Leif-Rydenfalk/halo/electronics/halo_replica/evidence/E07-CHECKS-THAT-CANNOT-FAIL.md

# E07 — the four ways a check passed today without being able to fail

*halo Replica lane, 2026-09-05. A running catalogue, because this lane produced four distinct
instances in one session and they do not look alike from the outside. Three were found by
lanes beneath me; one was mine, and I had already written the rule against it.*

Every entry is a real, dated defect in this project's own work, with the fix that caught it.

---

## 1 · A check that agrees with what it checks — the fitted-residual test

`bin/boardmetro circle` judged whether a feature was circular by the **residual of the fitted
inliers**. Its selftest fed it a **SQUARE**, which passed at **residual sd 1.15 px** under a
2.0 px threshold — because IRLS *chooses* the inliers that make the residual small.

**Fix:** judge shape on evidence the fit cannot manufacture. **Inlier fraction** separates
cleanly: square **0.055**, ring **1.000**.

**Also:** the first fix was itself wrong. It gated on angular uniformity and rejected the real
O'Flynn marker circle, which is *legitimately* clipped by the crop. **Angular completeness is
not circularity.** Selftest case 9 is now a clipped circle that must still be accepted.

## 2 · A negative control that cannot lose — L1's rim-pad permutation controls

Two in one hour, both in `m_rim_*`:
- The control permuted the **smoothed** signal, giving a jagged control where the real signal
  is smooth. The peak-finder invented ~22 peaks from it and **nothing could ever have beaten
  it.** Fix: permute raw, then smooth identically.
- The control permuted angular **columns**. For a "reaches the edge" criterion every permuted
  column is a full-height stripe, so **the control manufactured the property under test** and
  returned 46.8 against a real 26. Fix: roll each radius row independently — same pixels, same
  per-row runs, only the radial alignment destroyed.

The verdict did not change. **The reasoning behind it was worthless.** A right answer reached
through a control that cannot fail is not a measurement.

## 3 · Methods that cannot disagree — my own, E04, and I had written the rule against it

I concluded from "four independent methods" that the board was ~25 mm and not 26. Every method
applied a **scalar px/mm to an anisotropic projection**, so none could disagree about the thing
I used their agreement to establish. L5's 24.997 mm matched L1's *vertical* extent to **0.02 %**
and sat 5.08 % off horizontal. One systematic reproduced four times. **Retracted in E05.**

I had written the rule after the coil retraction four hours earlier, applied it in E04 **in
writing**, and still got it wrong: I checked whether the scale *sources* were independent and
never asked whether the *projection assumption* was shared.

## 4 · A positive control that is too easy — L1's synthetic rim, and the subtlest of the four

The blob detector **failed** its positive control outright: six synthetic pads at photo 6's
exact scale, **one found**. That withdrew M03's counts. But the replacement's positive control
was still not representative — **the synthetic was 19× cleaner than the photograph**
(differential robust sd 1.8 luma against 34.6 and 37.3). A pad at the synthetic's full 111-luma
contrast sits at **3.2 σ** in photo 6, under a 4 σ gate, and *no larger than the 4.0 σ the real
rim already throws from nothing.*

**Fix:** a noise-matched case where the same detector finds **zero** of six pads that are
certainly there.

**Why this one is the subtlest, in L1's words: passing feels like evidence.** A negative control
that cannot lose leaves you uneasy. A positive control that sails through leaves you confident.

**It also upgraded the verdict**: from *"we could not see them"* to *"at this signal-to-noise
they could not have been seen"* — which CLOSES the rim question instead of leaving it hanging.

---

## 5 · The near-miss family: a bad input dressed as a better one

Not a check, but it would have defeated all of the above. Re-rendering the FCC exhibit at
600 dpi would have resampled a 27 px rim band to 110 px, producing **more** candidates with
**higher** confidence from **no new evidence** — and nothing in that output would have looked
wrong. Caught by measuring the prior first (`E06`): no competitor FCC exhibit embeds above
2048 × 1536, ours is already 2134 × 1600. L1 then closed it independently by power-spectrum
rolloff — the board region's real detail **dies below half Nyquist**, so destroying everything
above half Nyquist costs nothing.

## 6 · And the inverse: a tool that refused when it had actually measured

L1's resolution probe demanded `as_held > /2 > /4` and, when /2 came out *equal*, reported
"cannot separate the controls". **Wrong.** If real detail already dies below half Nyquist then
destroying everything above it MUST cost nothing — **/2 failing to separate IS the answer.** A
monotonic-ordering assumption had been smuggled into the verdict logic rather than the physics.

**This is rarer and harder to notice than the reverse, because the output is the safe-looking
one and nobody audits a refusal.**

---

## The rule, in its current form

Started as: *when you claim two measurements corroborate, name what each would have had to
SEE to disagree; if you cannot name it, they are one measurement.*

Sharpened after E04: *check independence against the assumption every method has in common,
not only against the inputs they do not share — a shared assumption is harder to see than a
shared input because nobody writes it down.*

**L1's form is better and is the one this lane now uses:** *check the assumption the method
shares with **its own control**, not only the inputs they do not share.* It covers the
method-and-control case, which is the one that actually bit both of us today.

## 7 · A check whose failure mode returns the BEST possible score — noise is broadband

The worst of the set, and the one nearest to being published as a headline.

L1's resolution probe, pointed at a box on `oflynn-backside-fullres` that sat mostly **off the
board**, returned **0.992 of Nyquist** — "SHARP, essentially to the file's own limit". It was
drafted as the good news. On-board regions of the *same file* measure **0.195–0.258**.

**Sensor and JPEG noise reaches Nyquist by definition and resolves nothing.** So a resolution
probe aimed at empty background does not merely fail — **it returns the best possible score.**
This is worse than a check that cannot fail: it is a check whose failure mode is
*indistinguishable from the ideal result*. The only thing separating them was the region's
luma sd — **36** for the background box against **64–66** on board.

**Fix:** every row now names its region and carries that region's luma sd. What caught it was
drawing the sample box back onto the photograph and **looking** — the same move that caught the
half-max contact-shadow artifact, whose faked ellipse pointed a *different* direction in each
photograph, which no real board shape can do.

## 8 · A correct measurement with a wrong verdict printed over it

Distinct from all of the above: the number was right and the sentence above it was not. Two
instances in one tool:

- `k_first`, "the first ladder step that costs detail", is ≥2 even for a perfectly sharp
  image — so the tool printed **"ALREADY SOFT / UPSAMPLED" over a 0.992 measurement.**
- The verdict demanded `as_held > /2 > /4` and, when /2 came out *equal*, reported "cannot
  separate the controls" — when **/2 failing to separate WAS the answer.** A monotonic-ordering
  assumption had been smuggled into the verdict logic rather than the physics.

**L1's line, kept verbatim: nobody audits a refusal, and nobody audits a confident label
either.**

---

## The resolution table, because it is the fact these lessons produced

Genuine pixels across the board — rolloff × board span — not pixels per file:

| source | side shown | board span | rolloff | genuine px | genuine px/mm |
|---|---|---|---|---|---|
| `oflynn-frontside-fullres` (right) | BACK | 1924 px | 0.570 | 1097 | ~42 |
| `oflynn-frontside-fullres` (upper-left) | BACK | 1924 px | 0.445 | 856 | ~33 |
| `oflynn-backside-fullres` (left annulus) | **FRONT** | 2672 px | 0.258 | 689 | ~27 |
| `oflynn-backside-fullres` (top-right) | **FRONT** | 2672 px | 0.195 | 521 | ~20 |
| `oflynn-frontside-26mm-cropped` (M01 datum) | BACK | 787 px | 0.398 | 313 | ~12 |
| FCC photo 6, board | FRONT | 412 px | 0.289 | 119 | ~4.6 |
| FCC photo 6, **steel rule** (within-image control) | — | — | **0.383** | — | — |

**Three consequences, and the third is the one people will get wrong:**

1. **More pixels is not more information.** The 2916 × 3412 file is *softer per pixel* than the
   2347 × 2344 one and only wins because the board fills more of the frame.
2. **The steel rule is sharper than the board in the same frame** (0.383 vs 0.289). That single
   within-image number explains why the px/mm datum is solid and the rim count never was.
3. **"Prefer the sharper image" does not apply to component work, because there is no choice.**
   The components are on the FRONT, and the FRONT is imaged only by the *softer* source. The
   sharper photograph shows the side with the battery contacts and the coil — **the better
   picture is of the emptier face.** Component metrology is stuck at 20–27 genuine px/mm.
   At that scale an 0402 is 20–27 px long and workable; an **0201 is 12–16 px long and 6–8 px
   wide, and a 6-pixel width cannot support package-size discrimination.** The AirTag uses
   0201s. That boundary belongs in the BOM as a number, not discovered per line.

## 9 · A control that can NEVER PASS — the same defect wearing the opposite sign

L1's centre-hole negative control required **zero detected objects inside the hole**. But the
hole is **bright background seen through the board**, so an unbounded intensity detector must
always return exactly one object there. It reported **1 at every threshold**. The requirement
was not a test of anything.

**Fix:** a **physical** upper size bound — 60 mm², against a largest real part (the UWB can) of
~35 mm². **Not** by lowering the requirement.

A control that can never pass is as useless as one that can never fail, and it is more likely
to survive review because it looks strict.

## 10 · A validation blind to the very quantity it appears to certify — and the cleanest demo of all

`c_register.validate` reported a worst held-out fold of **0.1029 mm**, which reads like a
statement of accuracy. Its scale basis was `photo6_bottom = 15.8875 px/mm` — the bottom rule's
value **at the rule, near the frame edge**. M02 measures **15.6850 px/mm at the board**, by two
routes agreeing to 0.23 %. **The basis was 1.29 % high**, and every millimetre downstream moved
with it (transferred source scale 107.686 → **106.313 px/mm**).

**The held-out error cannot see this, and L1 demonstrated it rather than arguing it.** Re-running
`validate` with the corrected scale gives **0.1029 mm in both runs, identical to four decimals** —
because validate converts the fitted *and* the held-out landmarks with the same px/mm, so a wrong
scale divides both sides equally and cancels exactly.

**0.1029 mm is a statement about REGISTRATION CONSISTENCY and carries no information about SCALE
ACCURACY.** A 1.29 % scale error and a 0.1029 mm held-out error coexist happily, and the second
never warns you about the first.

This is family 3 (methods that cannot disagree) in its purest form: **two runs differing in
exactly one number, and the check does not move.** It is the strongest single demonstration this
project has produced that a passing validation is not automatically evidence about the thing you
hoped it was evidence about.

**Fixed by extension, not forking:** `--target-px-per-mm` with a named `--target-px-per-mm-basis`,
and when the default is used the tool now *prints* that it is the rule's value and names the
board-located alternative. Default behaviour unchanged. That shape — make the assumption visible
rather than silently changing it — is the one to copy.

---

## Where this leaves the component work

**95 bright features located on the project FRONT; only 32 with a short side over 10 genuine
pixels.** Median detection area **0.178 mm²** — 0201 nominal (0.6 × 0.3 mm) **to 1 %**. So most
are **located but not sized**, exactly as the 0402/0201 boundary in §8 predicted. Every row
prints its short side in genuine pixels so the distinction cannot be lost downstream.

**The known hole, with names in it:** the detector finds *metal* — pads, terminations, cans,
solder — and is **blind to dark IC bodies**. The nRF52832 is not among the 95. For a footprint
list that is arguably correct; for a placement list it is a gap, and it is the gap that matters
most for the deliverable, because the dark packages are what make the photograph read as an
AirTag at all.

## 11 · A number that measures the operator, not the board — "the answer is the box"

L1's third dark-package attempt stated a region of interest and ran Otsu inside it. **It returns
an answer, and the answer is the box.** Padding the ROI 0 / 20 / 40 / 60 px gave **3.35 / 3.98 /
4.09 / 4.50 mm for the same package** — a **34 % swing driven entirely by the choice of box**,
touching the ROI edge at every padding.

**This is M01's "394 px was the crop frame" in a new costume**, and it would have passed
unnoticed on a single run. The tell is the same one: a result that tracks a parameter of the
*search* rather than a property of the *subject*.

**The general test: sweep the arbitrary parameter and see whether the answer moves with it.**
L1 now does this everywhere — and it is what converted the UWB can from one number into an
honest split: short side **3.56–3.67 mm, stable at 2.9 %, MEASURED**; long side **15.6 %
ROI-dependent, CANNOT DETERMINE**, with 6.735 mm as a lower bound.

## 12 · An assertion in a deliberate break that could not fire

L1's merge-detection break asserted "the merged blob must be 3× bigger than the package". **It
cannot fire**: the search box caps the blob at the ROI's own area, so a fully merged blob and a
3×-too-big one are *the same number*. Caught only because it went red when the merge had
actually happened.

**Correct evidence of merging: the blob fills the WHOLE ROI — 100.0 % against the control's
82.9 %.** A deliberate break is itself a check, and it needs the same audit as the check it
tests.

---

## The cross-validation that came free, and is the strongest result in this lane

The nRF52832-CIAA positive control measured **3.218 × 2.940 mm** against a published
**2.956 × 3.226 mm** — long **−0.23 %**, short **−0.54 %**, aspect **+0.31 %**. The candidate is
selected as the **most rectangular** in the search box, *not* the closest to the published size,
because selecting on the answer would make the control agree with itself.

> **⚠ CORRECTED 2026-09-05 (BOM lane): the 0.23 % below rests on the SMALLEST of THREE
> segmentations of the same part in the same photograph.** M08's own whole-board run gives
> **108.2 px/mm by the same route — 1.8 % away, not 0.23 %**, and a third gives 110.1. The
> agreement is **real but materially weaker than this section reads**, and I amplified it twice —
> calling it "the strongest cross-validation in the lane" here and reporting it upward. The
> **verdict of 106.313 px/mm is unaffected**; only the strength of its corroboration was overstated.
> **A datasheet package cannot pin a scale better than ~2 %**, because the segmentation of the part
> is itself uncertain at that level. And the honest uncertainty is not the 0.41 % transfer spread —
> the transfer inherits FCC-6's unresolved **2.07 %** rule-to-rule disagreement, so **106.3 ± ~1 %**.

**And it validates the scale, which nobody designed it to do.** That size is reached with the
*registration-derived* 106.313 px/mm; making the nRF exactly its published size would need
106.06 px/mm — **0.23 % away**. **A steel rule in a different photograph carried through a
homography, and a package dimension from a datasheet, agree to 0.23 % with neither fitted to the
other.** Applying this lane's own rule: each could have disagreed, and the assumption they share
is only that the board is rigid.

Consequence: **L3's nRF-derived 110.3 px/mm is +3.9 % against two agreeing routes and must be
re-derived.** Its 0.4 % aspect agreement still stands — aspect is scale-free — so the
segmentation was sound and the *scale it inferred* was not.

And it resolves the UWB puzzle: L3's 20.8 mm² was **physically impossible**, not a meaningful
coincidence, since TechInsights' U1 *die* is 20.58 mm² and a SiP must exceed its die. L1's
rectangle (23.98–28.92 mm²) sits comfortably above it. **The near-equality was a box that
stopped short** — family 11 again.

## 13 · A similarity you manufactured by transcription — the colour-sampling trap

The board lane proposed sampling **median RGB from Apple's photograph inside each marker** and
painting our parts that colour, to fix "ours reads as a schematic". It asked, correctly, whether
that was a measurement or an invention.

**It is a measurement — and that is not the problem.** The problem is that it makes the
comparison **circular**. Paint our board with pixels taken from Apple's photograph, set the two
side by side, and they *must* agree on colour, because we copied it. Leif's test is whether ours
looks like theirs; **a similarity manufactured by transcription measures nothing.**

This would have been the most *visually persuasive* instance of the whole family, which is
exactly what makes it the most dangerous — every other entry here is caught by a number, this one
is caught only by asking where the agreement came from.

**Ruling:** the primary comparison stays **uncoloured** — that is the render Leif's test applies
to. A coloured version may exist as a **separate** file, labelled on its face that appearance was
sampled from Apple's photograph and that the panel cannot be used to judge colour fidelity, and
no similarity metric may touch it.

**The non-circular fix is to colour by part TYPE** — ENIG gold for a pad, silver for a can, olive
or white for an MLCC — from a palette derived from the material rather than from the target
image. That **can disagree** with the photograph, which is what makes it worth drawing.

**And the honest cause is not colour at all:** ours reads as a schematic mostly because we do not
*know what most of these parts are*. A palette cannot fix that, and must not be allowed to paper
over the identification gap.

---

## The state of the deliverable when this was written

`board/out/compare-front.png` — ours | Apple's | overlay at one shared 48 px/mm, **registration
by construction rather than by alignment**, so nothing was fitted to make the panels agree.

**The one number that matters:** median luma under our 97 markers **185.0**, against **60.0** at
4000 random annulus positions; **42.3 % of markers above the random 90th percentile against 10 %
by construction — 4.23× enrichment.** The random draw is the negative control and it is printed
on the picture. The positions are not decoration.

**What is still wrong, worst first, in the board lane's own assessment:** Apple's centre hole has
a step/notch at 3–5 o'clock that our fitted superellipse rounds straight over, so our line runs
through Apple's board material there — a real geometric miss. The dark regions are **empty**, and
knowingly so. Ours reads as a schematic. The grey rim material is absent (no geometry exists for
it — CANNOT DETERMINE). The outer outline overshoots at 2–4 o'clock, fit residual sd 0.277 mm
with 55.8 % of rays inside ±0.15 mm (a plain circle gives 0.563 mm / 43.6 %). And **X1 is firing
at 3.20 % and the montage exits FAIL** — diagnosed as the instrument, not the board: dark wooden
blocks in the photograph's background merge into the thresholded silhouette. **Not loosened. A
failing check that names its own cause is worth more than a passing one.**

## 14 · A break severed from its subject by a process boundary

Distinct from family 12 (an assertion inside a break that cannot fire). Here **the break was
real, the check was real, and the break never reached the check.**

- `X3` displaced the geometry, but **panel 1 is rendered by a subprocess that knows nothing
  about the break**, so `X4` sat unmoved at 0.413 mm under a 12° rotation. The break was a
  decoration on that number. Fixed; X4 now moves 0.413 → 0.470.
- `R5`'s `--break-drop` **truncated the input rows**, so the accounting balanced and the check
  had nothing to notice. Fixed to lose markers at draw time instead.

**A break that runs in one process and a check that runs in another are not connected by
intention.** Anywhere a deliberate break crosses a subprocess, a file write, or a regenerate
step, verify the number on the far side actually moves.

## 15 · A threshold that silently inverts when its reference goes negative

The "does this model earn its extra parameters" gate read **gain > 2 × floor**, where the floor
was the same improvement measured on a synthetic shape known to have no such feature.

When the floor came out **negative**, `2 × floor` is *more negative*, so **the test passed on any
positive gain whatsoever.** A ratio test against a signed reference inverts silently, and nothing
in its output says so.

**Fix:** demand an absolute margin as well — 5 % — not only a ratio.

**And getting to that floor took two rejected controls.** The first returned **−3836 %** and was
correctly binned as nonsense rather than reported. The rebuilt one returned **−221 %**, which
turned out to be **the detector, not the control**: a line fitted to a short noisy arc comes out
nearly tangential, `d/cos(θ−normal)` diverges at 90°, and such a "facet" throws its own radius to
infinity inside its own arc. Facets more than 60° from their own normal are now refused *with
that reason*. Final floor **−0.31 %** against a real gain of **40.53 %**.

---

## The corroboration that worked — control R7

Set against the recurring failures, one clean success, and it came from asking two methods with
**different blind spots** the same question.

Markers falling outside the drawn outline is a self-consistency check that can fail. The board
lane found **16 of 100 rows** beyond 0.95 of the *fitted outline radius*. L1 had independently
flagged **14** as `on_rim_material_suspect`, by a *radial* criterion against the local edge
radius. **Intersection 14. L1-only 0.** L1's set is strictly contained in the geometric one, and
neither model was fitted to the other.

The two extras are the interesting part. B011 at 0.9648 is marginal. **D004 at 1.0413 is a
BLUE-body row outside the fitted outline — and L1's radial test ran on the 95 *bright* rows only,
so it could never have flagged it.** A genuine 15th candidate, visible only because the two
methods fail in different places. Reported, not chased, and not drawn as a confirmed part.

## The finding that may reopen a closed verdict

**Apple's centre hole is a routed pocket — arcs and straight walls — not a smooth curve.** Seven
facets admitted; line inlier fraction **0.86–1.00** against the superellipse's **0.00 on the same
arcs**; residual **0.3342 → 0.1987 mm**.

**CORRECTED 2026-09-05: there are TWO estimates, not three — see below. The argument stands but is weaker than I first wrote it.** L1 closed
the hole as PARTIALLY DETERMINED because two photographs gave n=2.70 and n pinned at 2.00, and a
refit gave 2.449 (**but the latter two share a photograph — see the correction below**) — reasoning that assumes the shape *is* a superellipse and the spread is
measurement error. Under a pocket, **n is not a property of the hole at all**: it is whatever
exponent best splits the difference across whichever facets each photograph sampled well, so two
photographs would disagree **by construction**.

**The test, and it can fail:** fit the pocket model to FCC photo 6's hole boundary — different
photograph, different scale, different segmentation — and compare **facet angles, not n, and not
residuals**. Agreement moves the hole from PARTIALLY DETERMINED to MEASURED. Disagreement leaves
L1's verdict standing for a better reason than it currently has.

## 16 · A statistic that saturates — a test with no power, and the design error was mine

I directed the board lane to test the pocket hypothesis by fitting the pocket model to a second
photograph and comparing **facet angles, not n and not residuals**. Good instinct, bad statistic,
**and I specified it.**

The lane measured what chance scores on my statistic: with 7 facets at a 12° tolerance, **36 % of
the circle counts as a match**, and granting a free rotation on top means **chance already scores
2.61 of a possible 3**. The pre-registered run returned **3 of 3 at p = 0.61** — a perfect-looking
agreement that is indistinguishable from noise.

**A test that cannot distinguish agreement from coincidence is not a test.** I never asked what
the null distribution looked like before naming the statistic. The lane's negative control is the
only reason "3 of 3 agreement" is not in the file as a result — and I would have accepted it,
because I asked for facet agreement and would have been handed facet agreement.

**The fix is a shape worth keeping:** a **count** saturates; an **error** does not. Derive the
tolerance per facet from `atan(1 genuine px / that facet's span)` rather than one number for all,
restrict the comparison to facets the second photograph can actually resolve, and use the angular
error as the statistic.

## 17 · A verdict chosen after seeing which analysis wins

The lane wrote a facet-stability filter **after** the first null, and it moved p from **8.64 % to
2.81 %**. The filter was defensible on its own terms — excluding operator-dependent features is
this project's standing rule, and only 3 of 7 facet normals survive half the threshold sweep.

**Being defensible was not enough, because the choice was made downstream of the answer.** The
tool now always runs **both** sets, reports both, and **takes the verdict on the weaker one**.

In the lane's words: *a verdict chosen after seeing which analysis wins is not a verdict.* The
temptation was real — 2.81 % is publishable-looking and 8.64 % is not.

---

## CORRECTION TO THIS DOCUMENT — the exponents were never three

**My own miscount, repeated and built upon.** `n = 2.00` (pinned) and `n = 2.449` come from the
**same photograph and the same boundary points**, differing only by optimiser and bounds. There
are **TWO** estimates — photo 6's 2.70 and O'Flynn's ~2.0–2.45 — not three.

**This partly undercuts the pocket argument I made above.** I said three disagreeing exponents
were probably explained by fitting the wrong primitive. **Two estimates from two photographs
disagreeing is far less remarkable and needs much less explaining** — an ordinary measurement
spread covers it. The pocket may still be the right model on its own evidence (line inlier
0.86–1.00 against the superellipse's 0.00 on the same arcs), but **the exponent spread is now weak
support for it, not strong.**

**ROUTED, not edited:** `metrology/M02 §4` should restate PARTIALLY DETERMINED on **two**
estimates rather than three. The **verdict is unaffected** — only the basis it cites is
overcounted. That is L1's file; L1 is idle and this is a documentation refinement, not a
propagating error.

## Instrument facts that outlive the test

- **Photo 6's hole diameter moves 6.60 % across thresholds 150–210**; photo 7's moves 2.97 %.
  Anyone quoting a hole size off an FCC photograph should see 6.60 % first — **this supports
  PARTIALLY DETERMINED on its own, with no facet analysis at all.**
- **Only 3 of 7 facet normals recur across more than half the threshold sweep.** Most of that
  geometry is the operator's threshold choice, not the board. (Family 11 again.)
- The same extractor **centred on solid board finds 0 px of hole on both photographs** — the
  positive-control-in-reverse that says the extractor finds a real thing when it finds one.
- The faster cross-correlation statistic is applied **identically to the real set and to every
  random set**. A strict statistic for the real data and a loose one for the null is the rigged
  comparison caught three times elsewhere in this project.

## 18 · A fix applied in one place and not the other — the latent defect

The near-tangential guard (a straight edge cannot be the boundary more than 60° from its own
normal, because `d/cos` diverges at 90°) was added to the **hole facets** and **never propagated
to the outer chords**. It surfaced only when a *second* profile was fitted: chords at 4.02 and
5.55 mm offset, **73° and 63° from their own arcs**, residual 3.21 mm.

**It changed nothing on the published profile.** That is the point — it was a **latent** defect,
not an active one, and latent defects are the ones that survive, because nothing goes red. The
board lane found two of its own in one session.

**When a guard is added, grep for every other place the same operator is applied.**

## 19 · A control that cannot be placed cleanly on the geometry — reported, not tuned

`E1` (find nothing where there is nothing) first ran over 0.40–0.80 R, which **straddles the
centre hole**. It fired 72 of 72 — and it was **right to**, because it was being shown genuine
background and asked to find nothing. **The control was wrong, not the finder.**

Moved fully into the annulus it *still* fires (50/35/26 of 72 at persistence 1.5/2.5/3.5 mm), with
found radii clustered at 0.68/0.64/0.62 R — **against the hole's bright shelf, not scattered**.
The annulus is 5.79 mm wide and the persistence window needs 1.5–3.5 mm of it, so **the control
cannot be placed clear of both the shelf and the rim.**

**Reported as un-runnable on this geometry rather than tuned until it passed.** `E4` — real
annulus texture with a known step appended — carries the verdict instead: 0 missed of 24, median
error 0.0015 mm, **but p90 0.19 mm and max 3.76 mm, so roughly one ray in ten prefers an annulus
feature to the true edge.** That rate is published, and it is what makes the whole-circle refusal
below legible rather than a matter of taste.

---

## The refusal that matters most: more data, declined

A whole-circle re-extraction produced **1428 rays with an edge against L1's 1194**, including
**246 rays L1 had no value for**. It was **not adopted.**

- **N4 fired: displacing the fitted chords by 0.30 mm made the fit BETTER**, and `p_fit`
  **refused to write the file.** A fit that improves when you deliberately corrupt it is not
  tracking the geometry, and a tool that notices this about its own output and declines to
  publish is doing something almost nothing does.
- The gaps are gaps **precisely where the edge is genuinely ambiguous**, and E4 puts the
  gross-failure rate there near **one ray in ten**. Filling a gap with a value that is wrong one
  time in ten is worse than leaving it empty.

**More data was available and was declined, with the number that justified declining it
published.** Almost everyone takes the extra rays.

And the corroboration that came free: on the **1182 shared rays the two extractors agree to a
median 0.0158 mm** — sixteen microns, from two finders never tuned to each other.

## The two worst arcs answered differently, which is why re-measuring was worth it

- **82.75–101.0°** — the 0.901 mm excursion. Mine +0.556 mm from the fit, L1 +0.674 mm, and a
  second independent extractor moves it only 0.119 mm. **The bulge is REAL** — unmodelled
  geometry, not a detector artefact. Whether it is substrate or the grey rim material lapping
  over it **cannot be separated with the sources this lane has**. The model has no feature there
  and none was invented.
- **101.0–123.0°** — the 0.979 mm excursion, containing a 13.75° data gap. Mine −0.127 mm, L1
  −0.691 mm, and 74 rays L1 had no value for sit **near the fit**. **The dent is largely a
  detector artefact** — so refusing to model a flat across that gap was right, and is now
  measured rather than argued.

**One worst arc was a real feature the model lacks; the other was the instrument. Only measuring
told us which.**

## And a measurement bias larger than the thing being measured

`E2` caught the gradient-peak edge estimator at **4.21 px of bias on a synthetic step — 40 µm,
larger than the feature being measured.** A boxcar smoother turns a step into a ramp whose
gradient is a *plateau*, and the peak lands anywhere in it. Position is the **50 % crossing**
now: **0.05 px**.

## 20 · A threshold is not a property of a material — it is a property of a material AND A FIELD OF VIEW

The sharpest portability lesson this project has produced.

L1's copper criterion (chroma ratio 0.25) measured the NFC winding at **0.727 mm** in the tight
26 mm crop, at ~12 genuine px/mm, in a frame that held little but the coil. The **same criterion**
applied to the full frame returns **2.732 mm — 3.8× too wide** — because it now sees *every gold
feature on the board*.

**Nothing in its output would have looked wrong.** The threshold did not travel, and a threshold
carries no record of the frame it was tuned in.

**Consequence, stated so it cannot be misused:** the resulting 18.6 % / 20.9 % difference against
M01 is **NOT** a scale comparison and must not be quoted as one. The verb was measuring a different
object. The scale comparison that *is* worth doing — O'Flynn's tilde against the FCC rulers, on
**one object, in a photograph both share** — is still untested, and is valuable precisely because
those two measurements share every pixel and **can therefore only disagree about scale**.

## 21 · A control that merely sits under the threshold has separated nothing

The no-coil control annulus scored **0.230** against a **0.25** admission threshold and **PASSED**.

It should not have. **A control passes by being far from the signal, not by squeaking under a
bar.** Real separation was **1.37×** against a **2.00×** floor — a fail. That near-miss *was* the
entire signal, and the first version of the check threw it away by asking the wrong question
("is the control under the threshold?" rather than "how far apart are they?").

**Demand a separation ratio, never a pass.**

## 22 · The null and the statistic must be designed against each other

A row-roll null **cannot fire** against a statistic built on **row means** — rolling a row
horizontally leaves its mean exactly unchanged. And a **peak-height** statistic survives row
*permutation* untouched, so the statistic itself had to be rebuilt on **band contiguity** before
any null could bite.

**Inheriting a good null from a neighbouring tool is not enough.** A null is only a null with
respect to a particular statistic; the pair has to be designed together, and porting one without
the other produces a control that runs, reports, and cannot fail.

## 23 · A number that snaps to a known standard is the strongest invitation to stop checking

The back-face lane measured a bulk capacitor at **3.192 × 1.581 mm** — **EIA 3216 / Case A to
0.25 % and 1.2 %**. It is very likely correct.

**It was refused**, because the same seed returns **4.699 × 4.414 mm** two window sizes later
(family 11 — the answer is a function of the window). Held in `candidates_not_published` with the
reason attached, and with the note that the three clustered candidates **share a method, a scale
and a seed, so they could not have disagreed** about any of those.

**In the lane's own words: landing on a plausible standard case code makes the temptation worse,
not better.** A value that matches a published standard *feels* like independent confirmation. It
is not — the standard was never consulted by the measurement, so the match is a coincidence until
the measurement is shown to be window-invariant.

---

## And the systematic that had gone unstated all day

**The FCC photographs and O'Flynn's are of TWO DIFFERENT BOARDS** — `920-08283-01` data code 3119
(2019 engineering build) versus `820-01736-A` data code 2920 17 (2020 production). Every scale in
this lane is transferred from one to the other.

**A uniform dimensional difference between them is absorbed into the fitted scale and leaves the
held-out residual completely unchanged**, because the check divides both sides by the same number —
family 10 exactly, arriving from a direction nobody was watching. It applies to the Replica's
106.313 px/mm and therefore to **every absolute millimetre this lane has published.**

`REFERENCE-TEARDOWN.md` §7 already listed "whether the FCC-sample board differs electrically from
production" as open. **Nobody had noticed it was also a DIMENSIONAL assumption.** CANNOT DETERMINE
here; a caliper on one board of each part number settles it.

## 24 · A STABLE WRONG ANSWER — and why parameter-invariance is not sufficient

**This refines a test several lanes here have leaned on as though it settled things.**

Family 11 ("the answer is the box") produced a 34 % swing on ROI padding alone, and the fix
adopted across this lane was: **sweep every arbitrary parameter and show the answer does not move
with it.** That is a good test and it is *not* a sufficient one.

The dark-package lane found a rectangle scoring 18.8 at 2.45 × 2.18 mm — an **inner** feature of
the nRF package, not its outline — **stable to −26 % across downsample 2/3/4, band 1/2/3 and
npeak 30/40/60. Every parameter swept, and the answer did not move.** It is also wrong.

**A wrong answer that corresponds to a real feature of the image is stable precisely because it is
genuinely there.** Invariance rules out one failure mode — the operator's arbitrary choice driving
the result — and establishes nothing else. It does not tell you that the feature you locked onto is
the feature you were looking for.

**So sweep-stability is necessary, not sufficient.** It must be paired with something that ties the
answer to the *intended subject*: a published dimension, an independent modality, or a positive
control whose truth came from outside the measurement.

## 25 · A check that SATURATES rather than fails — the zero-variance null

The rectangle engine's null standard deviation was sampled over spans that lay **off the board**,
where the directional derivative is **identically zero**. Past 50 % zeros the **MAD is zero**, so
`z` goes to infinity and **every rectangle scores the same.**

It produced z-scores of **1e11**.

**This is not a check that fails — it is a check that saturates, and a saturated check reports
maximum confidence in everything.** It would have made every subsequent number meaningless while
looking overwhelmingly significant. Nothing downstream would have flagged it; a 1e11 z-score looks
like a triumph.

**Fix:** sample the null only where the mask is fully covered. **Found by pointing a diagnostic at
a known answer** — not by reading the code.

**Guard the denominator.** Any statistic normalised by a spread must refuse when that spread
collapses, and say so, rather than dividing by something near zero.

---

## And a premise of mine, refuted by measurement

I briefed the dark-package lane that the packages are "unmistakable to the eye **because of their
straight boundaries and right-angled corners**", and told it to detect exactly that.

**Measured, that is false on this board.** Perpendicular luma profiles across the nRF's outline,
61 samples averaged per side: **one strong step, two weak (−15 and −14 luma), and one side with no
step at all.** Interior luma runs **90 / 41 / 66 / 36** around the same package — a strong
illumination gradient across it — so a consistent-polarity closure test is refuted by the data. An
exhaustive search with peak-picking removed confirms **no rectangle at the published
3.226 × 2.956 mm has four supported sides.**

**What the eye is actually doing is completing a shape from partial evidence plus the laser
marking. I described the output of that process as if it were the input.**

The correct design follows from the measurement: fit each side **independently**, report **per-side
support**, and call a dimension MEASURED only when **both sides of that axis** are supported —
otherwise the row is position-only. That is the same located-not-sized distinction already carried
by 63 of the 100 rows in the front-face handoff.

## 26 · A parameter you did not know was a parameter — and "chosen by the code" is not a control

**The sharpest defect surfaced today, and it feels *more* objective than the thing it replaced.**

The dark-package lane's detection-limit run used **the single quietest on-board window**, selected
automatically. It landed on the **metal shield can** — smooth at 4.2 mm, so it wins a
gradient-energy contest while being **nothing like the soldermask a package actually sits on**.

**Nothing in the numbers said so. Only drawing the evidence onto the photograph and looking did.**

And it was load-bearing: sweeping the site moved the closing number from "~120" to **100–140 luma**.

**In the lane's words: an automatic choice is not the same as a controlled one.** "Chosen by the
code, not by me" removes the operator's hand and **leaves the criterion's own blind spot exactly
where it was** — while feeling more objective, which is what makes it dangerous. Sweep the site
selection like any other parameter.

## 27 · A regression test written against an easy case is not a regression test

Selftest case 7 exists to protect a bound against side-wander. **With that bound removed, it still
passed** — because on a clean four-edged synthetic the sides have no reason to wander in the first
place.

Rebuilt on a `onesided` synthetic reproducing the real situation (one strong boundary, three nearly
absent), removing the bound produced **3.423 × 0.000 mm**. Only then was it a test.

**Family 4 arriving inside a selftest rather than inside a measurement.** A regression case must
reproduce the conditions the bound exists for, not merely exercise the code path.

---

## The refusal, repeated independently by two lanes on the same day

The per-side fit of the nRF gives **3.076 × 2.878 mm** against a published **3.226 × 2.956** —
−4.6 % and −2.6 %, with the centre wandering only 0.242 mm. **It was not admitted**, because only
**one of four boundaries** clears the measured bar.

**In the lane's words: its agreement with the datasheet is not a reason to believe it, and
admitting it for that reason is a control agreeing with itself.**

That is the same trap as the capacitor snapping to **EIA 3216 Case A to 0.25 %** that the back-face
lane refused (§23) — and **the two lanes refused it independently, hours apart, without
coordination.**

## The dark packages are closed with a NUMBER, not an absence

**What the photograph needs:** a boundary step of **100–140 luma** for 3 of 4 sides to be
exceptional among the board's own straight structures; **120–160** for all four. Measured at five
automatically-chosen sites, all five reaching it.

**What the packages present:** **1–26 luma** on most sides; the nRF reaches **75** on its single
best one. Per-side |z| 37.2 / 15.4 / 9.2 / 13.5 against a bar of 33.4. **One supported boundary in
twenty examined**, across five bodies.

**And the method is not at fault:** the positive control is made *of* the photograph — a
3.226 × 2.956 mm rectangle of known boundary step pasted into the quietest on-board windows — and
at 120 luma it is recovered as **3.217 × 2.935 mm (0.3 % / 0.7 %)**.

So the verdict moves from *"we could not see them"* to **"at the boundary contrast they actually
present, they could not have been seen by any boundary method on this source."**

## The reframe that changes what would close it

**Every method this project has tried — intensity, texture, colour, boundary — reads a FLAT-LIT
photograph.** Flat lighting destroys precisely the property that makes a package trivially
separable: **its height.**

**A 0.5 mm tall body under oblique or raking illumination throws a shadow edge that no method has
to infer.** The gap is therefore not resolution (M10: 1.9× more genuine resolution does not do it)
and not contrast in the flat-lit sense — **it is that every source we hold was lit in the one way
that hides the discriminating feature.**

It needs no new teardown, only a differently-lit one. **This belongs at the top of every
what-would-close-it list in this lane.**

## 28 · A quantity measured a second way is not automatically the better one

**The nastiest entry here, because every instinct this project has built says "measure it another
way" is the safe move. It usually is. It was not here.**

The rim lane measured a boundary step at a rough seed and got **64–99 luma**, and could see the
figure was diluted by its own imperfect outline. So it measured the same thing a way that does not
depend on the outline at all — **brightest core against the board ring beyond** — and got
**174–191**, above the 140–170 limit. It read that as *bar cleared, count on*, and said so out loud.

**Wrong.** Core-minus-ring is a **peak-to-median** statistic and a **loose upper bound** on a
boundary **step** — and the step is what the detector integrates. The direct per-side measurement
settled it at **|z| 8–27** against a 23.7 bar.

**The outline-independent estimate was more robust AND further from what the method actually
consumes.** The tell was that the second measurement was of a **different quantity**, not a second
look at the same one.

**The number that decides a verdict has to be the number the method uses, not a proxy that
correlates with it.**

*(And the lane's own pre-registered P4 predicted its bias would be pessimism. It was pessimism,
then optimism, and only the direct measurement was neither — which is the kind of scoring that only
a committed prediction makes possible.)*

## 29 · A mask that manufactures an absence out of a coverage failure

The rim probe returned **|z| = 0.0 on eleven of twenty sides**, one step from being reported as *no
boundary*. It was not. **A rim feature straddles the board edge**, and fitting against the *eroded*
board mask cut its outer boundary, so the scan returned nothing — **and printed a zero**.

**A number that looks like strong evidence of absence, and is the absence of a measurement.**

Fixed by dilating the mask 1.5 mm outward into the gasket where a rim pad's outer boundary
legitimately sits; 0 of 20 unmeasured now. **And the structural fix: `probe` NAMES unmeasured sides
instead of scoring them.**

**An unmeasured thing must never be representable in the same field as a measured zero.**

## 30 · A control that catches the wrong failure — the limits of the disjoint-arc tell

L1's disjoint-arc control exists to catch a detector following per-photograph illumination: front
candidates clustering at 147–199° while back candidates cluster at 210–308° is a tell, because two
views of one board cannot legitimately put their features in non-overlapping arcs.

A later run's five detections spanned **45–322° across five of eight octants** and **passed that
control comfortably** — while being **SMD capacitor pads and entirely the wrong objects**.

**The control catches a detector following illumination. It does not catch a detector looking at the
wrong things.** Passing it is necessary and nowhere near sufficient — and anyone inheriting a control
should be told what it does *not* cover, not only what it does.

---

## The rim joints: closed a second time, and for a DIFFERENT reason

M05 closed the rim count on **signal-to-noise**. That closure no longer holds, and the new one is
about the instrument:

- On this source the joints are **unmistakable** — core luma **222–242** against a surrounding board
  ring of **34–56**, at roughly **5× the genuine resolution** M05 closed on. **They are not lost in
  noise.**
- They fail the boundary detector because **a straight-sided rectangle is the wrong model for a round
  solder blob** — a straight-line integral matches only a short tangent arc of a circle. **2 of 20
  boundaries clear.**

**That is a statement about the instrument, not the source, which means the question is genuinely
live again rather than closed twice.** The matched instrument is a **round**-feature detector, and
`bin/boardmetro circle` already has one with an inlier-fraction shape test.

## The refusal that produced a blind test

The lane that reached this point **could see the answer at native resolution** — and noticed its own
tally matched the dossier's stated figure. **It refused to run the circle detector**, on the grounds
that running a counter straight after seeing an expected number is how a count gets fitted to an
expectation. *"The number I expected is the number I saw."*

**Declining to run an available tool because the TIMING would contaminate it** is a form of control
this catalogue had no entry for. The observation is preserved, marked never-to-be-drawn, **as the
thing a later blind measurement gets compared against** — and a separate lane now runs the count
without being told the number, because **there is only one first look.**

## 31 · An allow-list controls WHICH FILES are read, not WHAT IS INSIDE THEM

**Found by verifying a containment rather than by reasoning about it — and the leak was in this
very document, in the one file the protocol marks *required*.**

To count the rim joints without knowing the expected answer, the lane that had already seen it
wrote a protocol naming ten permitted files, on an argument worth keeping: **a deny-list has to be
complete to work; an allow-list does not.** It grepped the repo first and found the withheld figure
in **more than twenty files**, including a selftest that builds a synthetic rim carrying a specific
number of pads, and log files quoting a document title.

It then flagged the honest residual risk: **blindness enforced by a lane's compliance is
undetectable if broken, because a contaminated count and a clean one look identical.** So the
allow-list was applied to the **filesystem** instead — a git worktree with every other file deleted,
leaving eleven files and the images.

**Then the result was grepped, and §4 of this document twice stated a count of synthetic pads used
in a rim-detection positive control.** Those numbers described a *synthetic* rim and had nothing to
do with the withheld figure — **but a number of pads, in a rim-detection context, read by a lane
counting rim features, is a leak regardless of what it refers to.**

**The allow-list protects against files you did not think of. It does nothing about a leak inside a
file you deliberately included** — and the required file is exactly the one nobody re-reads for
contamination, because its inclusion was the deliberate part.

Redacted to `N` in the blind working tree only; the copy on `main` is untouched and correct.

**The transferable rule: after applying a containment, GREP THE RESULT. Verifying the artefact is
not the same as reasoning about the rule that produced it** — which is the same distinction this
whole catalogue keeps arriving at from different directions.

---

## And the escalation that produced it: compliance → structure

| level | what enforces the blindness | detectable if broken? |
|---|---|---|
| instruction | the lane not reading forbidden files | **no** |
| tool refusal | `d_rim step`/`probe` exit 2 without an explicit flag, seeds quarantined out of the docstring | partly |
| **filesystem** | the files are **absent** from the working copy | **structurally** |

The first level is where this started. **The lane that wrote the protocol argued its own protocol
down** — naming the gap rather than defending the work — and proposed the third level itself.
Taking that suggestion cost one worktree and caught a real leak within minutes.

## 32 · The containment ladder has a ceiling — redaction inside a permitted file is a deny-list again

**My own containment, refined by the lane it was protecting.**

I redacted a synthetic-pad count out of the required file (§31) and believed the blind tree clean.
The executing lane then reported, unprompted, that the same document still carried **"invented ~22
peaks"** and **"returned 46.8 against a real 26"** — control figures from a withdrawn rim-pad
analysis. Numbers, in a rim-counting context, reaching a lane counting rim features.

I had grepped for the figure and for count-like patterns. **I had not grepped for bare numbers in a
rim-counting context, because that set is not enumerable.**

**The structure of the failure:**

| layer | mechanism | can it be circumvented by an oversight? |
|---|---|---|
| files removed from the working tree | **absence** | **no — structural** |
| redaction *within* a permitted file | **a deny-list over content** | **yes, and it must be complete to work** |

**So the ladder tops out.** L7 chose an allow-list because a deny-list has to be complete; applying
that allow-list to the filesystem made the file layer structural — and then the *content* layer fell
straight back to a deny-list, one level down, for exactly the reason the allow-list was chosen. The
only complete fix was to omit the document entirely, and it was marked *required* for good reason.

**The honest statement of what the blindness is worth: structural at the file level, best-effort
within the files supplied.** That is weaker than I claimed when I set it up, and saying so is the
point.

**What made it survivable was not the containment — it was the lane's disclosure.** It recorded the
numbers in its pre-registration §0 *before measuring*, and pre-committed to say so explicitly if its
count lands on either. **A contamination that is named and pre-committed is checkable; one that is
merely absent-in-principle is not.**

**And the correct answer to "is this the number?" from inside a blind test is silence** — a *denial*
eliminates candidates and is information just as surely as a confirmation. Refused deliberately, and
said to be deliberate, so it could not read as an oversight.

---

## The instrument that is blind by construction

Worth recording beside all the failures: the blind lane chose a **circular boundary integral** —
integrating the outward radial derivative around a ring — because **a straight edge gives
`D = |g|·cos(φ − φ_n)`, which integrates to ZERO around a full circle.**

**That is structural blindness to the exact failure that killed the rectangle attempt** (§30: a
straight-line integral matches only a short tangent arc of a circle), rather than a threshold tuned
to avoid it. **An instrument that cannot see the wrong class by construction is worth more than one
that is told not to.**

With it: three morphology classes never merged, and an **X class** — clears the locator, fails the
shape gate — **reported as a number rather than silently discarded**, because a detector that
quietly drops what it cannot classify reports a clean count and hides its own error rate. That is
exactly where the five SMD capacitor pads went wrong.

And a bias pre-registered **with its direction and mechanism**: optimism, biased to count too high,
because being told the joints are unmistakable and that the prior failure was instrumental primes a
lane to believe a matched instrument and admit bright non-joint metal. **That framing came from my
own brief — the bias was induced, and naming its source is part of controlling for it.**

---

# CLOSING SYNTHESIS — one sentence for all thirty-two

*Added after the catalogue was closed. This is **not** a thirty-third entry; it is a statement
about the other thirty-two, and it came from the comparison lane rather than from me.*

> **Each one was checking something ADJACENT to the property it was supposed to test.**

That is sharper than the formulation this document had been using — *check the assumption the
method shares with its own control* — because it **names what goes wrong** rather than what to do
about it, and it covers cases the earlier version does not.

Five instances from a single day, all found by a deliberate break and none by inspection:

| the check | what it actually tested | what it was supposed to test |
|---|---|---|
| a null permuting profile **increments** | that increments are large — which a two-peak profile guarantees | that the peaks are not chance |
| a contrast-to-noise estimator | the **signal**, since a 3.5 mm part fills two thirds of the window | the noise floor beside it |
| an area-symmetry gate | that two areas **agree** | that two features are **one symmetric pair** |
| a "GND is between the tabs in **x**" rule | position in **one coordinate** | being **with** the tabs |
| an anti-gaming guard | a path resolved against the **search root** | that rev_a's board had not been copied in |

**Three kinds of adjacent**, and the last is the one people least expect:
**adjacent STATISTIC** (increment permutation, off-peak noise, area alone) · **adjacent COORDINATE**
(between-in-x) · **adjacent PATH** (the guard resolving against the search root). The path case is
not a modelling error at all — it is **a plumbing error wearing a control's clothes**, which is why
no amount of thinking about the physics would have found it.

*(A sixth, from the same day and the same shape: reading `cmd | tail`'s exit status instead of the
command's. `${PIPESTATUS[0]}` gives the real one. **The exit code you read was adjacent to the exit
code you wanted** — and it cost two false readings before it was caught by re-running clean.)*

**Adjacency is what makes these survive review.** A check testing something *unrelated* is obvious.
A check testing something *next to* the target passes, correlates, and reads as evidence — and the
tighter the correlation, the longer it lives.

The practical form: **name the property, then ask what else would satisfy your check.** If anything
else would, the check is adjacent and not on target. Two lanes independently refused a number for
exactly this reason on the same day — a capacitor matching EIA 3216 to 0.25 %, and a package fit
agreeing with its datasheet to 4.6 % — because in both cases **the agreement was with something
adjacent to the measurement rather than produced by it.**

### Two amendments to the synthesis, both against rules I specified

**A counter must not be improvable by typing — AND IT MUST NOT BE SILENTLY ZEROABLE.** I asked for
the basis grade to be guarded against relabelling, and it was. Then a sheet edit ran one statement
too far and deleted the loop that hands every basis to the checker. **The count went to "0 of 52
MEASURED" and nothing went red**, because the feature is opt-in — so *a sheet that never declared*
and *a sheet that lost its declarations* are indistinguishable to the check. I specified the opt-in
and the promotion guard and did not think about deletion. Fixed by a grader that fails on exactly
that case, **moved into the default pass**: a grader that only runs under `--self-test` is a grader
that is not running.

**A break must find its target by the property it breaks, never by a hardcoded literal.** Two of
this session's five "break that did not reach its check" instances came from the same cause — a
break naming a string verbatim that something else was free to change. Shortening a component's
value turned a break into a no-op. **A literal in a break is a dependency the break does not
declare.**

### And the rule that no check can enforce

> *"I had not looked at my own drawing."*

Every number green, ERC passing, 6 of 6 checks passing — and the rendered sheet had 29 value fields
running to 92 characters over their neighbours, 16 paragraph notes drawn past the bottom edge over
each other, and a title truncated mid-sentence.

**And looking properly mattered twice, in opposite directions, in one image.** At page scale the
note block *looked* like it had overlapping lines — and the measurement said it fitted with 34 mm
to spare. At real zoom the notes were clean, but a rail label was printing on top of the first note
line, which page scale had hidden. **A render that is produced and glanced at is not a render that
was looked at.**

One design law fell out of the repair, and it is worth more than the repair: **two pieces of code
placing text into one band cannot be made not to collide by arithmetic in one of them.** Proved by
trying — the first fix cleared the notes and put them over the power-flag symbols. A second
collision in place of the first.

---

## 33 · A check whose SUBJECT is the artefact its INPUT was derived from

*L5b BOARD BUILD, 2026-09-05. Mine, it was this lane's headline number, and I quoted it to two
sessions and into the changelog before catching it.*

`p_compare.py`'s **X5 "component landing"** measured, for each of 97 drawn component markers, the
photograph's luma at that position, against the same statistic at 4000 random annulus positions.
It returned **4.23× enrichment**, and it moved correctly under every perturbation: it collapses to
1.44× when the geometry is rotated 12° on purpose. It has a real negative control, it has a real
break, and both work.

**And the marker positions were extracted from that same photograph.**
`metrology/components-front.json` `source: oflynn-backside-fullres.jpeg`; X5 samples
`oflynn-backside-fullres.jpeg`. The markers ARE the bright blobs of that image. Bright-metal
markers landing on bright pixels is **close to a tautology**.

**This is not entry 1's shape.** There the *estimator* agreed with what it checked — IRLS chooses
its own inliers. Here the estimator is fine, the null is fine, the break is fine: **the
circularity is in the DATA PROVENANCE**, one file upstream of anything the check can see. No
amount of inspecting the check reveals it. The question that does is *"where did the INPUT come
from, and is it the same artefact as the SUBJECT?"*

**What X5 does genuinely test**, and it is kept under a correct name — **registration round-trip**:
the k-scaling, the crop about the stated origin, the resample to the montage scale, the coordinate
mapping. That is worth having. It is not what it was called.

**The fix — X5B, and it can fail.** Push the same markers through `c_register`'s homography into
**FCC photo 6**, an image they were never extracted from, taken by different people with a
different camera:

| | |
|---|---|
| marker median luma | **106** |
| 4000 random annulus positions | **42** |
| null — 97-sized draws from the random pool reaching our median | **zero of 20000, p < 1/20000** |
| fraction above the random 90th percentile | 15.5 % vs 10 % by construction — 1.55×, **p = 0.051** |

The count statistic is only marginal and that is **reported, not dropped**: photo 6 gives a 2.8 px
sampling radius, so blur mixes a pad with its neighbourhood. The median statistic is the powerful
one and it is decisive.

**The rule.** A check inherits the provenance of its input. Before believing a check that compares
a derived quantity against a source, ask **which artefact the derived quantity came from** — and if
it is the same one, the check is measuring the pipeline, not the world. Say so in its name.

## 34 · A null that was mine, not the board's

*Same lane, same hour, and it is entry 33's inverse.*

X5B's first version returned a flat **0.00× enrichment, 10 of 97 markers even inside the frame** —
a clean, quotable negative that would have read as *"the markers are an artefact of one
photograph."*

It was wrong. `c_register`'s homography maps into the O'Flynn image **divided by its `pre_average`
of 6.58**, not into full resolution. Omitting that factor put every marker on the paper background,
where the luma is saturated and identical to the random control.

**Verified in one line:** `H(fcc6 board centre) × 6.58 = (1522.559, 1738.801)` — the stated frame
origin to three decimals. The measurement that settles a frame question is *round-tripping a point
you already know the answer for*, and it costs nothing.

**The rule.** `VERIFICATION-DEBT.md` records the mirror defect for **capabilities** — a thing
declared absent because the probe looked in the wrong place. This is the same shape for a
**measurement**: a null needs auditing for its own construction exactly as hard as a pass does, and
it will not get that audit from anyone who is pleased with it. A negative result flatters whoever
wanted the negative.
