Leif-Rydenfalk/halo/electronics/halo_replica/comparison/THREE-WAY.md

# Apple | halo_rev_a | halo_replica — every axis, and which is better on it

*L9 — THE COMPARISON, halo Replica, 2026-09-05. **Generated by `tools/k_threeway.py render` from `comparison/threeway.json`. Nothing on this page is hand-typed into it.***

**Anchor check at render time: 80 PASS · 0 FAIL · 0 CANNOT DETERMINE → PASS.** Every cell below names a file and a value in it; `k_threeway check` resolves all of them and goes red when the table and its sources disagree.

---

## What this is

Apple | halo_rev_a | halo_replica, one row per axis. Five lanes measured Apple's board and nobody had set our own two boards against each other. This file is that comparison, and it is the artifact DECISIONS.md D23 asked for: it converts twenty-two assertions into measured differences, or says CANNOT DETERMINE and names what would settle it.

## The asymmetry that governs every row

> THE THREE OBJECTS ARE NOT THE SAME KIND OF THING, and no row means anything until that is stated. Apple's AirTag is a shipped product. halo_rev_a is a routed, DRC-checked, priced KiCad design with 62 footprints, 49 vias and 255 track segments. halo_replica is a MEASURED DRAWING: one face, no copper, no nets, no netlist, no DRC, no price, and no possibility of any of those, because nothing in it was ever a schematic. A Replica row that wins on fidelity has not thereby won anything a person can build.

## The three axes a row can be judged on

- **F** — FIDELITY TO APPLE — does this object reproduce what Apple actually built. The Replica's stated purpose (Leif: 'a perfect copy of the internal airtag stuff').
- **B** — BUILDABILITY — can it be ordered, assembled and checked. Measured against published capability pages and against this repo's own DRC/DFM/cost outputs.
- **G** — FITNESS FOR GOAL.md — a cheap open Find My puck, an embeddable circuit block in any outline, and peer-to-peer ranging between Leif's own sensors.

**Better is not automatic.** D23, verbatim: 'some of Core's divergences will survive comparison — the deleted amplifier looks likely.' It did. So did four more. Every row names the axis it is judged on, and where the axes disagree the row says so instead of picking the flattering one. CLOSER TO APPLE IS NOT A SYNONYM FOR BETTER and is never used as one here.

---

## The scoreboard

| # | axis | rev_a vs Apple | replica vs Apple | judged on | better | in one line |
|--:|---|---|---|:-:|---|---|
| 1 | Board outer diameter | SAME | SAME | F | **CANNOT DETERMINE** | Apple's diameter is a bound 1.39 mm wide and BOTH our boards sit inside it — 26.0000 and 25.1593. |
| 2 | Board outline SHAPE (not size) | DIVERGED | SAME | F | **halo_replica** | The Replica's outline is FITTED TO APPLE'S OWN EDGE with a published residual and a published per-degree map of where it disagrees. |
| 3 | Board thickness | DIVERGED | SAME | F | **halo_replica** | 0.30 against 0.60 is a 2x miss for rev_a on the best figure anyone has for Apple. |
| 4 | Layer count | SAME | SAME | F | **TIE** | All three are 4 and all three are counted rather than assumed. |
| 5 | Centre hole / board shape | DIVERGED | SAME | F | **halo_replica** | Apple's board is annular and rev_a's is not. |
| 6 | BLE and UWB antenna implementation | DIVERGED | SAME | F | **halo_replica** | Apple has no antenna in board copper and neither does the Replica. |
| 7 | NFC coil | DIVERGED | SAME | F | **halo_replica** | Apple's central coil is wound wire and the Replica refuses to draw it as copper. |
| 8 | Component packages | EQUIVALENT | CANNOT DETERMINE | F | **CANNOT DETERMINE** | THE REPLICA CANNOT CLAIM PACKAGE FIDELITY WHILE THE LARGEST BODY ON THE BOARD IS ABSENT BY NAME. |
| 9 | The flash and its power rail | DIVERGED | CANNOT DETERMINE | G | **halo_rev_a** | THIS IS A DIVERGENCE THAT SURVIVES COMPARISON, and it is the same shape as the one D23 predicted. |
| 10 | The audio path | DIVERGED | CANNOT DETERMINE | G | **halo_rev_a** | THE ROW D23 NAMED IN ADVANCE, and it survives. |
| 11 | The speaker / sounder | DIVERGED | CANNOT DETERMINE | B | **halo_rev_a** | Apple's motor is not buyable at any price and a housed buzzer does not fit the height. |
| 12 | Battery and its contacts | SAME | UNSTARTED | F | **halo_rev_a** | rev_a reproduces Apple's scheme exactly — three contacts, two positive rails, one sensed rather than loaded — and the prior comparison grades it SAME on this row. |
| 13 | Connectors and off-board joints | SAME | CANNOT DETERMINE | F | **halo_rev_a** | Apple's principle is 'not a connector on the product' and rev_a matches it exactly and measurably. |
| 14 | UWB transceiver | MISSING | MISSING | F | **TIE AT ZERO** | Neither board has an ultra-wideband radio and no amount of replication will produce one. |
| 15 | The SoC | DIVERGED | CANNOT DETERMINE | F | **halo_rev_a** | rev_a names a specific part and diverges from Apple's on a stated, priced reason. |
| 16 | Bulk energy storage | DIVERGED | UNSTARTED | F | **halo_rev_a** | rev_a is at one twelfth of Apple's bulk, which is a large and honestly-recorded miss. |
| 17 | Debug access and test points | DIVERGED | UNSTARTED | G | **halo_rev_a** | Apple's debug surface is a documented glitch target and Apple documents none of it. |
| 18 | Surface finish | CANNOT DETERMINE | SAME | F | **halo_replica** | The Replica's finish is a stated choice inside a measured bound, with the measurement's own control published. |
| 19 | Soldermask colour | CANNOT DETERMINE | CANNOT DETERMINE | F | **CANNOT DETERMINE** | Apple's mask colour is not known and the Replica's black is explicitly a choice rather than a match. |
| 20 | Board identity marking | EQUIVALENT | DIVERGED | G | **halo_replica** | Putting 'U1 IS UNPOPULATED' on the copper rather than only in a file is the one place the Replica applies this project's own standard to a physical artifact: a fact a person can find without reading t... |
| 21 | Cost at 10 / 100 / 1000 / 10000 | CANNOT DETERMINE | CANNOT DETERMINE | B | **halo_rev_a** | AND IT IS NOT CLOSE. |
| 22 | Manufacturability of the bare board | DIVERGED | SAME | B | **halo_rev_a** | One of these two boards can be ordered today and the other cannot be ordered at all. |
| 23 | Design integrity — can the artifact be checked at all | n/a | n/a | B | **halo_rev_a** | THIS ROW IS THE ASYMMETRY THE WHOLE FILE RESTS ON. |
| 24 | Coverage — how much of Apple's board each object accounts for | SAME | UNSTARTED | F | **halo_rev_a** | COVERAGE IS PART OF FIDELITY AND THE REPLICA HAS HALF A BOARD. |
| 25 | Design-rule violations, and whose they are | n/a | n/a | F | **CANNOT DETERMINE** | Apple has no DRC to compare against, so no fidelity verdict is available on this axis at all. |

**Primary-axis tally across 25 axes:** halo_rev_a **12** · halo_replica **7** · CANNOT DETERMINE **4** · TIE **1** · TIE AT ZERO **1**

Secondary judgements — the rows where a second axis reverses the first — are in the row bodies below and are the substance of this document, not a footnote to it.

---

## The accumulation — the divergence counter

*THE-DRIFT.md's own prescribed fix, verbatim: 'A divergence budget, made visible. That count belongs on the convergence scoreboard as a tracked row with a stated ceiling, so the thirteenth divergence is visibly the thirteenth rather than just the next one. A ratchet with no counter is how you get here.' This is the counter. It is computed from the rows above by tools/k_threeway.py, not typed.*

| | SAME | EQUIVALENT | DIVERGED | MISSING | CANNOT DETERMINE | UNSTARTED | n/a | departures | NO ANSWER |
|---|--:|--:|--:|--:|--:|--:|--:|--:|--:|
| **halo_rev_a** | 5 | 2 | 12 | 1 | 3 | 0 | 2 | **13** | **3** |
| **halo_replica** | 9 | 0 | 1 | 1 | 8 | 4 | 2 | **2** | **12** |

**THE TWO RIGHT-HAND COLUMNS MUST BE READ TOGETHER AND NEITHER MAY BE QUOTED ALONE.** The Replica's 2 departures against rev_a's 13 looks like a rout and is not one: the Replica also has NO ANSWER on 12 of 24 axes against rev_a's 3. An axis you never answered cannot be a departure. Quoting the departure count on its own would be this project's own headline-from-a-favourable-half failure, in the document written to catch it.

- **SAME** — the same thing, or inside the bound Apple's own value is known to within. No departure.
- **EQUIVALENT** — a different realisation doing the same job to the same specification.
- **DIVERGED** — a deliberate difference from what Apple built. Includes functions DELETED.
- **MISSING** — the function is absent and nothing replaces it.
- **CANNOT DETERMINE** — MEASURED AND NOT SETTLED. An attempt was made, it is on record, and what would settle it is named.
- **UNSTARTED** — NOT ATTEMPTED. Distinct from CANNOT DETERMINE and the distinction is the point of the count below: an unstarted axis is a job, a CANNOT DETERMINE is a limit.

**The ceiling.** THERE IS NO CEILING, because nobody has set one. THE-DRIFT.md asks for 'a stated ceiling' and no document in this repo states a number. That is an open product decision and it is routed to the orchestrator, not decided here.

### What the count says

- halo_rev_a departs from Apple on 13 of the 24 axes (12 DIVERGED + 1 MISSING). D23's own sentence says halo 'had diverged from the AirTag in seven places'. The full three-way count is nearly double that. THE RATCHET WAS WORSE THAN THE DOCUMENT THAT NAMED IT — which is exactly what a ratchet with no counter does.
- halo_replica matches Apple on 9 axes and HAS NO ANSWER ON 12 (8 CANNOT DETERMINE + 4 UNSTARTED). Half the table.
- AND THE NINE MATCHES ARE ALL IN ONE REGION. Outline, shape, thickness, layer count, centre hole, finish, and the three refusals where the right answer was to draw nothing. THE REPLICA MATCHES APPLE ON THE BARE BOARD AND HAS NO ANSWER ON ALMOST ANYTHING MOUNTED TO IT. That is a true and useful object; it is not a replica of the AirTag's internals, which is what was asked for.
- The four UNSTARTED axes are one job, not four: Apple's BACK face has never been drawn. Battery contacts, the five bulk capacitors, the ~38 test points and half the coverage all sit on it, and oflynn-frontside-fullres.jpeg (2347x2344) already carries every one of them. It is the highest-value unblocked work in this lane by a wide margin.

### The GOAL.md re-read

*'Periodically read GOAL.md and ask one question in writing: does what we are building still answer this? Record the answer even when it is yes, because a check that only produces output when something is wrong is a check nobody trusts.' Run here, 2026-09-05, against the accumulation rather than against any single row.*

**GOAL 1 a perfect copy of the AirTag internals** — NEITHER OBJECT ANSWERS THIS, and they fail it in opposite directions. rev_a is a functional equivalent with 13 named departures. The Replica is a faithful substrate with the electronics absent — it matches the board and not the internals, and 'internals' is the word Leif used. ANSWER: NO, for both, for different reasons.

**GOAL 2 an embeddable block not only a puck** — rev_a answers it: a KiCad hierarchical block with the antenna in its own copper, which is exactly why row 6's fidelity loss is a GOAL win. The Replica cannot answer it and cannot be made to — it has no schematic, no netlist and no nets, so there is no block to embed. ANSWER: YES for rev_a, STRUCTURALLY NO for the Replica.

**GOAL 3 local relative position between Leifs own devices** — rev_a answers it with Bluetooth Channel Sounding on the nRF54L10 — the one capability in the whole comparison that Apple does not provide at any price. The Replica does not address it. ANSWER: YES for rev_a, NOT ADDRESSED by the Replica.

**CONSTRAINT cost is a first class spec** — rev_a is priced at 10/100/1000/10000 against a dated catalogue and FAILS honestly at two of them on stock. The Replica has no cost, no sourced part, and a board that is not orderable at either house. ANSWER: YES for rev_a, NO for the Replica.

### The conclusion

THE-DRIFT.md says halo 'built the wrong thing while every step was right'. Measured against GOAL.md rather than against the AirTag, THAT IS TOO HARSH ON rev_a AND TOO KIND TO THE PROCESS. rev_a answers three of GOAL.md's four stated aims and is the only one of the two objects that answers any of them. What actually went wrong is narrower and worse: Leif asked for BOTH — 'so create many different versions including one which is a perfect recreation' — and the project built the equivalent and did not build the recreation until he said so twice. The defect was never that rev_a diverged. It was that the recreation was not also built, and that nothing counted the divergences while it wasn't.

### And the risk in this very document

The failure THE-DRIFT.md describes is a sequence of locally-correct judgements arriving somewhere nobody chose. THIS FILE COULD REPEAT IT by letting 'closer to Apple' accumulate into 'better'. It does not: on the primary axis of each row halo_rev_a wins 12 and halo_replica wins 7. The Replica's wins are real and they are concentrated in one region of the board, and this document says so in the same breath as it counts them.

---

## Distance from a deliverable — the other axis of drift

*The divergence counter in threeway.json counts distance FROM APPLE. It does not count DISTANCE FROM A DELIVERABLE, and that is the gap that let this project run for a day with 130 measurement files, 40 measuring tools and twelve evidence documents, and NOTHING ANYONE CAN OPEN IN KiCAD OR SEND TO A FABRICATOR. We had an instrument for one axis of drift and none for the other, so the Replica could move steadily away from being a buildable thing while every number about fidelity improved. THIS IS THE MISSING AXIS. It is red until KiCad can open something.*

**8 of 8 artifacts exist and open. 0 of those are STALE. 6 rows are green.**

| | artifact | state | opens | current | source ok | **its own verdict** | evidence |
|---|---|:-:|:-:|:-:|:-:|:-:|---|
| D1 | Schematic source | ✅ | yes | — | — | — | `electronics/halo_replica/out/schematic/halo_replica.kicad_sch` |
| D2 | Netlist | ✅ | yes | yes | — | — | `electronics/halo_replica/out/schematic/halo_replica.net` |
| D3 | Footprint library | ✅ | yes | — | — | — | `electronics/halo_replica/halo_replica.pretty/REPL_0201_0603Metric.kicad_mod`, `electronics/halo_replica/halo_replica.pretty/REPL_0402_1005Metric.kicad_mod`, `electronics/halo_replica/halo_replica.pretty/REPL_ABSENCE_EYEBALLED.kicad_mod`, `electronics/halo_replica/halo_replica.pretty/REPL_BACK_CONTACT_POS.kicad_mod`, `electronics/halo_replica/halo_replica.pretty/REPL_BPAD_D0.21.kicad_mod`, `electronics/halo_replica/halo_replica.pretty/REPL_BPAD_D0.34.kicad_mod` |
| D4 | Board file | ✅ | yes | yes | yes | — | `electronics/halo_replica/pcb/out/halo_replica.kicad_pcb` |
| D5 | ERC result | ✅ | yes | yes | — | 0E | `electronics/halo_replica/out/schematic/halo_replica.erc.json` |
| D6 | DRC result | ✅ | yes | yes | yes | **33E 0U** | `electronics/halo_replica/pcb/out/halo_replica.drc.json` |
| D7 | Gerbers | 🔴 | yes | yes | **NO** | — | the package is not a complete copper set: PRESENT BUT CONTAINS NO IMAGE: In1.Cu (halo_replica-In1_Cu.g1), In2.Cu (halo_replica-In2_Cu.g2). Found 3 of 5 required layers. A zip that opens and carries no copper would waste the order. |
| D8 | Drill file | 🔴 | yes | yes | **NO** | — | cut from a source that FAILED its own checks: D6 reports 33 error(s). It exists, it may even be current, and IT IS NOT BUILDABLE. |

**Freshness.** AN ARTIFACT THAT OPENS IS NOT AN ARTIFACT THAT IS CURRENT. halo_rev_a's gerbers open perfectly and describe a board that no longer exists: they carry an embedded KiCad creation date of 2026-09-05T06:06:39 while the board file they came from has an mtime of 07:54:19 - 6,460 seconds later, an hour and three quarters in which the board gained the NFC coil keep-out, lost plane copper under the coil, and was rerouted from 83 unconnected items to 28. A pure existence test reads that GREEN. EXISTENCE IS ADJACENT TO CURRENCY, which is the same failure shape as every other control this lane broke today.

**The rule.** Every non-root artifact must be NEWER THAN EVERY ONE OF ITS SOURCES. A set of files is only as fresh as its OLDEST member; a source is as new as its NEWEST member. Both directions are the conservative one. FRESH -> the row can be green. STALE -> RED. SOURCE ABSENT -> CANNOT DETERMINE, never green and never red: an artifact with no source to compare against is UNMEASURED, not stale, and this project does not let an unmeasured thing occupy the same field as a measured one.

**Timestamps.** An EMBEDDED timestamp - one the generating tool wrote into its own output - is preferred wherever it exists. mtime is the fallback and it is WEAK: a git checkout rewrites every mtime to checkout time, which can make a stale artifact look fresh or a fresh one look stale. Every row records which kind it used, and a comparison that mixes an embedded stamp against an mtime says so.

**Its own verdict — the column that removes a trap rather than documenting it.** A REPORT'S ROW STATE AND A REPORT'S CONTENTS ARE DIFFERENT FACTS, and with only three columns the first reads as the second. D6 showed valid=yes, which by this file's own rules means ITS SOURCE (the ERC) was clean - and reads to anyone scanning a table for green as 'the DRC passed'. It did not: the Replica's DRC reports 42 errors against 3 warnings, with actual clearances down to 0.0000 mm. The column that says so is now beside it. Documenting the trap was the weaker option; removing it is this one.

> **A report row being GREEN means:** the report EXISTS, OPENS, is NEWER than the thing it grades, and came from a source that had itself passed. It says NOTHING about what the report FOUND. A DRC listing 42 errors is a perfectly good ARTIFACT and a perfectly bad BOARD - different objects, and this table now shows both.

> **And a failing report does not turn its own row red**, because the artifact is not the defect. Turning D6 red on its contents would conflate 'we have no DRC' with 'the DRC found things', and this project already has a standing rule against conflating could-not-build with could-not-verify. Contents become a GATE where something DEPENDS on them - which is exactly what the third leg does for D7 and D8.

### The fifth state — whose fault a clearance violation is

42 of the Replica's 45 DRC violations are clearance errors on rows placed at MEASURED positions and sizes. An overlap there means one of three things and only one is a defect: Apple's metal genuinely is that close, OR our measurement could not separate two adjacent features, OR we drew something wrong. A gate that cannot tell them apart gets switched off for crying wolf - the same way an mtime-only freshness rule gets switched off the first time it calls a clean clone stale.

**IF A VIOLATION CAN MOVE OUT OF DRAWN-WRONG BY EDITING A STRING, THE GATE BECOMES SOMETHING A LANE IMPROVES BY TYPING. So every excusing class carries a RESOLVABLE POINTER that this check resolves AND CHECKS SUPPORTS THE CLAIM. A pointer that resolves but does not support the claim is refused exactly like one that does not resolve.**

**The default is the honest one.** DRAWN-WRONG needs no pointer and is what an UNCLASSIFIED violation falls back to. Silence means our fault, never Apple's. A lane that wants a violation excused must produce evidence; a lane that produces nothing gets the blame. The incentive runs the correct way round.

| class | pointer required | blocks fabrication | means |
|---|:-:|:-:|---|
| **DRAWN-WRONG** | no | **yes** | we placed something wrong. Our defect, and the default. |
| **MEASUREMENT-LIMITED** | yes | **yes** | the two features are closer together than our measurement could separate, so the overlap is an artifact of resolution rather than a placement error. NOT OUR DEFECT AND STILL NOT FABRICABLE - you cannot cut a board where two pads overlap, whatever the reason. It blocks, and it names a different fix: a measurement that CAN separate them, not a nudged pad. |
| **GENUINELY-TOUCHING** | yes | no | the two features are the same net or the same physical feature, so there is no clearance to violate. The rule fired on a distinction that does not exist on Apple's board. |
| **BOUND-LIMITED** | yes | **yes** | copper-to-OUTLINE, where our outline's diameter is a BOUND (24.95-26.34 mm) and not a number. No placement change fixes these honestly: the violation is against an edge whose position is not known. Specified by the board lane, not invented here. |

**Resolution floor: 0.0606 mm.** TWO genuine pixels at the coarser of this face's two genuine resolutions: 2 / 33 px/mm = 0.0606 mm. One pixel of edge-location uncertainty on each of the two facing edges. *Not the registration hold-out:* The handoff's held-out registration error is 0.1256 mm, and using THAT as the floor would excuse roughly twice as many violations. It is the wrong number here: a global registration error is COMMON-MODE between two features measured in the SAME frame and very largely cancels out of the gap between them. Reaching for the larger number would have been the permissive direction dressed as rigour. *Not one pixel:* one pixel would credit a single edge with perfect location while the other carries all the error. Two edges, one pixel each. *What would sharpen it:* a measured edge-location repeatability on this face - two independent extractors on the same edges, the way the outline lanes measured 0.0158 mm median across 1182 shared rays on the other face. Nobody has done that here, so this floor is derived rather than measured, and it says so.

**Current split of 33 clearance errors in `electronics/halo_replica/pcb/out/halo_replica.drc.json`:** DRAWN-WRONG **33** · MEASUREMENT-LIMITED **0** · GENUINELY-TOUCHING **0** · BOUND-LIMITED **0** — 33 block fabrication. no classification file found - every error falls back to DRAWN-WRONG. That is not CANNOT DETERMINE: an unexcused violation IS our defect until evidence says otherwise.

**The rule.** A ROW IS GREEN ONLY WHEN A FILE EXISTS THAT THE RELEVANT TOOL CAN ACTUALLY OPEN. A path that exists is not an artifact. Every row therefore carries a FORMAT PROBE - a string the real format must contain - and an empty file, a stub, or a file of the wrong kind at the right name all stay RED. The selftest watches each of those three cases fail on purpose, because a check that only ever goes red proves nothing about its own ability to go green.

**Anti-gaming.** The board and schematic rows additionally REFUSE a file whose sha256 matches halo_rev_a's equivalent. The cheapest way to turn this check green without doing the work is to copy the board Leif rejected into the Replica's tree, and that would be the exact failure this check exists to catch, dressed as a pass.

Why each is required, in the row's own words:

- **D1 Schematic source** — There is no circuit until there is a schematic. Every net, every part and every connection the Replica claims to copy from Apple lives here or lives nowhere.
- **D2 Netlist** — The netlist is the schematic in the form the board tool consumes. Without it a board file is a drawing of copper rather than a realisation of a circuit, and nothing can check that the copper matches the schematic.
- **D3 Footprint library** — Apple's parts are WLCSP-50, WLCSP-10, 0201 and a wound coil. None of those has a stock footprint that fits this board, and the Replica's whole claim is that its geometry is measured rather than assumed. The measured geometry has to become land patterns or it is not in the design.
- **D4 Board file** — THIS IS THE ONE LEIF ASKED FOR. His words were 'the exact pcb design and all the components'. Until this row is green there is no PCB design, only an apparatus for measuring one.
- **D5 ERC result** — A schematic nobody ran the rule checker over is a claim, not a verified circuit. This project's own standard is that a check which never ran is verification debt.
- **D6 DRC result** — Same argument one level down, and it is the row THREE-WAY.md row 23 turns on: halo_rev_a is a design that CAN be wrong and is measured to be wrong in four height rows. The Replica cannot be wrong in that sense at all, because there is nothing to check.
- **D7 Gerbers** — A board file is what WE can open. Gerbers are what a FABRICATOR can open. Nothing gets made without them. *halo_rev_a HAS NOT GOT THESE EITHER. This row is red for both boards, and saying so is the point - a check that only accuses the Replica would be measuring the wrong thing.*
- **D8 Drill file** — The board is annular with a routed centre pocket and three plated tooling holes. Every one of those is a drill or route operation and none of them exists until this file does. *halo_rev_a HAS NOT GOT THIS EITHER. Red for both.*

---

## Reconciliation with the prior comparison

*The brief's instruction: read out/comparison/ and docs/COMPARISON.md and say whether these numbers agree, and where they do not. They mostly agree. Three rows do not, and one of the three matters.*

**Denominators.** docs/COMPARISON.md grades 34 rows (22 component + 12 PCB) and counts 18 DIVERGED + 2 MISSING = 20 departures. This file grades 24 axes and counts 12 DIVERGED + 1 MISSING = 13. THESE ARE NOT THE SAME MEASUREMENT AND 20 vs 13 IS NOT A CHANGE. The prior page grades parts; this page grades axes, and one axis can hold several parts (row 9 holds Apple's flash, its LDO and its load switch, which are three rows there and one here).

### Where they agree

- 6 of 18 Apple BOM lines carry a usable manufacturer part number; 9 of 18 carry none at all. Not re-derived here and not disputed - it is a BOM fact, not a board fact, and it remains the real ceiling on 'recreating it exactly', higher than the U1 wall.
- Board thickness DIVERGED for rev_a, with D17's reason. Agreed, and this file adds that the Replica's faithful 0.30 mm is what makes it unorderable.
- Connectors SAME, battery contacts SAME, populated sides SAME. Agreed on all three.
- The U1 wall. Agreed, and unchanged: neither board has a UWB radio and the part is not sold.

### Where they do not

**PCB row 3, layer count**

- *prior:* CANNOT DETERMINE - 'halo's 4 is measured; Apple's 4 is a guess nobody has confirmed'
- *now:* SAME. Apple's 4 is COUNTED from a published physical delayering, and the superposition reading that would have made those four files carry no count was falsified at a named spot.
- *why it changed:* the evidence arrived after that page was generated. The prior verdict was correct for its state of knowledge. THIS CLOSES ONE OF THE PRIOR PAGE'S THREE CANNOT DETERMINE PCB ROWS.

**PCB row 1, outer diameter**

- *prior:* SAME - '26.0000 mm on the major axis, inside Apple's stated ~26 mm'
- *now:* SAME, but on a different basis. Apple's '~26 mm' has since been retracted (E04 -> E05: four methods that could not disagree, because all four applied a scalar px/mm to an anisotropic projection). Apple's OD is now a BOUND 24.95-26.34 mm with a signed downward expectation. rev_a's 26.0000 is still inside it. THE VERDICT SURVIVES; THE REASON UNDER IT DOES NOT.

**components row 15, the 2.4 GHz antenna**

- *prior:* 'AE1 - a rim inverted-F... ce-rf models +0.521 dBi, 3.7 dB above Apple's published figure'
- *now:* CONTRADICTED BY rev_a's OWN FILE on both halves. Topology: board.py builds 'the meandered quarter-wave monopole' and the owner describes a nine-tooth meander. Performance: board.py's WHAT THIS BOARD DOES NOT CLAIM section says the element is a parametric placeholder, that lane T3's round-board cases resonate at 4.0 and 5.8 GHz instead of 2.44 on a different outline, and that 'Its S11 is CANNOT DETERMINE until ce-rf measures THIS copper. It is not asserted to work.'
- *why it matters:* IT IS THE ONE ROW WHERE THE PRIOR PAGE CLAIMS rev_a BEATS APPLE ON A PHYSICAL NUMBER, and rev_a's own source file withdraws it. Apple's -3.2 dBi is a measurement of a shipped antenna; +0.521 dBi is a model of a placeholder. Comparing them was never valid.
- *not fixed here:* halo_rev_a and spec/comparison.json belong to other live sessions. Read, not written. Routed to the orchestrator.

### What this file adds that the prior one could not

- A THIRD COLUMN. The prior page is Apple vs halo. Nothing had ever set our two boards against each other, which is the only way to ask whether a divergence was worth making.
- A NAMED JUDGING AXIS PER ROW. The prior page's verdicts (SAME/EQUIVALENT/DIVERGED) describe a relationship; they never say which object is better, so 'DIVERGED' reads as a demerit even on the five rows where the divergence is the right call.
- A DIVERGENCE COUNTER. THE-DRIFT.md asked for one and nothing had built it.
- THE UNSTARTED / CANNOT DETERMINE SPLIT. The prior page has no way to say 'nobody has tried yet', so the Replica's four unstarted axes would have been filed as limits rather than as the one job they actually are.

---

## Outline and shape

### 1 · Board outer diameter

| | value | state | how it is known |
|---|---|---|---|
| **Apple AirTag A2187** | BOUND 24.95 – 26.34 mm. NOT a number. | BOUNDED, signed downward | halo_replica metrology M02 via board/board.json — the two image axes do not share a scale (26.3 wide x 25.0 tall). If the bound moves it moves DOWN. |
| **halo_rev_a** | 26.0000 mm major x 25.6138 mm minor | MEASURED off Edge_Cuts geometry | out/verify/dfm-jlc-4layer.json board_facts.size_mm, measured by `fab dfm` and cross-checked on the exported Gerber (720 points). Minor axis is short because three 26-degree keying notches cut to R12.60. |
| **halo_replica** | 25.1593 mm AS DRAWN — itself a shape result, not a fourth opinion on the diameter | PARAMETER, inside Apple's bound | board/board.json parameters.outer_diameter_mm.value, from p_fit.py robust circle fit, 1194 rays at 106.313 px/mm. It inherits the same registration scale as every other number in that frame. |

*Against Apple:* **halo_rev_a SAME** — 26.0000 inside Apple's 24.95-26.34 bound. **halo_replica SAME** — 25.1593 inside the same bound.

**Better on F: CANNOT DETERMINE.** Apple's diameter is a bound 1.39 mm wide and BOTH our boards sit inside it — 26.0000 and 25.1593. You cannot rank fidelity against a bound that contains both candidates. The Replica's number is nearer the bound's centre, and that is a fact about arithmetic, not about Apple.

*Would settle it:* a caliper on a bare MLB, or a scale-referenced edge-on photograph. Optical measurement from the existing frames cannot do it — M02 already established the two axes do not share a scale.

### 2 · Board outline SHAPE (not size)

| | value | state | how it is known |
|---|---|---|---|
| **Apple AirTag A2187** | Circle clipped by straight chords. 1194 measured rays; a plain circle fits at sd 0.5629 mm / 43.6% inliers, circle+4 chords at sd 0.2771 mm / 55.8%. | MEASURED | board/outline/outline-fit-oflynn.json, fitted primitives never merged with the raw silhouette. |
| **halo_rev_a** | Circle with THREE 26-degree keying notches cut to R12.60. Apple has no keying notches. | MEASURED off Edge_Cuts | spec/comparison.json pcb row 1 why-text; the notches are rev_a's own mechanical keying feature. |
| **halo_replica** | The fitted circle + 4 straight chords, drawn. Residual sd 0.2771 mm, 51% of the perimeter within 0.15 mm of Apple's own edge, 12% beyond 0.40 mm, 9% carrying no ray. | MEASURED, disagreement drawn onto the overlay in colour | board/CLOSING.md section 2, X4 RMS 0.413 mm over 654 rays; board/out/compare-front.png. |

*Against Apple:* **halo_rev_a DIVERGED** — three 26-degree keying notches Apple's board does not have. **halo_replica SAME** — fitted to Apple's own edge, residual sd 0.2771 mm.

**Better on F: halo_replica.** The Replica's outline is FITTED TO APPLE'S OWN EDGE with a published residual and a published per-degree map of where it disagrees. rev_a's three keying notches are a feature Apple's board does not have, and no measurement of Apple's outline was ever an input to them. This is a genuine Replica win and it is the clearest one in the file.

> **On B: halo_rev_a.** the notches key the board to the carrier so it can only go in one way. The Replica's chords carry no such function and no tolerance — CLOSING.md says plainly the silhouette 'cannot be dimensioned or toleranced'.

### 5 · Centre hole / board shape

| | value | state | how it is known |
|---|---|---|---|
| **Apple AirTag A2187** | ANNULAR. A routed pocket — superellipse plus 7 measured straight facets, i.e. a rounded polygon, not a circle. NO DIAMETER IS PUBLISHED by this lane. | PARTIALLY DETERMINED | board/board.json parameters.centre_hole. Three superellipse fits disagree on the exponent and disagree in different directions (n=2.70, n pinned at 2.00, n=2.449). |
| **halo_rev_a** | NO CENTRE HOLE. A solid disc. | MEASURED off Edge_Cuts | spec/comparison.json pcb row 4. D11a/D17: the hole holds a magnet and a voice coil rev_a deleted, so there is nothing to put in it and the SoC sits in the middle instead. |
| **halo_replica** | Superellipse + 7 facets drawn. Residual 0.3342 -> 0.1987 mm (40.5%) against a fabrication floor of -0.31% measured on a synthetic pure superellipse. No diameter published. | DRAWN, earned against a floor | board/board.json parameters.centre_hole.facets_earned. |

*Against Apple:* **halo_rev_a DIVERGED** — solid disc against an annular board. **halo_replica SAME** — annular, superellipse + 7 facets.

**Better on F: halo_replica.** Apple's board is annular and rev_a's is not. spec/comparison.json calls this 'the divergence every other mechanical difference hangs off' and it is right. The Replica reproduces it and additionally establishes that the hole is a ROUTED POCKET rather than a circle, which no prior document in this repo had stated.

> **On G: halo_rev_a.** GOAL.md wants an embeddable circuit block. A hole that exists to hold a magnet and a coil nobody is fitting is dead area in the middle of the block, and the SoC has to go somewhere. On the goal Leif actually stated, rev_a's solid disc is the better object.

> **On F-limit: n/a.** the Replica's win is bounded: the facet SIDE WALLS are not measured. Each facet ends where the boundary crosses 0.30 mm from the superellipse, which is not where the wall is. A perpendicular-edge detector would close it.

---

## Stackup and materials

### 3 · Board thickness

| | value | state | how it is known |
|---|---|---|---|
| **Apple AirTag A2187** | 0.30 mm | REPORTED, NOT MEASURED — a teardown engineer's statement in passing, no error bar ever published | Colin O'Flynn, verbatim: 'it's 0.3mm PCB so I'm pretty sure I broke some solder joints getting it out.' Catley corroborates THIN, not 0.30. |
| **halo_rev_a** | 0.60 mm — TWICE Apple's, deliberately | MEASURED off the board's own stackup | out/verify/dfm-jlc-4layer.json board_facts.thickness_mm. D17: deleting Apple's magnet and voice coil returned 1.742 mm to the stack and lane M spent part of it on a board that does not break when handled — the exact failure O'Flynn reports in the sentence that gives us Apple's number. |
| **halo_replica** | 0.30 mm AS DRAWN | SETTLED as-drawn; NOT ORDERABLE | board/board.json parameters.thickness_mm. Below PCBWay's 0.40 mm four-layer floor and below JLCPCB's 0.40 mm overall minimum at ANY layer count. That is a fact about us, not about Apple, and the two numbers are never fused. |

*Against Apple:* **halo_rev_a DIVERGED** — 0.60 against 0.30 - twice. **halo_replica SAME** — 0.30 as-drawn, matching the reported figure.

**Better on F: halo_replica.** 0.30 against 0.60 is a 2x miss for rev_a on the best figure anyone has for Apple. But the Replica's win is only as good as its target, and the target is a tweet: REPORTED, NOT MEASURED, uncertainty unbounded in both directions.

*Would settle it:* a caliper on a bare MLB or a cross-section micrograph. No published photograph shows the board edge-on; the best-scaled flat frame renders 0.30 mm as 4.8 px.

> **On B: halo_rev_a.** 0.60 mm is PCBWay's normal four-layer thickness and an orderable JLCPCB option. The Replica AS DRAWN cannot be ordered from either house at any layer count above two, and not from JLCPCB at all — anchored in stackup.json fabrication_delta.

> **On G: halo_rev_a.** GOAL.md asks for a block 'easy for everyone to integrate into their own pcbs'. A 0.30 mm board whose own reference source broke solder joints lifting it is not that.

### 4 · Layer count

| | value | state | how it is known |
|---|---|---|---|
| **Apple AirTag A2187** | 4 | COUNTED from a published physical delayering | stacksmashing/airtag-hardware pcb/layer1..layer4, credited to David Hulton. Cited, not redistributed. The superposition reading was falsified at a named spot: layer1's fine-pitch land grid is ABSENT from layer2 at the same board location. |
| **halo_rev_a** | 4 | MEASURED off the .kicad_pcb stackup | out/verify/dfm-jlc-4layer.json board_facts.copper_layers, read by ce-fab's parser during `fab dfm`. |
| **halo_replica** | 4 | MATCHES APPLE — no longer a Replica assumption | board/board.json parameters.layer_count. The orchestrator had authorised drawing 4 as a stated choice inside a {4,6} bound; the delayering arrived in the same session and made that unnecessary. |

*Against Apple:* **halo_rev_a SAME** — 4 = 4. **halo_replica SAME** — 4 = 4.

**Better on F: TIE.** All three are 4 and all three are counted rather than assumed. Nobody wins a row everybody passes.

> **On meta: n/a.** THIS ROW DISAGREES WITH THE PRIOR COMPARISON AND THE DISAGREEMENT IS AN UPGRADE. docs/COMPARISON.md pcb row 3 grades this CANNOT DETERMINE — 'halo's 4 is measured; Apple's 4 is a guess nobody has confirmed'. That was correct when written. The delayering evidence arrived afterwards, so the row can now be graded and it grades as a match. One of the three CANNOT DETERMINE rows in the prior PCB comparison is closed by this lane's work.

### 18 · Surface finish

| | value | state | how it is known |
|---|---|---|---|
| **Apple AirTag A2187** | GOLD-BEARING — ENIG or another immersion/electroless-gold finish. Plated hole rims at hue 40.5 and 43.8 degrees against BARE COPPER WIRE IN THE SAME FRAME at 21.8 degrees: 19-22 degrees of separation. Not HASL, tin or silver, all of which are grey. | MEASURED, with an in-frame control | stackup.json apple.surface_finish. The control is not optional: colour under an unknown illuminant cannot be trusted absolutely, but a hue DIFFERENCE between two metals in one frame survives a white-balance error because the error moves both together. |
| **halo_rev_a** | CANNOT DETERMINE from this lane's reading — no finish row appears in out/verify/dfm-jlc-4layer.json board_facts. | CANNOT DETERMINE — not read, and not asserted | the DFM output carries copper_layers, thickness, size, footprints, vias, tracks and mask width, and no finish field. |
| **halo_replica** | ENIG — chosen because the measurement says gold-bearing and because a 50-ball WLCSP needs coplanarity. ENIG is the member of the gold family both prototype houses offer. | CHOICE inside a measured bound | stackup.json replica_as_drawn.finish. |

*Against Apple:* **halo_rev_a CANNOT DETERMINE** — no finish field in the DFM output this lane read. **halo_replica SAME** — ENIG, a choice inside a measured gold-bearing bound.

**Better on F: halo_replica.** The Replica's finish is a stated choice inside a measured bound, with the measurement's own control published. rev_a's finish could not be read from its DFM output by this lane, so it is not being scored — an unread value is not a losing value.

*Would settle it:* reading the finish out of rev_a's fabrication order or its .kicad_pro. This lane did not do it because the file is another live session's and this row is not worth a write anywhere near it.

> **On F-limit: n/a.** WHICH gold finish stays CANNOT DETERMINE for Apple. ENIG, ENEPIG, immersion gold and hard gold are indistinguishable by hue in a JPEG. XRF or a cross-section would separate them.

### 19 · Soldermask colour

| | value | state | how it is known |
|---|---|---|---|
| **Apple AirTag A2187** | CANNOT DETERMINE. Bounded to DARK AND NEUTRAL — not green, blue, red or white. Flat mask patches read V=65 to 128 against a white in-frame CONTROL at V=224, R/G/B within about 10 counts. | CANNOT DETERMINE, bounded | stackup.json apple.soldermask_colour. The apparent violet cast (hue ~270 at saturation 0.14) is inside what a white-balance error produces on a near-neutral dark surface, so it is NOT evidence of a purple mask. |
| **halo_rev_a** | CANNOT DETERMINE from this lane's reading — no mask colour in the DFM output. | CANNOT DETERMINE — not read | out/verify/dfm-jlc-4layer.json board_facts has no colour field. |
| **halo_replica** | BLACK — recorded as a CHOICE within the measured bound, not as Apple's colour. | CHOICE inside a bound | stackup.json replica_as_drawn.soldermask and soldermask_note. |

*Against Apple:* **halo_rev_a CANNOT DETERMINE** — no colour field in the DFM output this lane read. **halo_replica CANNOT DETERMINE** — Apple's own mask colour is CANNOT DETERMINE, so nothing can match it.

**Better on F: CANNOT DETERMINE.** Apple's mask colour is not known and the Replica's black is explicitly a choice rather than a match. A choice inside a bound cannot be graded against the bound.

*Would settle it:* the board photographed beside a colour checker, or in hand.

---

## Radio

### 6 · BLE and UWB antenna implementation

| | value | state | how it is known |
|---|---|---|---|
| **Apple AirTag A2187** | NOT ON THE BOARD. A BLE inverted-F and a UWB patch, LASER-DIRECT-STRUCTURED onto a moulded plastic carrier and soldered to pads at the board rim. BLE max gain -3.2 dBi; UWB -1.6 dBi at 6.5 GHz. Six solder joints that TEAR when the board is lifted. | MEASURED — the on-board hypothesis was tested at ~90-110 px/mm and REFUTED. No meander, no inverted-F, no patch in the outer copper of either face. | evidence/E01-ARE-THE-ANTENNAS-ON-THE-BOARD.md; stackup.json apple.antennas_and_the_stackup. |
| **halo_rev_a** | AE1 — a nine-tooth meandered quarter-wave monopole in the board's OWN COPPER on the top layer alone, spanning R11.192–R12.200 with a 24.49100 mm conductor. Zero carrier, zero solder joints. Nearest foreign copper 0.3627 mm, MEASURED in plan view across all layers, against a 0.30 mm floor. | MEASURED (clearance) / REPORTED by the rev_a owner (tooth count and radii, relayed 2026-09-05) | out/verify/routed-check.json row antenna_arm_not_shadowed = 0.3627 mm, verdict PASS. The 0.30 mm floor is not arbitrary: lane T3 solved the coil at 2.4321 GHz in band at 0.30 mm and at 1.7666 GHz under the arm — a 668 MHz shift not recoverable by tuning. |
| **halo_replica** | NO ANTENNAS DRAWN, and that is the correct drawing. Also NO RIM PADS — their count is CANNOT DETERMINE and CLOSED. | REFUSED, with the reason | board/board.json not_drawn.antennas and not_drawn.rim_pads. The withdrawn 15- and 13-pad candidate angle sets FAILED a positive control. |

*Against Apple:* **halo_rev_a DIVERGED** — a nine-tooth meander in board copper Apple has nowhere. **halo_replica SAME** — no antennas in copper, which is what Apple's board has.

**Better on F: halo_replica.** Apple has no antenna in board copper and neither does the Replica. rev_a puts a nine-tooth meander on F.Cu that Apple's board does not have anywhere. On fidelity this is not close.

> **On B: halo_rev_a.** AN LDS CARRIER NEEDS A MOULD TOOL AND A LASER-PLATING LINE. Etched copper is free at every PCB house on earth and cannot tear off. The Replica has no antenna at all and therefore cannot transmit; it is not in this race.

> **On G: halo_rev_a.** GOAL.md asks for a block anyone can drop into their own board in any outline. A block whose radio only works with a custom moulded carrier is not distributable. D16 already names the residual limit: the keep-out has to travel as WORDS an integrator reads and applies. THIS IS THE STRONGEST rev_a SURVIVOR IN THE FILE — stronger than the deleted amplifier D23 predicted.

> **On RF PERFORMANCE: CANNOT DETERMINE FOR BOTH, AND THE PRIOR COMPARISON OVERSTATES rev_a.** spec/comparison.json components row 15 credits AE1 with 'ce-rf models +0.521 dBi, 3.7 dB above Apple's published figure'. rev_a's OWN board.py, under a heading WHAT THIS BOARD DOES NOT CLAIM, says the opposite: the element is 'a PARAMETRIC PLACEHOLDER at a length computed from a quarter wavelength', lane T3's two round-board cases 'resonate at 4.0 and 5.8 GHz instead of 2.44' on a diameter-30 outline that is not this board, and 'Its S11 is CANNOT DETERMINE until ce-rf measures THIS copper. It is not asserted to work.' THE GAIN FIGURE MUST NOT BE QUOTED AS A rev_a ADVANTAGE. Apple's -3.2 dBi is a published measurement of a shipped antenna; rev_a's number is a model of a placeholder. This lane takes rev_a's own file over the generated comparison page, and the Replica has no antenna to compare at all.

> **On naming: n/a.** rev_a's board.py calls AE1 three things in three places - 'the meandered quarter-wave monopole' (l.820), 'the inverted-F drawn here' (l.86) and 'an inverted-L monopole' (l.324) - and spec/comparison.json calls it 'a rim inverted-F'. The owner's relayed description is a NINE-TOOTH MEANDER spanning R11.192-R12.200 with a 24.49100 mm conductor. A meandered monopole and an inverted-F are different topologies with different counterpoise requirements. NOT CORRECTED HERE - halo_rev_a is another live session's file and this lane only reads it. ROUTED to the orchestrator. What would settle it: the owner naming AE1 once, in one place, and the generated page regenerating from it.

### 7 · NFC coil

| | value | state | how it is known |
|---|---|---|---|
| **Apple AirTag A2187** | WOUND MAGNET WIRE at the board centre, ID 9.380 mm / OD 10.834 mm — i.e. radii 4.690 to 5.417 mm. Not a trace, not board copper, and it needs no tooling. | MEASURED (geometry) — but WHETHER IT IS THE NFC ANTENNA OR THE VOICE COIL IS OPEN (E02) | board/board.json not_on_this_board.nfc_coil; evidence/E02-THE-COIL-CORRECTION.md. |
| **halo_rev_a** | AE2 — a 2-turn coil ETCHED on the outer annulus of B.Cu at R10.043–R10.825, 0.2449 uH measured by ce-rf, tuned by C24/C25. Radially roughly TWICE as far out as Apple's central coil. | MEASURED (inductance) / REPORTED by the rev_a owner (radii, relayed 2026-09-05) | spec/comparison.json components row 16. The annulus between the cell can and the contact lands is 0.70 mm wide, which holds two turns and not five, so the coil is eight times smaller than Nordic's reference and the tuning capacitors eight times larger. |
| **halo_replica** | NOT DRAWN. Wire is not copper on a board. | REFUSED, correctly | board/board.json not_drawn.nfc_coil. |

*Against Apple:* **halo_rev_a DIVERGED** — etched 2-turn coil at R10.043-10.825 against Apple's wound wire at R4.690-5.417. **halo_replica SAME** — refused to draw wire as copper.

**Better on F: halo_replica.** Apple's central coil is wound wire and the Replica refuses to draw it as copper. rev_a's etched coil sits at R10.043–10.825 against Apple's R4.690–5.417 — a 2.1x radial difference nobody in this repo had stated until this row. THE FIRST NEW MEASURED DIFFERENCE THIS LANE PRODUCED.

> **On F-caveat: n/a.** E02 leaves OPEN whether the central wound coil is the NFC antenna at all. If it is the VOICE COIL, Apple's NFC antenna is the LDS coil on the carrier around the magnet well, and the 2.1x radial comparison above is comparing rev_a's NFC coil against Apple's SPEAKER. The number stands; its interpretation does not. Settling E02 settles this.

> **On function: halo_rev_a.** rev_a can be tapped by a phone. The Replica has no NFC antenna and no phone will ever read it.

### 14 · UWB transceiver

| | value | state | how it is known |
|---|---|---|---|
| **Apple AirTag A2187** | U2 — the Apple U1 (die TMKA75, TSMC 16 nm) in a USI SiP module, ~20.58 mm2 die, under a shield can. Apple's own FCC internal photo 6 labels the position 'UWB Module'. | TEARDOWN — never sold to anyone, at any price | spec/comparison.json components row 2. |
| **halo_rev_a** | NOT FITTED. J2 reserves eight SMD lands just inboard of the board edge as a stuffing option — a stub, not a DW3110 land pattern, because no sourced DW3110 pin table exists in this repo. | DECIDED (D1, D12), with the sourcing measured: DW3110 shows 30 in stock, DW3220 shows 9, DW1000/DW3210/DW3120/DWM3000 all show zero | spec/comparison.json components row 2. |
| **halo_replica** | UNPOPULATED, AND THE FOOTPRINT IS NOT DRAWN — for a DIFFERENT reason from the unpopulation. Its size is CANNOT DETERMINE: an independent remeasure of the can swings 6.735 -> 7.891 mm on the operator's padding alone. That U1 is unpopulated is printed ON THE BOARD in the legend. | CANNOT DETERMINE (size); DECIDED (unpopulated) | board/board.json not_drawn.U1_footprint and unpopulated.U1. |

*Against Apple:* **halo_rev_a MISSING** — no UWB radio; the part is not sold to anyone. **halo_replica MISSING** — U1 unpopulated and its footprint not drawn - size swings 6.735->7.891 mm on padding.

**Better on F: TIE AT ZERO.** Neither board has an ultra-wideband radio and no amount of replication will produce one. Apple's part is not sold; every buyable alternative is out of stock in the volumes GOAL.md names. THE WALL IS THE SAME FOR BOTH BOARDS AND IT DOES NOT MOVE.

*Would settle it:* nothing available from this machine. It is a supply fact, not a measurement gap.

> **On G: halo_rev_a.** rev_a replaces the function rather than the part: Bluetooth Channel Sounding on the nRF54L10 ranges tag-to-tag, which is the capability Leif actually asked for and which Apple's Precision Finding does not provide at any price. Section 3 of GOAL.md is answered by rev_a and untouched by the Replica.

---

## Components

### 8 · Component packages

| | value | state | how it is known |
|---|---|---|---|
| **Apple AirTag A2187** | WLCSP-50 SoC (3.0 x 3.2 mm, 90 nm), WLCSP-10 flash, metal-lid LGA accelerometer 2.0 x 2.0 x 0.95 mm, 0201 and 0402 passives, five large 100 uF bricks on the rim, K11-marked Schottky pairs. | PRIMARY for their existence; NO VALUES PUBLISHED for the passives | spec/comparison.json components rows 1, 4, 5, 13, 14 — Catley, iFixit, TechInsights, O'Flynn photographs. |
| **halo_rev_a** | 62 footprints, all real datasheet land patterns. 0201 dominant; the only 0402s are the four bulk capacitors on the bottom face, where the height allowance reaches 0.578 mm. Height check: 42 PASS, 4 FAIL, 16 CANNOT DETERMINE — verdict FAIL. | MEASURED | out/verify/dfm-jlc-4layer.json board_facts.footprints; electronics/halo_rev_a/out/height_check.json. |
| **halo_replica** | 34 rows drawn to MEASURED SIZE, 63 as POSITION ONLY. Every neutral-black IC package is ABSENT BY NAME — including the largest body on the board. | CANNOT DETERMINE for the dark packages, after three detector attempts, one of which returned an answer that was purely a function of the operator's chosen box (34% swing on padding alone) | board/board.json components.knowingly_incomplete; board/CLOSING.md section 4. |

*Against Apple:* **halo_rev_a EQUIVALENT** — same package classes for the same stated reason - height, not money. **halo_replica CANNOT DETERMINE** — the largest body on the board is absent by name; M08 CANNOT DETERMINE.

**Better on F: CANNOT DETERMINE.** THE REPLICA CANNOT CLAIM PACKAGE FIDELITY WHILE THE LARGEST BODY ON THE BOARD IS ABSENT BY NAME. rev_a's 62 footprints are real land patterns but chosen from its own parts, not read off Apple's. Neither side has the evidence to win and saying otherwise would be inventing a verdict.

*Would settle it:* the boundary-based detector CLOSING.md section 5 gap 2 specifies — line detection plus rectangle assembly with the same sweep-stability admission rule, on the 1.9x-resolution link-only source, with MIRROR-AWARE registration since that source is flipped and carries no scale.

> **On B: halo_rev_a.** a footprint you can place a part on beats a rectangle drawn from a photograph, and rev_a's height check FAILS on 4 rows with the rows named — a failure you can read is worth more than a drawing that cannot fail.

### 9 · The flash and its power rail

| | value | state | how it is known |
|---|---|---|---|
| **Apple AirTag A2187** | U3 — 32 Mbit (4 MB) SPI NOR, 1.8 V, WLCSP-10. GD25LE32D (iFixit) or GD25LQ32C/GD25LQ32DLIGR (O'Flynn) — TWO TEARDOWNS NAME DIFFERENT PART NUMBERS. Fed by U9, an UNIDENTIFIED SOT-23 regulator, and gated by U8, an onsemi FPF2487 load switch. | SILICON CITED, not SEEN. U9 stays UNVERIFIED. | spec/comparison.json components rows 4, 9, 10. |
| **halo_rev_a** | ALL THREE DELETED — flash, its LDO, and the load switch that gated it. Firmware lives in the nRF54L10's own 1.022 MB internal flash, MEASURED at 13,164 bytes used = 1.27 percent. | MEASURED (the 1.27 percent) / DECIDED (D18) | spec/comparison.json components row 4 halo text. Apple needed 4 MB off-die because the U1's own 'Rose' firmware stages there too; with no U1 an external NOR is a part, a bus and a power gate carrying nothing. |
| **halo_replica** | PRESENT IN bom/bom.json AS A RECONSTRUCTED LINE, ABSENT FROM THE BOARD. It is one of the neutral-black packages the detector could not separate. | CANNOT DETERMINE on the board | bom/bom.json is a reconstruction of APPLE's bill of materials for identification. It is not a purchasable BOM and it places nothing. |

*Against Apple:* **halo_rev_a DIVERGED** — flash, its LDO and its load switch all deleted (D18). **halo_replica CANNOT DETERMINE** — the package was never separated from the soldermask.

**Better on G: halo_rev_a.** THIS IS A DIVERGENCE THAT SURVIVES COMPARISON, and it is the same shape as the one D23 predicted. 1.27 percent of the SoC's own flash is used. Apple's 4 MB existed to stage a coprocessor's firmware for a coprocessor that cannot be bought. Deleting three parts, a bus and a rail to carry nothing is correct, and copying them would be copying a consequence of a part we do not have.

> **On F: TIE AT ZERO.** rev_a diverged deliberately; the Replica never located the package. Neither board has a flash, for two entirely different reasons, and only one of them wrote down why.

> **On evidence: n/a.** bom/bom.json states the rule that makes this row readable: 'the four that halo deleted (flash, amplifier, op-amp, load switch) are all CITED, which is not a coincidence and is not evidence.' The four parts halo could most easily delete are the four nobody has photographed well enough to see.

### 15 · The SoC

| | value | state | how it is known |
|---|---|---|---|
| **Apple AirTag A2187** | U1 — Nordic nRF52832-CIAA (nRF52832CIAAE), WLCSP-50, 90 nm, 3.0 x 3.2 mm. Marking N52832 CIAAE0 2102JK, READ OFF the photograph. | PRIMARY, SILICON SEEN, marking read | spec/comparison.json components row 1. |
| **halo_rev_a** | nRF54L10. Brings Bluetooth Channel Sounding — tag-to-tag ranging at 6-10 cm without a second radio — and costs 61 cents LESS than the nRF52832 it replaces. | DECIDED (D12), price measured against the LCSC catalogue | spec/comparison.json components row 1. |
| **halo_replica** | NOT DRAWN. The SoC is one of the neutral-black packages M08 could not separate — the single most important part on the board, and the Replica has no footprint for it. | CANNOT DETERMINE | board/CLOSING.md section 4 and section 5 gap 2. |

*Against Apple:* **halo_rev_a DIVERGED** — nRF54L10 for nRF52832, on a stated and priced reason (D12). **halo_replica CANNOT DETERMINE** — the processor has no footprint on this board.

**Better on F: halo_rev_a.** rev_a names a specific part and diverges from Apple's on a stated, priced reason. The Replica has no SoC on the board at all. A replica that cannot place the processor has not replicated the board — and it says so, which is why this row can be written honestly instead of being quietly absent.

*Would settle it:* the boundary-based dark-package detector in CLOSING.md section 5 gap 2. The packages are UNMISTAKABLE TO THE EYE by their straight boundaries; the gap is a METHOD gap, not a source gap, and a 1.9x-resolution source has already been tested and does not close it by luma or texture.

> **On G: halo_rev_a.** the divergence is what delivers GOAL.md section 3. Channel Sounding is peer ranging; nRF52832 has none.

---

## The audio path

### 10 · The audio path

| | value | state | how it is known |
|---|---|---|---|
| **Apple AirTag A2187** | U5 MAX98357A class-D digital amplifier (iFixit writes MAX98357B) plus U7 TI TLV9001IDPWR op-amp, driving the voice coil across TP1/TP38. | SILICON CITED — no marking is legible on either part in any photograph in images/airtag, and the two teardowns name different suffixes for the amplifier | spec/comparison.json components rows 6 and 8. |
| **halo_rev_a** | BOTH DELETED. Two SoC GPIO driven anti-phase into the bender through R9 (100 R series damping). 1.43 mA peak at 21 nF and 3.6 kHz, inside nRF54L high-drive. | COMPUTED from the load, with the load stated | spec/comparison.json components row 6 why: a bridge-tied class-D swings about 6 Vpp from a 3 V cell and two anti-phase GPIO swing the SAME 6 Vpp; what the amplifier bought was CURRENT, and a piezo bender is capacitive. |
| **halo_replica** | NEITHER PART DRAWN. Both are neutral-black packages in the CANNOT DETERMINE set. | CANNOT DETERMINE | board/board.json components.knowingly_incomplete. |

*Against Apple:* **halo_rev_a DIVERGED** — amplifier and op-amp deleted (D11a). **halo_replica CANNOT DETERMINE** — both are neutral-black packages in the CANNOT DETERMINE set.

**Better on G: halo_rev_a.** THE ROW D23 NAMED IN ADVANCE, and it survives. The amplifier bought current into an inductive voice coil; the load is now a 21 nF capacitor and the current is 1.43 mA peak, which two GPIO supply directly. An op-amp conditioning an analog node in a path that has no analog node is a part with no job.

> **On F: TIE AT ZERO.** neither board carries either part. rev_a deleted them with a numbered decision and an arithmetic argument; the Replica could not see them. Only one of those is a design.

### 11 · The speaker / sounder

| | value | state | how it is known |
|---|---|---|---|
| **Apple AirTag A2187** | A copper VOICE COIL glued to the plastic dome moving against a FIXED CENTRAL MAGNET — the whole housing is the diaphragm. NOT A PART ANYONE SELLS. | PRIMARY for the mechanism; and whether the wound coil visible at the board centre IS this voice coil rather than the NFC antenna is OPEN | spec/comparison.json components row 18; evidence/E02-THE-COIL-CORRECTION.md. |
| **halo_rev_a** | LS1 — a BARE 20.0 x 0.21 mm piezo bender BONDED TO THE INSIDE OF THE SHELL, driven anti-phase from two GPIO. Apple's IDEA kept — the housing is the radiating surface — with a catalogue part. | SOURCED | spec/comparison.json components row 18: a housed buzzer is 3.5 mm tall against the ~1.5 mm available. |
| **halo_replica** | NO CLAIM. The sounder is not a board part and this lane has not settled which coil is which. | CANNOT DETERMINE | evidence/E02 leaves NFC-vs-voice-coil OPEN. |

*Against Apple:* **halo_rev_a DIVERGED** — piezo bender for a voice-coil motor nobody sells. **halo_replica CANNOT DETERMINE** — E02 leaves open whether the measured coil is the motor at all.

**Better on B: halo_rev_a.** Apple's motor is not buyable at any price and a housed buzzer does not fit the height. A 0.21 mm bender does. rev_a keeps the mechanism that matters — the shell is the diaphragm — and drops the part that cannot be obtained.

> **On F: CANNOT DETERMINE.** the Replica cannot claim to have replicated Apple's motor while E02 leaves open whether the coil it measured is the motor at all.

---

## Power

### 12 · Battery and its contacts

| | value | state | how it is known |
|---|---|---|---|
| **Apple AirTag A2187** | CR2032 on THREE sprung contacts: one negative on the well floor, two positive tabs on the wall. BOTH positives must see 3 V to boot; the left one powers the electronics, the right one is sensed at about 50 nA. | PRIMARY | spec/comparison.json components row 19. |
| **halo_rev_a** | BT1 — CR2032 on THREE sprung C5191 fingers on rev_a's own three-pad land pattern (no bought holder exists under 2 mm). Pad 1 VDD at 12 o'clock, pads 2 and 3 at 4 and 8 o'clock. The third is VBAT_SNS_HI through a 4.7 M / 4.7 M divider — 319 nA at 3 V against Apple's ~50 nA. | MEASURED (the divider current is computed from stated resistors) | spec/comparison.json components row 19 halo text, graded SAME. |
| **halo_replica** | NOT DRAWN. The battery-contact face is Apple's BACK, and THE REPLICA HAS DRAWN ONLY THE COMPONENT SIDE. The 'large silver clip beside the centre hole' on the drawn face is a magenta absence marker, not a contact. | CANNOT DETERMINE — the face was never drawn | board/CLOSING.md title line: 'The side carrying the SoC and the shield can.' board/out contains board-front.png and compare-front.png and no back. |

*Against Apple:* **halo_rev_a SAME** — three contacts, two rails, one sensed - Apple's scheme. **halo_replica UNSTARTED** — the contacts are on Apple's BACK face and that face was never drawn.

**Better on F: halo_rev_a.** rev_a reproduces Apple's scheme exactly — three contacts, two positive rails, one sensed rather than loaded — and the prior comparison grades it SAME on this row. The Replica cannot be graded here at all because it never drew the face the contacts are on.

*Would settle it:* drawing Apple's BACK face. Every input exists — oflynn-frontside-fullres.jpeg is 2347x2344 and all five bulk capacitors, the contacts and the TP field are on it. THIS IS THE LARGEST SINGLE GAP IN THE REPLICA AND IT IS NOT A MEASUREMENT PROBLEM.

> **On power: Apple.** Apple senses at ~50 nA; rev_a's 4.7M/4.7M divider draws 319 nA — 6.4x more, continuously, from a cell whose whole budget this project argues about in microamps. Neither of our boards beats Apple on this number and the Replica does not have one.

### 16 · Bulk energy storage

| | value | state | how it is known |
|---|---|---|---|
| **Apple AirTag A2187** | C1-C5 — five 100 uF bricks = 500 uF, on the rim of the BACK face. Marking J107S read off the photograph; all five located and counted. NO PART NUMBER PUBLISHED. | PRIMARY for count and marking, none for the part | spec/comparison.json components row 13. |
| **halo_rev_a** | C9-C12 — four 10 uF 0402 = 40 uF. ONE TWELFTH of Apple's bulk. On the BOTTOM face over the cell where 0.578 mm is allowed; they clear by 0.028 mm. | MEASURED (the clearance) | spec/comparison.json components row 13: a 100 uF part is a brick and the top face inside 21.2 mm allows a 0.400 mm body, so Apple's rim capacitors do not physically fit under rev_a's diaphragm gap. |
| **halo_replica** | NOT DRAWN — all five are on Apple's BACK face, which the Replica has not drawn. | CANNOT DETERMINE — face not drawn | board/CLOSING.md, the component side only. |

*Against Apple:* **halo_rev_a DIVERGED** — 40 uF against 500 uF - one twelfth. **halo_replica UNSTARTED** — all five are on Apple's BACK face, never drawn.

**Better on F: halo_rev_a.** rev_a is at one twelfth of Apple's bulk, which is a large and honestly-recorded miss. The Replica has no number at all. A 12x miss you can read beats an absence you cannot.

*Would settle it:* drawing Apple's BACK face — the same gap as row 12, and the same inputs already exist.

> **On function: CANNOT DETERMINE.** whether 40 uF is enough is not a fidelity question, it is a hold-up question, and nobody has measured it. WOULD SETTLE IT: a brown-out test across battery removal on real hardware, which is a bench measurement neither board has had.

---

## Interfaces

### 13 · Connectors and off-board joints

| | value | state | how it is known |
|---|---|---|---|
| **Apple AirTag A2187** | NONE, ANYWHERE. Every off-board connection is a spring contact or a soldered tab: 3 battery contacts, 6 antenna solder joints ('4x at upper center and 2x bottom left-of-center'), 2 voice-coil joints. | PRIMARY — O'Flynn's tear-off joint count | spec/comparison.json pcb row 6. |
| **halo_rev_a** | NONE either. Three sprung battery fingers, two piezo wire lands, and ZERO antenna joints because the antennas are etched in the board — six fewer joints than Apple. | MEASURED off the schematic's connector-less contract | spec/comparison.json pcb row 6, graded SAME. |
| **halo_replica** | NO CONNECTORS DRAWN — and it CANNOT STATE THE JOINT COUNT, because the rim pad count is CANNOT DETERMINE and CLOSED. At photo 6's signal-to-noise those pads could not have been seen. | CANNOT DETERMINE, closed | board/board.json not_drawn.rim_pads; the closure came from a noise-matched positive control in which the same detector finds ZERO of six pads that are certainly there. |

*Against Apple:* **halo_rev_a SAME** — no connectors, and six fewer solder joints than Apple. **halo_replica CANNOT DETERMINE** — rim pad count CANNOT DETERMINE and closed - no joint count to be right about.

**Better on F: halo_rev_a.** Apple's principle is 'not a connector on the product' and rev_a matches it exactly and measurably. The Replica also has no connectors, but it cannot say how many joints Apple has or where — the count is closed as unmeasurable — so it has nothing to be right about.

*Would settle it:* a source that images the rim at higher SNR than FCC photo 6. E06 established that re-rendering the existing exhibit at higher dpi produces more candidates from no new evidence and must not be done.

> **On reliability: halo_rev_a.** six fewer solder joints, and the six it removed are the ones Catley reports tearing: 'Removing the PCB is likely to cause damage due to the thin PCB and being soldered to the plastic tray.' A divergence from Apple that is straightforwardly better.

### 17 · Debug access and test points

| | value | state | how it is known |
|---|---|---|---|
| **Apple AirTag A2187** | About 38 numbered pads on the BACK face, reachable after popping the cover. SWD fully exposed on TP30/TP35/TP36 with SWO on TP31; the SPI flash fully exposed on TP19-TP24; APPROTECT enabled but DEFEATED by a voltage glitch on TP28. UNDOCUMENTED BY APPLE - the numbering is Colin O'Flynn's. *** MEASURED BY THIS LANE 2026-09-05: 43 circular gold pads located on that face, MEDIAN DIAMETER 0.5985 mm, interquartile range 0.034 mm = 5.7% of the median. *** | PRIMARY for the pinout; the pad GEOMETRY is now MEASURED | spec/comparison.json components row 20 and pcb row 8 for the pinout. The pad diameter is metrology/backface-pads.json - k_backface pads at 69.557 px/mm, gold colour AND circular shape, 55 gold components rejected on shape. Negative control: 0 pads found off the board. Positive control: Colin O'Flynn's 2021 annotation, an EXTERNAL reference made with no knowledge of this detector - his label positions sit a median 0.462 mm from a detection against 1.973 mm for 4000 random points on the same annulus, a 4.27x separation against a 2.00x floor. |
| **halo_rev_a** | J1 — a Tag-Connect TC2030 SWD footprint with a PUBLISHED PINOUT, plus 11 named test points with a stated reason each, including SEPARATE FORCE AND SENSE pads on VDD and GND, and two ASYMMETRIC fiducials so a round board has a datum at all. | MEASURED off the schematic's TESTPOINTS table | spec/comparison.json pcb row 8. The force/sense pairs matter because sleep current here is single-digit microamps and a two-wire measurement puts the probe's contact resistance in series with the thing being measured. |
| **halo_replica** | The TP FIELD IS NOT DRAWN - it is on Apple's BACK face. But that face is no longer unmeasured: it has a validated scale (69.557 px/mm, held out at 0.1256 mm) and 43 of its pads are located at a measured 0.598 mm diameter. The gap is now DRAWING work, not metrology work. | NOT DRAWN - but the face is measured and the inputs exist | board/CLOSING.md; metrology/backface-pads.json; evidence/E08. |

*Against Apple:* **halo_rev_a DIVERGED** — 11 named TPs + TC2030 with a published pinout against ~38 undocumented pads. **halo_replica UNSTARTED** — the TP field is on Apple's BACK face, not drawn - but the face now has a validated scale and 43 located pads, so this is unfinished drawing rather than unfinished measurement.

**Better on G: halo_rev_a.** Apple's debug surface is a documented glitch target and Apple documents none of it. rev_a publishes a pinout, which is the stated differentiator against certified tags from eufy and Motorola that ship debug pads undocumented. For an OPEN product, documented beats hidden.

> **On F: CANNOT DETERMINE.** the Replica has not drawn the face, so it cannot be scored. The pad count is knowable — oflynn-frontside-tpnames.jpg carries all 38 already annotated — which makes this an unstarted job rather than a measurement limit.

> **On F: n/a.** APPLE'S TEST-PAD DIAMETER IS NOW A NUMBER: 0.598 mm median over 43 pads, spread 5.7%. Nothing in this repo had it. halo_rev_a's 11 named test points have no published pad diameter in any file this lane read, so the two still cannot be compared on pad geometry - but the Apple side of that row is no longer empty, and it was empty this morning.

### 20 · Board identity marking

| | value | state | how it is known |
|---|---|---|---|
| **Apple AirTag A2187** | Silkscreen 820-01736-A on the component side plus data code '2920 17' (week 29, 2020, batch 17); 920-08283-01 with data code 3119 on the FCC sample. White legend on a dark mask. TWO DIFFERENT BOARDS, never merged. | OBSERVED | stackup.json apple.board_part_numbers. |
| **halo_rev_a** | M1 — a DataMatrix serial mark on the probed face. Graded EQUIVALENT: both carry a board identity and a per-unit trace, Apple's human-readable, rev_a's machine-readable. | MEASURED off the footprint list | spec/comparison.json pcb row 9. |
| **halo_replica** | A legend stating U1 IS UNPOPULATED, printed on the board rather than only in a document. | DRAWN | board/board.json unpopulated.U1. |

*Against Apple:* **halo_rev_a EQUIVALENT** — DataMatrix against human-readable silkscreen - same purpose. **halo_replica DIVERGED** — prints U1 IS UNPOPULATED; prints neither 820-01736-A nor a data code.

**Better on G: halo_replica.** Putting 'U1 IS UNPOPULATED' on the copper rather than only in a file is the one place the Replica applies this project's own standard to a physical artifact: a fact a person can find without reading the repository. rev_a's DataMatrix is the better production mark; the Replica's legend is the better honesty mark, and they are not competing.

---

## Cost and manufacture

### 21 · Cost at 10 / 100 / 1000 / 10000

| | value | state | how it is known |
|---|---|---|---|
| **Apple AirTag A2187** | $29 retail. BOM NEVER PUBLISHED. NINE of the eighteen bill-of-materials lines have no manufacturer part number in the public record at all. | PRIMARY for retail; the BOM cost is CANNOT DETERMINE and always was | out/comparison/comparison-summary.json unidentified = 9, pct_orderable = 33.3. |
| **halo_rev_a** | $6.146 / $4.144 / $3.579 / $3.490 parts per board at 10 / 100 / 1000 / 10000, plus $66 of extended-part feeder fees (22 unique extended parts x $3). PASS at 10 and 100; FAIL at 1000 (1 failed line) and FAIL at 10000 (6 failed lines) — on STOCK, not on price. | MEASURED against a 684,956-row LCSC catalogue snapshot dated 2026-09-03 | out/verify/bom-cost-live-2026-09-05.json. |
| **halo_replica** | NO COST EXISTS AND NONE CAN. bom/bom.json is a reconstruction of APPLE's bill of materials for IDENTIFICATION — it prices nothing, sources nothing and places nothing. The board as drawn is not orderable at 0.30 mm four-layer from either house. | CANNOT DETERMINE, structurally | bom/bom.json document line; stackup.json fabrication_delta.the_delta_in_one_line. |

*Against Apple:* **halo_rev_a CANNOT DETERMINE** — Apple's BOM cost is unknowable - 9 of 18 lines have no part number. **halo_replica CANNOT DETERMINE** — same wall, and no cost of its own either.

**Better on B: halo_rev_a.** AND IT IS NOT CLOSE. rev_a is priced at four quantities against a dated catalogue and FAILS HONESTLY at two of them, naming the failing lines. The Replica has no price, no sourced part and no orderable board. GOAL.md's first stated constraint is 'Cost is a first-class spec: BOM at 10 / 100 / 1 000 / 10 000, vs $29 retail'. rev_a answers it; the Replica does not and was never built to.

> **On F: n/a.** Apple's BOM cost is unknowable from here — nine of eighteen lines have no part number — so no fidelity comparison on cost is possible for EITHER board. The $29 is a retail price, not a bill of materials, and must never be differenced against $6.146.

### 22 · Manufacturability of the bare board

| | value | state | how it is known |
|---|---|---|---|
| **Apple AirTag A2187** | Built at volume by suppliers no prototype capability page describes. A 0.30 mm four-layer board with a 50-ball WLCSP and a routed centre pocket. | OUT OF SCOPE for capability comparison, deliberately — a prototype house's floor bounds what WE can order, never what Apple built | stackup.json fabrication_delta._and_what_it_does_not_mean. |
| **halo_rev_a** | ORDERABLE. 0.60 mm four-layer is PCBWay's normal thickness and a stock JLCPCB option. DRC: 0 errors, 3 warnings (all track_dangling). 28 unconnected items after routing, down from 83 before — 55 closed, verdict PASS on all 9 routed-check rows. | MEASURED | out/verify/routed-check.json drc_after; electronics/halo_rev_a/out/halo_rev_a-routed.drc.json. |
| **halo_replica** | NOT ORDERABLE AT ANY HOUSE READ. 0.30 mm is below PCBWay's 0.40 mm four-layer floor and below JLCPCB's 0.40 mm overall minimum at ANY layer count. Building one requires an HDI house whose capability page was not read, or a stated departure to 0.40 mm (+33.3%), PROPOSED and NOT ADOPTED. | MEASURED against published capability pages. No account, no quote, nobody contacted, no money spent. | stackup.json fabrication_delta. |

*Against Apple:* **halo_rev_a DIVERGED** — 0.60 mm is orderable; Apple's build is out of scope for a capability page. **halo_replica SAME** — 0.30 mm as-drawn, and unbuildable BECAUSE it is faithful.

**Better on B: halo_rev_a.** One of these two boards can be ordered today and the other cannot be ordered at all. That is the whole row.

> **On F: halo_replica.** and this is the row that shows why fidelity and buildability genuinely conflict rather than merely differing: the Replica is unbuildable BECAUSE it is faithful. 0.30 mm is exactly the number that puts it under both floors.

---

## What the artifacts are

### 23 · Design integrity — can the artifact be checked at all

| | value | state | how it is known |
|---|---|---|---|
| **Apple AirTag A2187** | n/a. A shipped product needs no DRC from us. | n/a | — |
| **halo_rev_a** | CHECKABLE, AND CHECKED, AND IT FAILS IN PLACES. DRC 0 errors / 3 warnings. 81 unconnected items in the unrouted board (out/drc.json) and 28 in the routed one (halo_rev_a-routed.drc.json) — TWO DIFFERENT BOARDS, and this lane quotes both with their files rather than picking one. Height check verdict FAIL: 42 PASS, 4 FAIL, 16 CANNOT DETERMINE. Keep-out check verdict CANNOT DETERMINE, 0 hits. | MEASURED | electronics/halo_rev_a/out/*.json. |
| **halo_replica** | NOT CHECKABLE, AND NEVER WILL BE. No netlist, no nets, no copper, no DRC, and no path to any of them, because nothing in it was ever a schematic. It has its own controls — the fit residuals, the enrichment test, the break flags — and they are good ones, but they check a DRAWING against a PHOTOGRAPH, not a design against a rule set. | STRUCTURAL, not a gap to be closed | board/CLOSING.md section 3: 'copper, traces, vias — not measured'. |

*Against Apple:* **halo_rev_a n/a** — not a fidelity axis - it is about what our artifacts are. **halo_replica n/a** — not a fidelity axis.

**Better on B: halo_rev_a.** THIS ROW IS THE ASYMMETRY THE WHOLE FILE RESTS ON. The two artifacts are not the same kind of thing. rev_a is a design that can be wrong and is measured to be wrong in four height rows; the Replica is a drawing that cannot be wrong in that sense at all. Every fidelity win above should be read against this row.

> **On method: halo_replica.** the Replica's controls are stronger than rev_a's on the axis it does measure. Nine of its own defects were found by controls rather than by inspection, every break flag has been watched going red, and it publishes a per-degree map of where it disagrees with its own reference. rev_a has nothing equivalent for the question 'how close is this to the AirTag'.

### 24 · Coverage — how much of Apple's board each object accounts for

| | value | state | how it is known |
|---|---|---|---|
| **Apple AirTag A2187** | TWO populated faces. Front: every IC, both crystals, the UWB module, the shield can. Back: battery contacts, voice-coil pads, magnet well, the coil, five 100 uF caps, ~38 test points. | PRIMARY | spec/comparison.json pcb row 5. |
| **halo_rev_a** | TWO populated faces, 62 footprints, 49 vias, 255 track segments, 33 nets. Every function of Apple's board is either present, deliberately deleted with a numbered decision, or recorded as MISSING — 22 component rows and 12 PCB rows, none blank. | MEASURED | out/verify/dfm-jlc-4layer.json board_facts; spec/comparison.json. |
| **halo_replica** | ONE FACE. 34 components at measured size, 63 at position only, every dark IC absent by name, no copper, no back face. The prior comparison's 12 PCB axes: the Replica addresses 6 and cannot address 6. | MEASURED where drawn; the back face is UNSTARTED, not unmeasurable | board/CLOSING.md sections 2 and 4. |

*Against Apple:* **halo_rev_a SAME** — two populated faces, 34 graded rows, nothing blank. **halo_replica UNSTARTED** — one face of two.

**Better on F: halo_rev_a.** COVERAGE IS PART OF FIDELITY AND THE REPLICA HAS HALF A BOARD. rev_a accounts for every function of Apple's board across 34 graded rows with nothing blank; the Replica accounts for one face with its most important parts absent by name. A faithful drawing of half the object is not a more faithful object.

*Would settle it:* the back face, from oflynn-frontside-fullres.jpeg (2347x2344) which already carries the contacts, the coil, the five bulk capacitors and all 38 annotated test points. THIS IS THE SINGLE HIGHEST-VALUE JOB IN THE REPLICA AND IT IS NOT BLOCKED ON ANYTHING.

### 25 · Design-rule violations, and whose they are

| | value | state | how it is known |
|---|---|---|---|
| **Apple AirTag A2187** | NO DRC EXISTS AND NONE CAN. Apple's board ships; nobody outside Apple has its rule set, its stackup tolerances or its fabricator's capability. The only thing this lane can say is that the board was manufactured, so by construction it passed whatever rules Apple applied. | n/a - not a measurable axis on Apple's side | The bound that makes this row necessary is Apple's OD, which is 24.95-26.34 mm and not a number (board/board.json). Every copper-to-edge rule the Replica fires is a rule against an edge whose position is not known. |
| **halo_rev_a** | 0 errors, 3 warnings (all track_dangling), 28 unconnected items on the routed board. A CLEAN RULE SET AND AN INCOMPLETE ROUTE - the opposite failure to the Replica's. | MEASURED | electronics/halo_rev_a/out/halo_rev_a-routed.drc.json, dated 2026-09-05T08:15:46. Note its gerbers predate it by 7,742 s and were cut from a board with those 28 unconnected nets - see the deliverable section. |
| **halo_replica** | 0 unconnected and a live, moving error count - the route is COMPLETE and the rules are not satisfied. THE EXACT INVERSE OF rev_a. The count is read live by k_threeway rather than frozen here, because it has moved 42 -> 58 -> 33 in under two hours while the board lane iterates, and an anchored number that churns is an anchor that cries wolf. | MEASURED, live | pcb/out/halo_replica.drc.json, read at render time; the split by class is in the deliverable section of this page. The CLASSES are stable and anchored here even though the counts are not. |

*Against Apple:* **halo_rev_a n/a** — not a fidelity axis - Apple has no DRC to be faithful to. **halo_replica n/a** — same.

**Better on F: CANNOT DETERMINE.** Apple has no DRC to compare against, so no fidelity verdict is available on this axis at all. What the row DOES carry is the split - how much of the Replica's unbuildability belongs to Apple's unknown edge, to the photographs' resolution, and to us - and that split is a fidelity reading even though the gate that produces it is a buildability gate. THE TWO QUESTIONS ARE KEPT IN SEPARATE INSTRUMENTS ON PURPOSE: the deliverable gate answers 'can it be cut' and blocks on every class but one; this row answers 'whose fault is it' and blocks nothing.

*Would settle it:* nothing available. Apple's rule set is not public and its board is already made.

> **On buildability: halo_rev_a.** a board with 0 rule errors and 28 unrouted nets is nearer to fabricable than one with a complete route and 33 rule errors: finishing a route is ordinary work, while 19 of the Replica's 33 are copper-to-OUTLINE against an edge whose position is a bound. rev_a's remaining work is known; the Replica's is partly unknowable.

> **On THE SIGNED EXPECTATION: n/a.** AND THIS IS THE PART THAT MUST NOT BE MISREAD. M02 sec.8 records that IF THE OD BOUND MOVES, IT MOVES DOWN. So the Replica's 19 copper-to-edge violations get WORSE, not better, as the outer diameter resolves toward the 24.95 mm floor. Classifying them BOUND-LIMITED records WHOSE PROBLEM THEY ARE. It must never be read as expecting them to go away - they cannot be waited out, and the expectation runs against us.

---

## How to reproduce

```bash
cd ce-designs/halo/electronics/halo_replica
python3 tools/k_threeway.py check -v      # every anchor, with its file and value
python3 tools/k_threeway.py selftest      # 9 deliberate breaks, each watched going red
python3 tools/k_threeway.py render        # regenerate this page
```

`check` exits 0 PASS / 1 FAIL / 2 CANNOT DETERMINE. It verifies that this page agrees with the files it cites; it cannot verify that those files are right, and says so in its own docstring.
