Leif-Rydenfalk/halo/electronics/halo_replica/trash/leifsays.md

# LEIF SAYS — the halo Replica lane
# VERBATIM ONLY. This file outranks the lane brief, PROTOCOLS, and every summary.
# Anything not in quotes here is dated attribution, nothing else.

## 2026-09-05 — the instruction that created this lane
> "our current version doesnt look visually similar at all. not even close. put a claude
> terminal instance window on orchestrating workflows to make an actual perfect replica of
> every components and painstakinlgy reverse engineering it exactly with the exact pcb
> design and all the components. there shouild be different versions of it and this is one
> of them."

## Earlier, recorded in DECISIONS.md D23
> "so create many different versions including one which is a perfect recreation."

> "first step is recreating it exactly."

## 2026-09-05 — on tools (relayed to this lane by the halo lane, session halo-cb)
> "Tell halo replica orchestration to always manage its own tools and create any tools
> that might be missing."

Relay path: Leif -> halo-cb -> this lane, 2026-09-05, received before any tool work was
committed. Recorded verbatim as relayed; the wording is Leif's, the framing sentence
around it is not and is therefore not quoted.

## 2026-09-05 — supervision (relayed to this lane by the halo lane, session halo-cb)
> "tell it to tell the agents its supervising"

Context of the relay: it applies to the tools instruction immediately above. Every lane
this session supervises manages its own tools and builds what is missing, and every brief
written from here on carries that rule. Relay path: Leif -> halo-cb -> this lane.

---
Further words of Leif's go here verbatim, dated, BEFORE they are acted on.
