Leif-Rydenfalk/halo/electronics/halo_replica/board/stackup/FINDING-pack-status-is-asserted.md

# FINDING — every release-pack status is hand-authored, and item 5 is READY without its artifact

*halo Replica lane L4, 2026-09-05. A finding about the **release pack**, raised
from this lane because it owns fabrication and cannot write into `out/release/`
or `tools/`. Instrument: `../../tools/s_packstatus.py`.*

## 1. No status in the pack is computed

`spec/release-pack.json` gives each of the eleven artifacts a `status`, a
`reason`, an `evidence` line and — for ten of the eleven — **the `command` that
would prove it**.

`tools/gen_release_pack.py` **never runs any of them.** Its only `subprocess`
call is `git rev-parse --short HEAD`; every other use of `status` is counting
them, sorting by them, and rendering a badge. So all eleven are **hand-authored
literals**, against the workshop's own standing rule — *"`trust.json` is
COMPUTED here, never hand-authored"* — and against MISSION.md's requirement
that every item be *generated by a tool on this machine and graded PASS, never
asserted*.

## 2. Being hand-authored is not the same as being wrong — measured

I ran the recorded commands for every item that has a cheap one:

| item | asserted | its own command | verdict |
|---|---|---|---|
| 1 Gerbers, drill, netlist | PARTIAL | `check_fabset` → exit 1 | consistent |
| 3 BOM | **READY** | `check_bom_identity` → **exit 0**, 138 assertions, 0 fail | **agrees** |
| 4 Pick-and-place | **READY** | `check_cpl_rotations` → **exit 0**, 40/40 | **agrees** |
| 9 Test plan | PARTIAL | `gen_test_plan --selftest` → exit 0 | conservative |
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
