Leif-Rydenfalk/halo/electronics/halo_replica/metrology/compside/R00-DATUM-TRANSFER.md

> **⚠ HOLD-OUT SUPERSEDED (L2, 2026-09-05, later the same day) — see
> [R08](R08-THE-HOLDOUT-WAS-OPTIMISTIC.md).** The "0.103 mm, worst of four folds" headline
> below is an **INTERPOLATION** error: with four 90° folds, three quarters of the board
> still surround every held-out sector, so the fit never extrapolates. Holding out a
> **half** gives **0.1298 mm RMS / 0.2266 mm p95** on this FRONT pair. Quote **0.130 mm**
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
