Leif-Rydenfalk/halo/electronics/halo_replica/board/out/.compare-ours.png

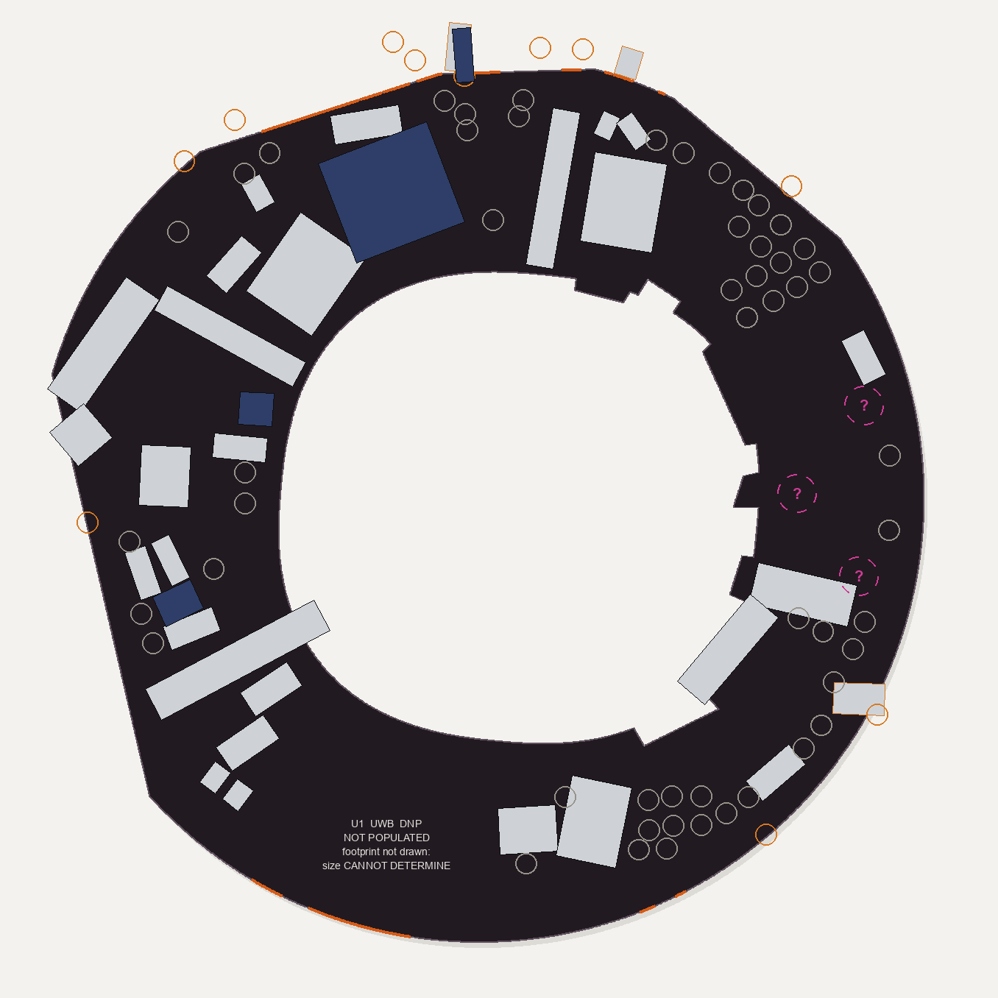
electronics/halo_replica/board/out/.compare-ours.png
