Leif-Rydenfalk/halo/electronics/halo_replica/board/out/board-front.png

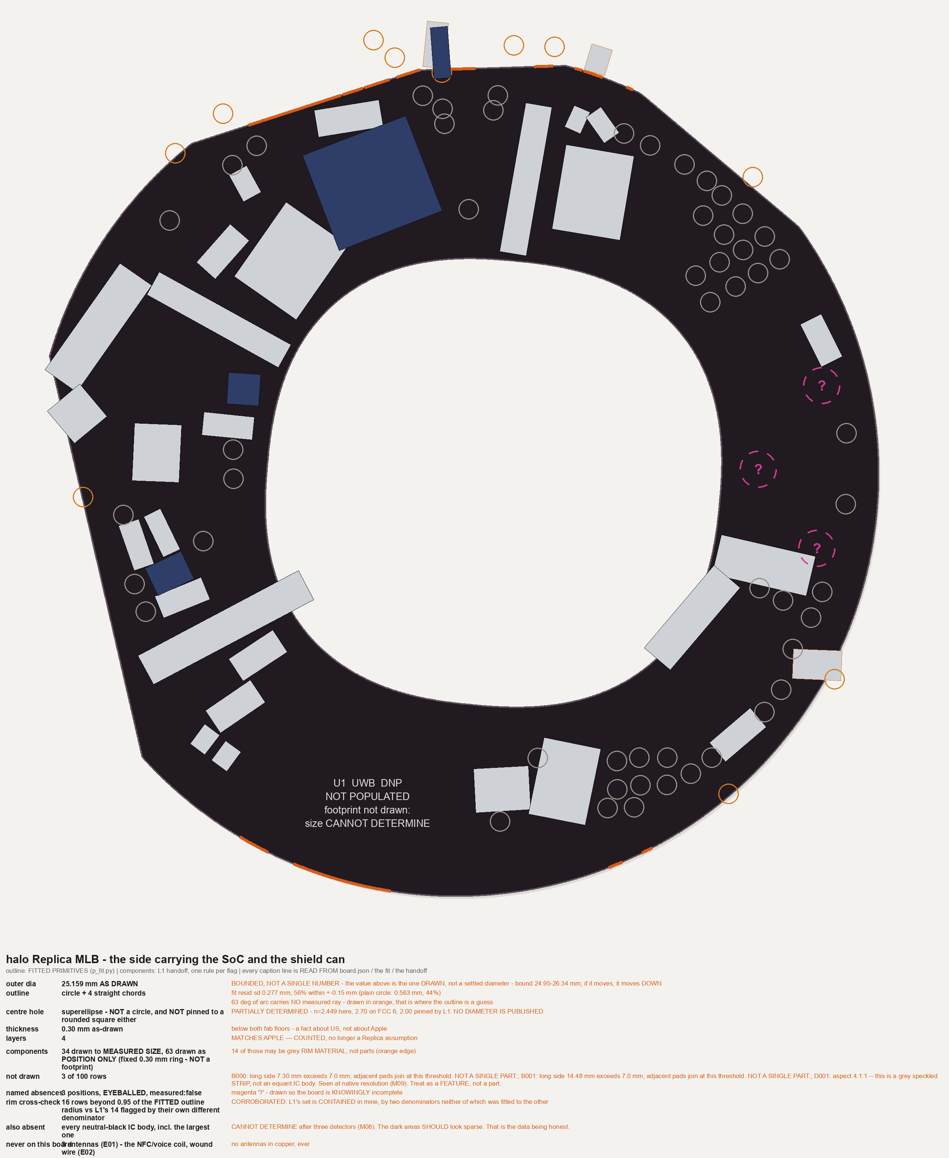
electronics/halo_replica/board/out/board-front.png
