Leif-Rydenfalk/halo/electronics/halo_replica/board/out/compare-front.png

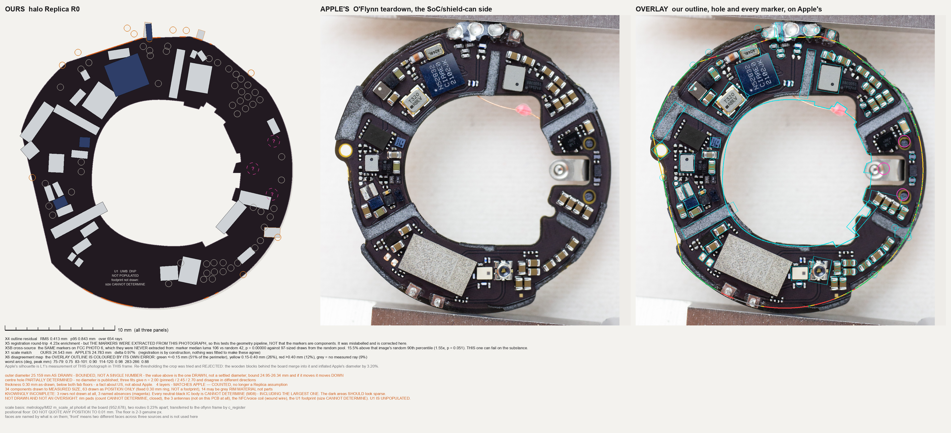
electronics/halo_replica/board/out/compare-front.png
