Leif-Rydenfalk/halo/electronics/halo_replica/evidence/E-L1-everything-on-the-photograph.png

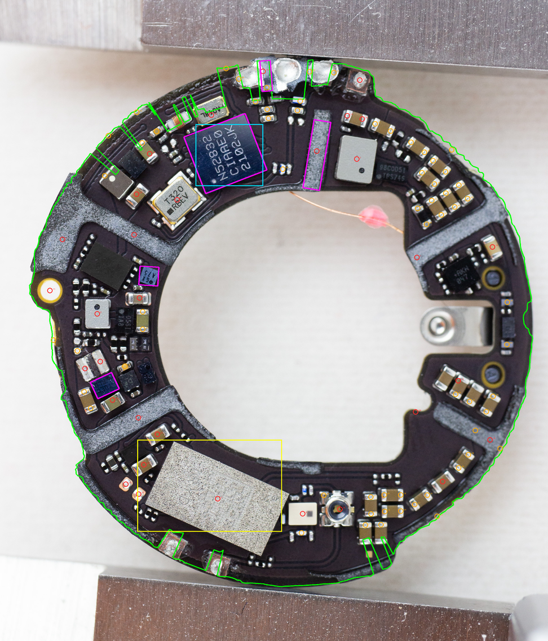
electronics/halo_replica/evidence/E-L1-everything-on-the-photograph.png
