Leif-Rydenfalk/halo/electronics/halo_replica/fab/out/render-bottom.png

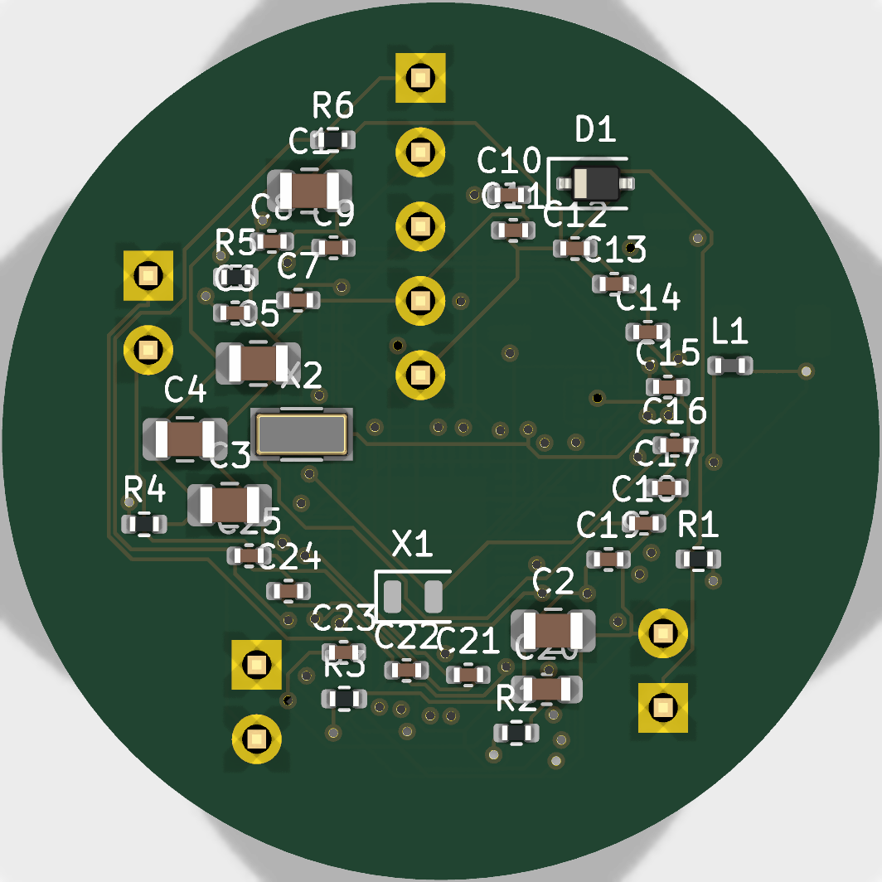
electronics/halo_replica/fab/out/render-bottom.png
