Leif-Rydenfalk/halo/electronics/halo_replica/fab/out/render-top.png

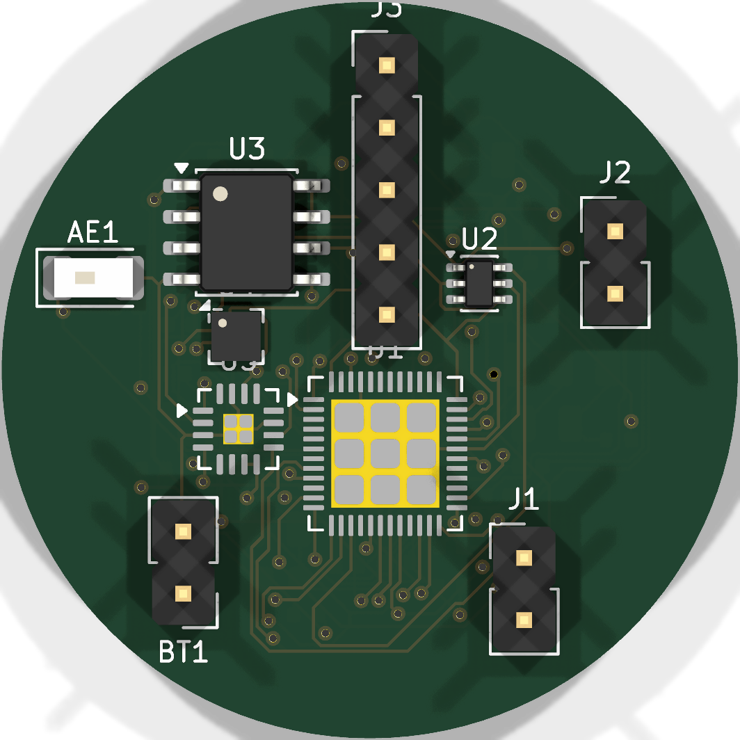
electronics/halo_replica/fab/out/render-top.png
