Leif-Rydenfalk/halo/electronics/halo_replica/metrology/compside/img/R16-edge-profiles-gated.png

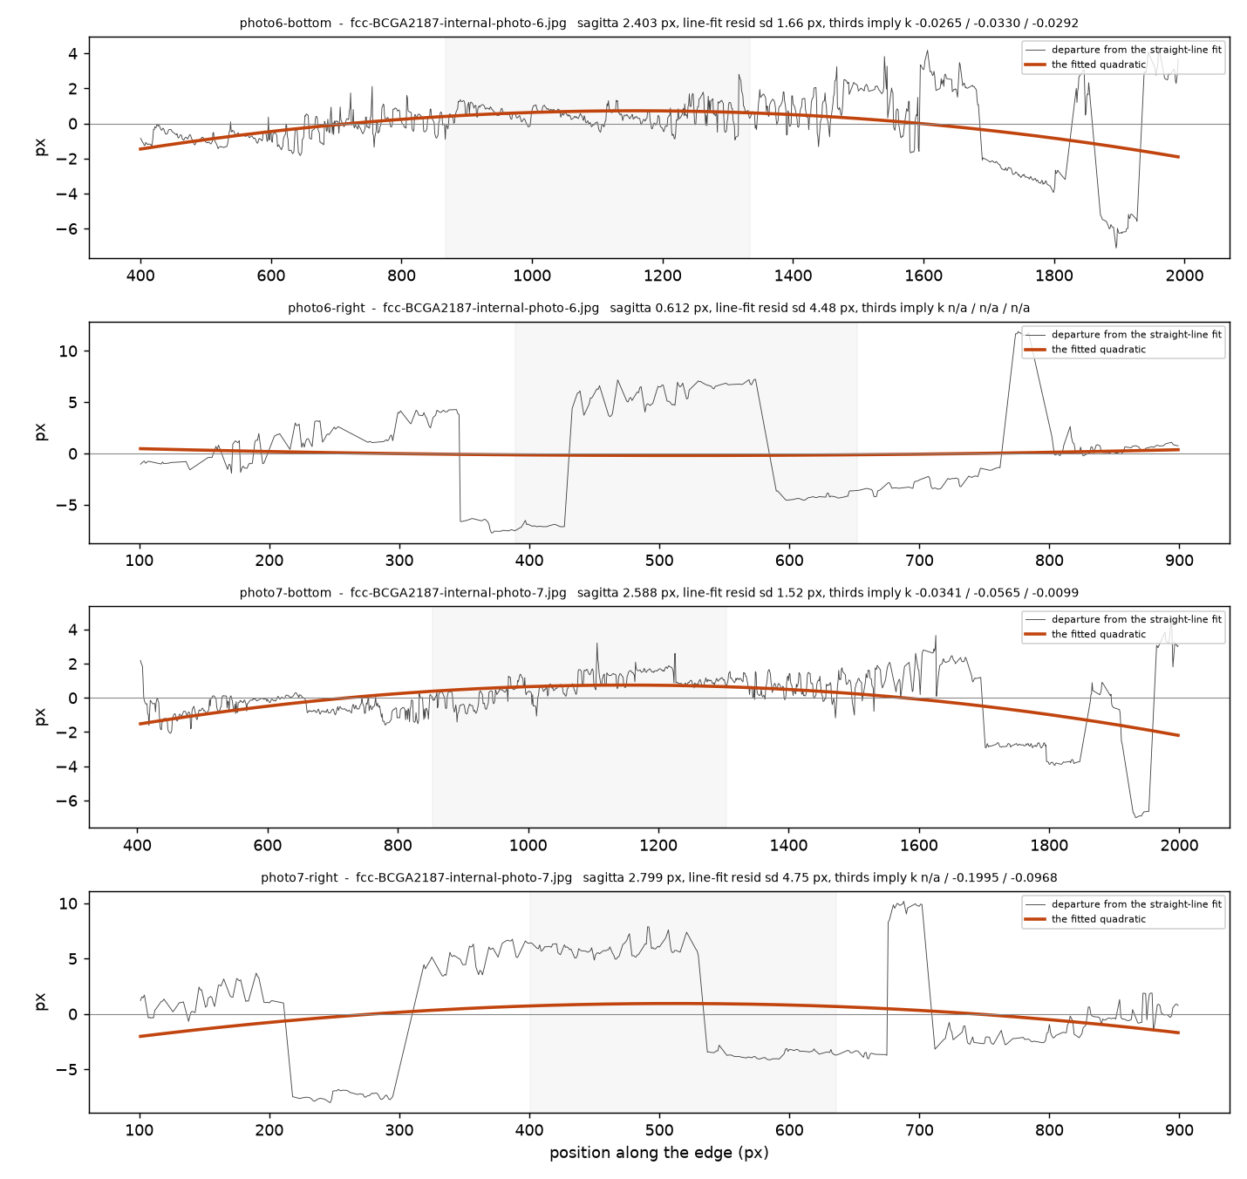
electronics/halo_replica/metrology/compside/img/R16-edge-profiles-gated.png
