Leif-Rydenfalk/halo/electronics/halo_replica/metrology/compside/img/R16-edge-profiles.png

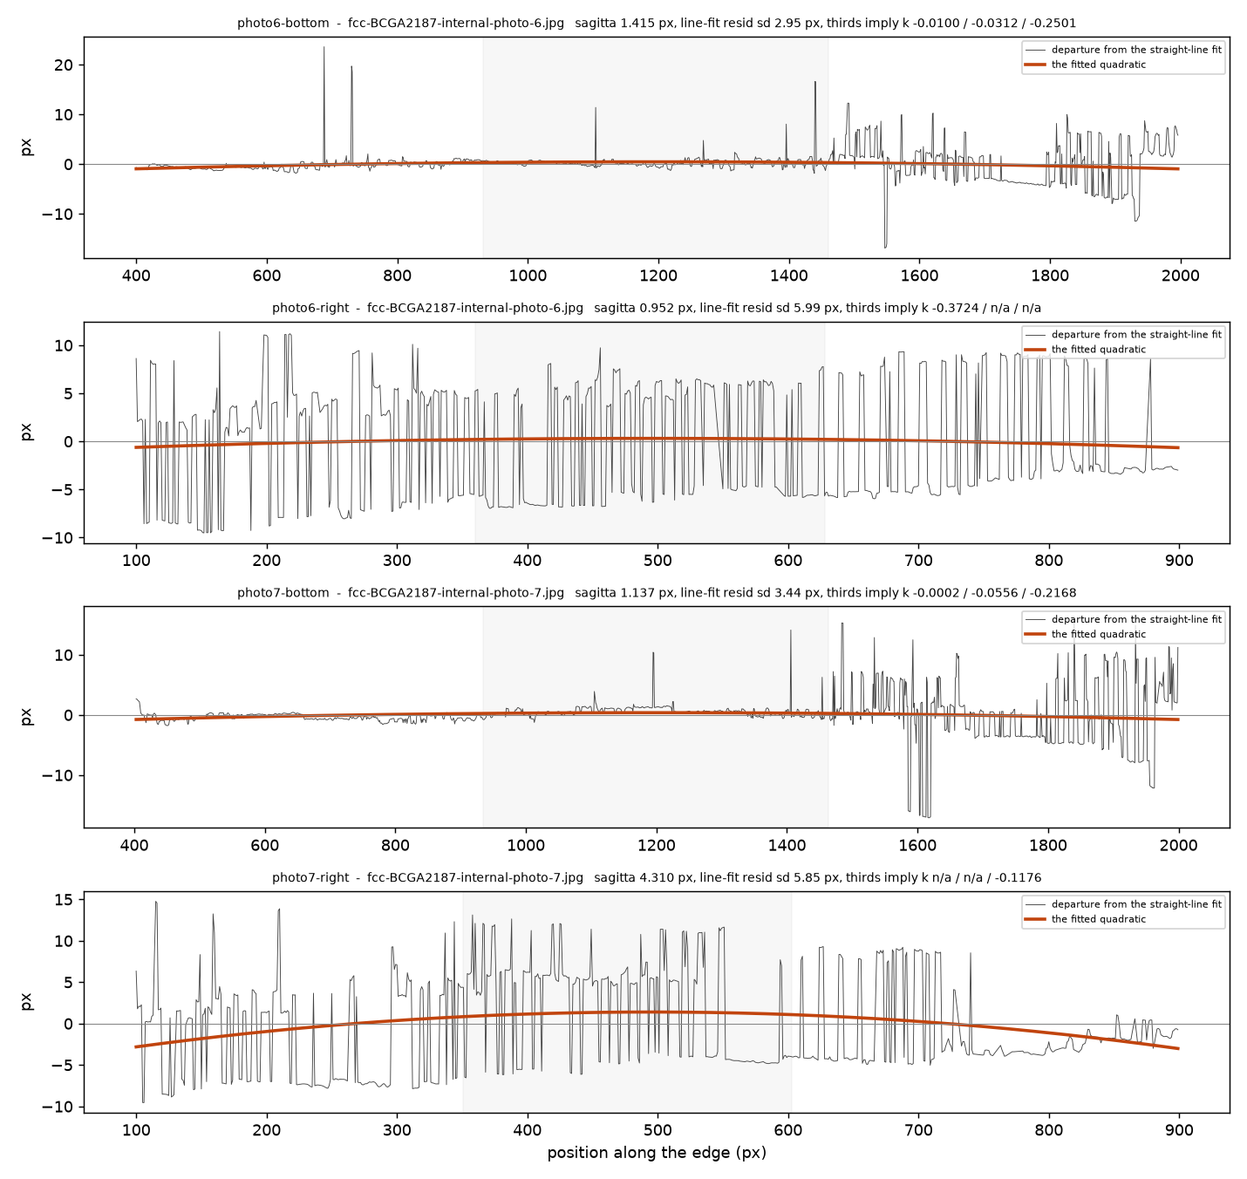
electronics/halo_replica/metrology/compside/img/R16-edge-profiles.png
