Leif-Rydenfalk/halo/electronics/halo_replica/metrology/rimcount/out/detections-tiles.png

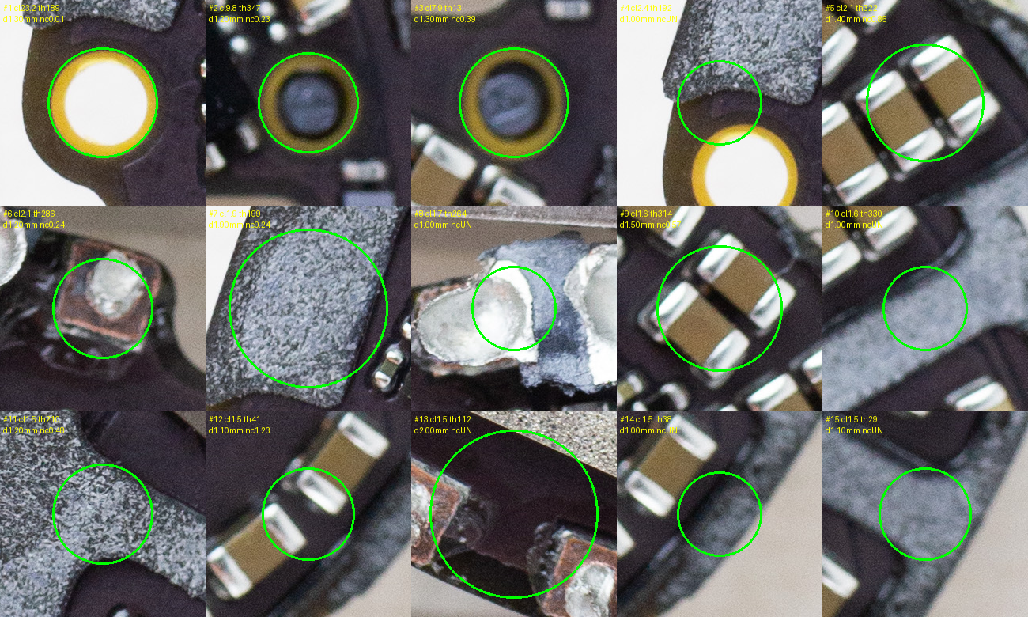
electronics/halo_replica/metrology/rimcount/out/detections-tiles.png
