Leif-Rydenfalk/halo/electronics/halo_replica/metrology/rimcount/out/sites-tiles.png

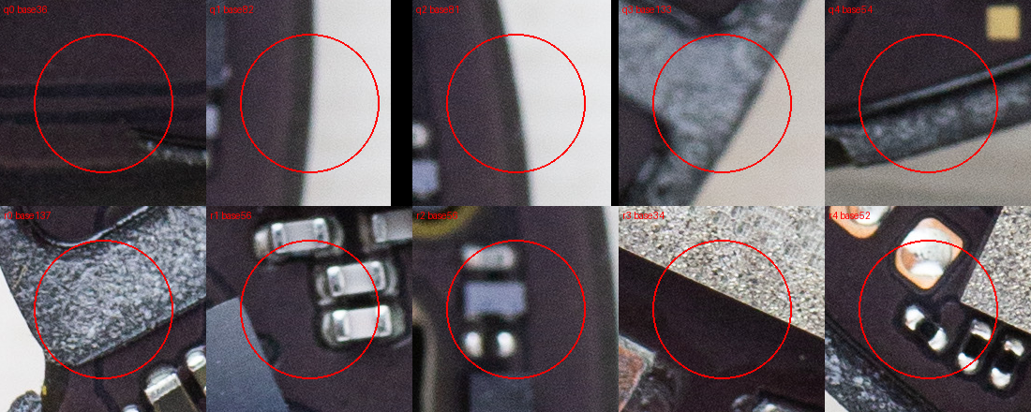
electronics/halo_replica/metrology/rimcount/out/sites-tiles.png
