Leif-Rydenfalk/halo/electronics/halo_replica/pcb/out/compare-real.png

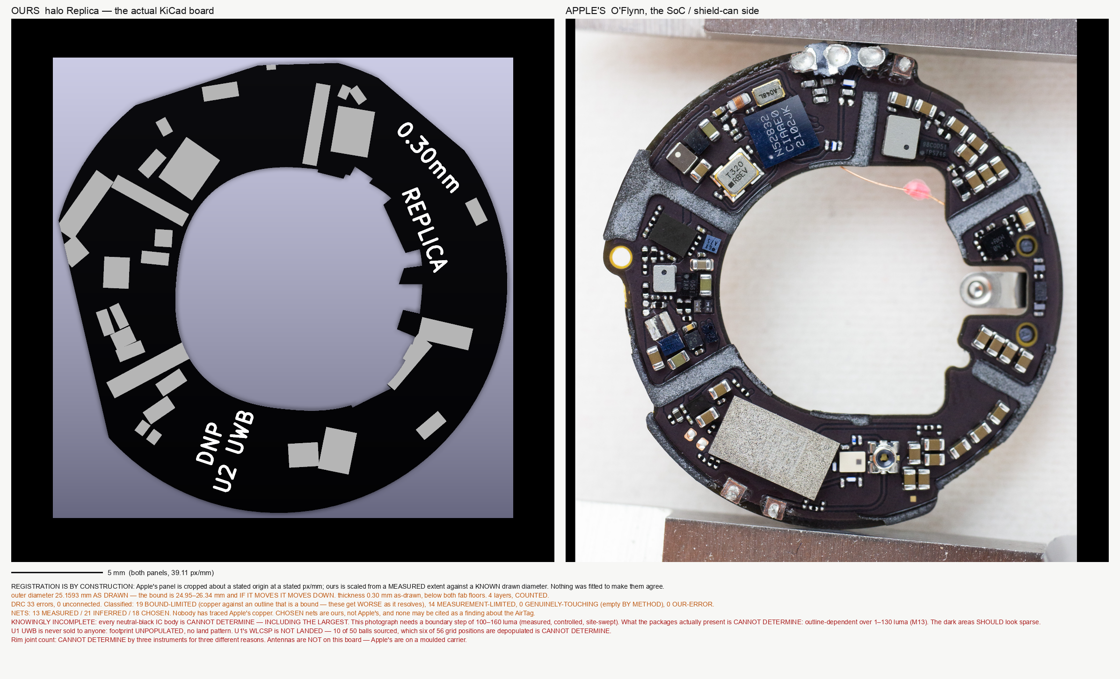
electronics/halo_replica/pcb/out/compare-real.png
