Leif-Rydenfalk/halo/electronics/halo_replica/pcb/out/halo_replica-bottom-BROKEN.png

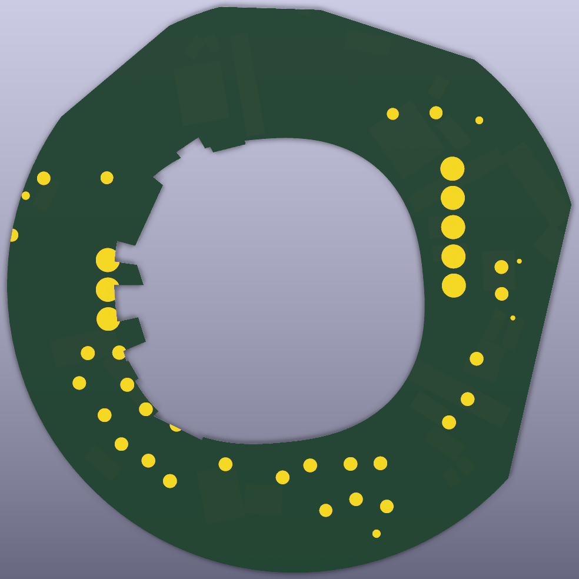
electronics/halo_replica/pcb/out/halo_replica-bottom-BROKEN.png
