Leif-Rydenfalk/halo/electronics/halo_replica/pcb/out/halo_replica-top-BROKEN.png

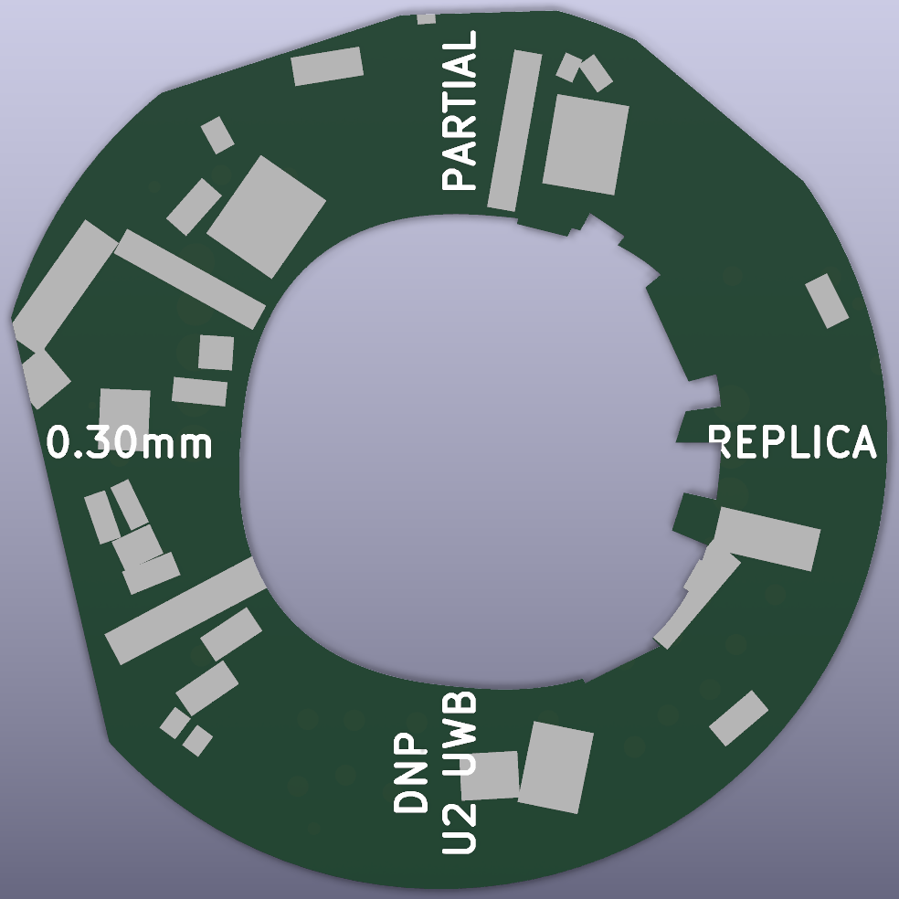
electronics/halo_replica/pcb/out/halo_replica-top-BROKEN.png
