Leif-Rydenfalk/halo/electronics/halo_replica/pcb/out/halo_replica-top.png

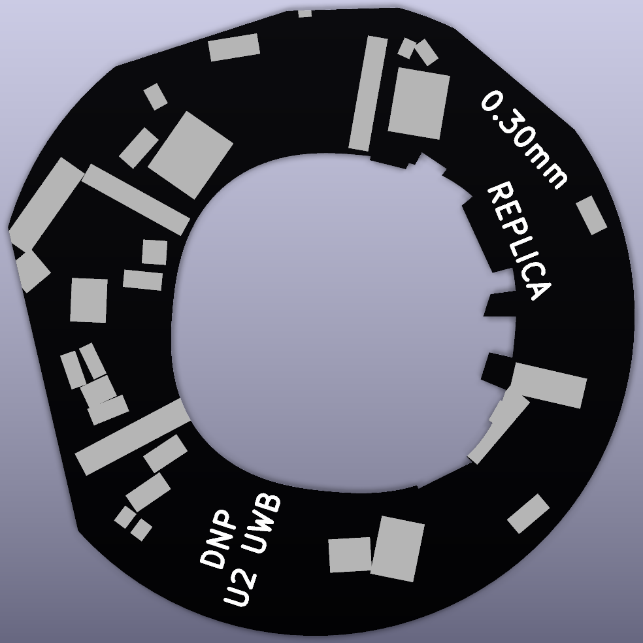
electronics/halo_replica/pcb/out/halo_replica-top.png
