Leif-Rydenfalk/halo/images/airtag/fcc-BCGA2187-internal-photo-3.jpg

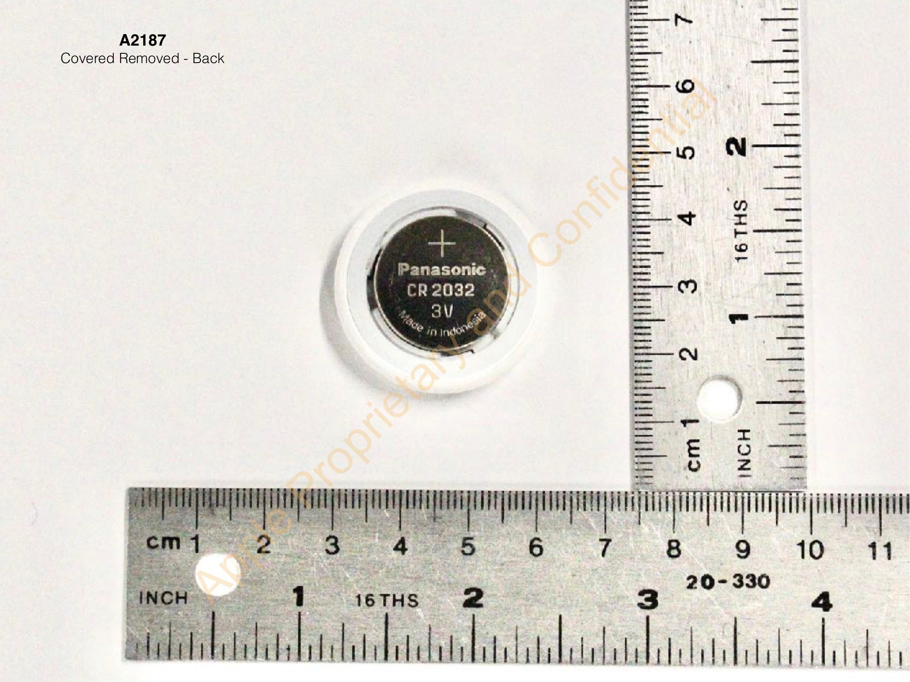
images/airtag/fcc-BCGA2187-internal-photo-3.jpg
