Leif-Rydenfalk/halo/images/airtag/fcc-BCGA2187-internal-photo-7.jpg

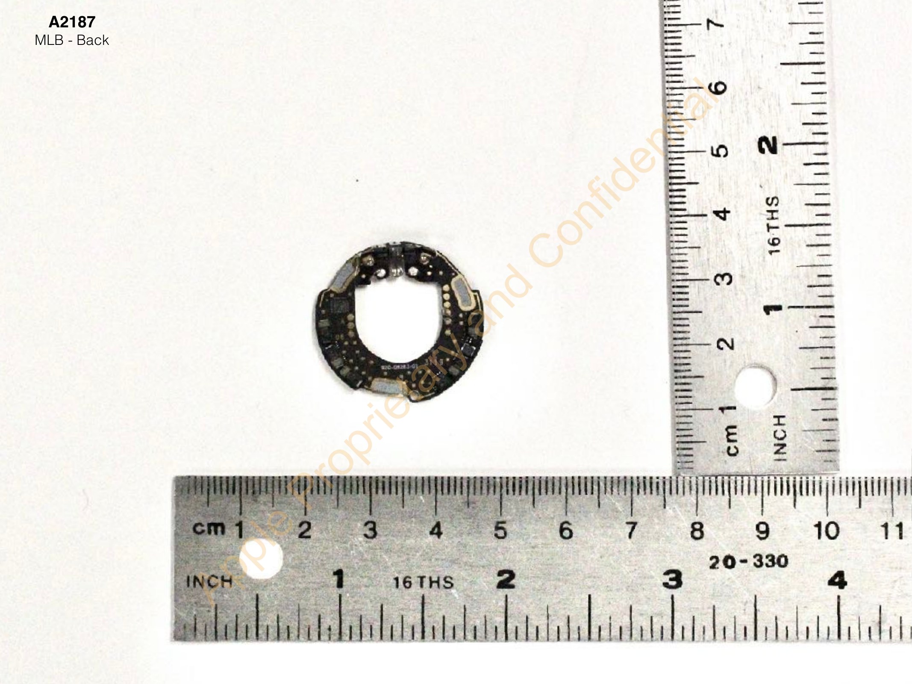
images/airtag/fcc-BCGA2187-internal-photo-7.jpg
