Leif-Rydenfalk/halo/images/airtag/fcc-BCGA2187-internal-photo-8.jpg

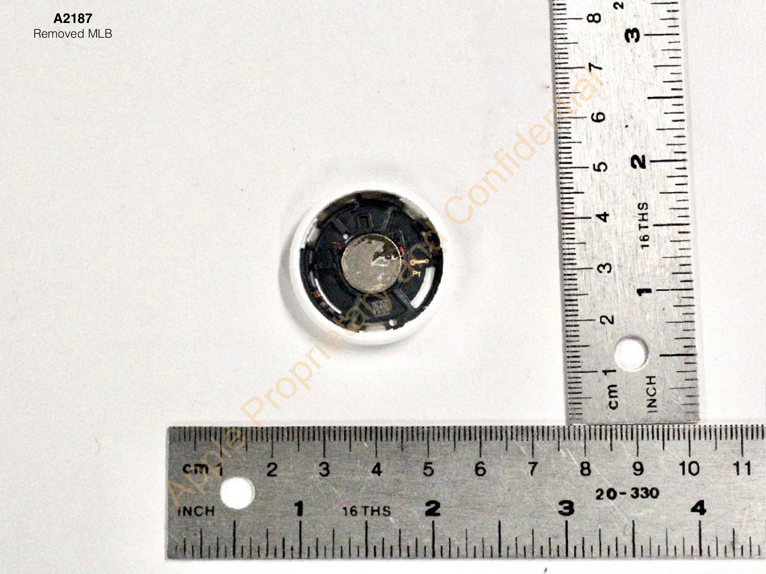
images/airtag/fcc-BCGA2187-internal-photo-8.jpg
