Leif-Rydenfalk/halo/images/commercial/FCC_2AD85-C21M_Chipolo-ONE-Spot_p-2.png

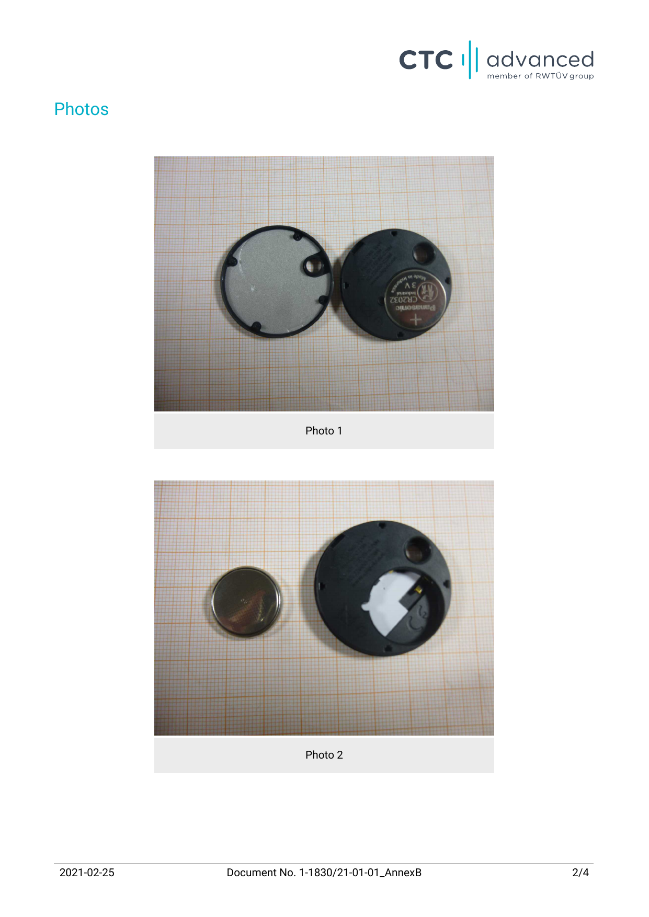
images/commercial/FCC_2AD85-C21M_Chipolo-ONE-Spot_p-2.png
