Leif-Rydenfalk/halo/images/commercial/FCC_2AG5O-PB-531-BG_Pebblebee-Clip_p-2.png

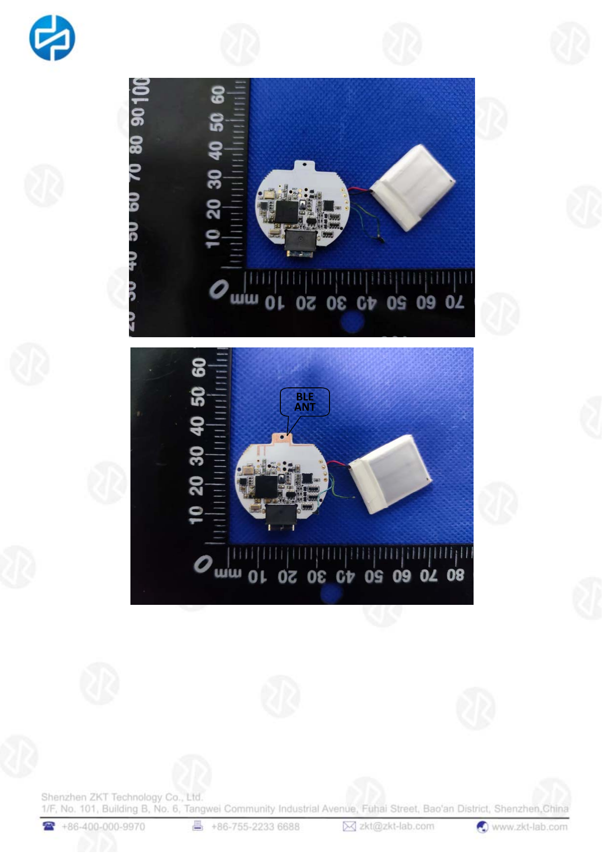
images/commercial/FCC_2AG5O-PB-531-BG_Pebblebee-Clip_p-2.png
