Leif-Rydenfalk/halo/images/commercial/FCC_2AOKB-T87B0_eufy-SmartTrack-Link_p-1.png

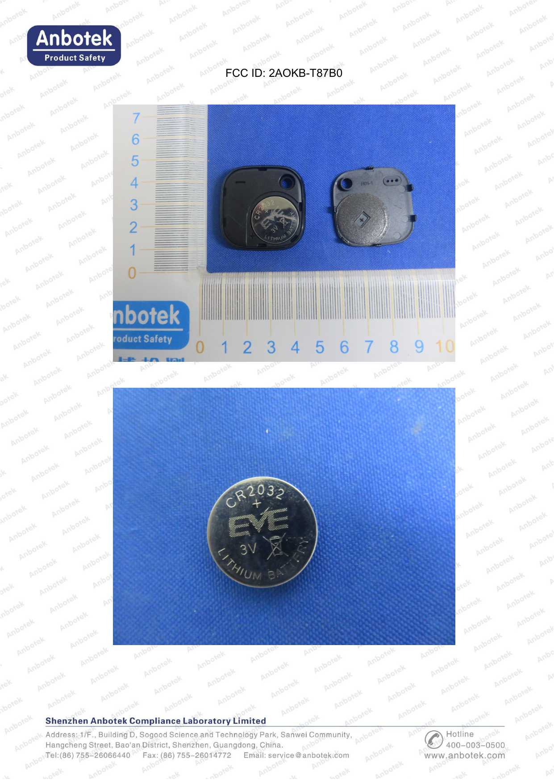
images/commercial/FCC_2AOKB-T87B0_eufy-SmartTrack-Link_p-1.png
