Leif-Rydenfalk/halo/images/commercial/FCC_2AOKB-T87B0_eufy-SmartTrack-Link_p-4.png

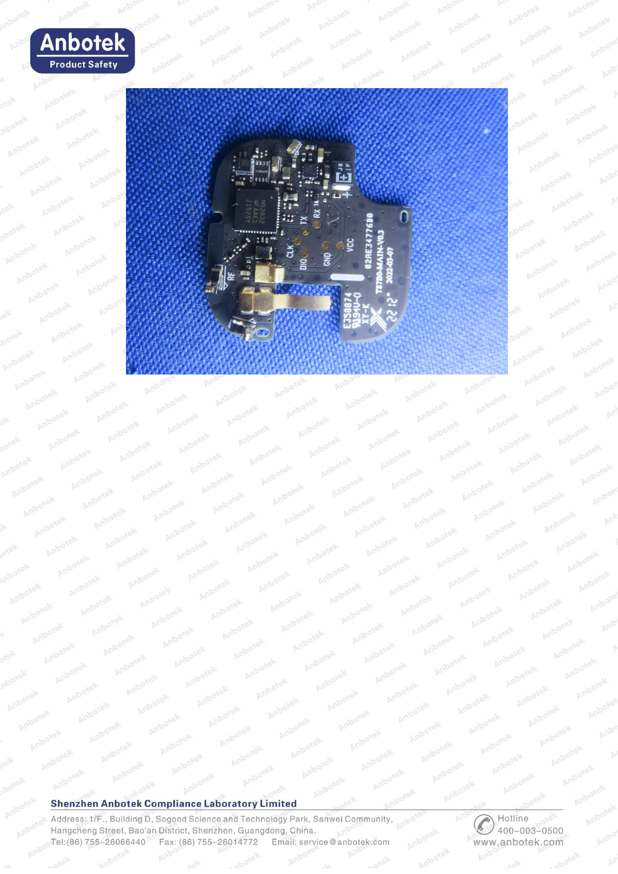
images/commercial/FCC_2AOKB-T87B0_eufy-SmartTrack-Link_p-4.png
