Leif-Rydenfalk/halo/images/commercial/FCC_2AQI5-CM816_UGREEN-Smart-Finder_p-3.png

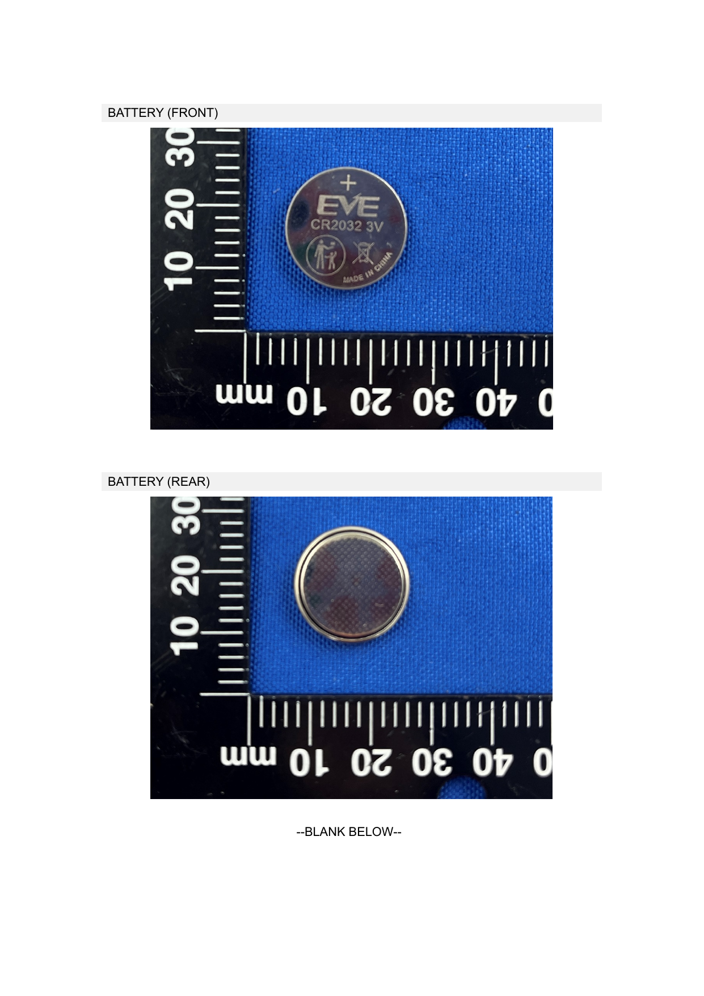
images/commercial/FCC_2AQI5-CM816_UGREEN-Smart-Finder_p-3.png
