Leif-Rydenfalk/halo/images/commercial/FCC_IHDT6AB3_moto-tag_p-01.png

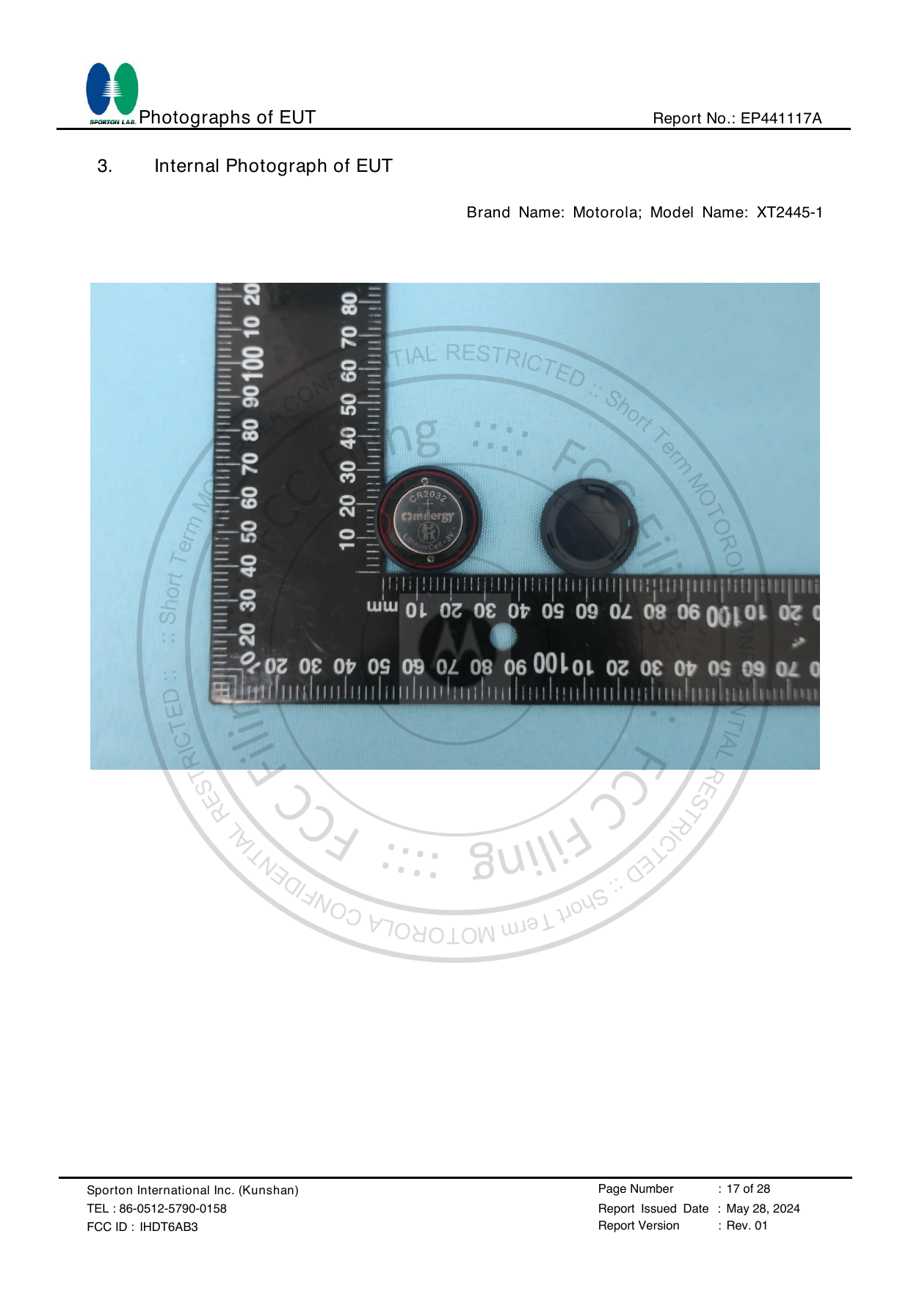
images/commercial/FCC_IHDT6AB3_moto-tag_p-01.png
