Leif-Rydenfalk/halo/images/commercial/FCC_IHDT6AB3_moto-tag_p-05.png

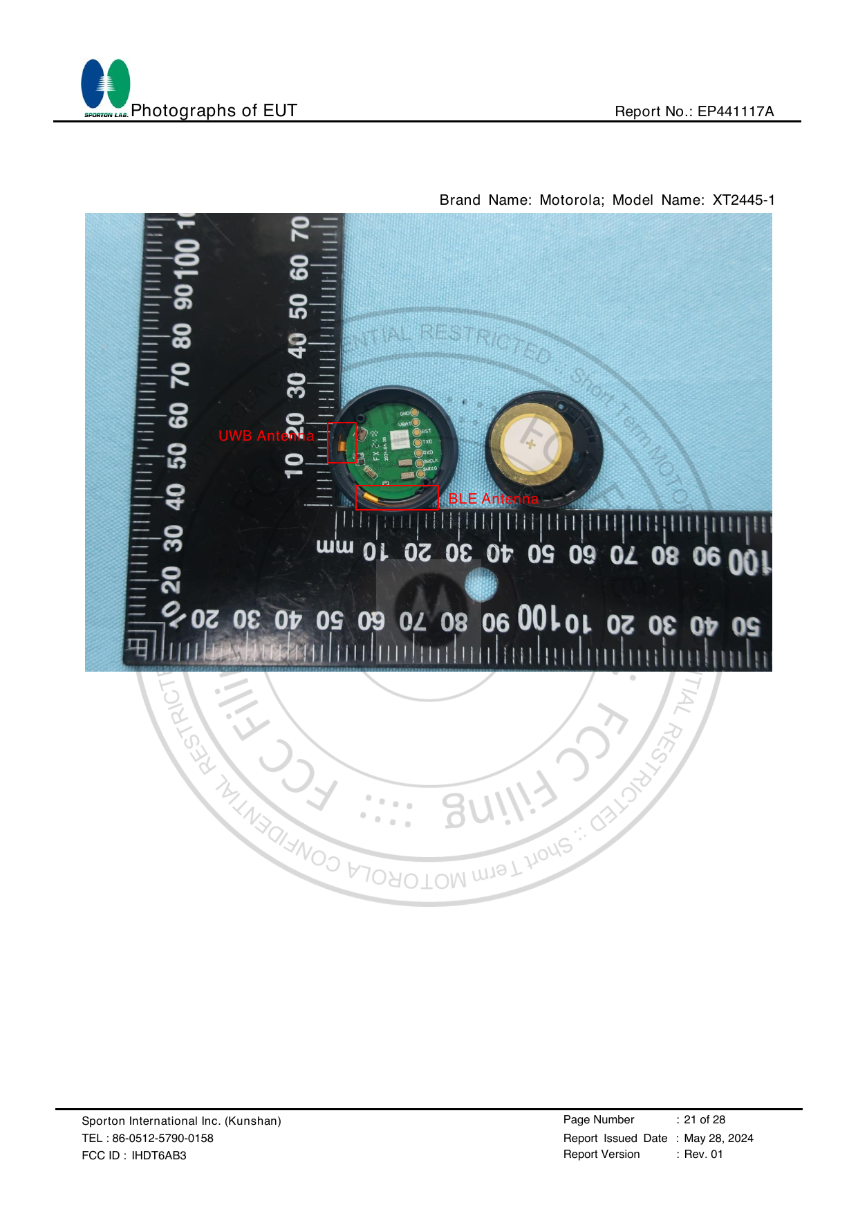
images/commercial/FCC_IHDT6AB3_moto-tag_p-05.png
