Leif-Rydenfalk/halo/images/commercial/FCC_IHDT6AB3_moto-tag_p-08.png

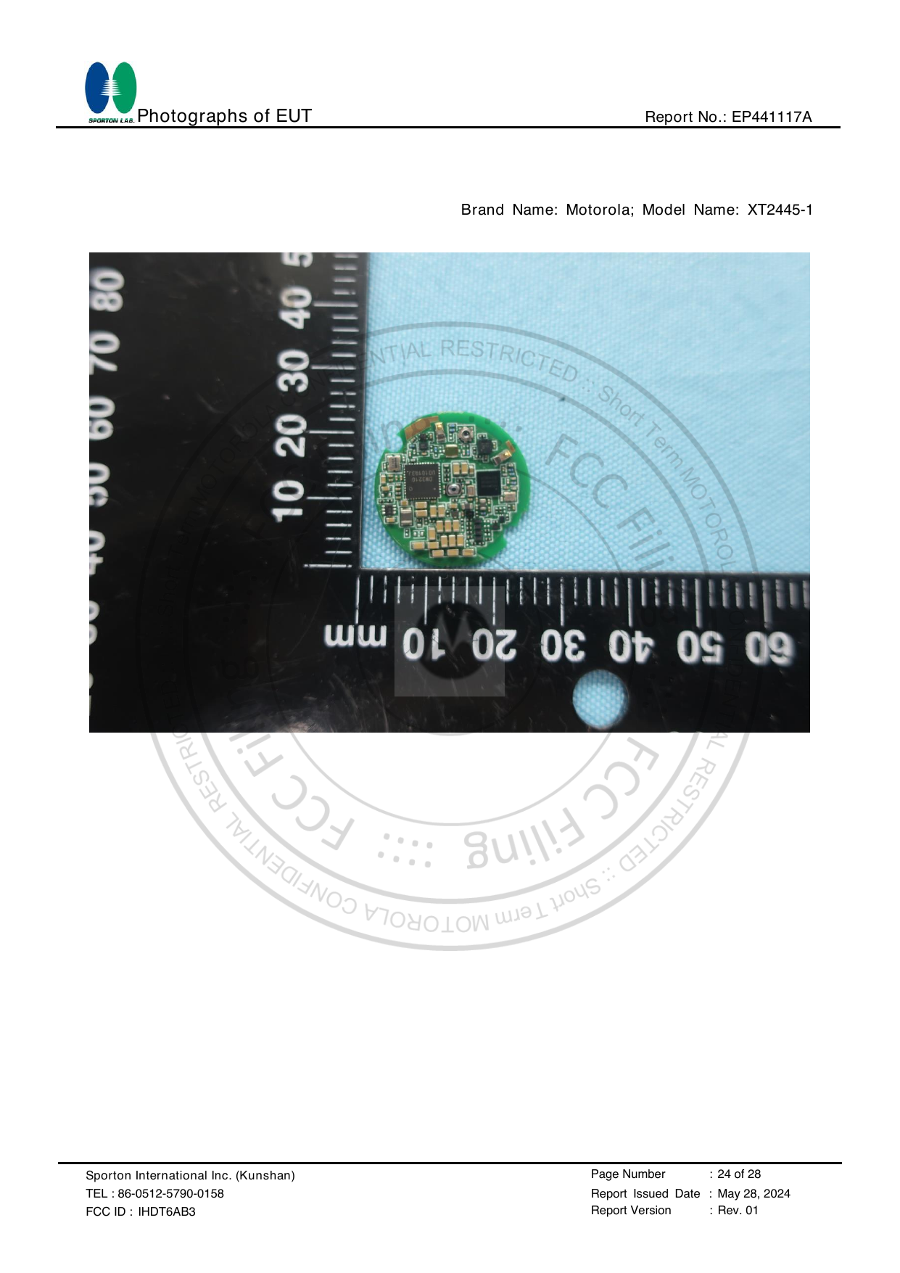
images/commercial/FCC_IHDT6AB3_moto-tag_p-08.png
