Leif-Rydenfalk/halo/images/designs/C-airtag-buttoncells-scale.jpg

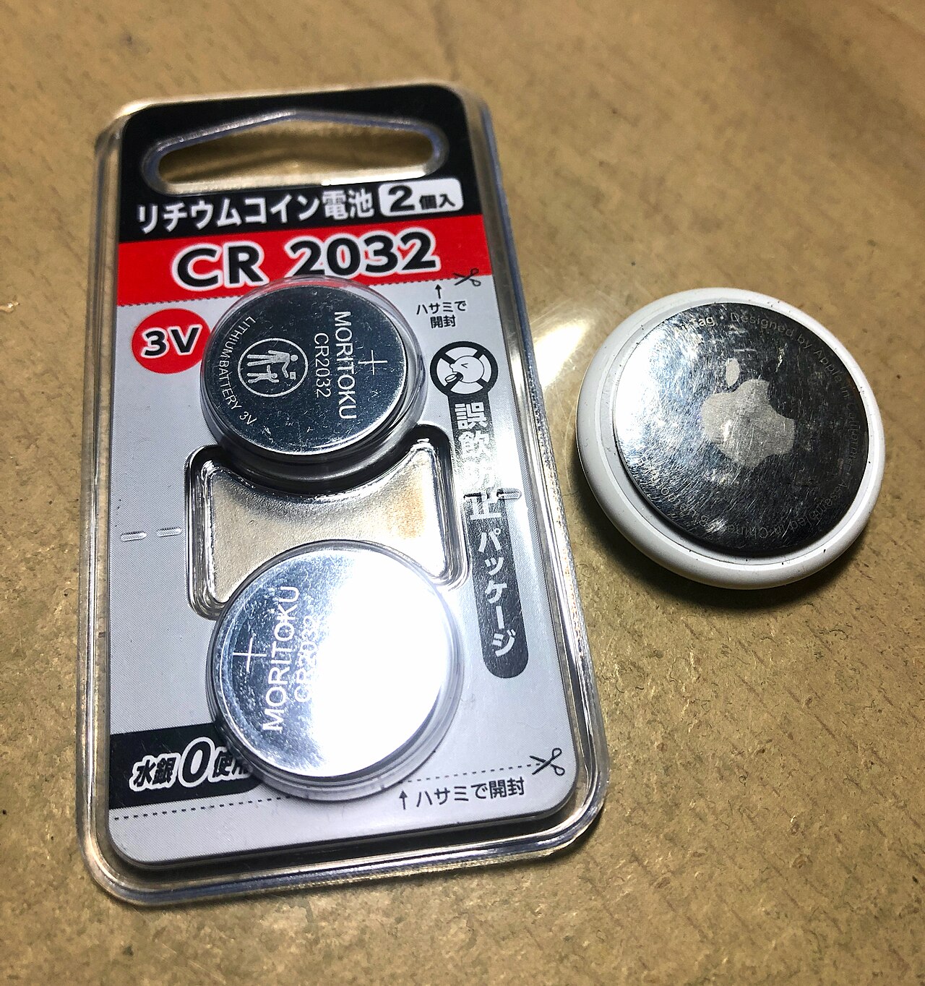
images/designs/C-airtag-buttoncells-scale.jpg
