Leif-Rydenfalk/halo/images/designs/C-airtag-inside-3.jpg

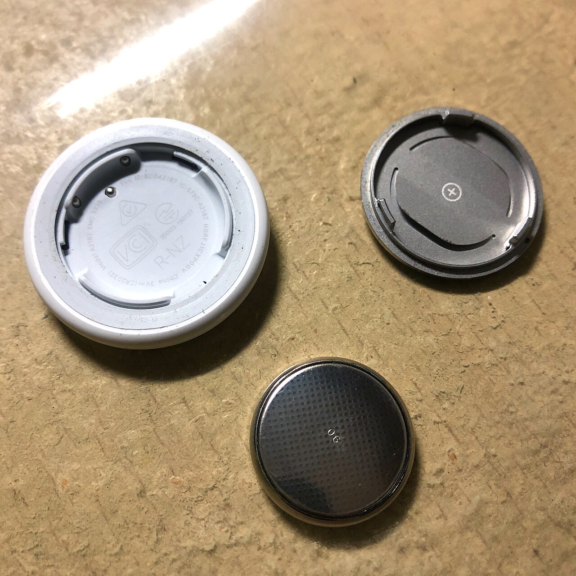
images/designs/C-airtag-inside-3.jpg
