Leif-Rydenfalk/halo/images/mechanical/Airtag_-_4.jpg

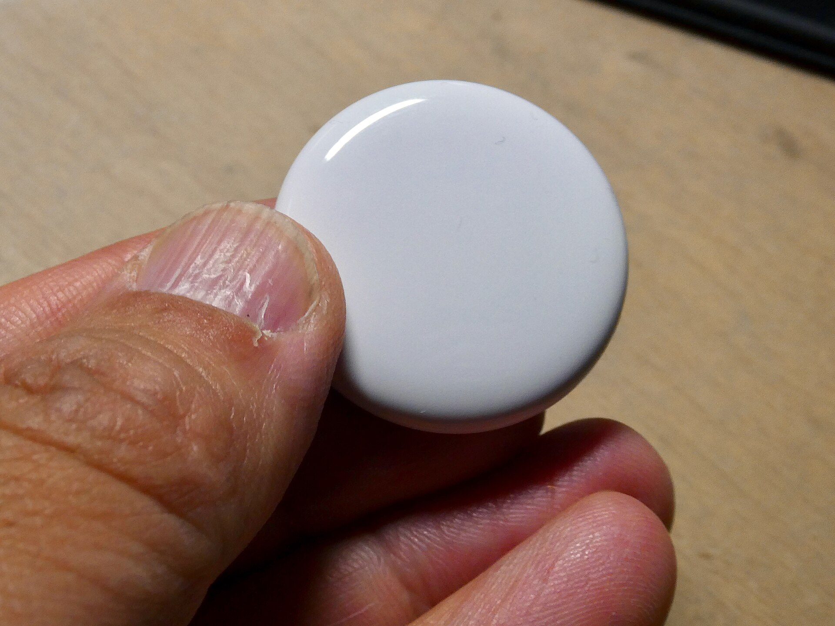
images/mechanical/Airtag_-_4.jpg
