Leif-Rydenfalk/halo/images/mechanical/Airtag_-_7.jpg

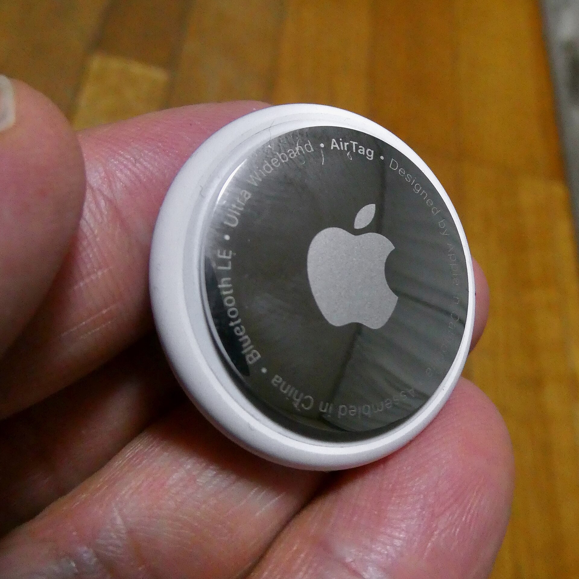
images/mechanical/Airtag_-_7.jpg
