Leif-Rydenfalk/halo/images/mechanical/Airtag_-_8.jpg

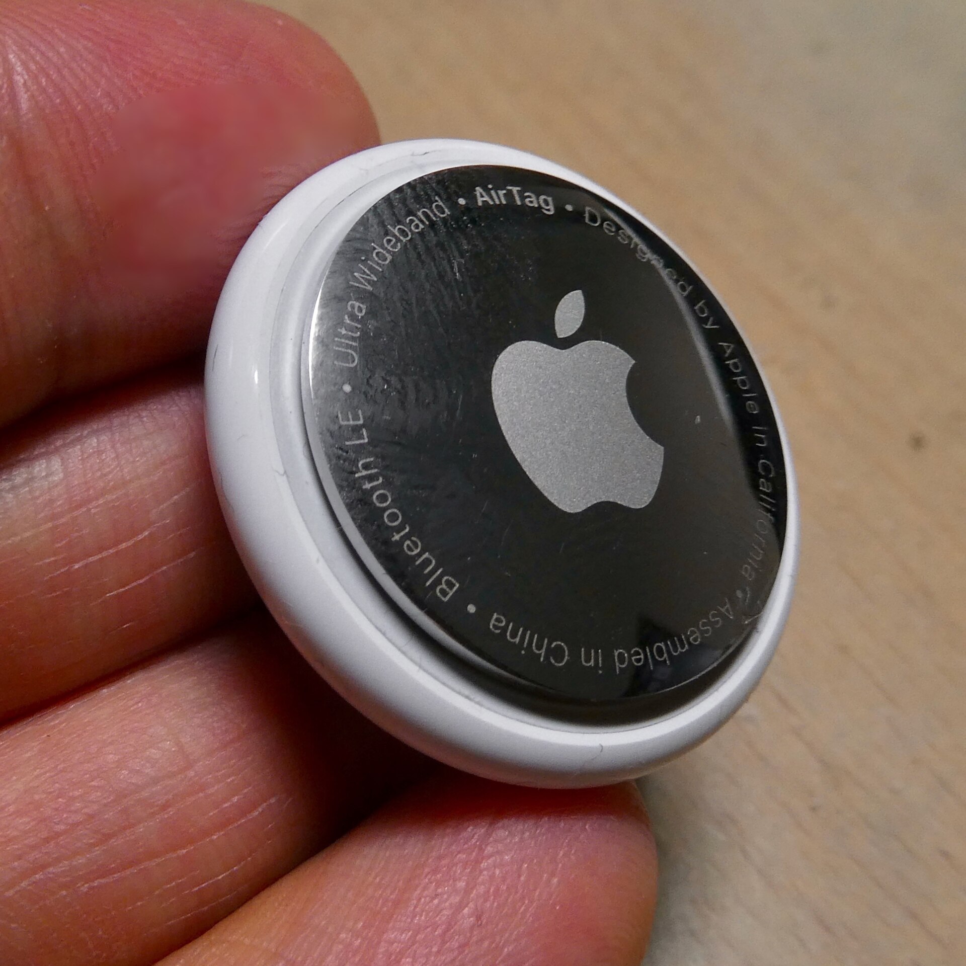
images/mechanical/Airtag_-_8.jpg
