Leif-Rydenfalk/halo/images/mechanical/Airtag_-_9.jpg

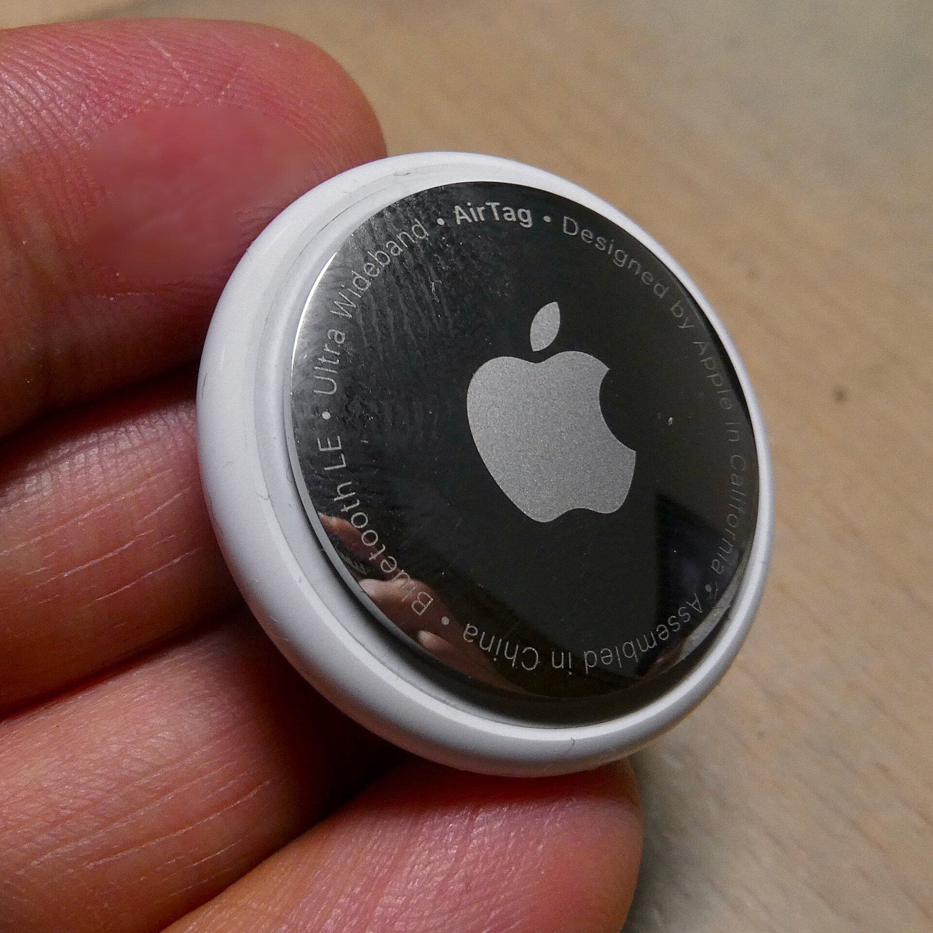
images/mechanical/Airtag_-_9.jpg
