Leif-Rydenfalk/halo/out/comparison/fig-boards-labelled.png

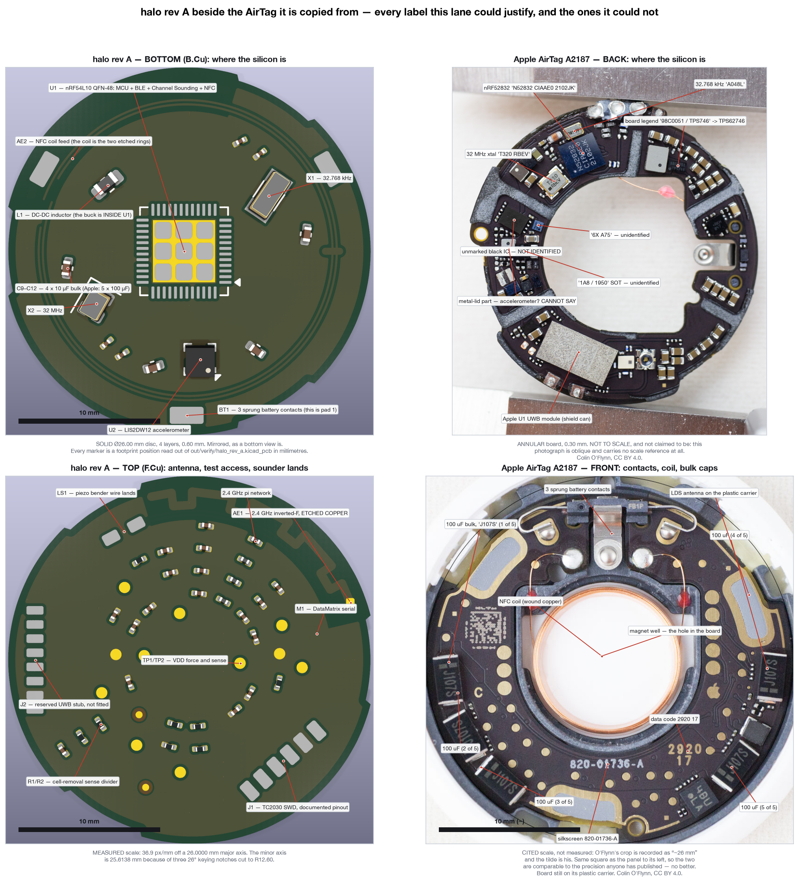
out/comparison/fig-boards-labelled.png
