Leif-Rydenfalk/halo/out/gallery/fig-board-side-by-side.png

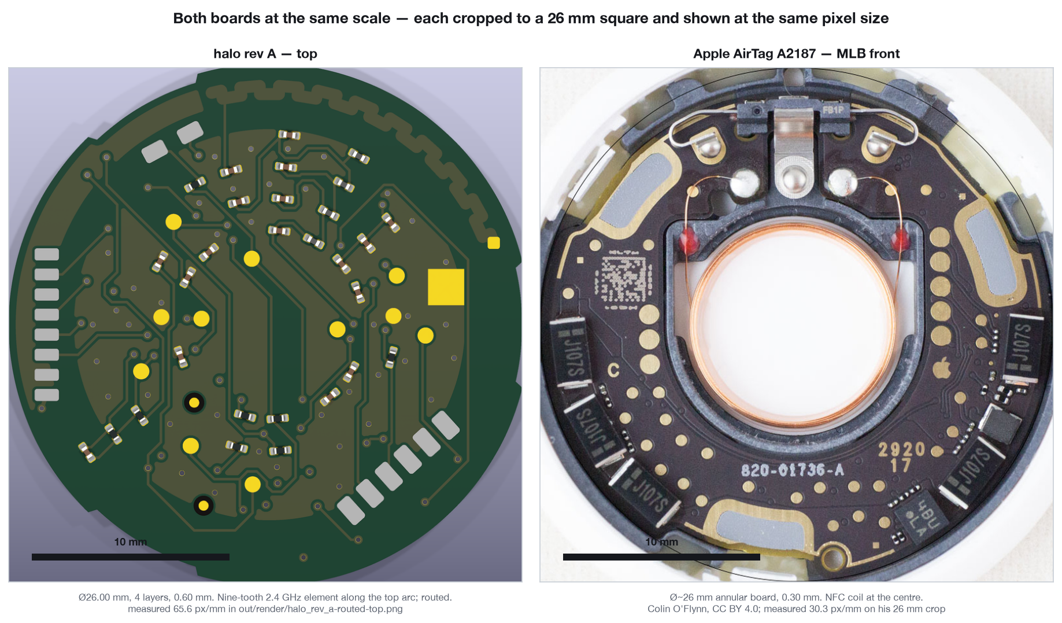
out/gallery/fig-board-side-by-side.png
