Leif-Rydenfalk/halo/out/gallery/img/ce-rf-out-halo-rev-a-2g4-meander4-bare-pad-quarter-s11.png

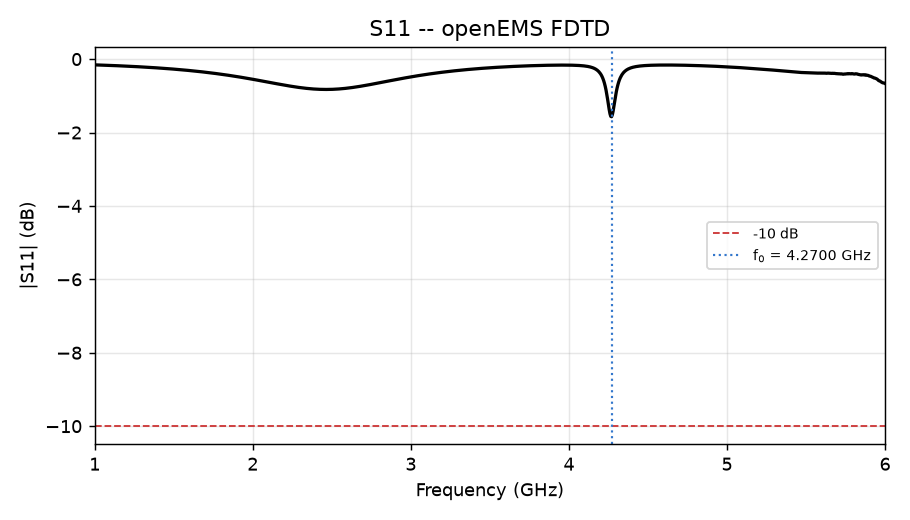
out/gallery/img/ce-rf-out-halo-rev-a-2g4-meander4-bare-pad-quarter-s11.png
