Leif-Rydenfalk/halo/out/gallery/img/ce-rf-out-halo-rev-a-2g4-meander9-passive-pattern.png

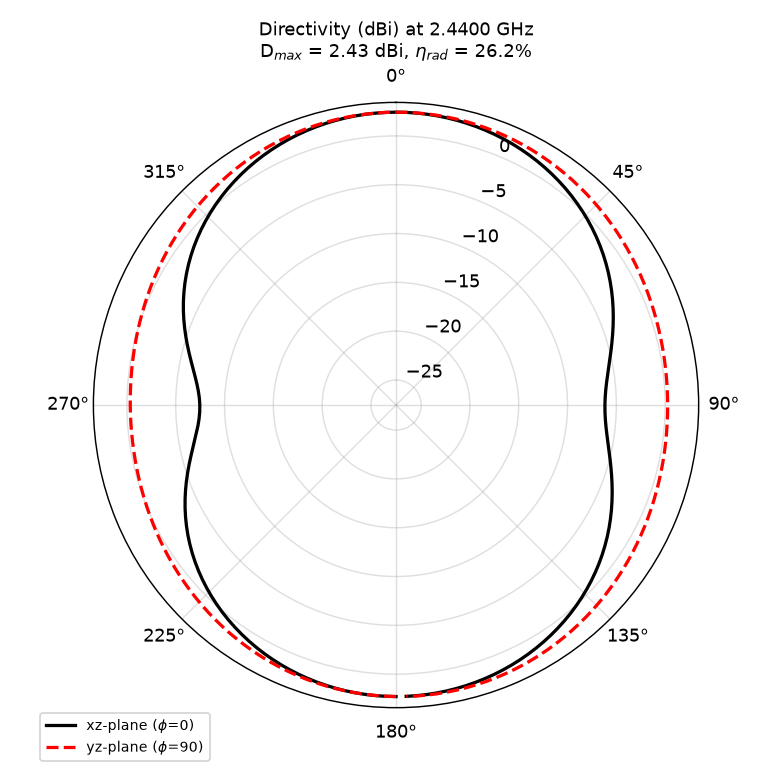
out/gallery/img/ce-rf-out-halo-rev-a-2g4-meander9-passive-pattern.png
