Leif-Rydenfalk/halo/out/gallery/img/ce-rf-out-halo-rev-a-2g4-room-r4000-layout.png

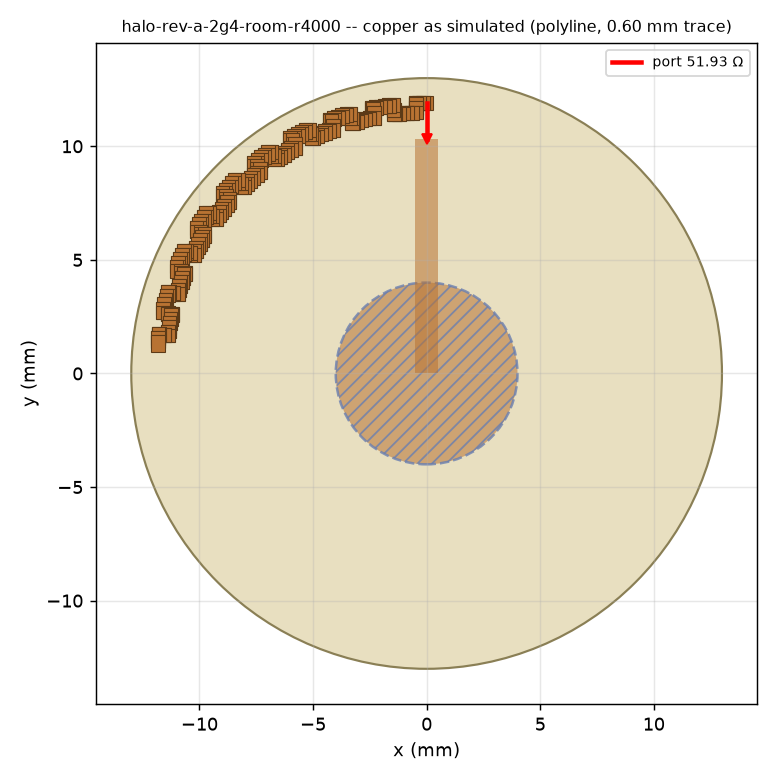
out/gallery/img/ce-rf-out-halo-rev-a-2g4-room-r4000-layout.png
