Leif-Rydenfalk/halo/out/gallery/img/ce-rf-out-halo-rev-a-2g4-rt1-bare-pattern.png

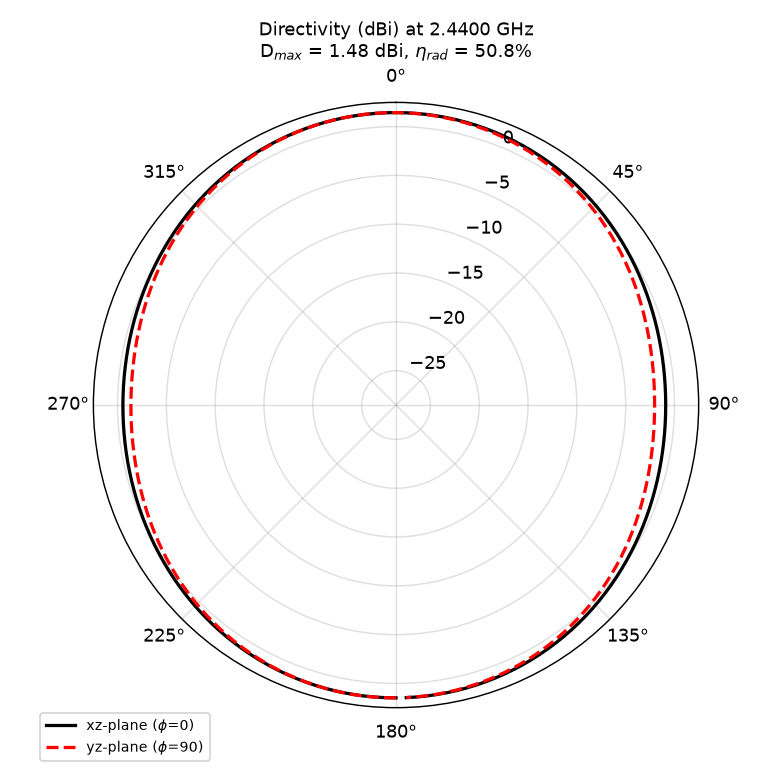
out/gallery/img/ce-rf-out-halo-rev-a-2g4-rt1-bare-pattern.png
