Leif-Rydenfalk/halo/out/gallery/img/ce-rf-out-halo-rev-a-2g4-rt1-passive-s11.png

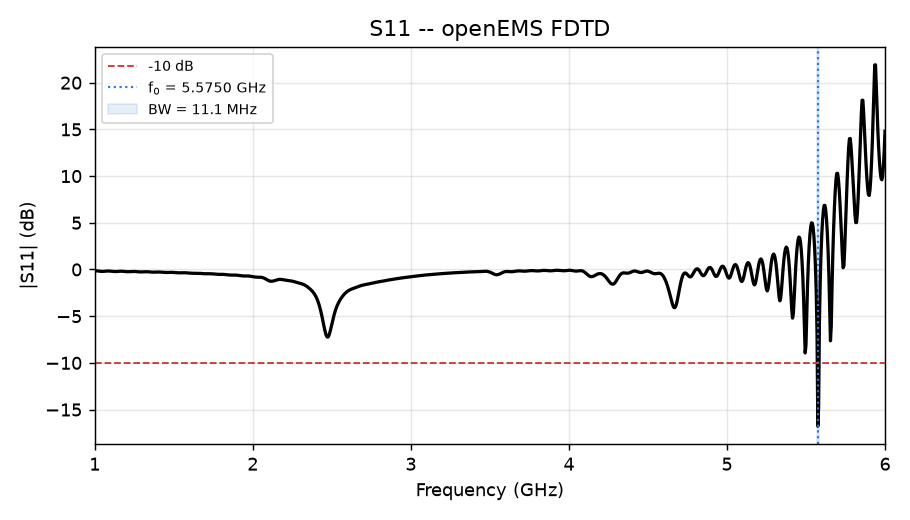
out/gallery/img/ce-rf-out-halo-rev-a-2g4-rt1-passive-s11.png
