Leif-Rydenfalk/halo/out/gallery/img/ce-rf-out-halo-rev-a-2g4-s11.png

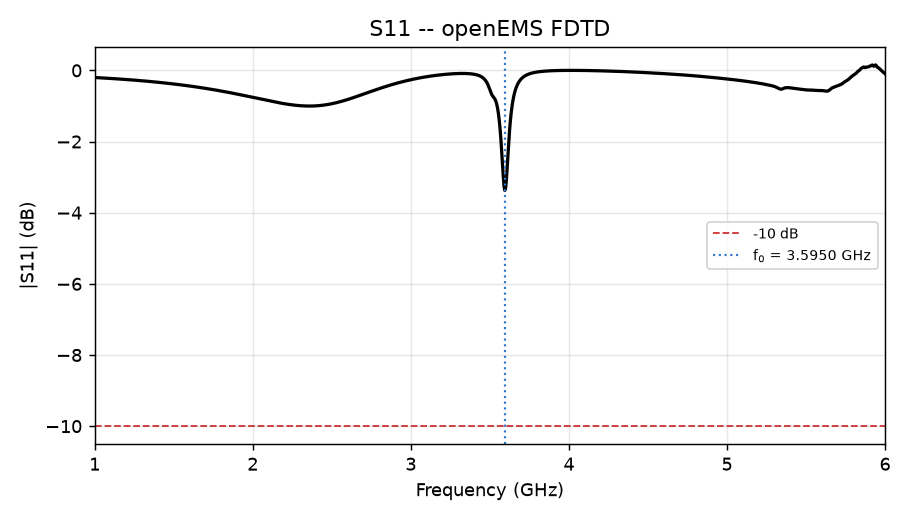
out/gallery/img/ce-rf-out-halo-rev-a-2g4-s11.png
