Leif-Rydenfalk/halo/out/gallery/img/ce-rf-out-halo-rev-a-2g4-zin.png

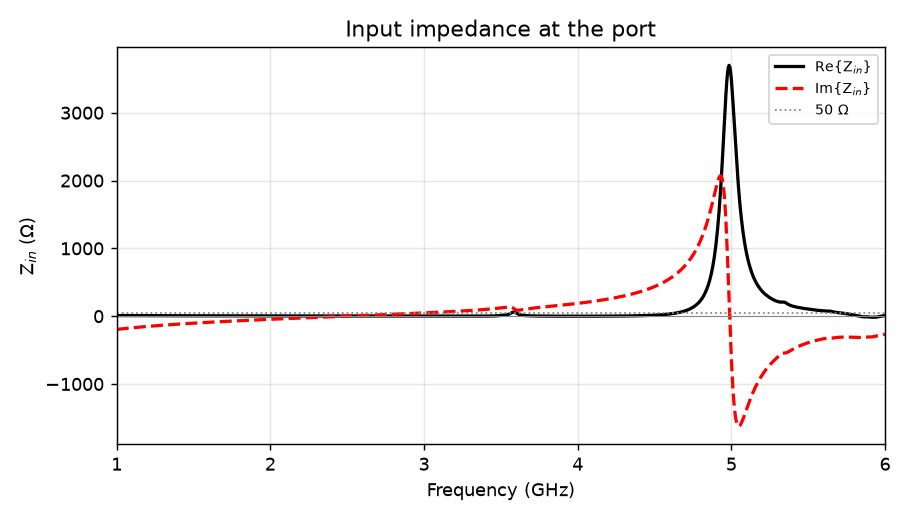
out/gallery/img/ce-rf-out-halo-rev-a-2g4-zin.png
