Leif-Rydenfalk/halo/out/gallery/img/ce-rf-out-halo-round-rim-ifa-layout.png

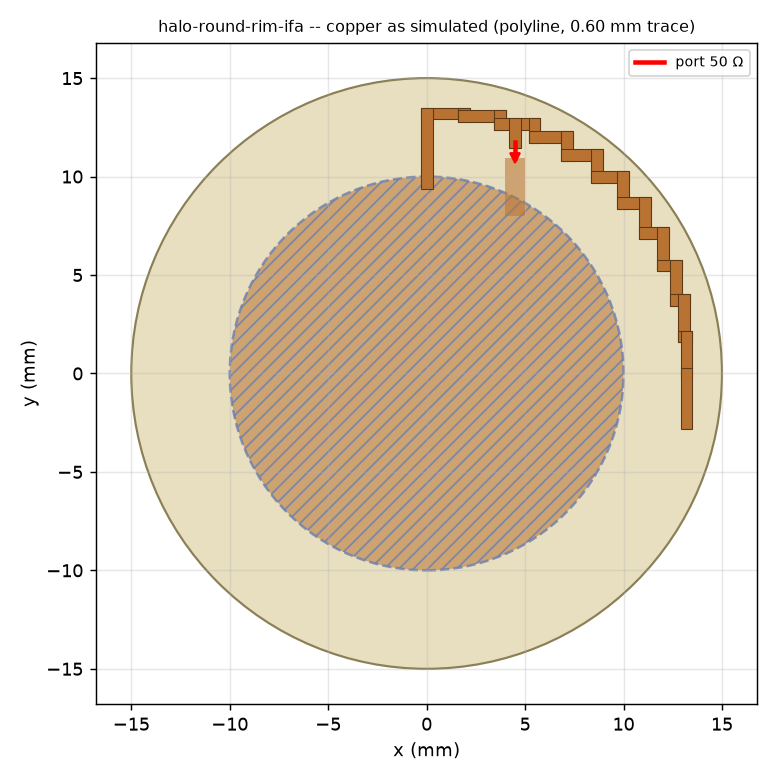
out/gallery/img/ce-rf-out-halo-round-rim-ifa-layout.png
