Leif-Rydenfalk/halo/out/gallery/img/ce-rf-out-halo-round-rim-ifa-zin.png

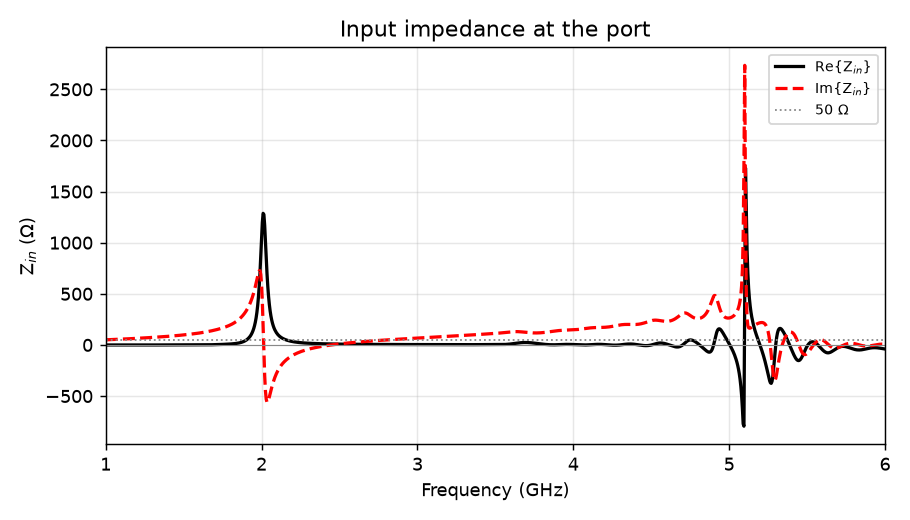
out/gallery/img/ce-rf-out-halo-round-rim-ifa-zin.png
