Leif-Rydenfalk/halo/out/gallery/img/ce-spice-out-cr2032_pulse_load-end-of-life.png

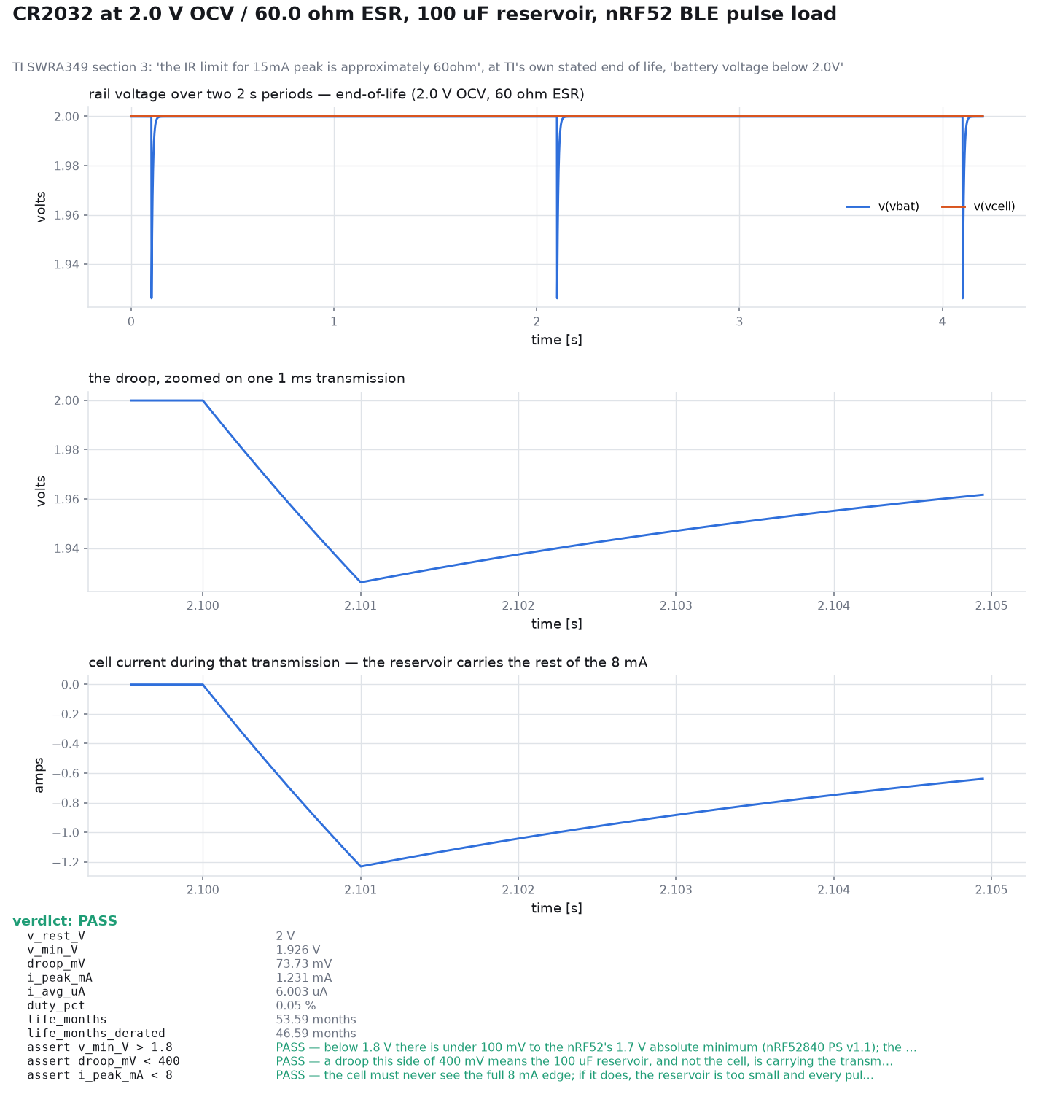
out/gallery/img/ce-spice-out-cr2032_pulse_load-end-of-life.png
