Leif-Rydenfalk/halo/out/gallery/img/ce-spice-out-cr2032_pulse_load-fresh.png

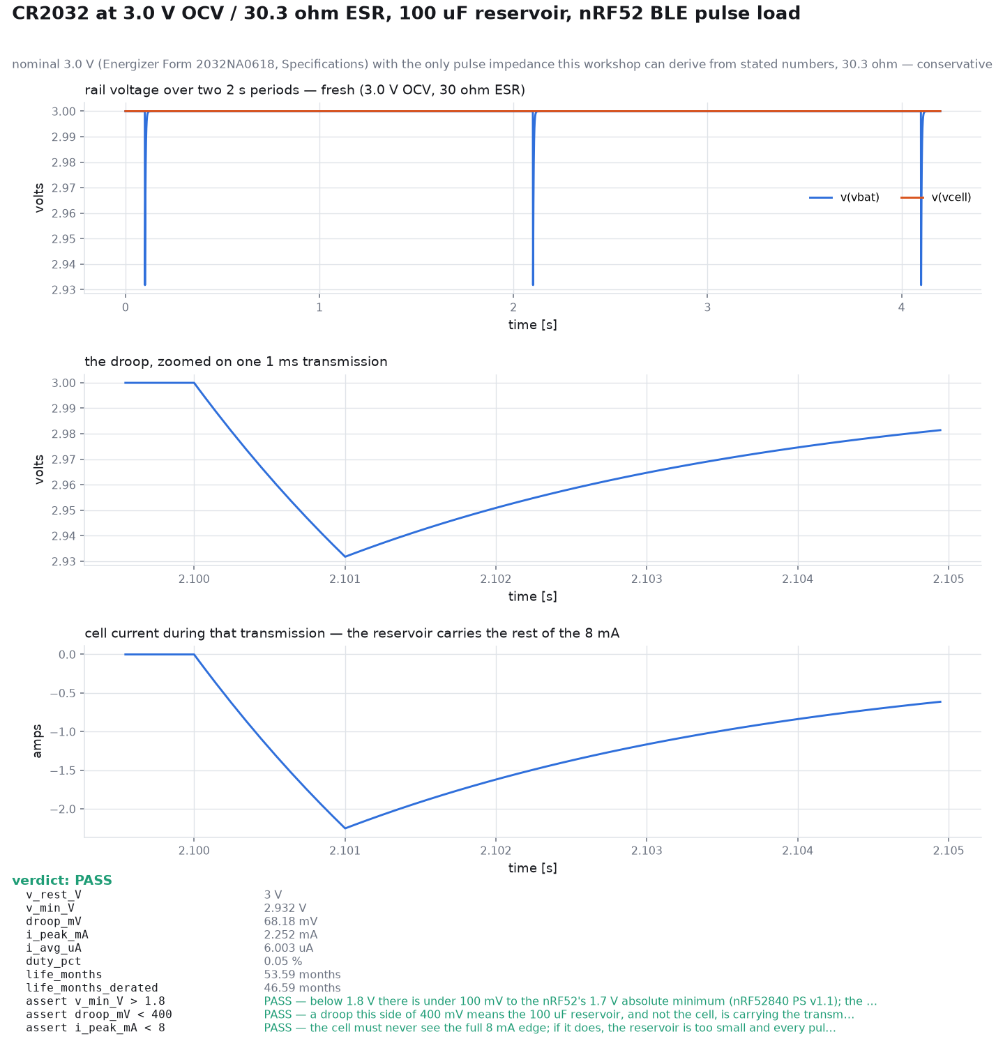
out/gallery/img/ce-spice-out-cr2032_pulse_load-fresh.png
