Leif-Rydenfalk/halo/out/gallery/img/ce-spice-out-cr2032_pulse_load-worst-case-no-reservoir.png

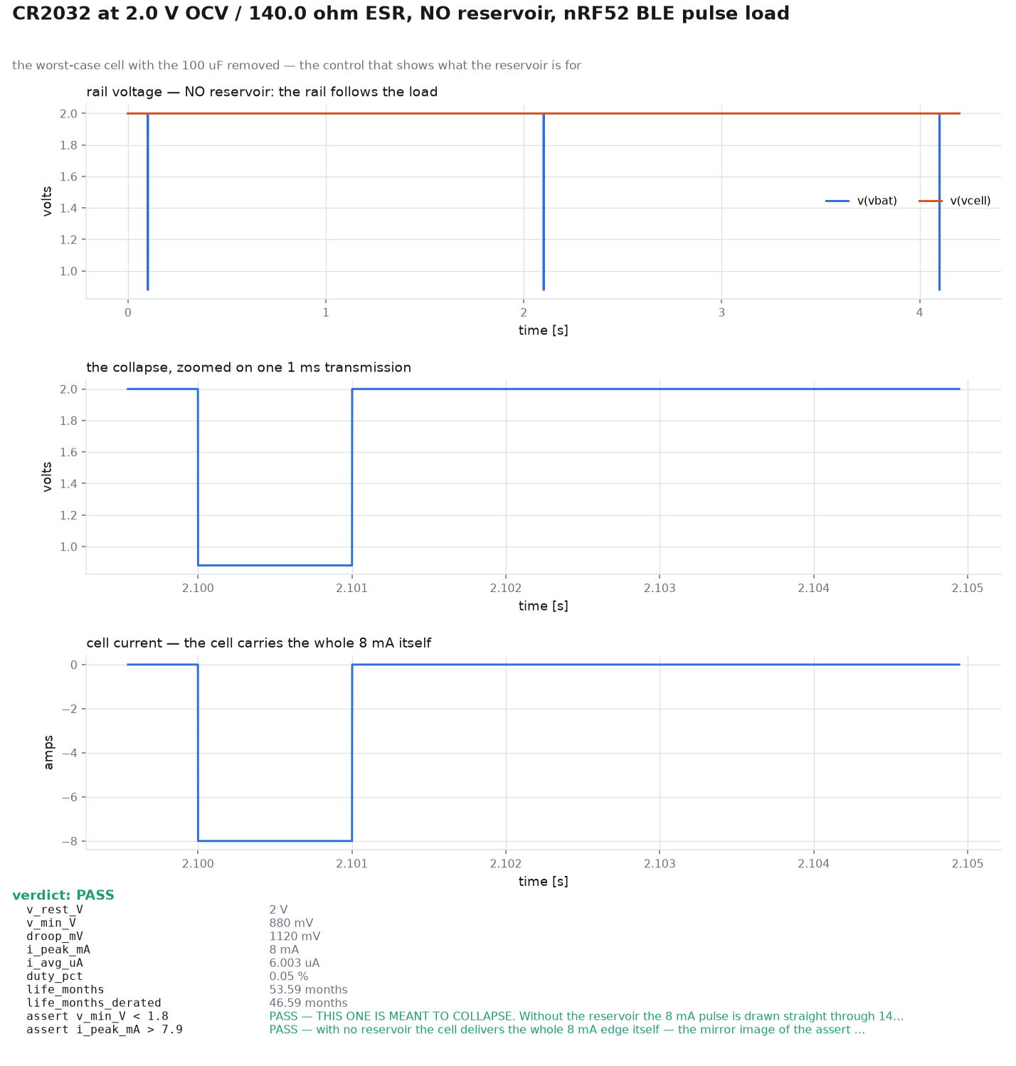
out/gallery/img/ce-spice-out-cr2032_pulse_load-worst-case-no-reservoir.png
