Leif-Rydenfalk/halo/out/gallery/img/ce-spice-out-decoupling_ldo-datasheet-check.png

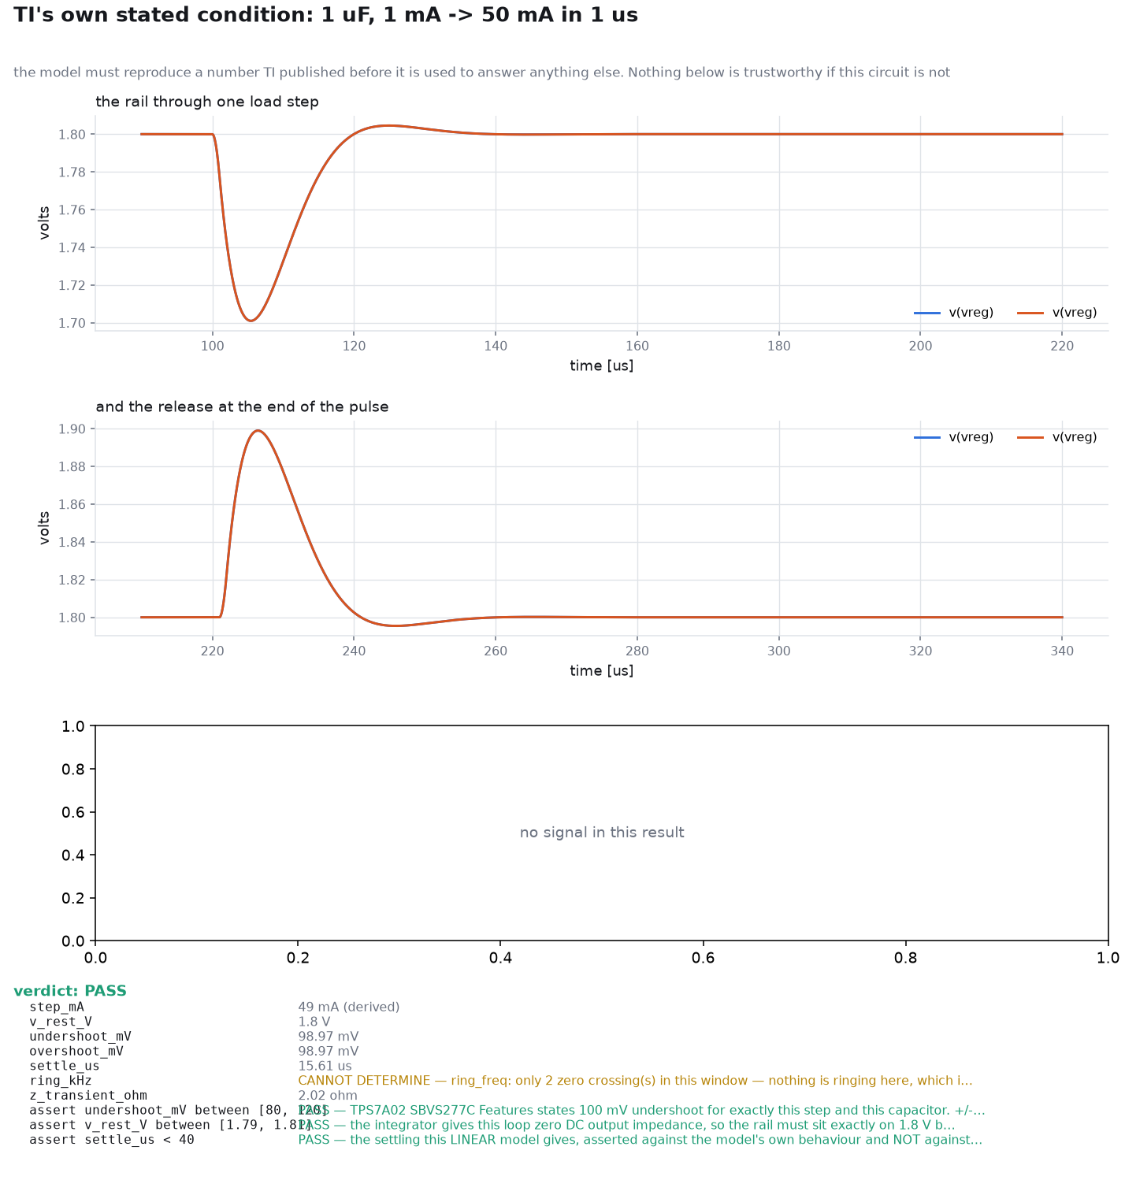
out/gallery/img/ce-spice-out-decoupling_ldo-datasheet-check.png
