Leif-Rydenfalk/halo/out/gallery/img/ce-spice-out-decoupling_ldo-halo-rail-50ma.png

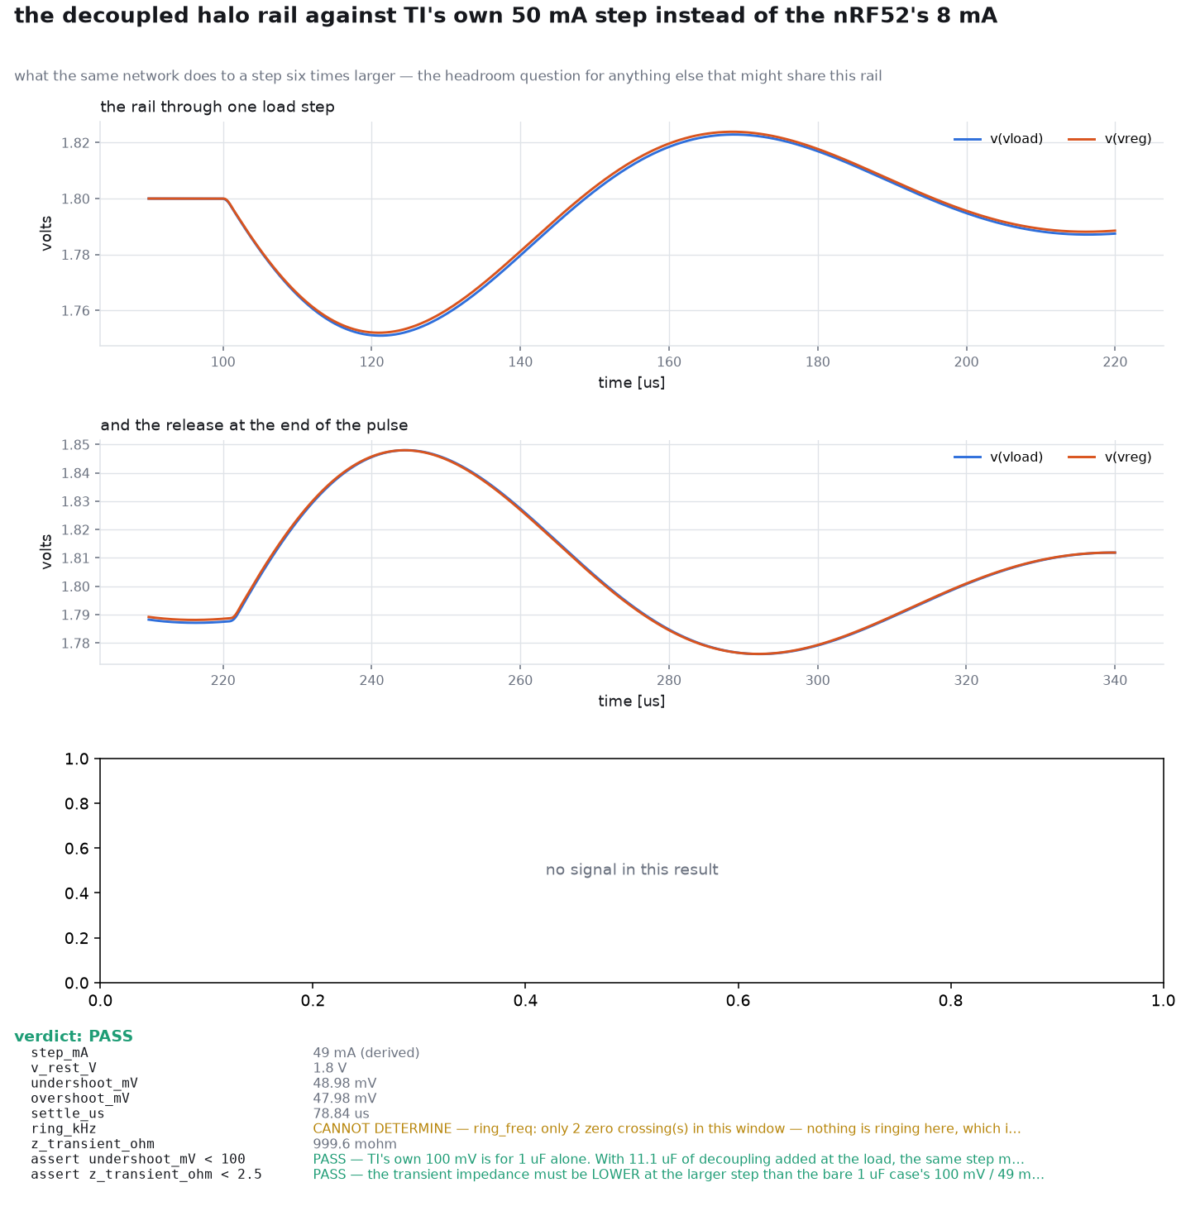
out/gallery/img/ce-spice-out-decoupling_ldo-halo-rail-50ma.png
