Leif-Rydenfalk/halo/out/gallery/img/ce-spice-out-decoupling_ldo-halo-rail.png

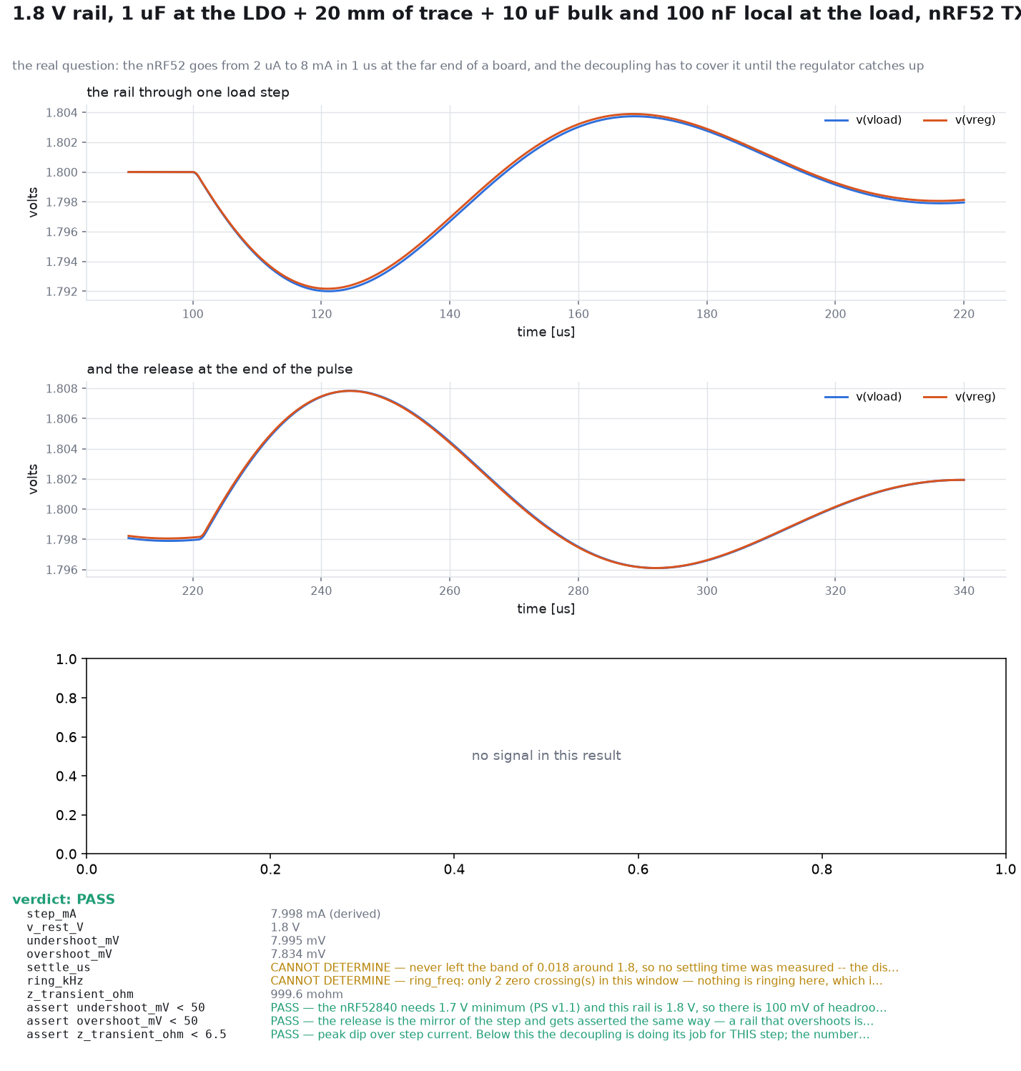
out/gallery/img/ce-spice-out-decoupling_ldo-halo-rail.png
