Leif-Rydenfalk/halo/out/gallery/img/ce-spice-out-decoupling_ldo-no-local-decoupling.png

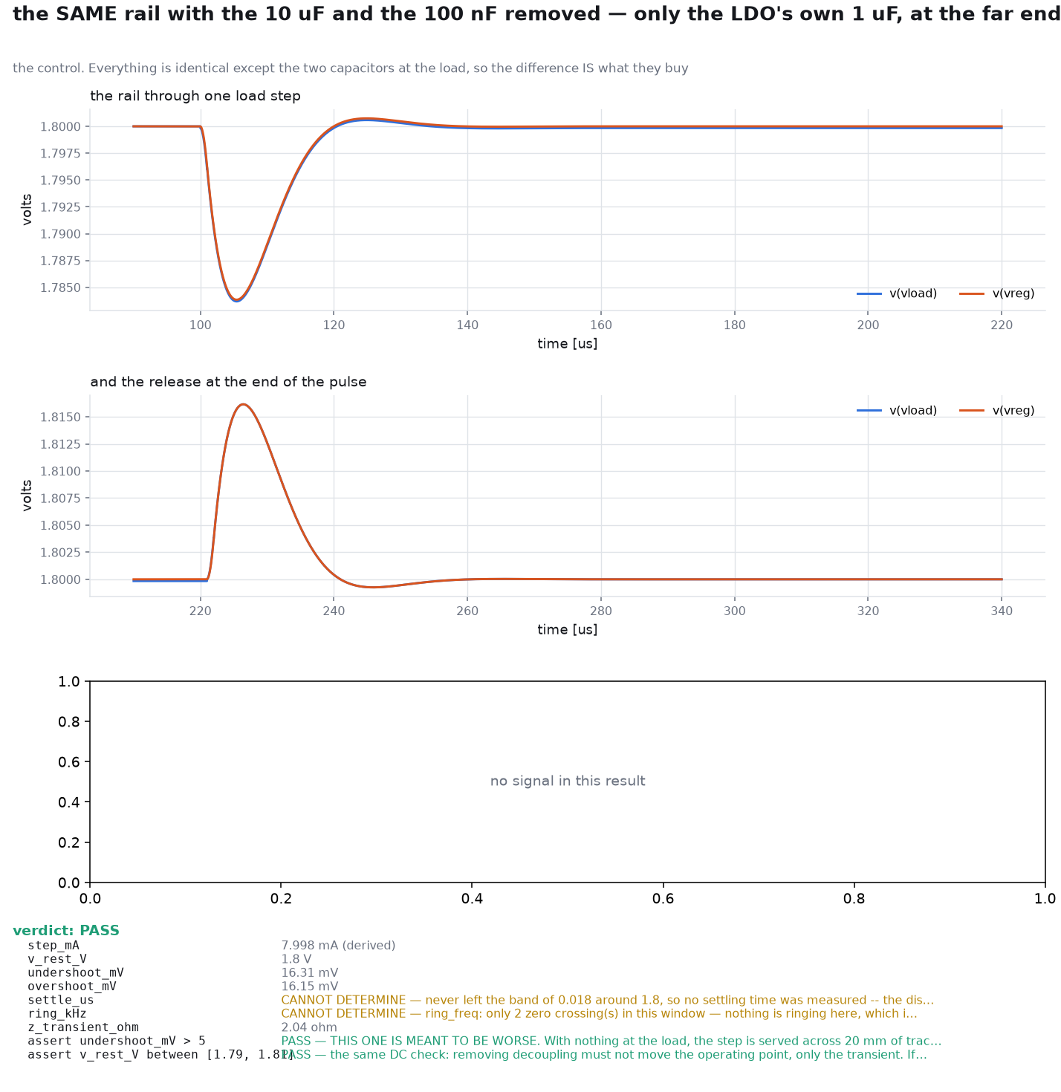
out/gallery/img/ce-spice-out-decoupling_ldo-no-local-decoupling.png
