Leif-Rydenfalk/halo/out/gallery/img/ce-spice-out-decoupling_ldo-underdamped-ringing.png

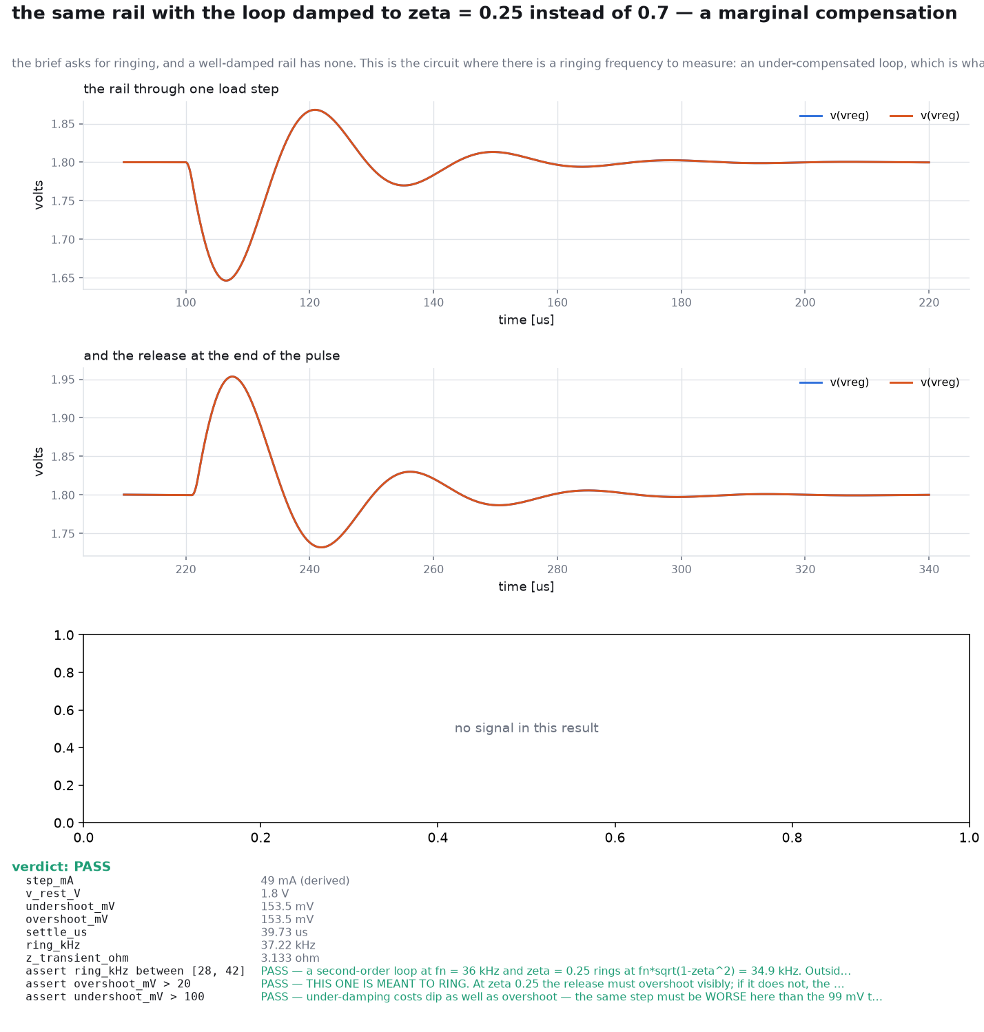
out/gallery/img/ce-spice-out-decoupling_ldo-underdamped-ringing.png
