Leif-Rydenfalk/halo/out/gallery/img/ce-spice-out-nfc_tank-damped-to-35.png

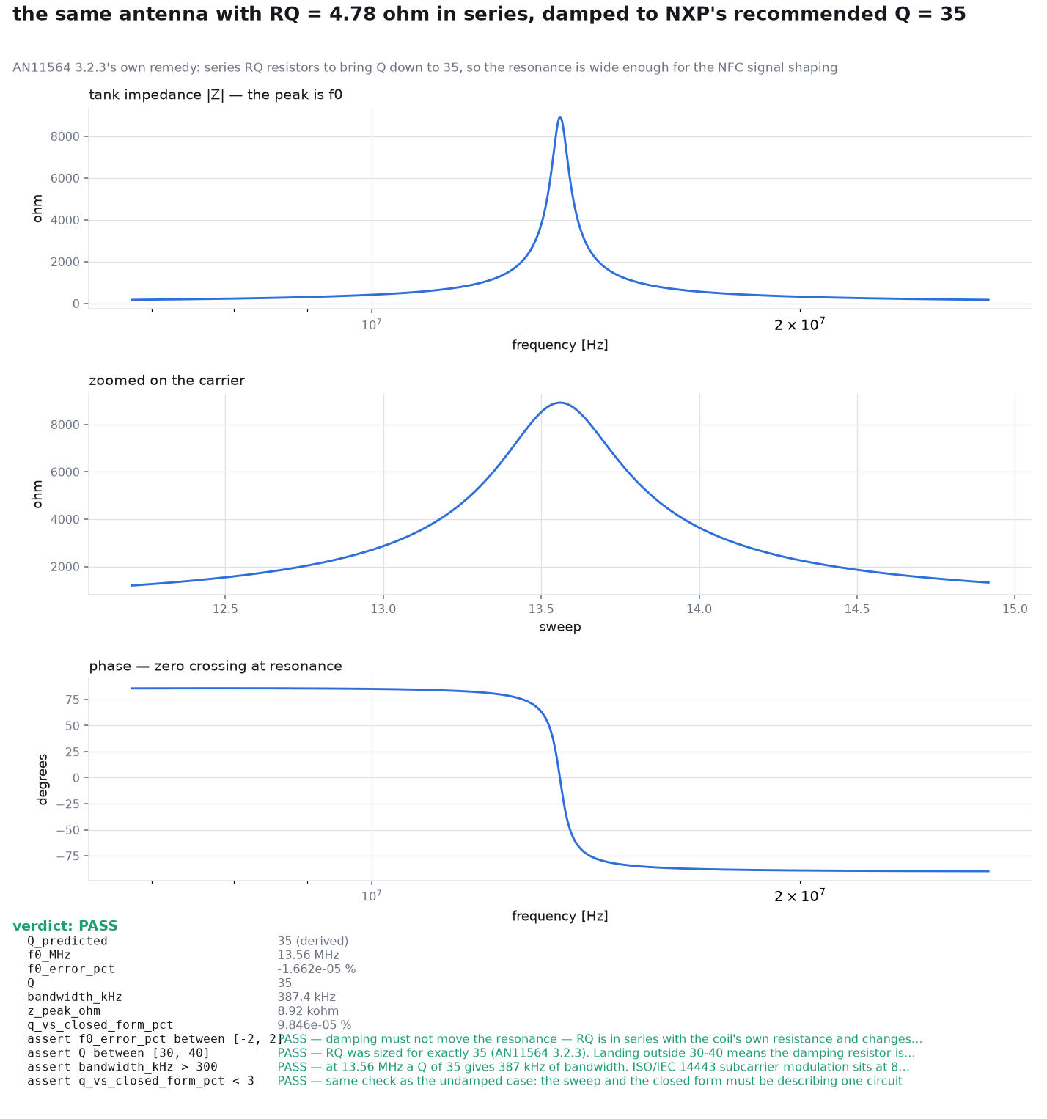
out/gallery/img/ce-spice-out-nfc_tank-damped-to-35.png
