Leif-Rydenfalk/halo/out/gallery/img/ce-spice-out-nfc_tank-detuned-10pct.png

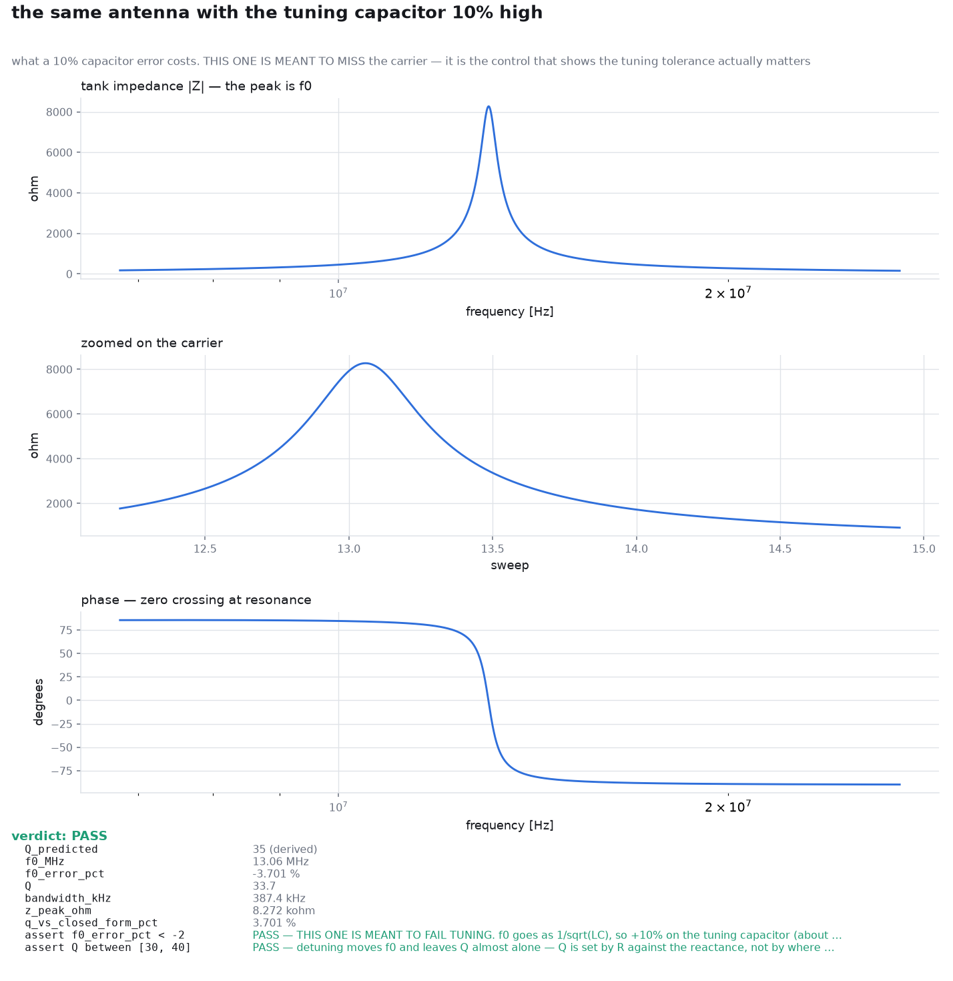
out/gallery/img/ce-spice-out-nfc_tank-detuned-10pct.png
