Leif-Rydenfalk/halo/out/gallery/img/ce-spice-out-speaker_hbridge-coil-32r-2m0h.png

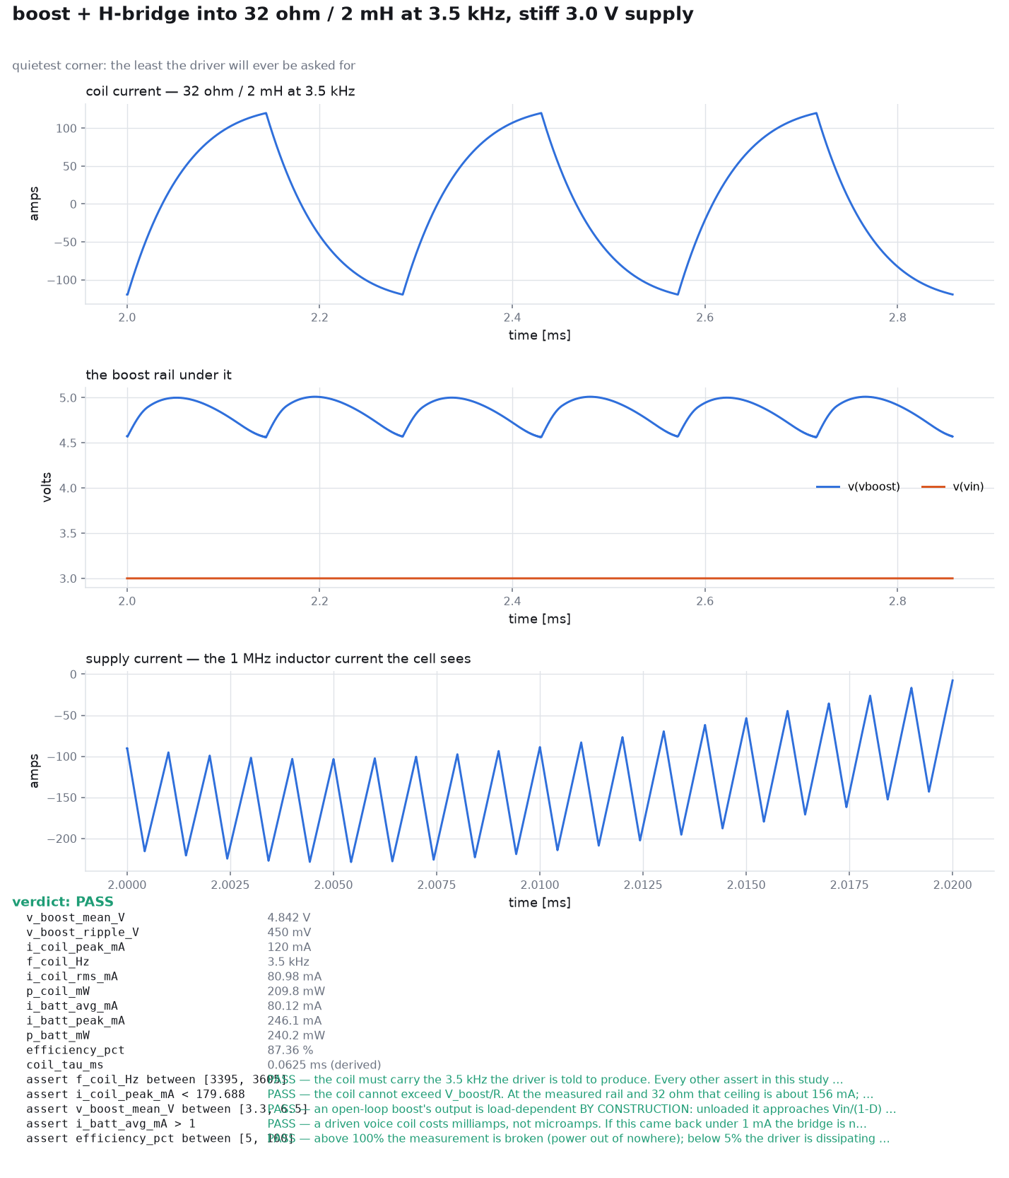
out/gallery/img/ce-spice-out-speaker_hbridge-coil-32r-2m0h.png
