Leif-Rydenfalk/halo/out/gallery/img/ce-spice-out-speaker_hbridge-cr2032-loaded.png

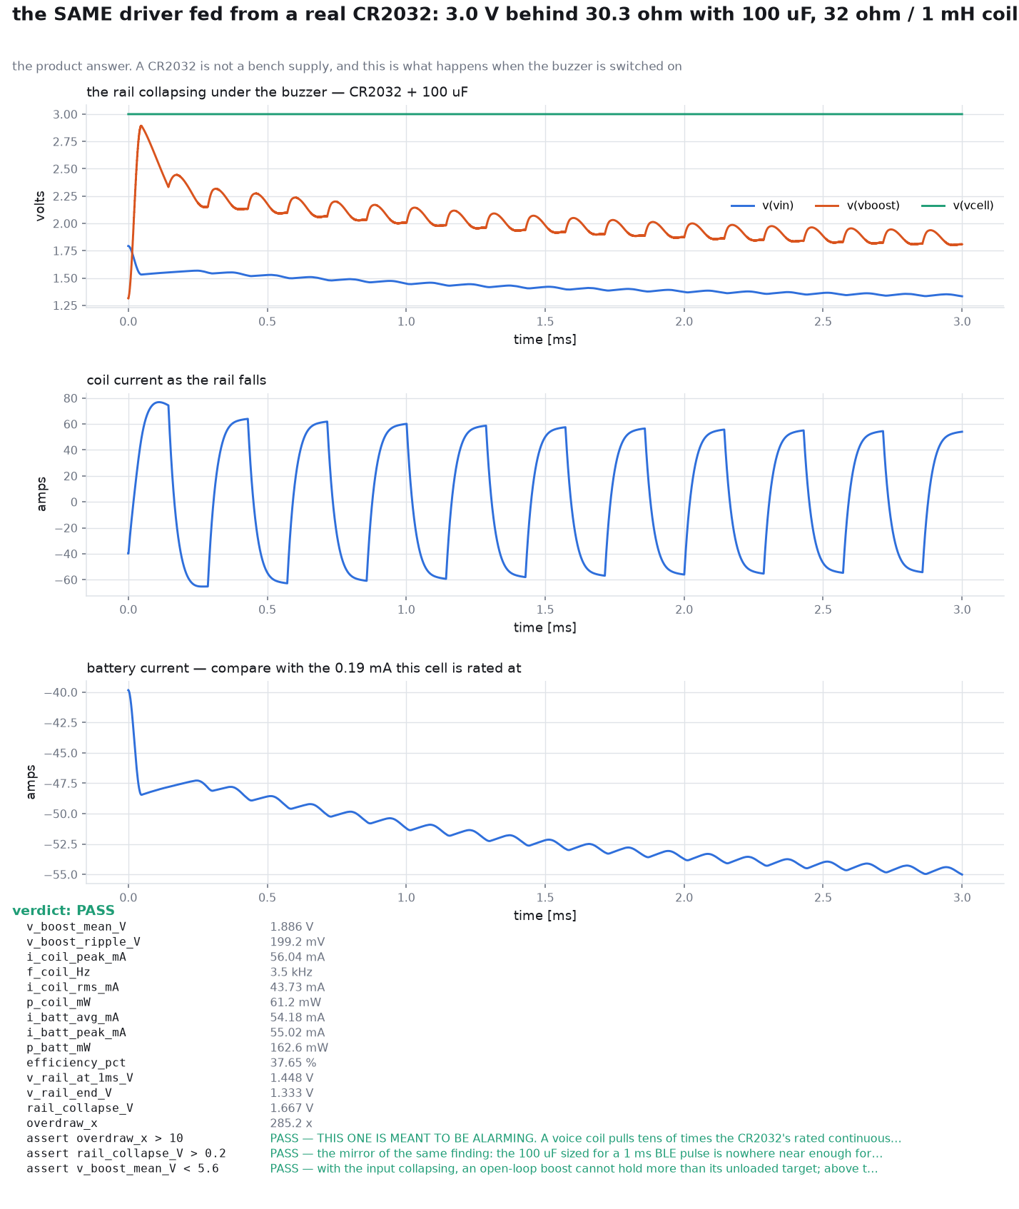
out/gallery/img/ce-spice-out-speaker_hbridge-cr2032-loaded.png
