Leif-Rydenfalk/halo/out/gallery/img/images-airtag-fcc-BCGA2187-internal-photo-1.jpg

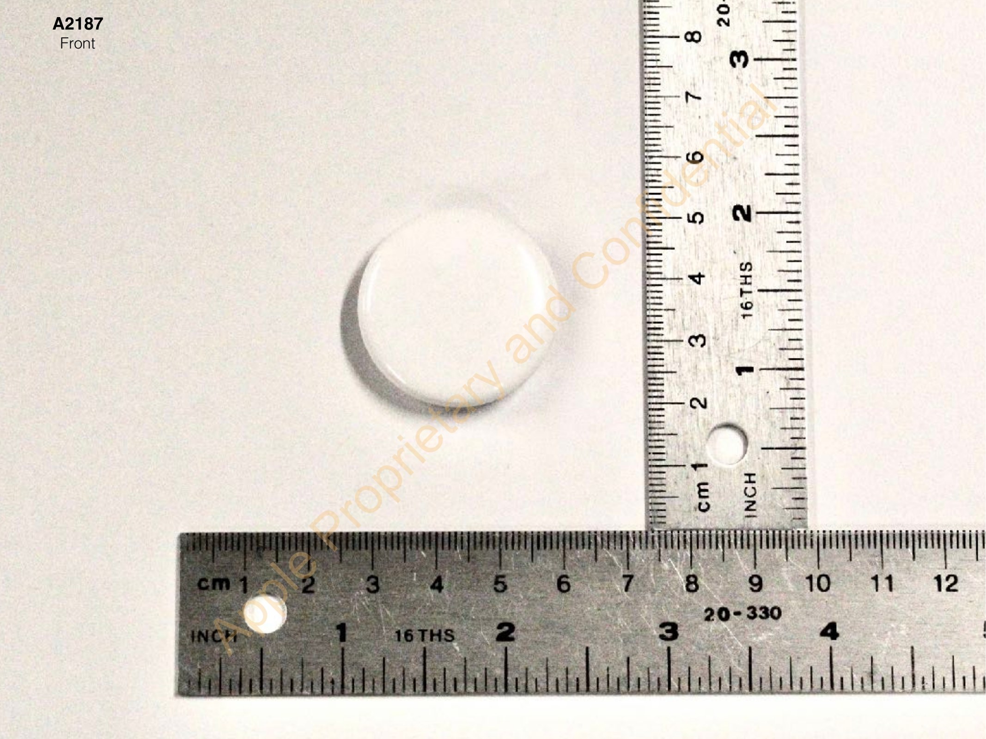
out/gallery/img/images-airtag-fcc-BCGA2187-internal-photo-1.jpg
