Leif-Rydenfalk/halo/out/gallery/img/images-airtag-fcc-BCGA2187-internal-photo-4.jpg

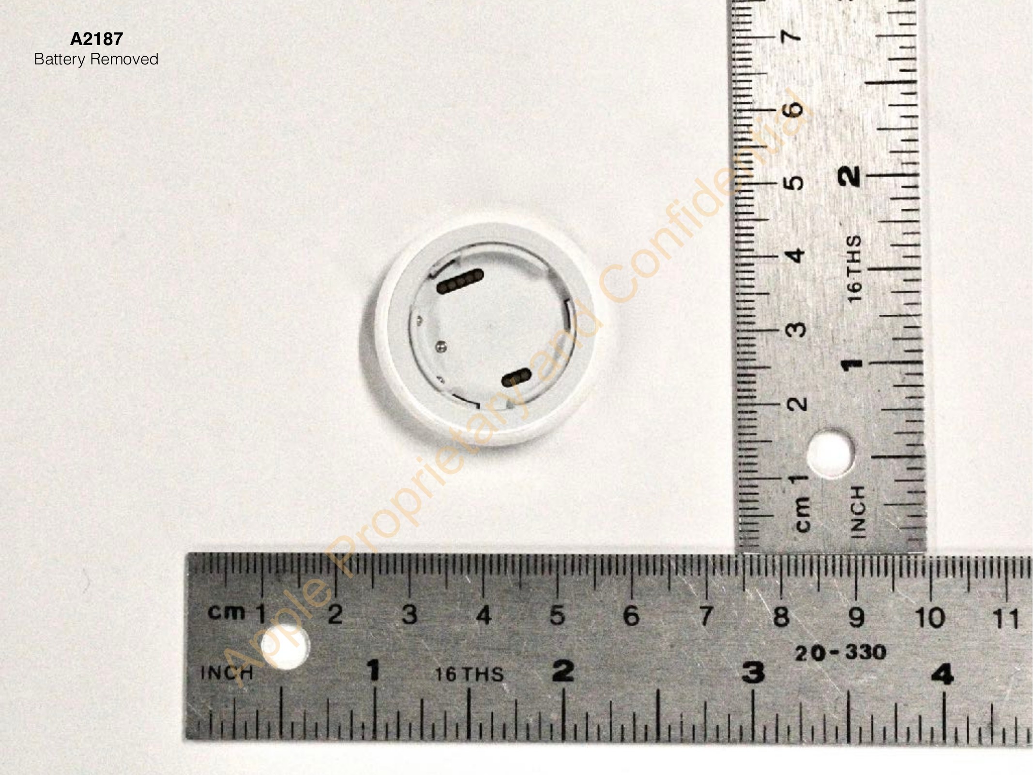
out/gallery/img/images-airtag-fcc-BCGA2187-internal-photo-4.jpg
