Leif-Rydenfalk/halo/out/gallery/img/out-gallery-fig-antenna-trajectory.png

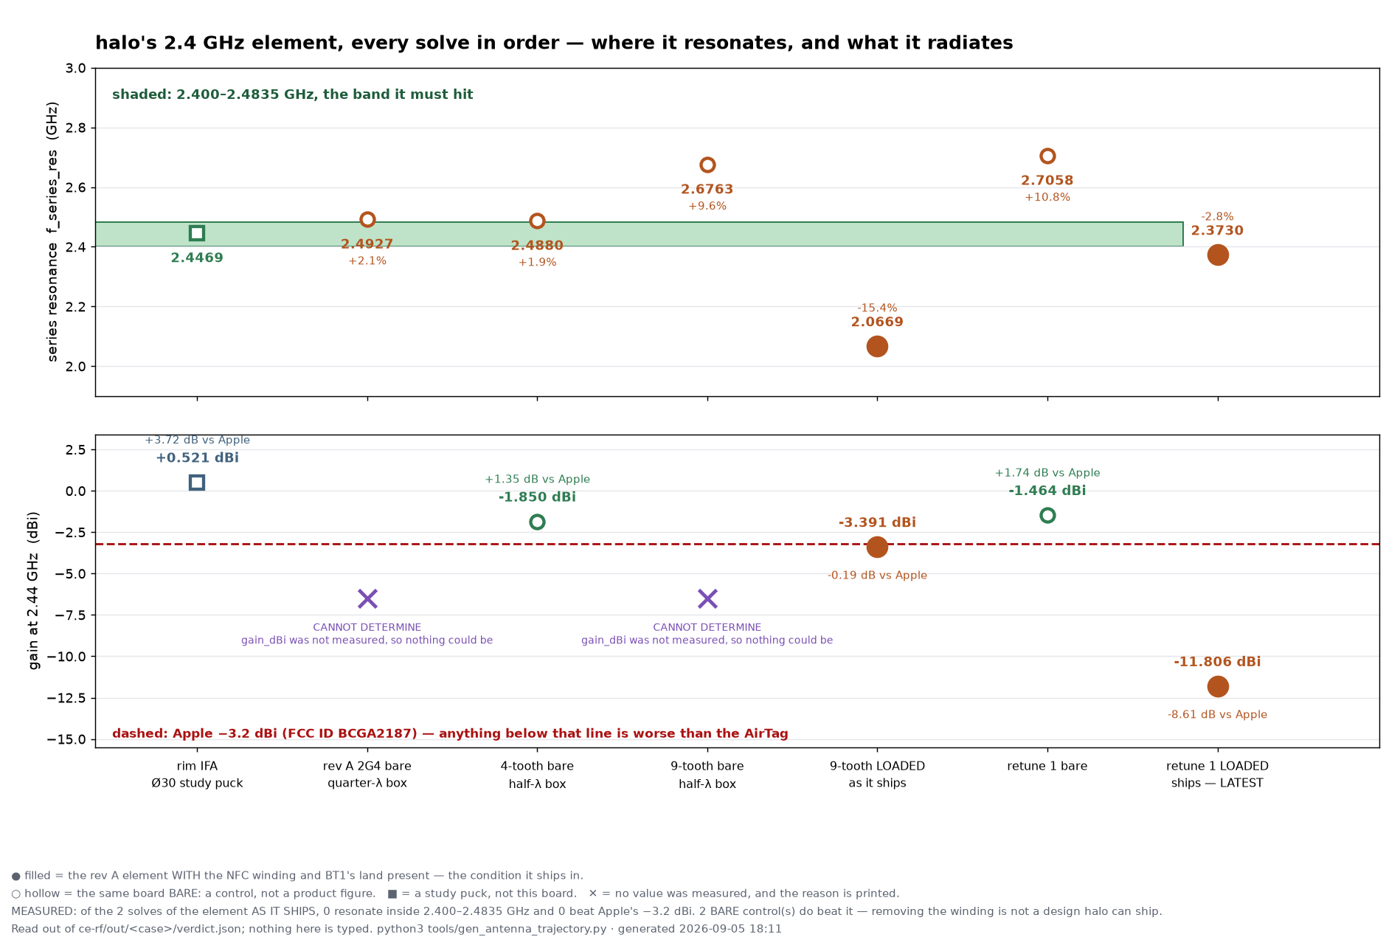
out/gallery/img/out-gallery-fig-antenna-trajectory.png
