Leif-Rydenfalk/halo/out/gallery/img/out-gallery-fig-halo-vs-airtag.png

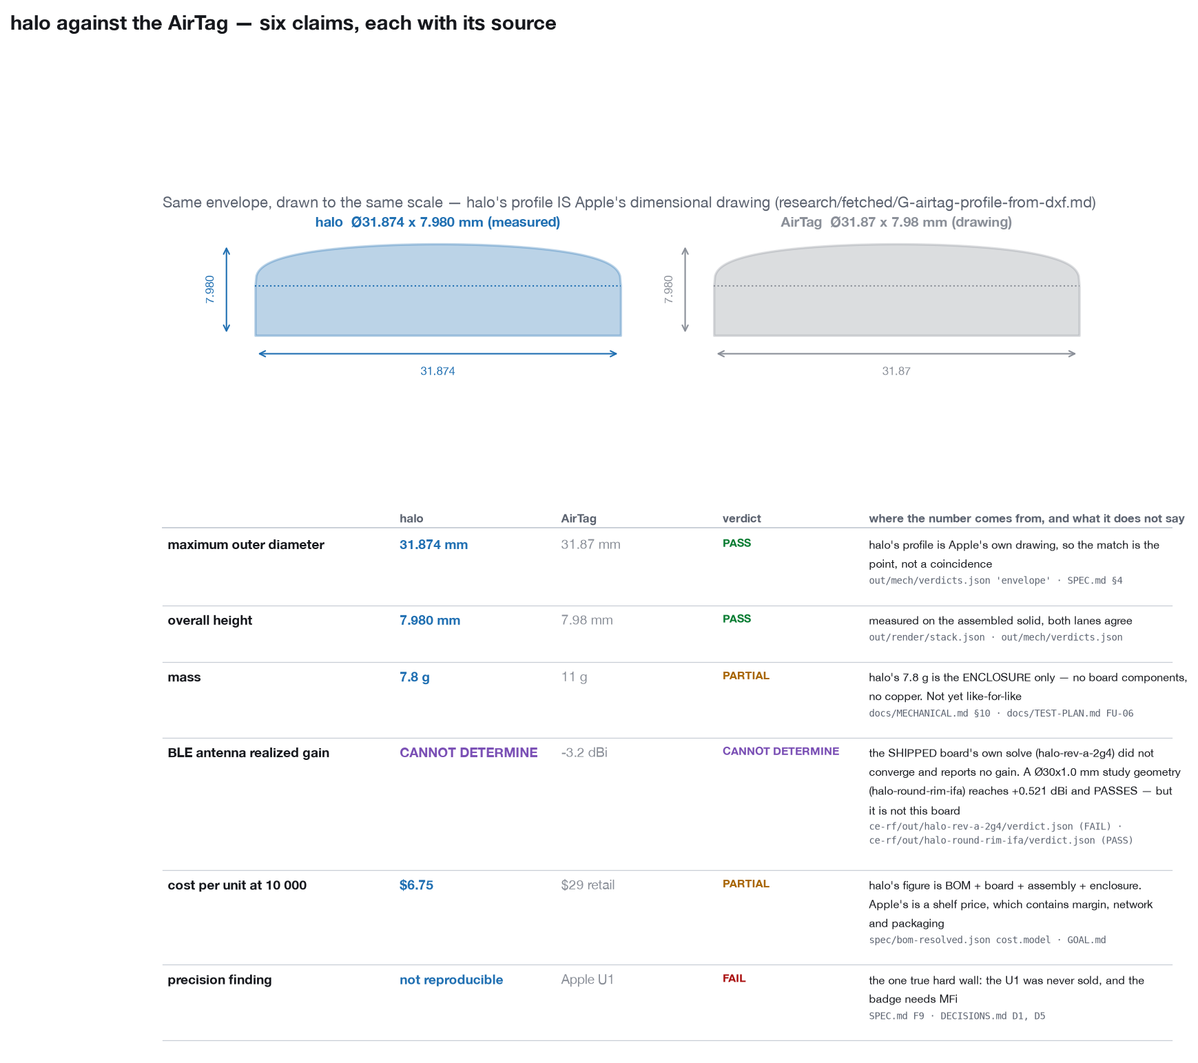
out/gallery/img/out-gallery-fig-halo-vs-airtag.png
