Leif-Rydenfalk/halo/out/gallery/img/out-gallery-fig-stack.png

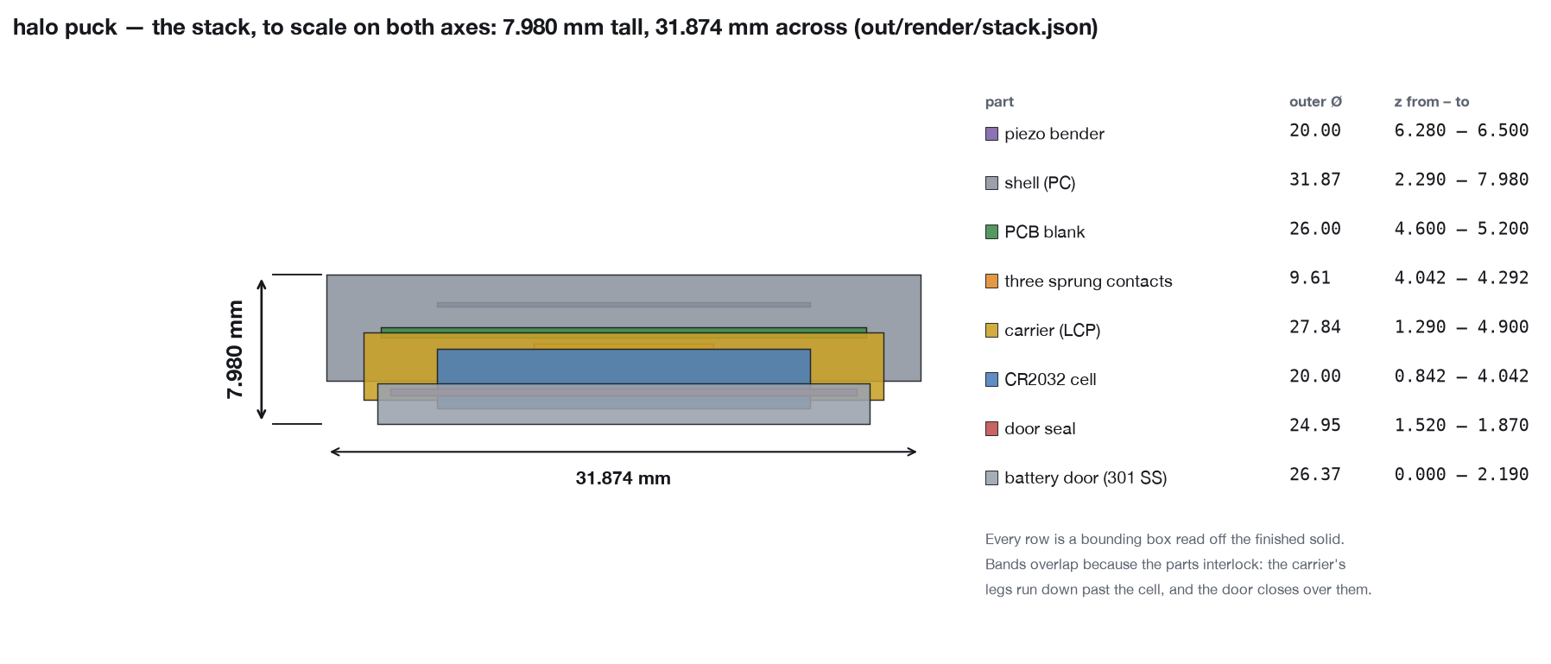
out/gallery/img/out-gallery-fig-stack.png
