Leif-Rydenfalk/halo/out/gallery/img/out-mech-halo-battery-contact-pos-a.png

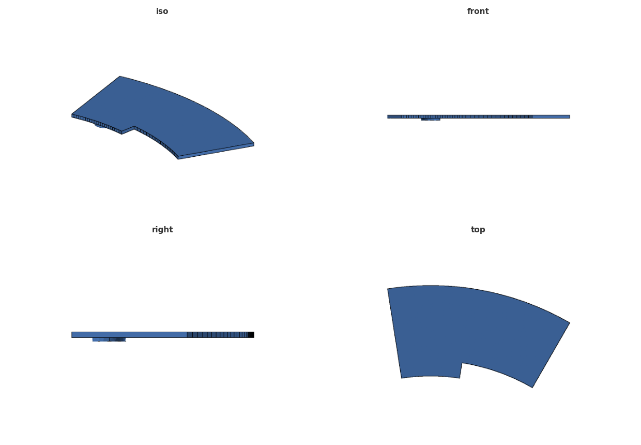
out/gallery/img/out-mech-halo-battery-contact-pos-a.png
