Leif-Rydenfalk/halo/out/gallery/img/out-mech-halo-battery-door.png

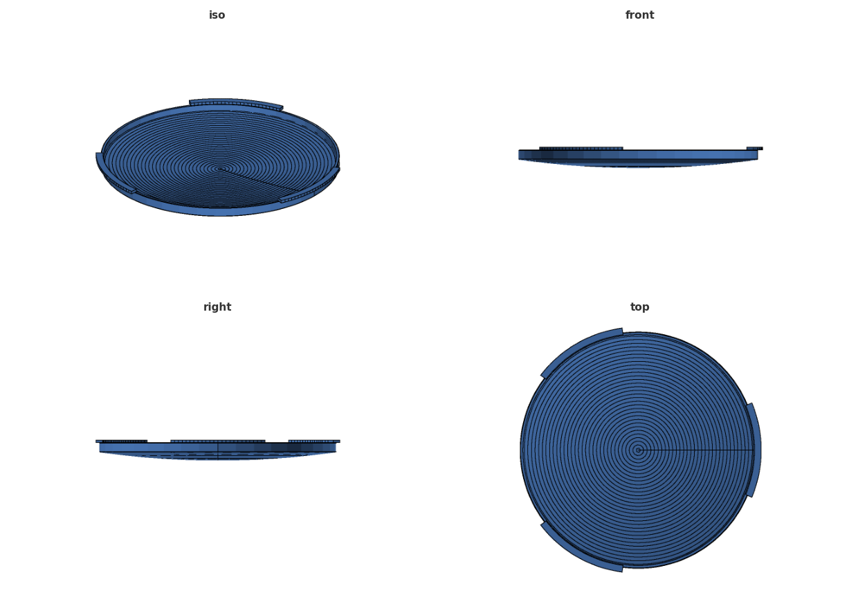
out/gallery/img/out-mech-halo-battery-door.png
