Leif-Rydenfalk/halo/out/gallery/img/out-mech-halo-carrier.png

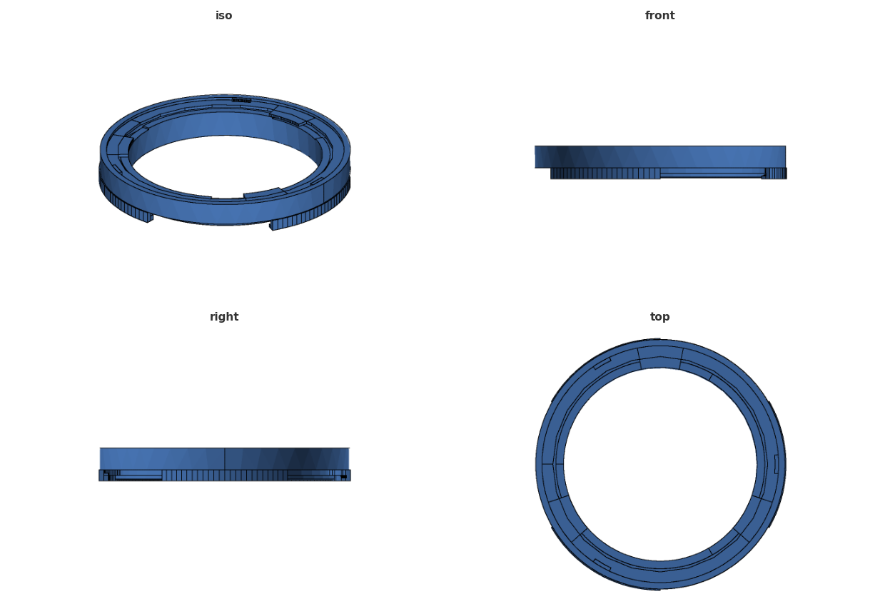
out/gallery/img/out-mech-halo-carrier.png
