Leif-Rydenfalk/halo/out/gallery/img/out-mech-halo-pcb-blank.png

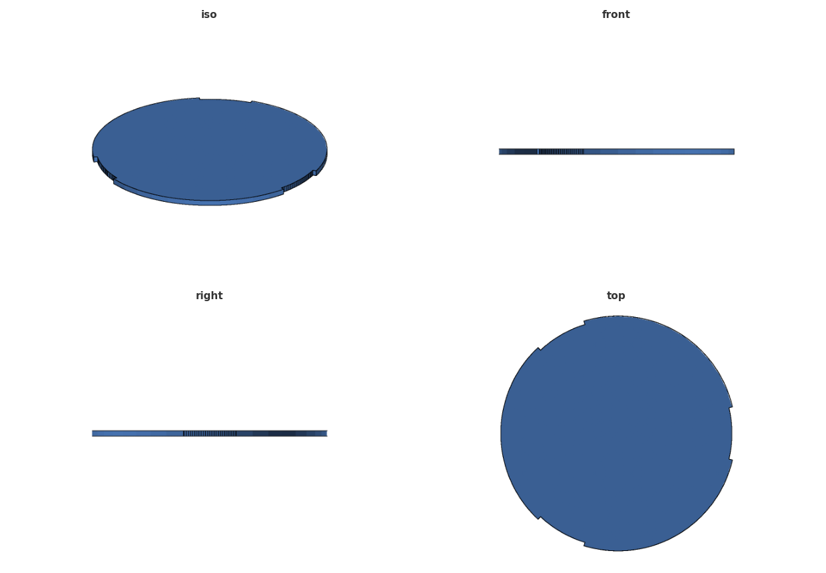
out/gallery/img/out-mech-halo-pcb-blank.png
