Leif-Rydenfalk/halo/out/gallery/img/out-mech-halo-puck-iso.png

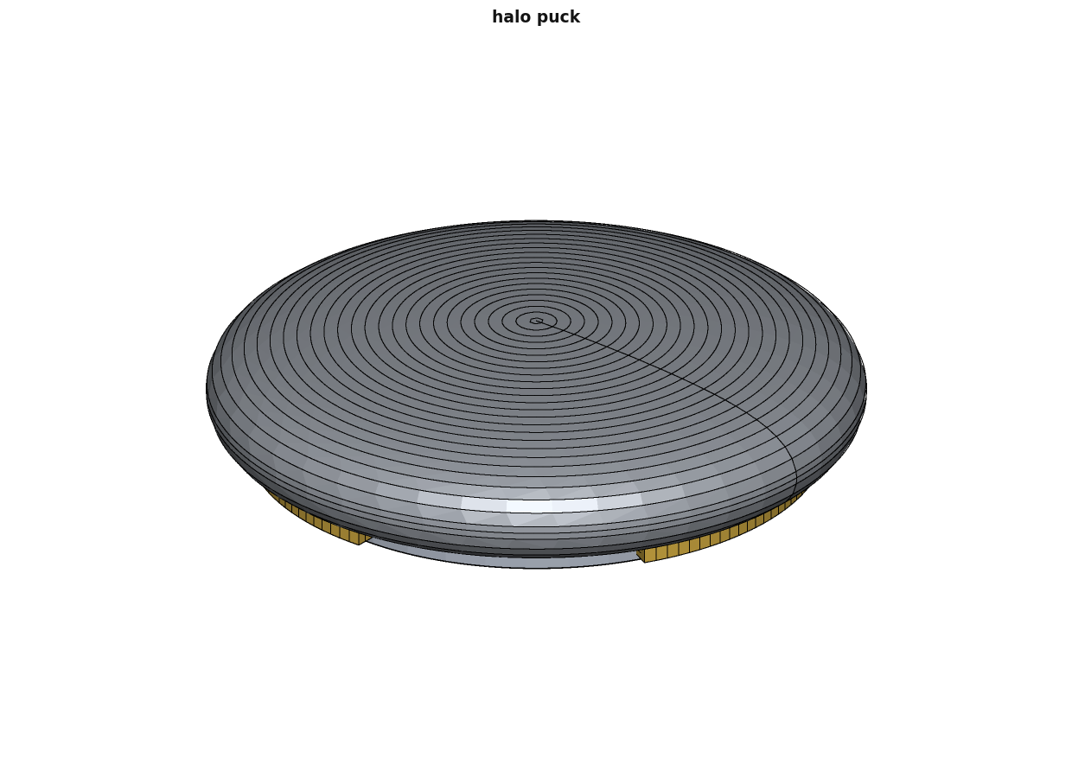
out/gallery/img/out-mech-halo-puck-iso.png
