Leif-Rydenfalk/halo/out/gallery/img/out-mech-halo-puck-section-front.png

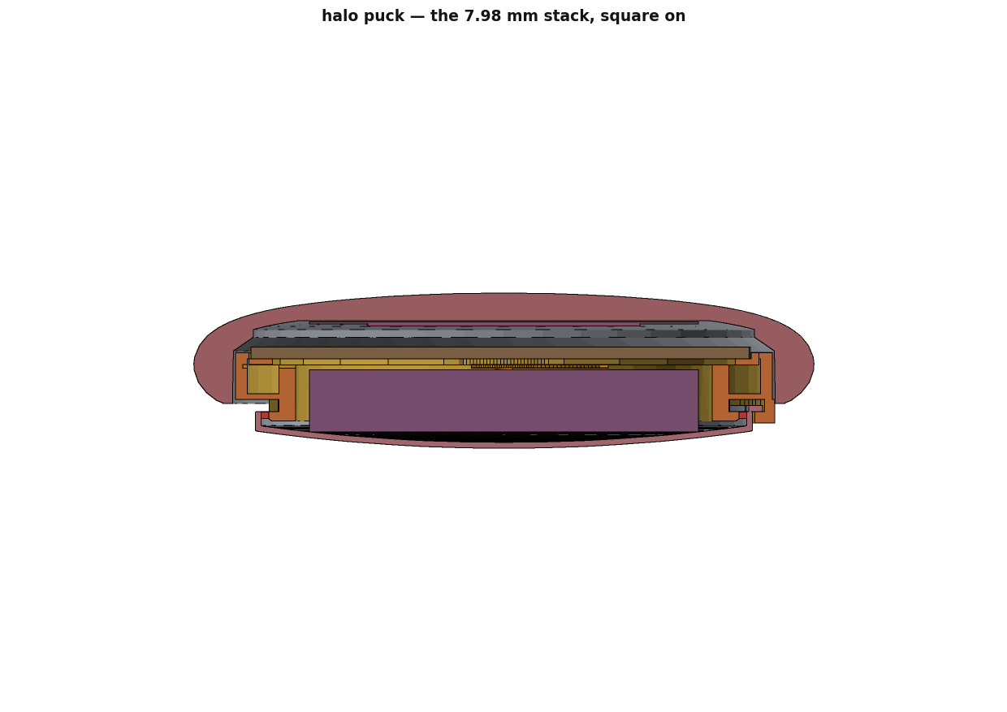
out/gallery/img/out-mech-halo-puck-section-front.png
