Leif-Rydenfalk/halo/out/gallery/img/out-mech-halo-puck-section.png

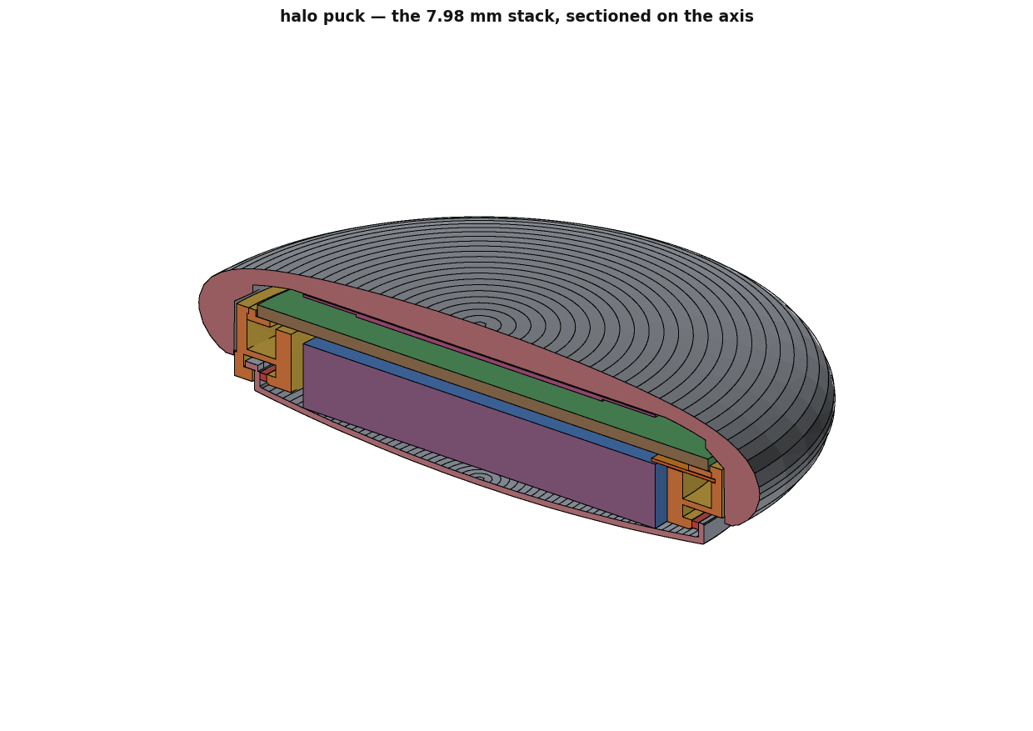
out/gallery/img/out-mech-halo-puck-section.png
