Leif-Rydenfalk/halo/out/gallery/img/out-render-halo-bayonet-section.png

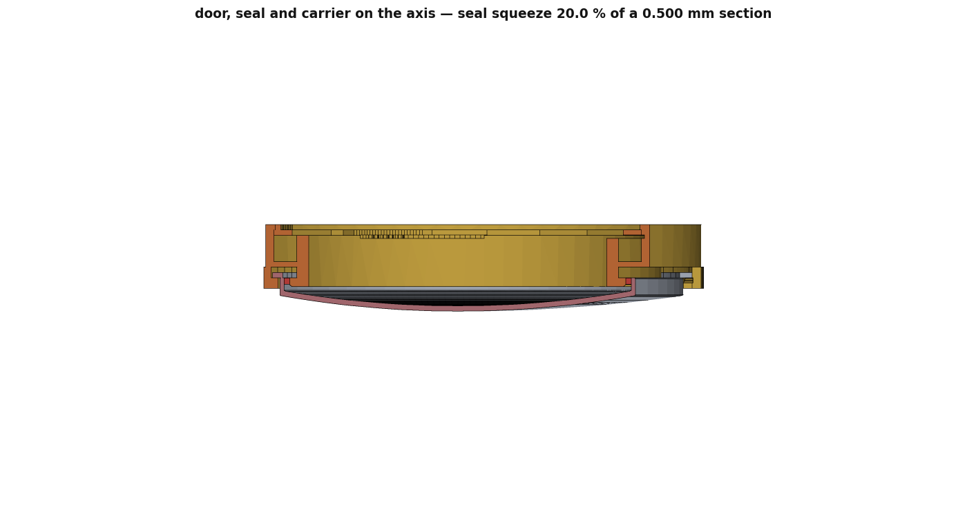
out/gallery/img/out-render-halo-bayonet-section.png
