Leif-Rydenfalk/halo/out/gallery/img/out-render-halo-bayonet.png

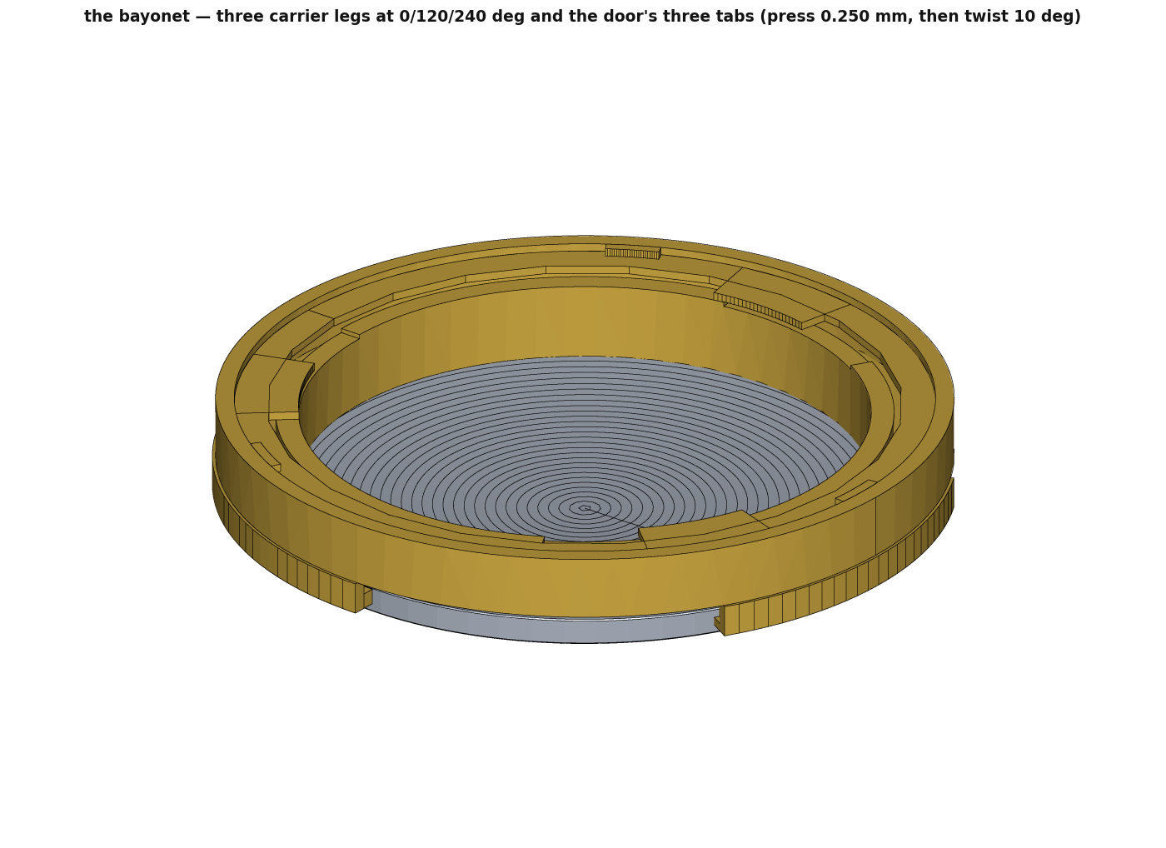
out/gallery/img/out-render-halo-bayonet.png
