Leif-Rydenfalk/halo/out/gallery/img/out-render-halo-board-in-shell.png

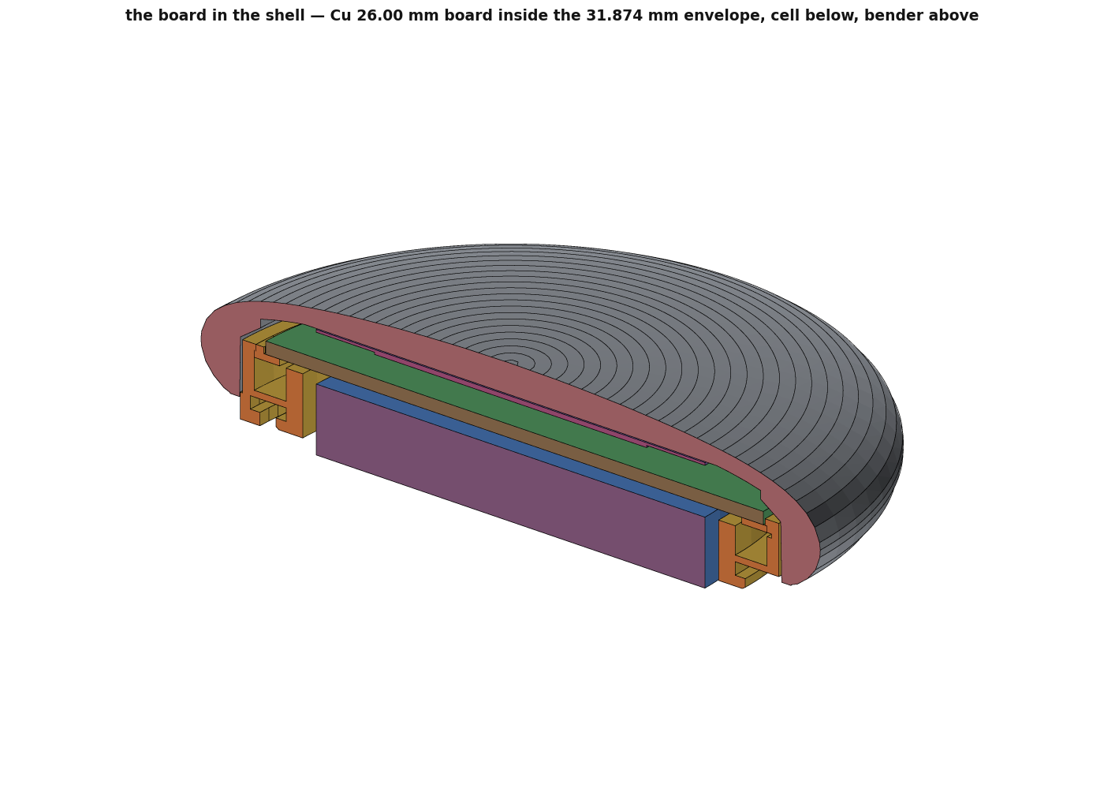
out/gallery/img/out-render-halo-board-in-shell.png
