Leif-Rydenfalk/halo/out/gallery/img/out-render-halo-contacts.png

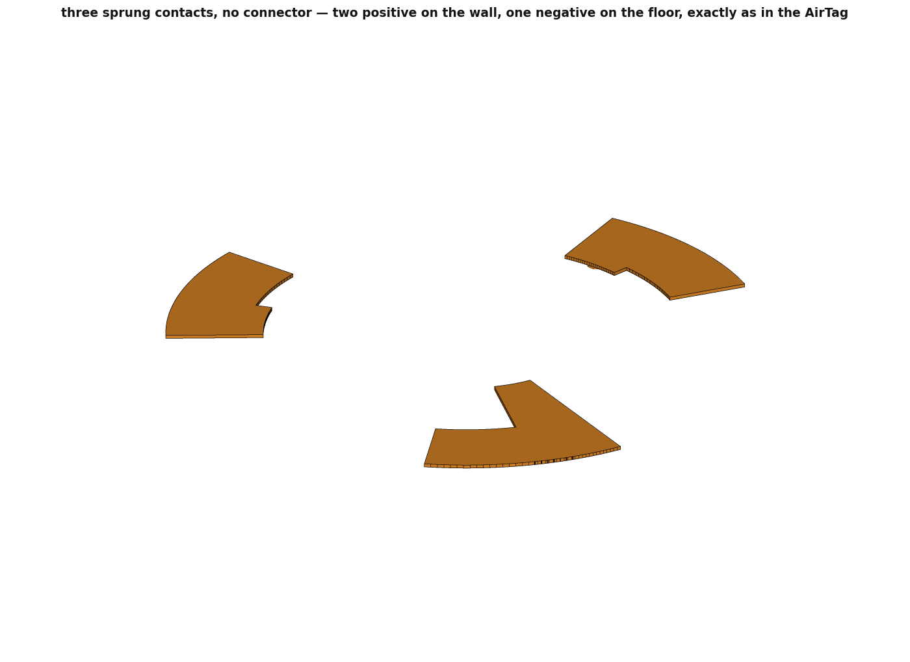
out/gallery/img/out-render-halo-contacts.png
