Leif-Rydenfalk/halo/out/gallery/img/out-render-halo-piezo-land.png

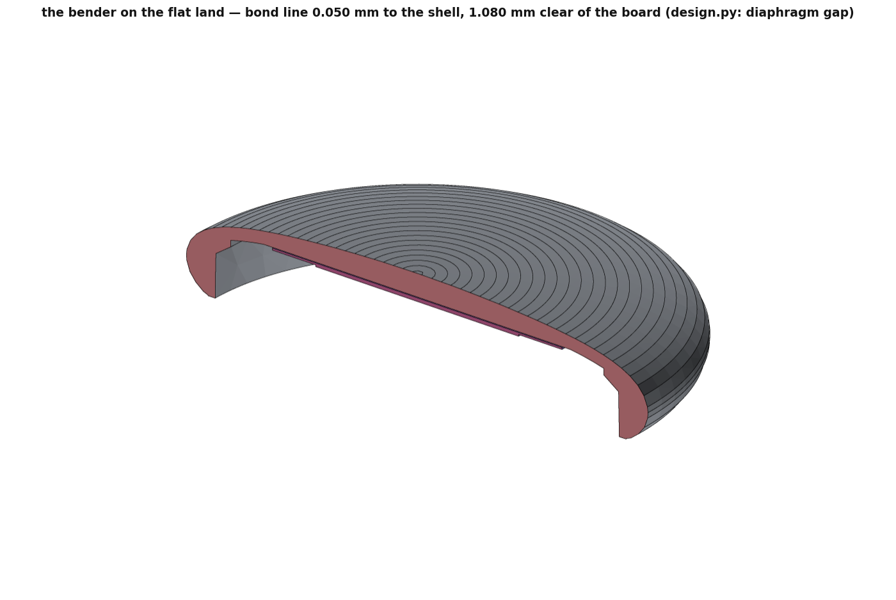
out/gallery/img/out-render-halo-piezo-land.png
