Leif-Rydenfalk/halo/out/gallery/img/out-render-halo-puck-exploded-wide.png

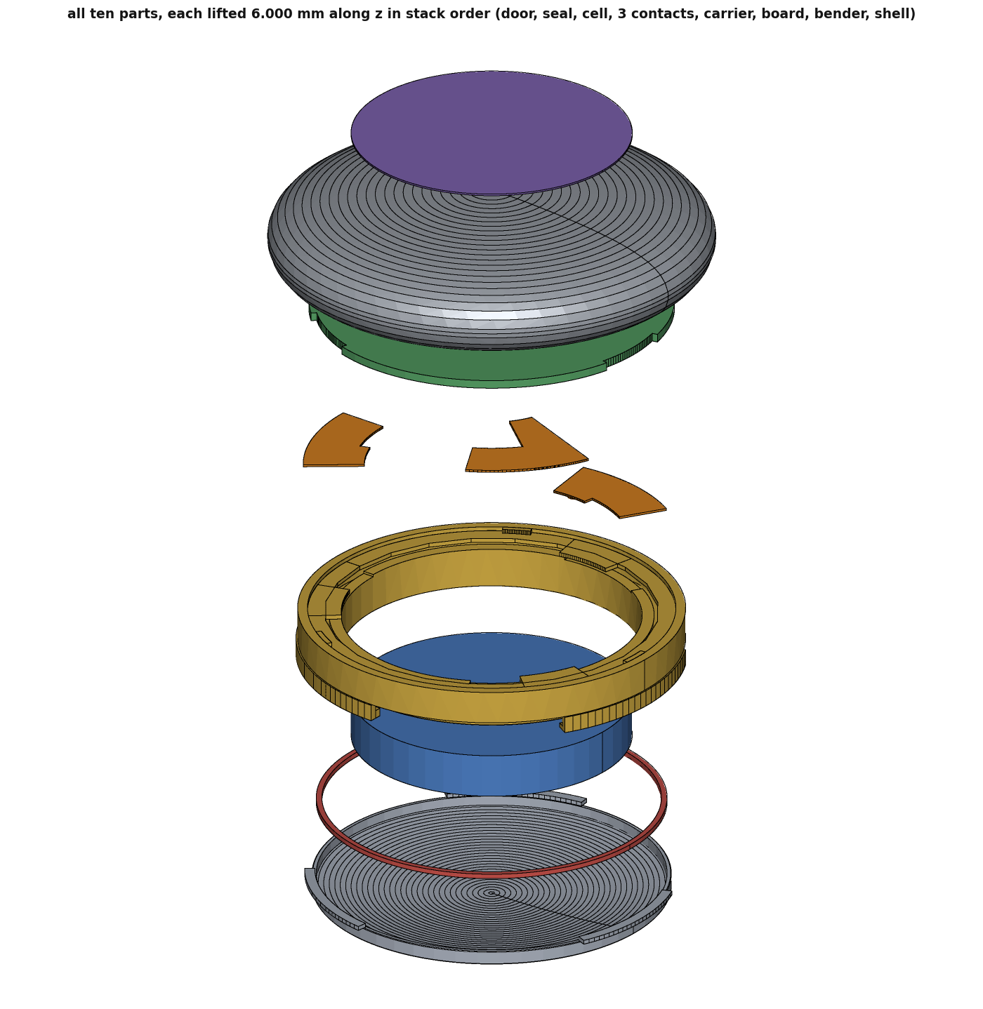
out/gallery/img/out-render-halo-puck-exploded-wide.png
