Leif-Rydenfalk/halo/out/gallery/img/out-render-halo-puck-hero.png

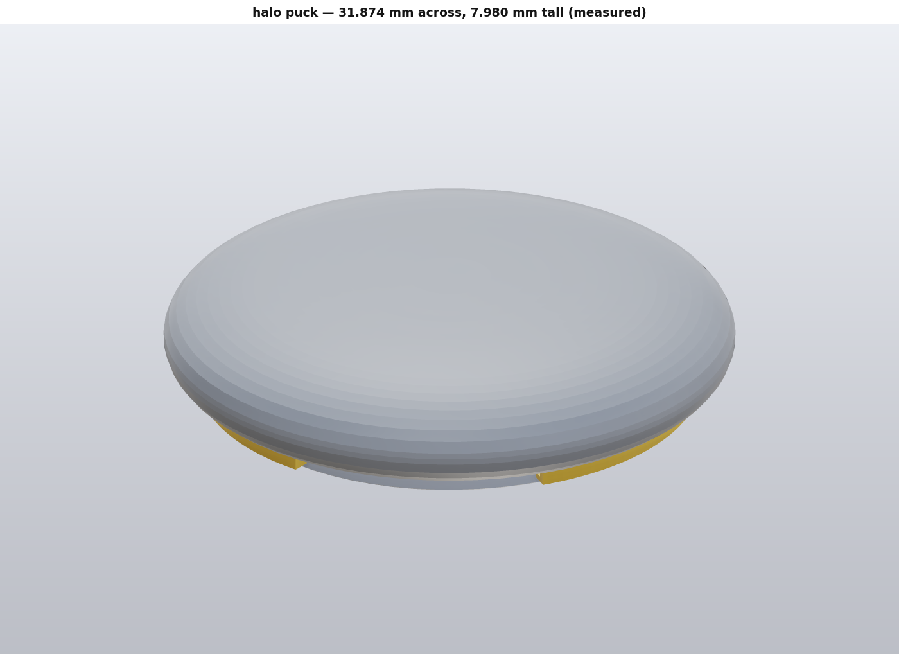
out/gallery/img/out-render-halo-puck-hero.png
