Leif-Rydenfalk/halo/out/gallery/img/out-render-halo_rev_a-bottom.png

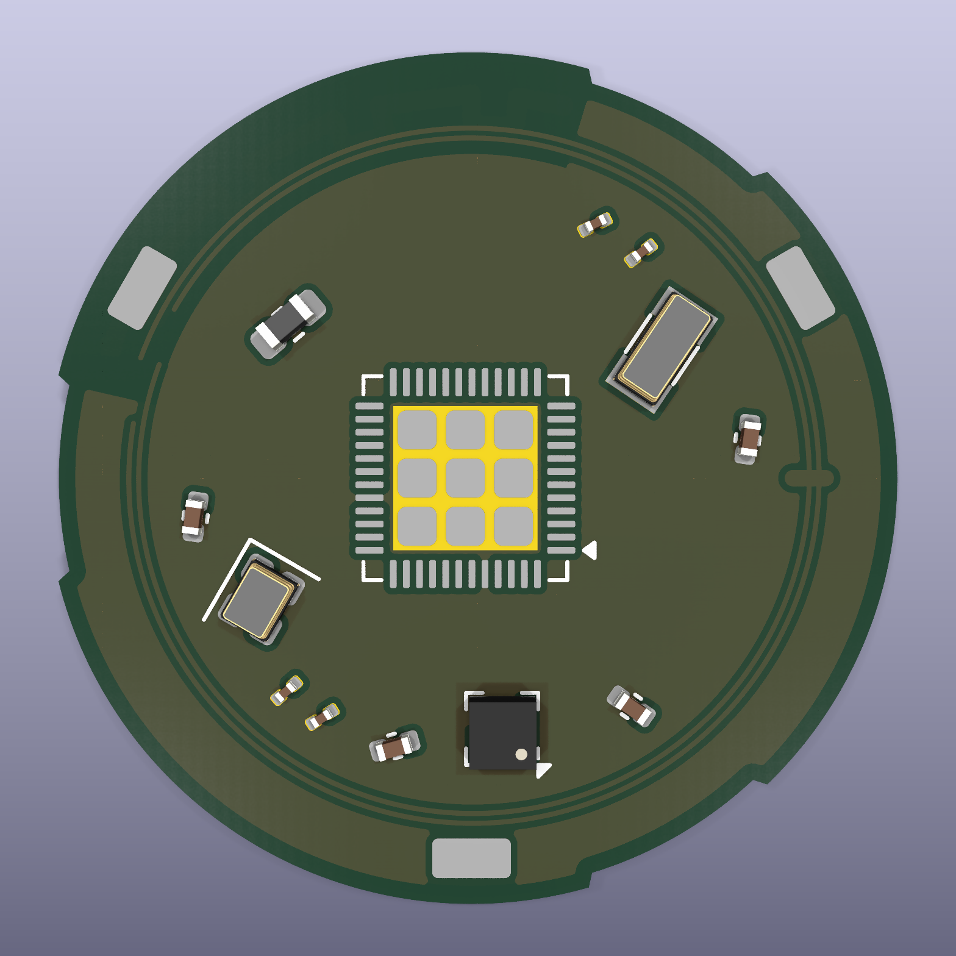
out/gallery/img/out-render-halo_rev_a-bottom.png
