Leif-Rydenfalk/halo/out/gallery/img/out-render-halo_rev_a-routed-bottom.png

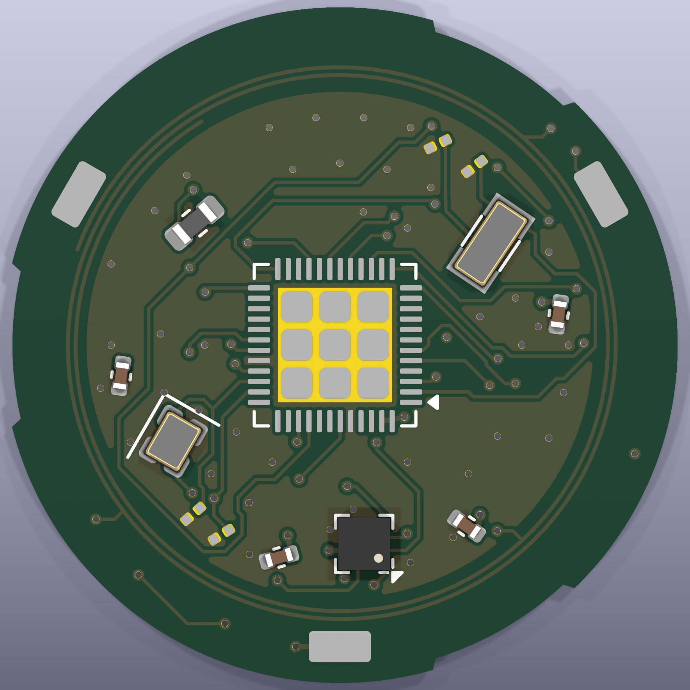
out/gallery/img/out-render-halo_rev_a-routed-bottom.png
