Leif-Rydenfalk/halo/out/gallery/img/out-render-halo_rev_a-routed-iso.png

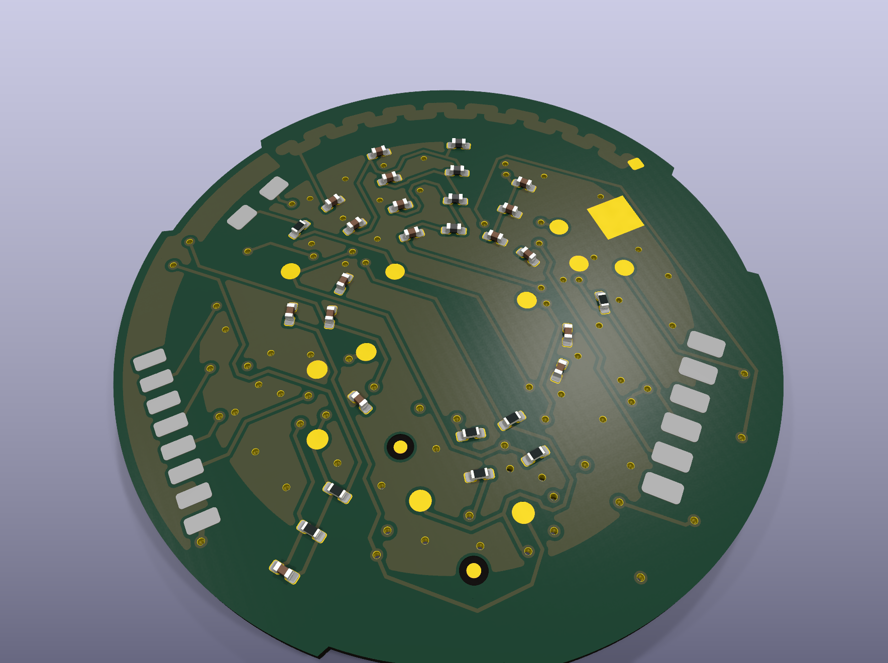
out/gallery/img/out-render-halo_rev_a-routed-iso.png
