Leif-Rydenfalk/halo/out/gallery/img/out-render-halo_rev_a-routed-top.png

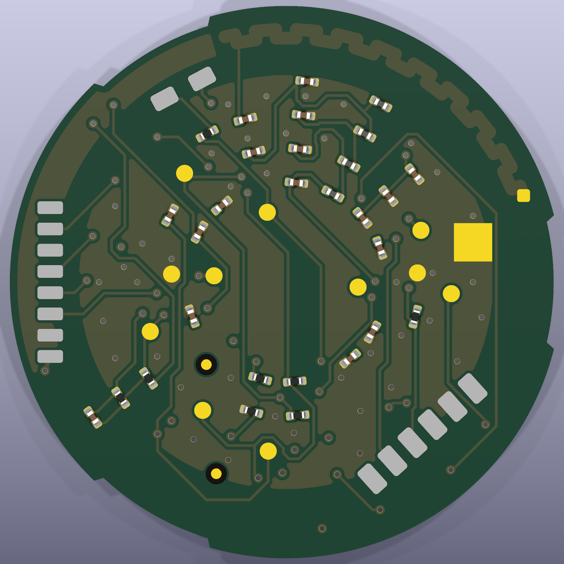
out/gallery/img/out-render-halo_rev_a-routed-top.png
