Leif-Rydenfalk/halo/out/gallery/img/out-render-halo_rev_a-top.png

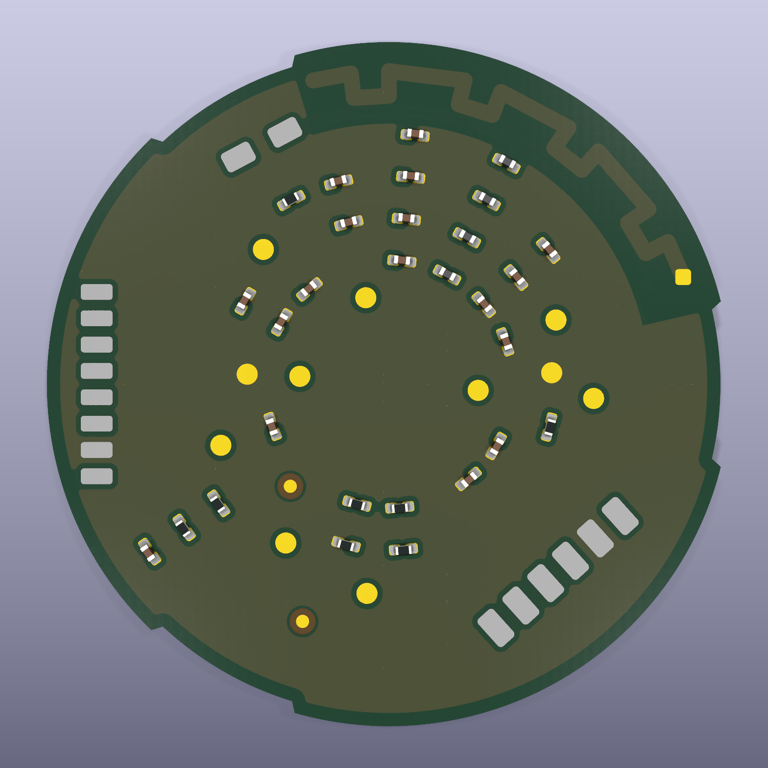
out/gallery/img/out-render-halo_rev_a-top.png
