Leif-Rydenfalk/halo/out/gallery/img/out-render-halo_rev_a-unrouted-top.png

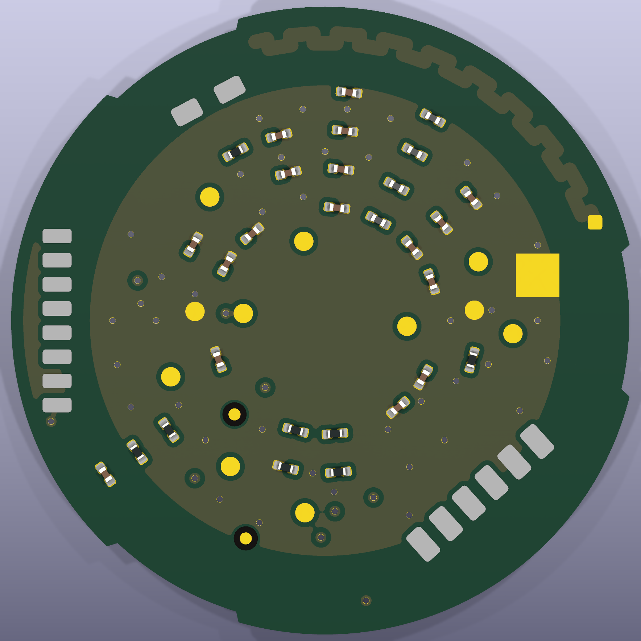
out/gallery/img/out-render-halo_rev_a-unrouted-top.png
