Leif-Rydenfalk/halo/out/mech/halo-puck-exploded.png

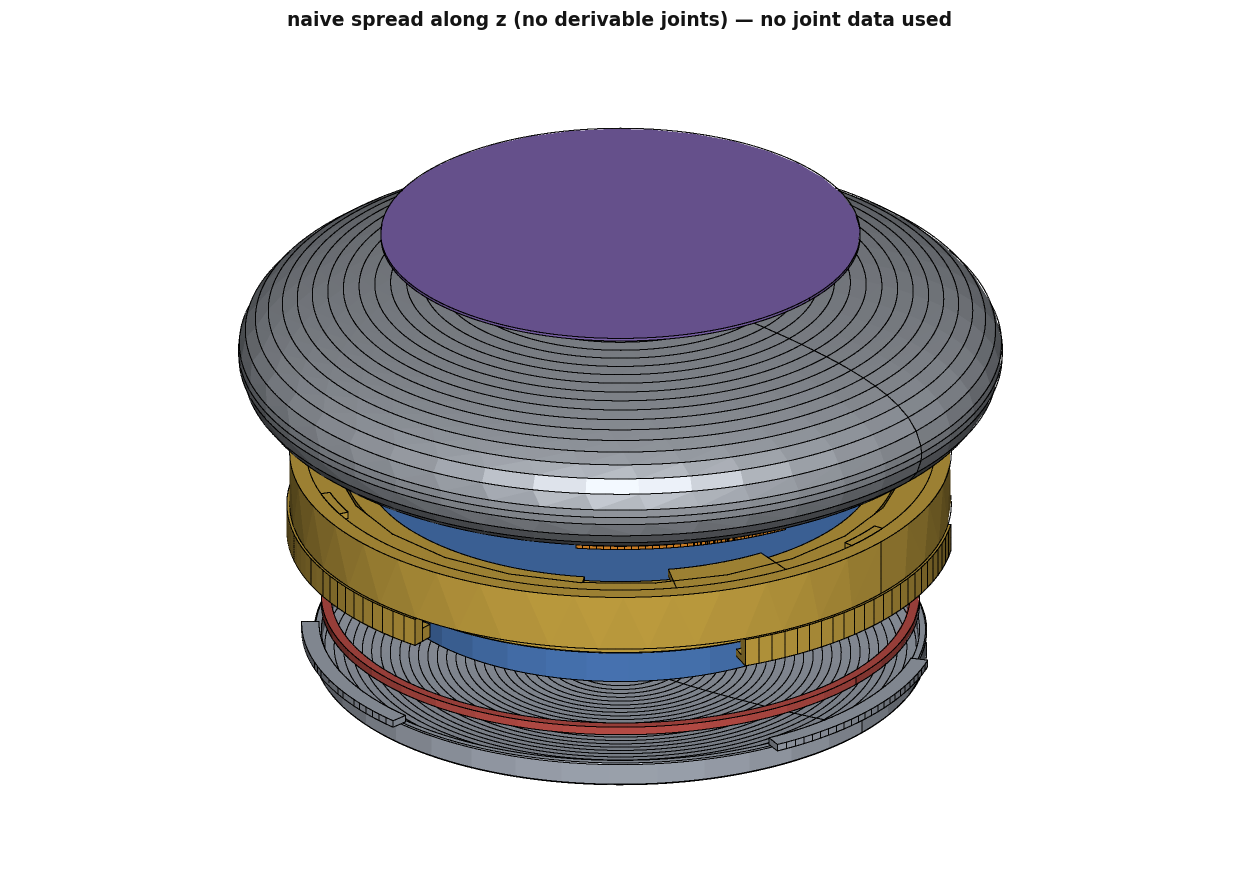
out/mech/halo-puck-exploded.png
