Leif-Rydenfalk/halo/out/mech/halo-puck-section-quarter.png

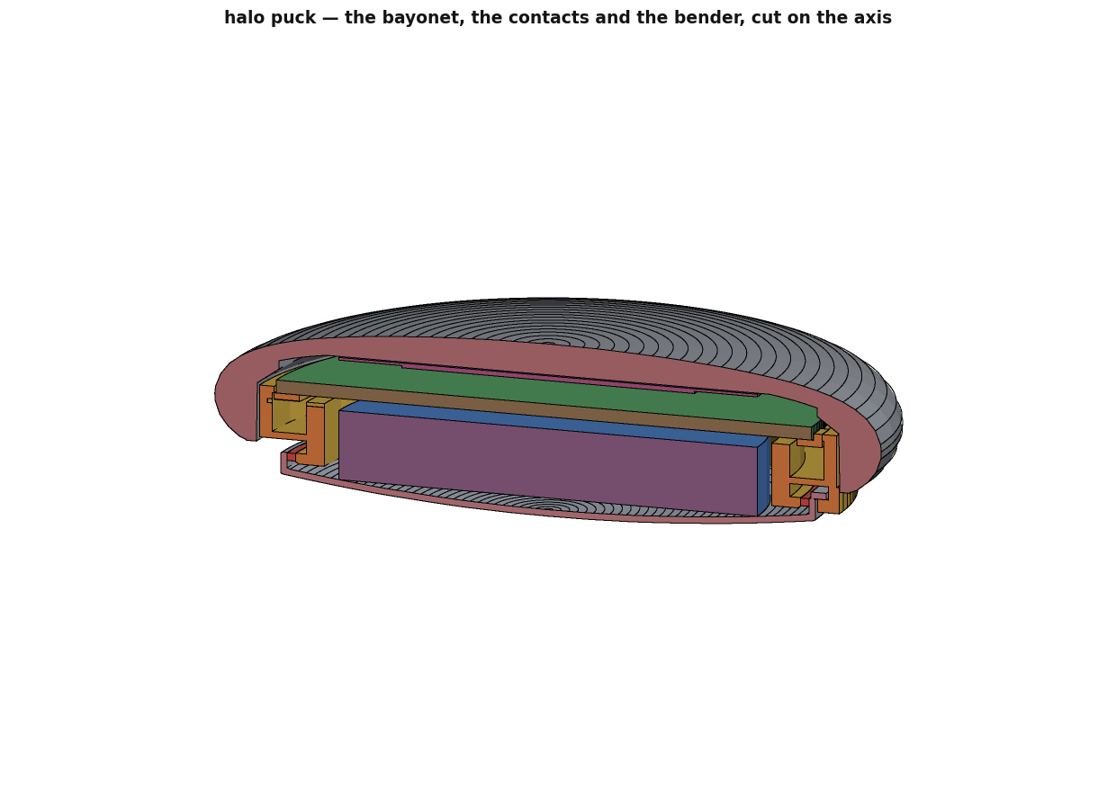
out/mech/halo-puck-section-quarter.png
