Leif-Rydenfalk/halo/out/release/board/sim/rail_droop/rail_droop_end_of_life.png

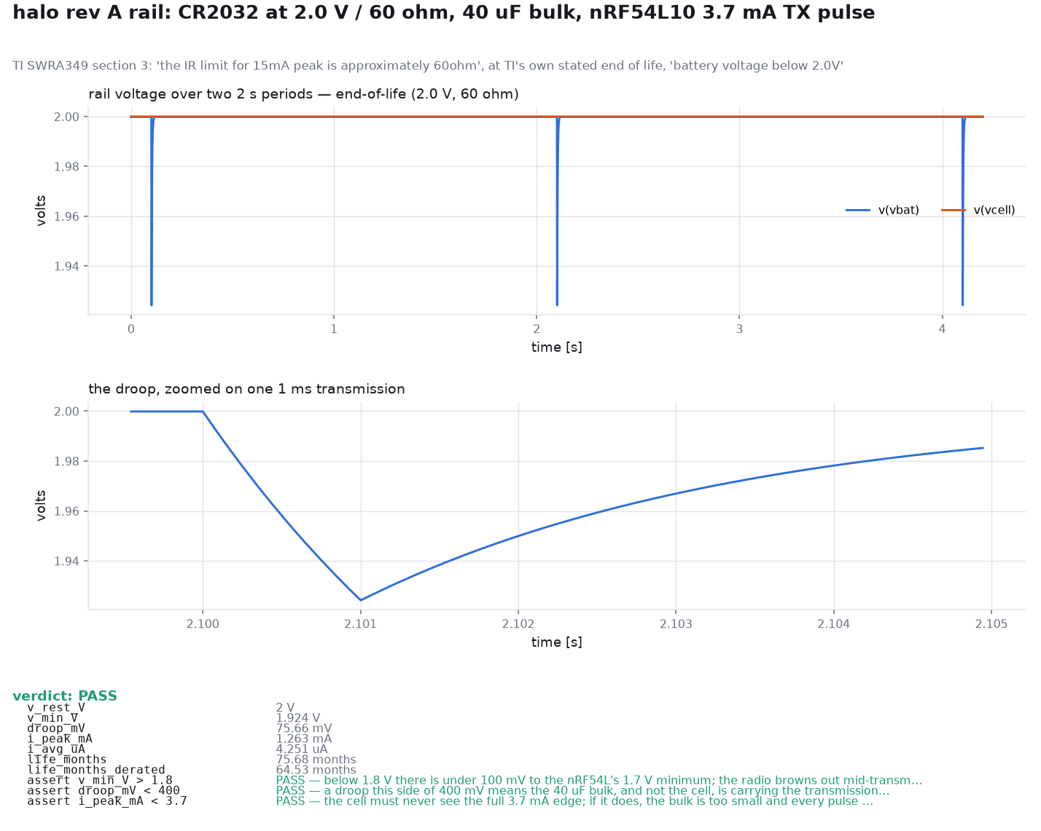
out/release/board/sim/rail_droop/rail_droop_end_of_life.png
