Leif-Rydenfalk/halo/out/release/board/sim/rail_droop/rail_droop_fresh.png

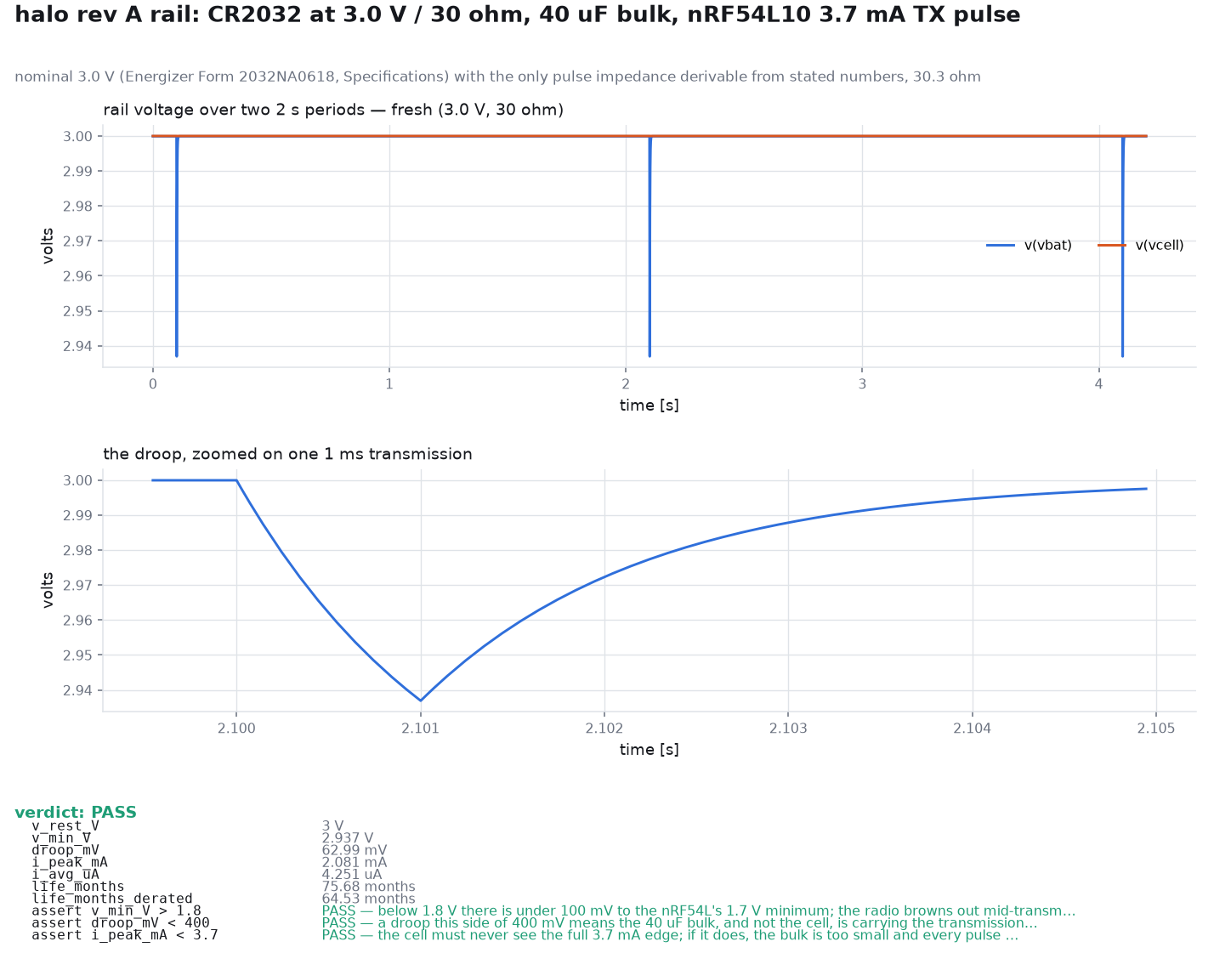
out/release/board/sim/rail_droop/rail_droop_fresh.png
