Leif-Rydenfalk/halo/out/release/board/sim/rail_droop/rail_droop_holdup.png

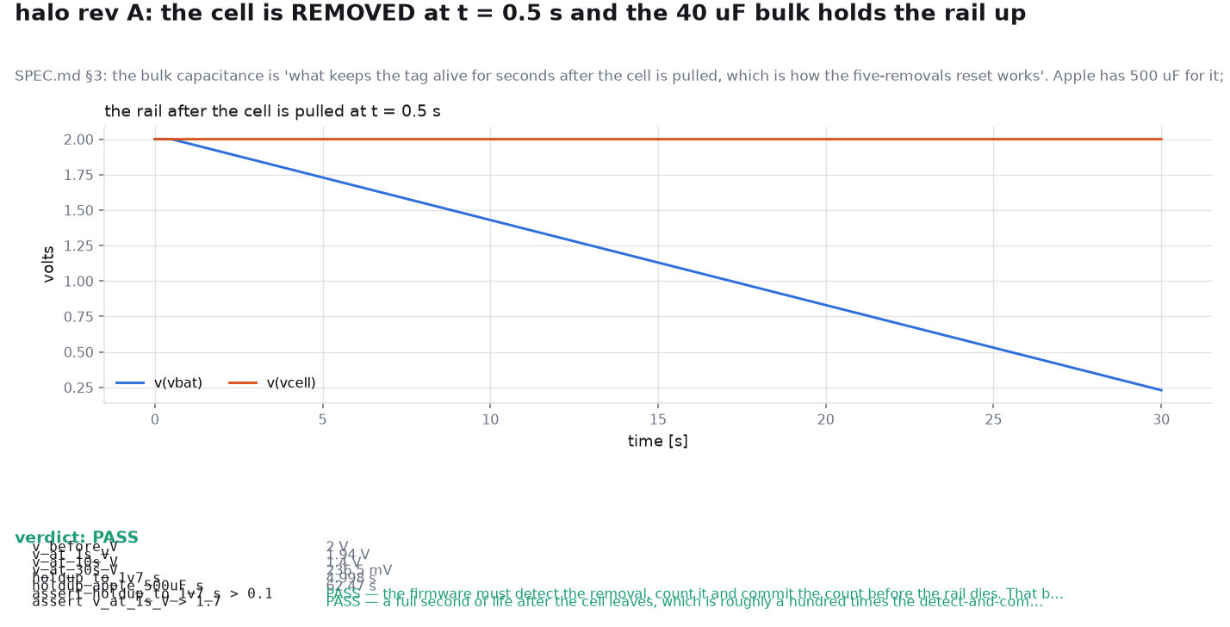
out/release/board/sim/rail_droop/rail_droop_holdup.png
