Leif-Rydenfalk/halo/out/release/board/sim/rail_droop/rail_droop_worst_case.png

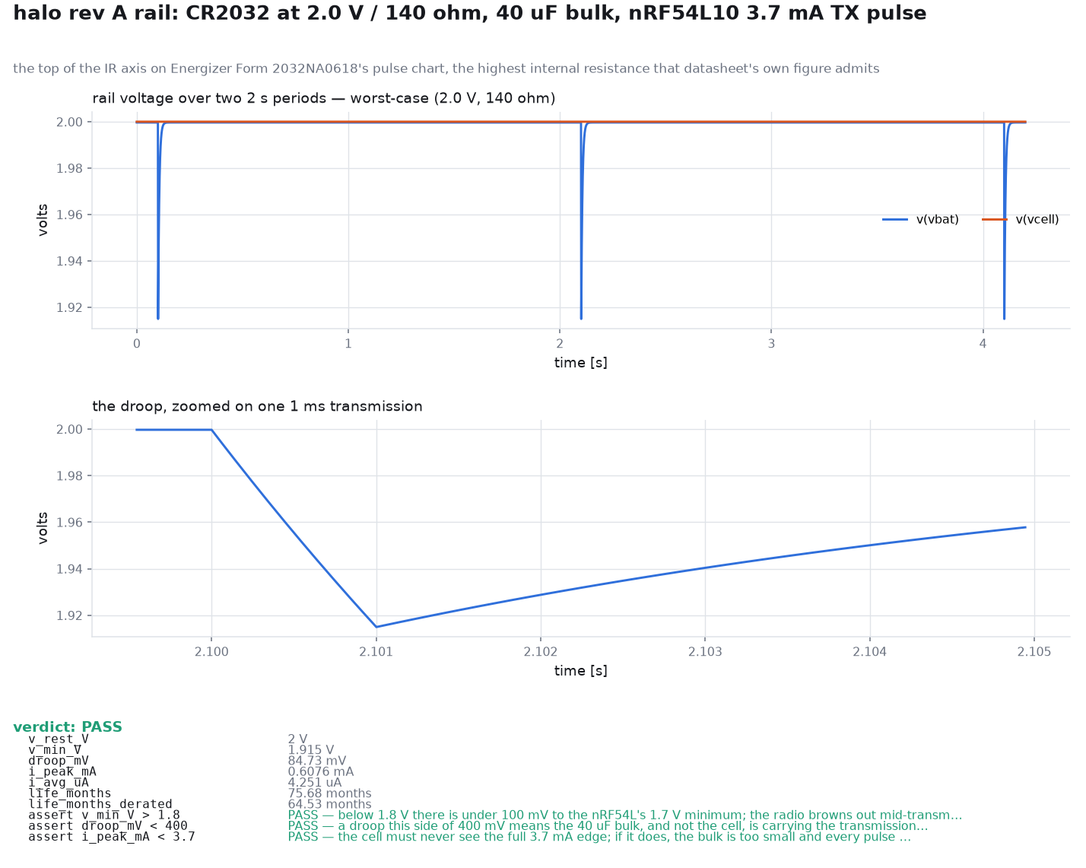
out/release/board/sim/rail_droop/rail_droop_worst_case.png
