Leif-Rydenfalk/halo/out/release/board/sim/rail_droop/rail_droop_worst_case_no_bulk.png

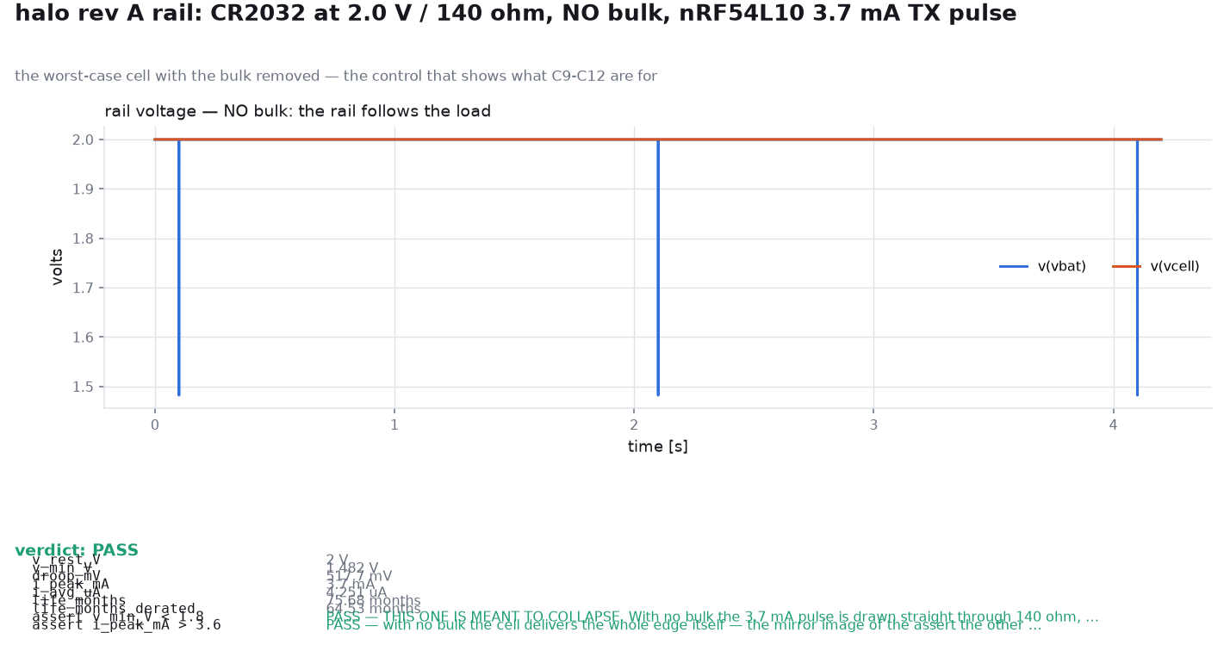
out/release/board/sim/rail_droop/rail_droop_worst_case_no_bulk.png
