Leif-Rydenfalk/halo/out/release/board/sim/sounder_drive/sounder_15nf.png

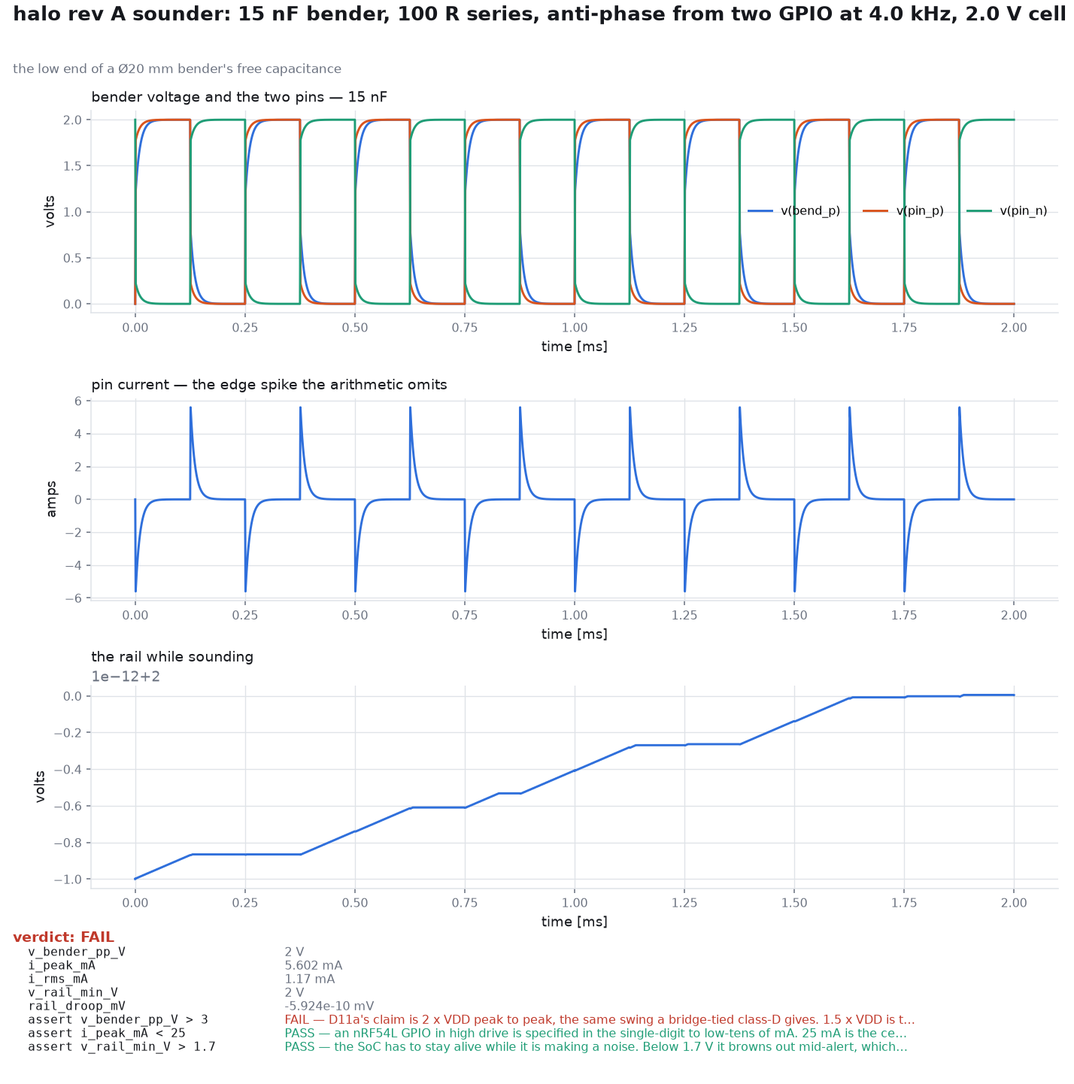
out/release/board/sim/sounder_drive/sounder_15nf.png
