Leif-Rydenfalk/halo/out/release/board/sim/sounder_drive/sounder_25nf.png

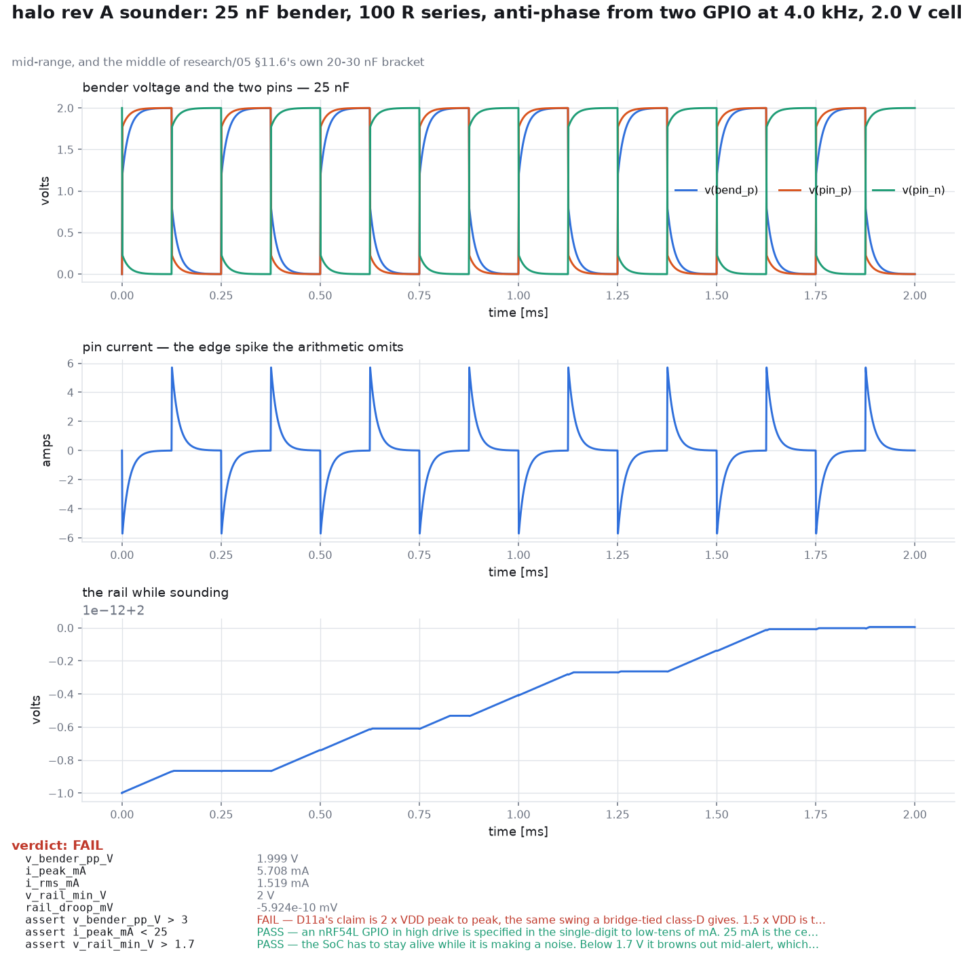
out/release/board/sim/sounder_drive/sounder_25nf.png
