Leif-Rydenfalk/halo/out/release/board/sim/sounder_drive/sounder_25nf_rs500.png

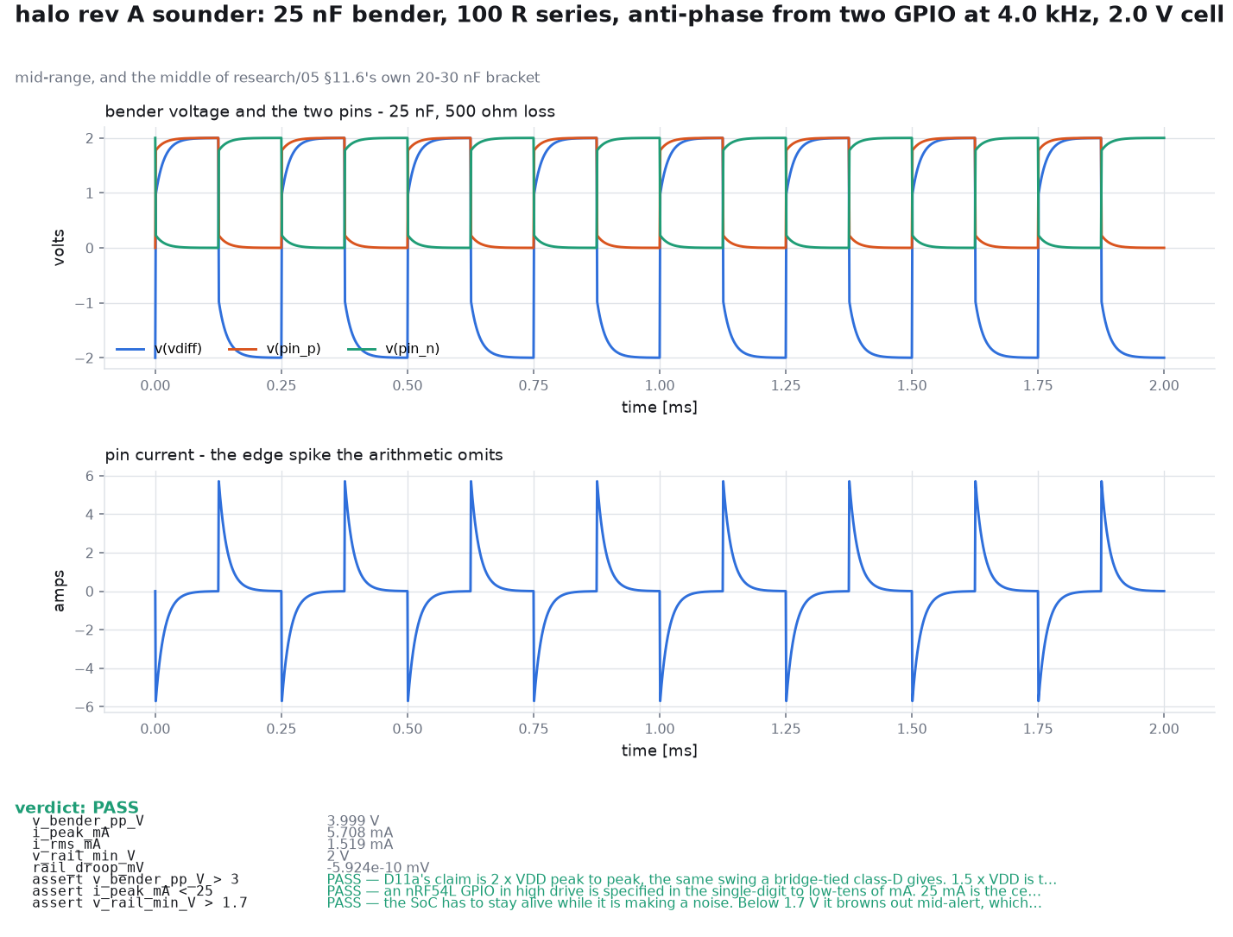
out/release/board/sim/sounder_drive/sounder_25nf_rs500.png
