Leif-Rydenfalk/halo/out/release/board/sim/sounder_drive/sounder_40nf_no_r9.png

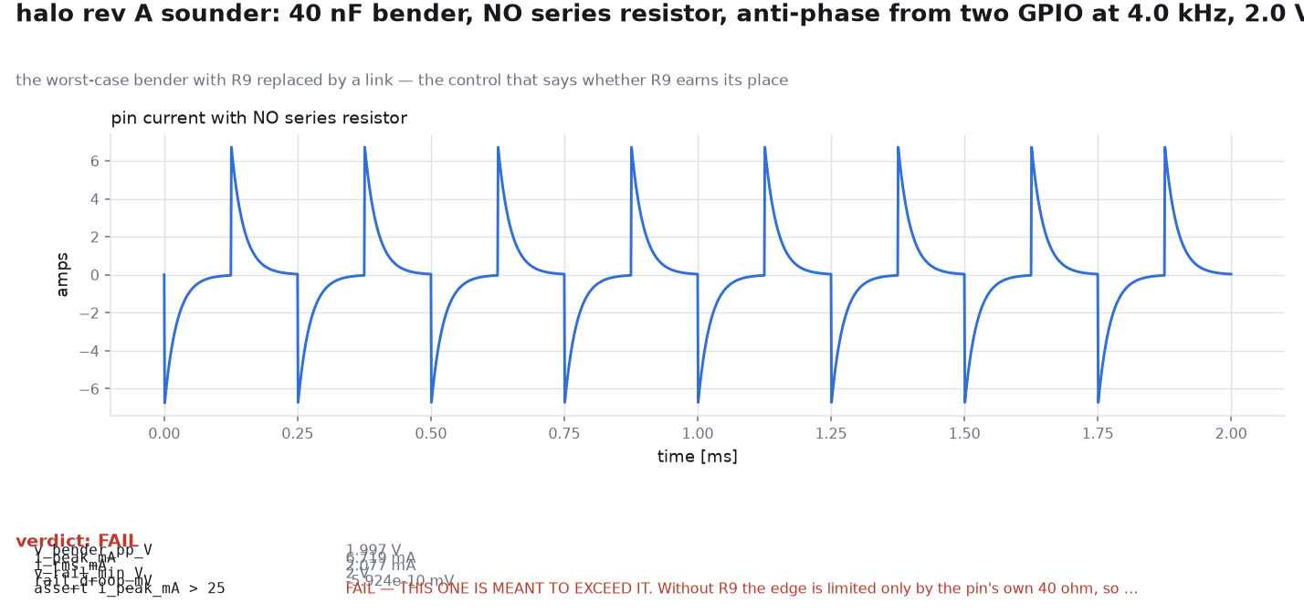
out/release/board/sim/sounder_drive/sounder_40nf_no_r9.png
