Leif-Rydenfalk/halo/out/release/board/sim/sounder_drive/sounder_40nf_rs32.png

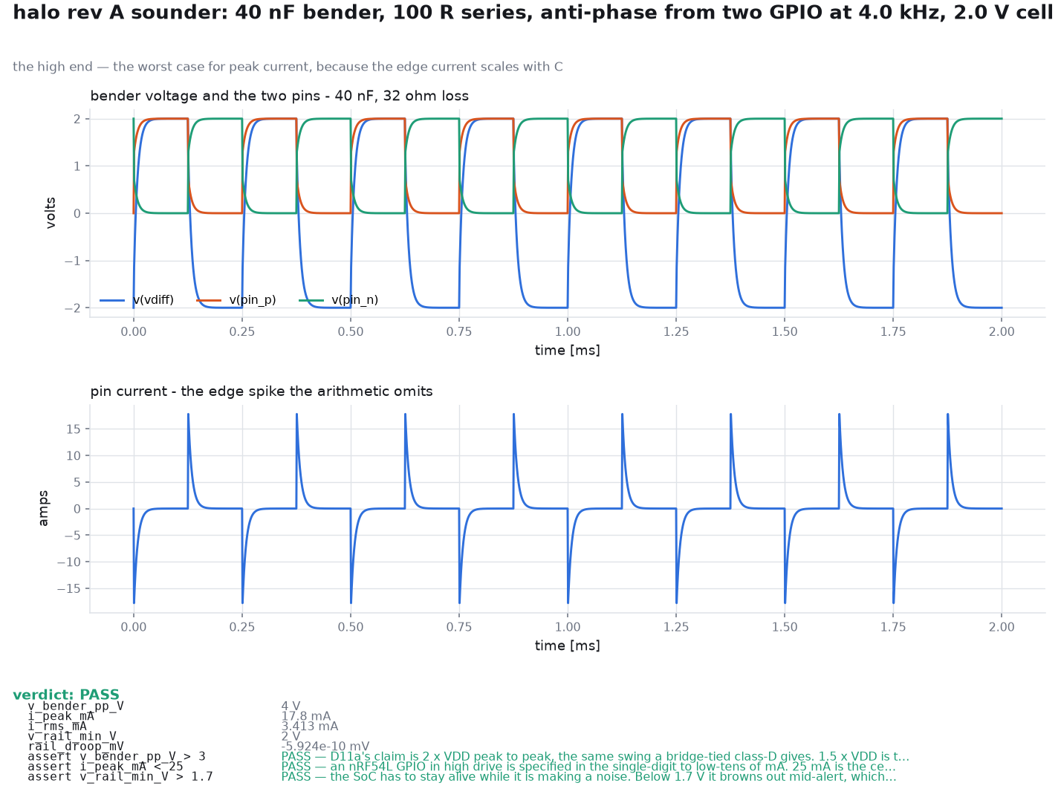
out/release/board/sim/sounder_drive/sounder_40nf_rs32.png
