Leif-Rydenfalk/halo/reference/send-my/Resources/modem.gif

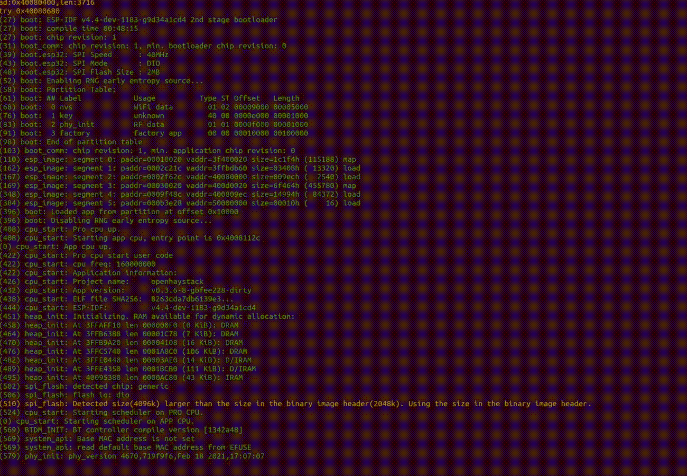
reference/send-my/Resources/modem.gif
