Leif-Rydenfalk/halo/reference/models/airtag-gustav-hires/Cutout 0.15mm margin.stl

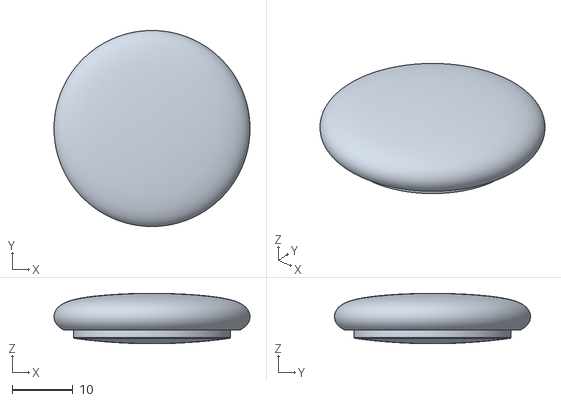
[picture p196: CAD file, 2026-09-03]
reference/models/airtag-gustav-hires/Cutout 0.15mm margin.stl
32.2 x 32.2 x 8.28
