Leif-Rydenfalk/halo/reference/models/ruuvitag-enclosure/ruuvitag-enclosure-base.step

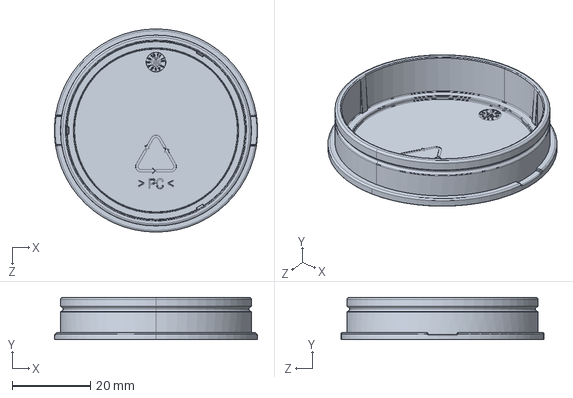
[picture p197: CAD file, 2026-09-03]
reference/models/ruuvitag-enclosure/ruuvitag-enclosure-base.step
51.9 x 10.8 x 52.0 mm
