Leif-Rydenfalk/halo/out/mech/halo-shell-top.step

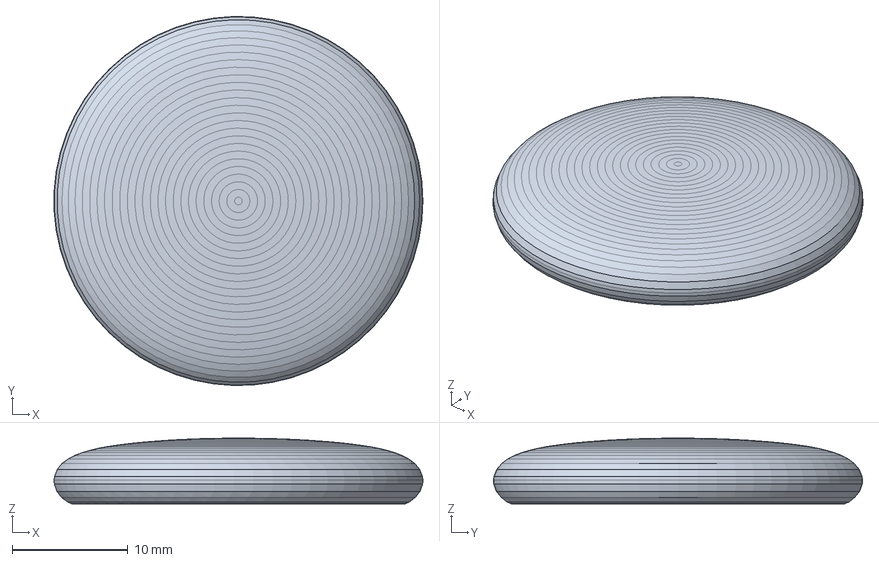
[picture p198: CAD file, 2026-09-04]
out/mech/halo-shell-top.step
31.9 x 31.9 x 5.69 mm
