Leif-Rydenfalk/halo/reference/EspruinoBoard/Bangle.js2/stand2d.dxf

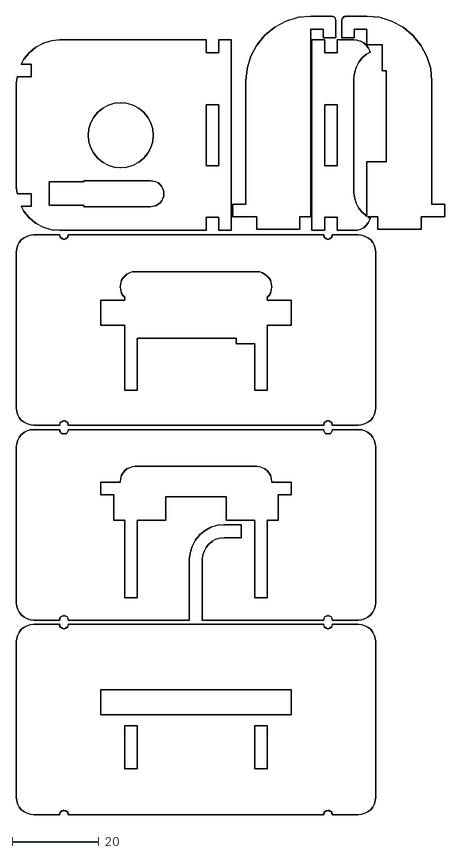
[picture p199: CAD file, 2026-09-03]
reference/EspruinoBoard/Bangle.js2/stand2d.dxf
99.0 x 184.5
