Leif-Rydenfalk/halo/reference/EspruinoBoard/Puck.js/case/top.stp

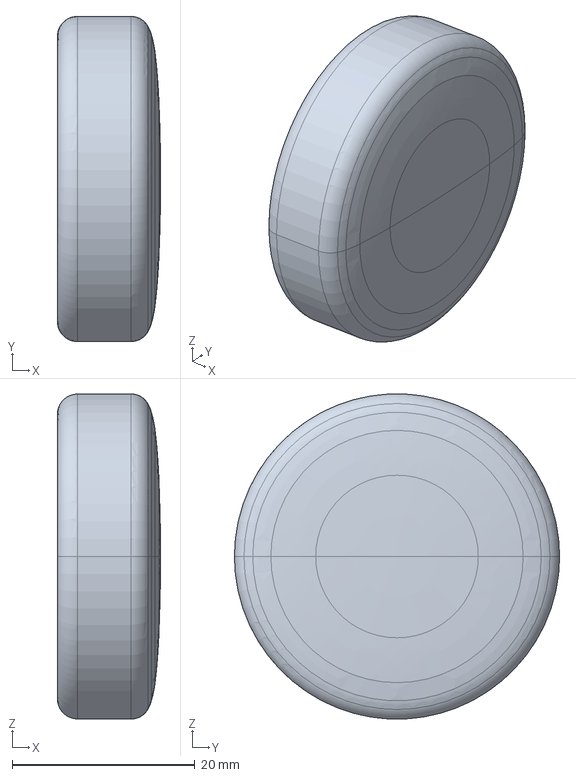
[picture p200: CAD file, 2026-09-03]
reference/EspruinoBoard/Puck.js/case/top.stp
11.3 x 35.6 x 35.6 mm
