Leif-Rydenfalk/halo/reference/Everytag/hardware/ALTIUM_EMBEDDED_MODELS/QFN50P400X400X80_HS-25N.step

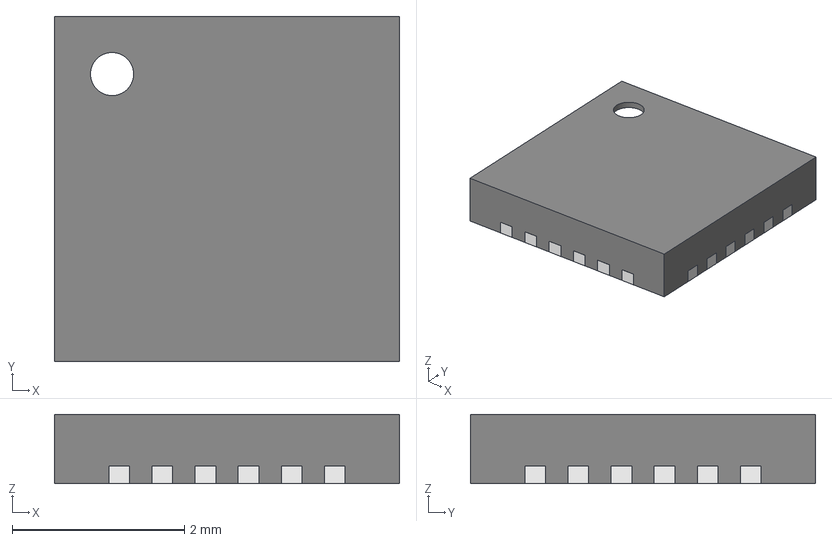
[picture p201: CAD file, 2026-09-03]
reference/Everytag/hardware/ALTIUM_EMBEDDED_MODELS/QFN50P400X400X80_HS-25N.step
4.00 x 4.00 x 0.801 mm
Thermal_Shape
