Leif-Rydenfalk/halo/reference/models/airtag-gustav-hires/Cutout 0.30mm margin.stl

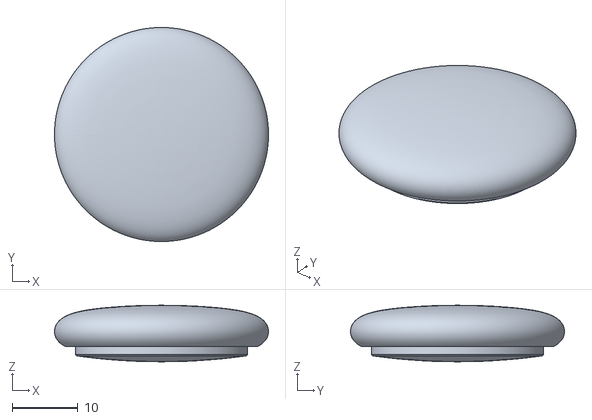
[picture p202: CAD file, 2026-09-03]
reference/models/airtag-gustav-hires/Cutout 0.30mm margin.stl
32.5 x 32.5 x 8.58
