Leif-Rydenfalk/halo/reference/models/ruuvitag-enclosure/ruuvitag-enclosure-lid.step

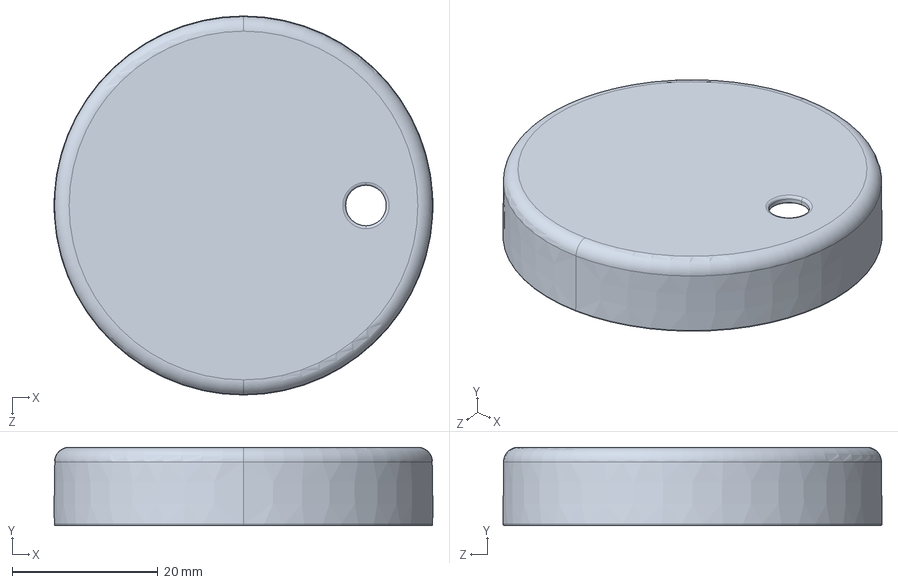
[picture p203: CAD file, 2026-09-03]
reference/models/ruuvitag-enclosure/ruuvitag-enclosure-lid.step
51.9 x 10.7 x 52.0 mm
