Leif-Rydenfalk/halo/out/mech/halo-pcb-blank.step

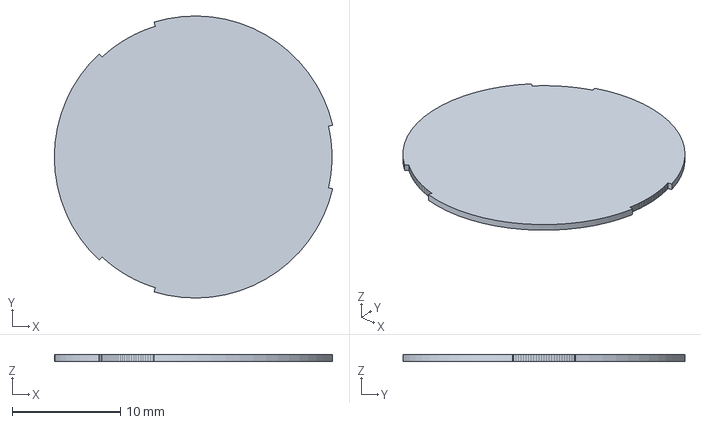
[picture p204: CAD file, 2026-09-04]
out/mech/halo-pcb-blank.step
25.7 x 26.0 x 0.6 mm
