Leif-Rydenfalk/halo/reference/EspruinoBoard/Puck.js/case/bottom.stp

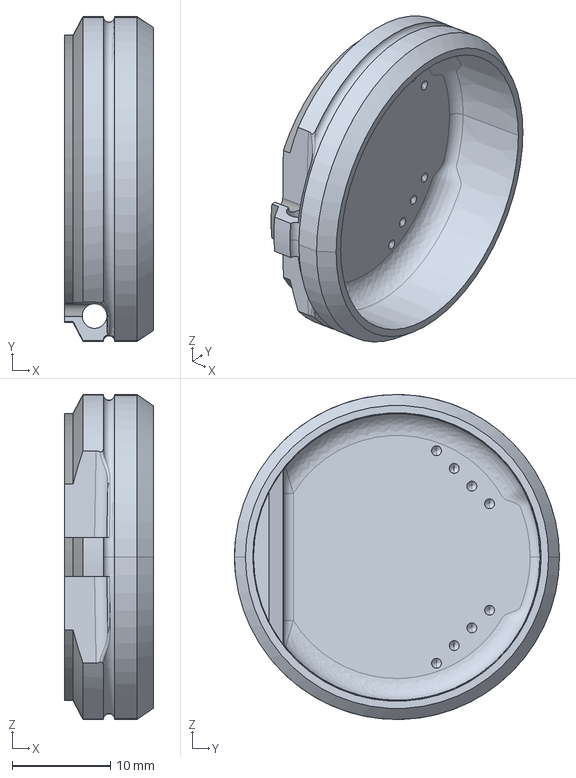
[picture p205: CAD file, 2026-09-03]
reference/EspruinoBoard/Puck.js/case/bottom.stp
9.00 x 33.0 x 33.0 mm
