Leif-Rydenfalk/halo/reference/Everytag/hardware/ALTIUM_EMBEDDED_MODELS/User Library-res0201-1.step

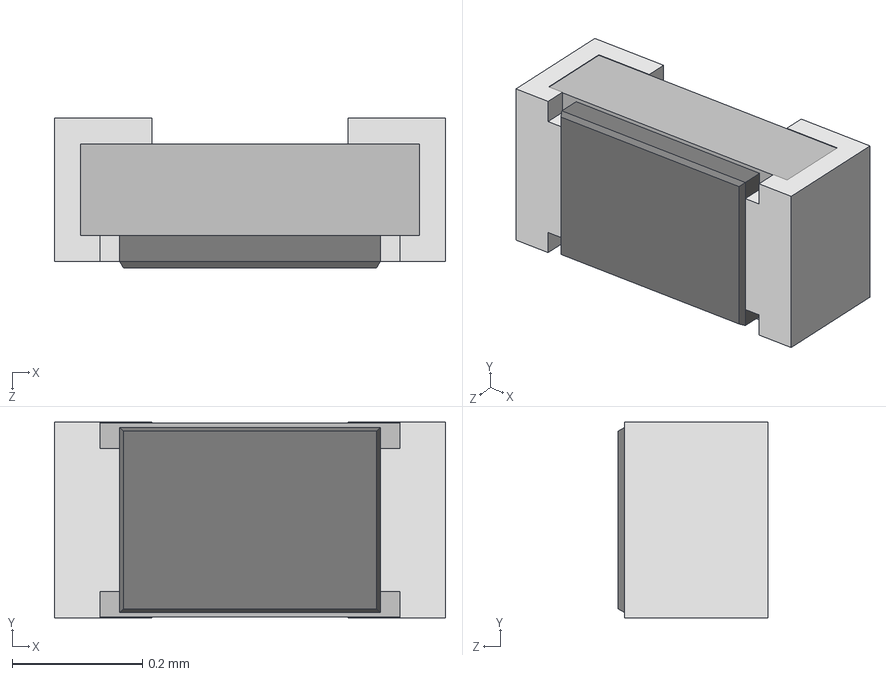
[picture p206: CAD file, 2026-09-03]
reference/Everytag/hardware/ALTIUM_EMBEDDED_MODELS/User Library-res0201-1.step
0.6 x 0.3 x 0.23 mm
