Leif-Rydenfalk/halo/reference/models/airtag-gustav-hires/AirTag with cutouts.step

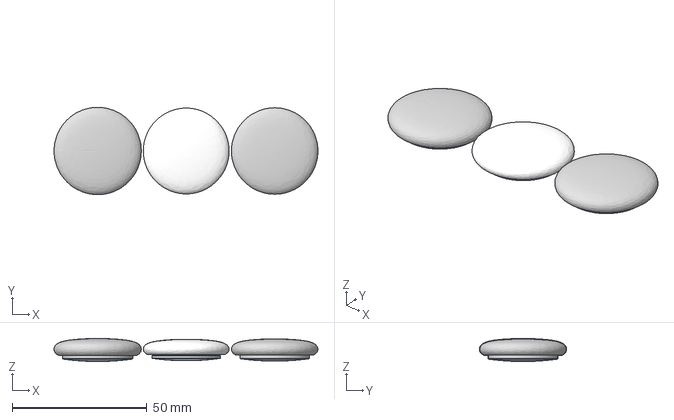
[picture p207: CAD file, 2026-09-03]
reference/models/airtag-gustav-hires/AirTag with cutouts.step
98.0 x 32.4 x 8.58 mm
Cutout 0.15mm margin
Cutout 0.30mm margin
