Leif-Rydenfalk/halo/out/mech/halo-door-seal.step

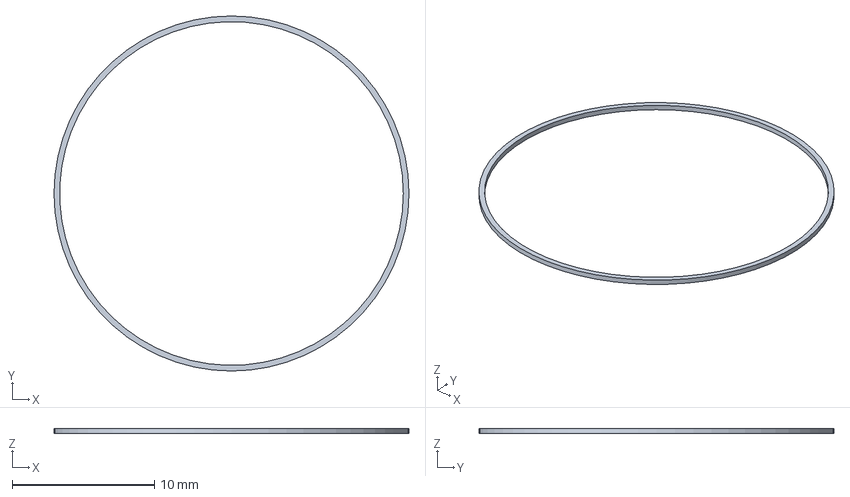
[picture p208: CAD file, 2026-09-04]
out/mech/halo-door-seal.step
24.9 x 24.9 x 0.35 mm
