Leif-Rydenfalk/halo/reference/Everytag/hardware/ALTIUM_EMBEDDED_MODELS/QFN40P500X500X50_HS-41N.step

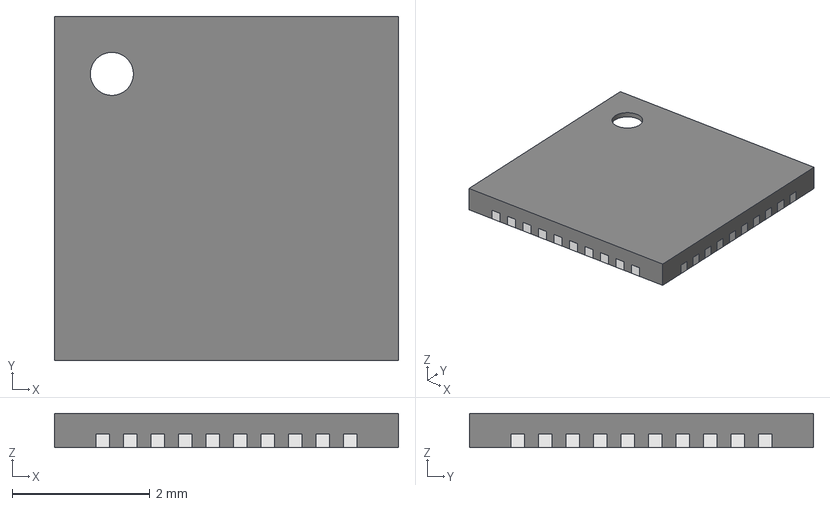
[picture p209: CAD file, 2026-09-03]
reference/Everytag/hardware/ALTIUM_EMBEDDED_MODELS/QFN40P500X500X50_HS-41N.step
5.00 x 5.00 x 0.501 mm
Thermal_Shape
