Leif-Rydenfalk/halo/out/mech/halo-battery-door-fdm.step

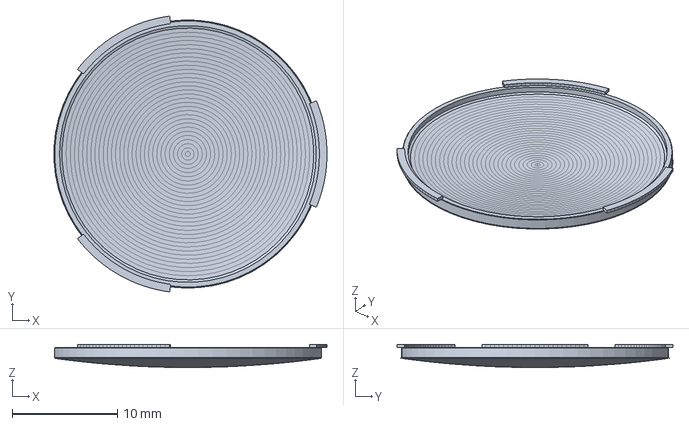
[picture p210: CAD file, 2026-09-04]
out/mech/halo-battery-door-fdm.step
25.9 x 26.2 x 2.19 mm
