Leif-Rydenfalk/halo/reference/Everytag/hardware/ALTIUM_EMBEDDED_MODELS/User Library-0201(0603M) Cap.step

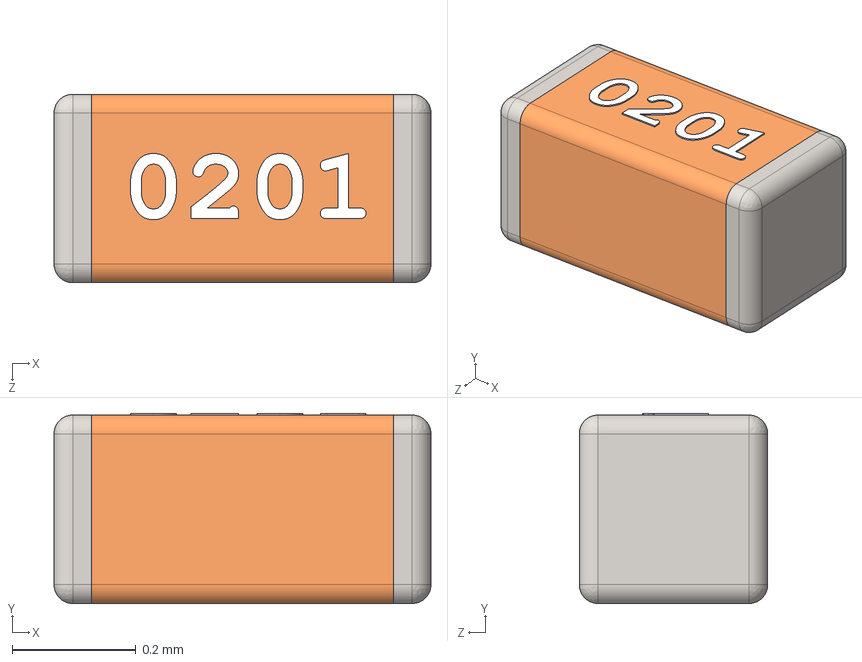
[picture p211: CAD file, 2026-09-03]
reference/Everytag/hardware/ALTIUM_EMBEDDED_MODELS/User Library-0201(0603M) Cap.step
0.61 x 0.307 x 0.305 mm
