Leif-Rydenfalk/halo/out/mech/halo-puck.step

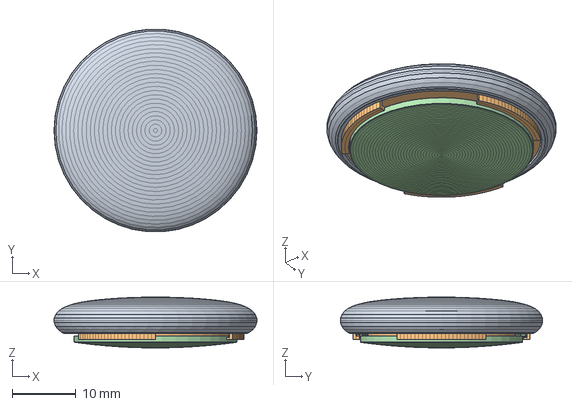
[picture p212: CAD file, 2026-09-04]
out/mech/halo-puck.step
31.9 x 31.8 x 7.98 mm
