Leif-Rydenfalk/halo/reference/Everytag/hardware/ALTIUM_EMBEDDED_MODELS/User Library-led_0603_red.step

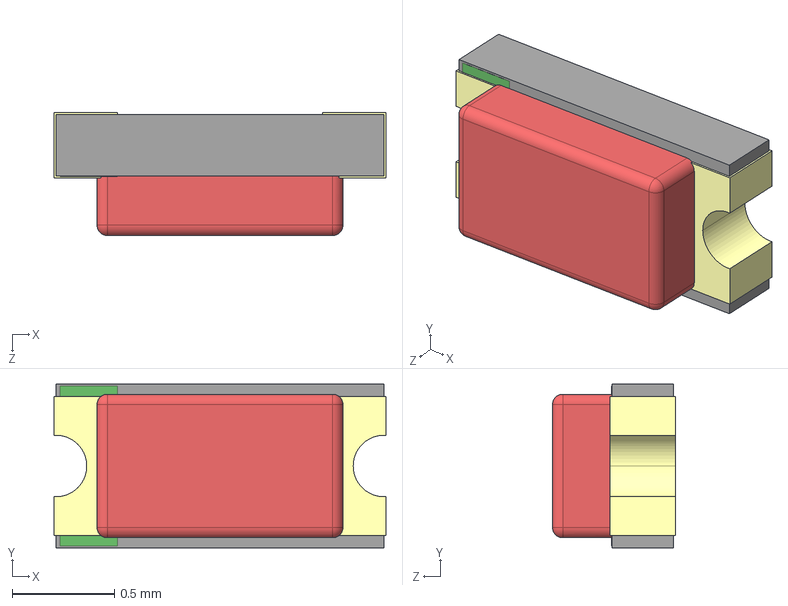
[picture p213: CAD file, 2026-09-03]
reference/Everytag/hardware/ALTIUM_EMBEDDED_MODELS/User Library-led_0603_red.step
1.62 x 0.8 x 0.6 mm
