Leif-Rydenfalk/halo/out/mech/halo-piezo-7bb-20-3.step

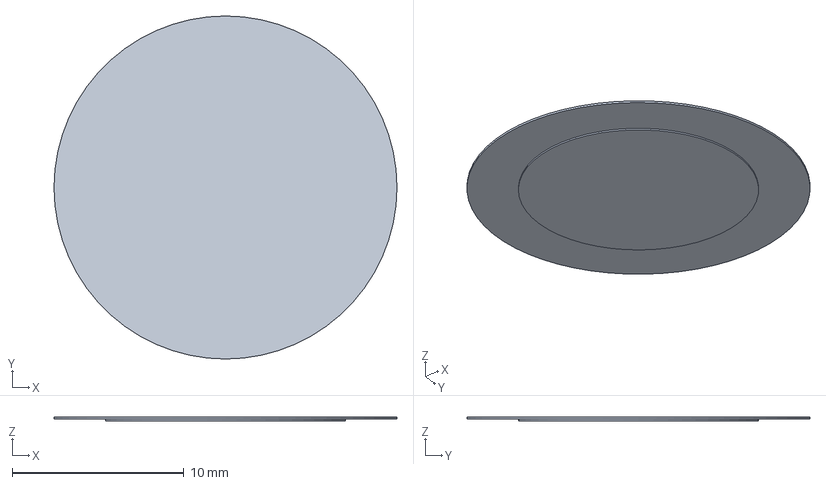
[picture p214: CAD file, 2026-09-04]
out/mech/halo-piezo-7bb-20-3.step
20.0 x 20.0 x 0.22 mm
