Leif-Rydenfalk/halo/out/mech/halo-battery-contact-pos-b.step

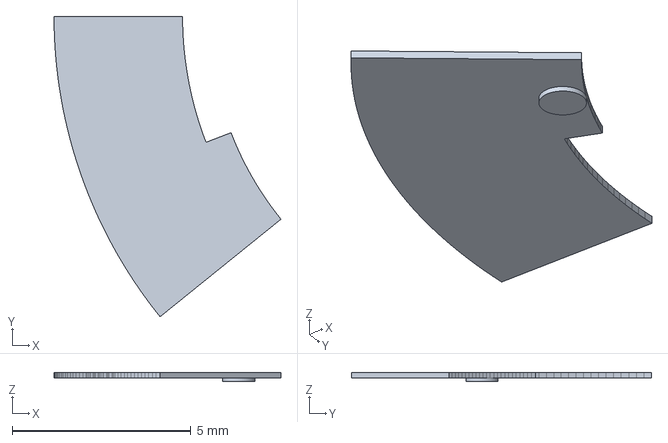
[picture p215: CAD file, 2026-09-04]
out/mech/halo-battery-contact-pos-b.step
6.36 x 8.41 x 0.25 mm
