Leif-Rydenfalk/halo/out/mech/halo-battery-contact-pos-a.step

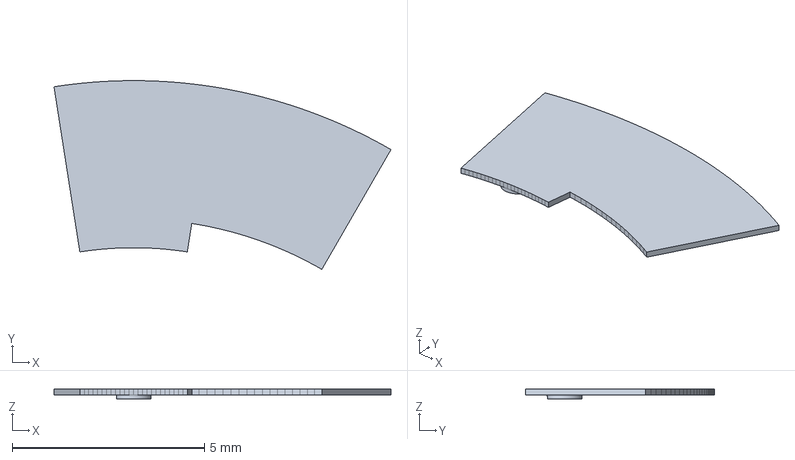
[picture p216: CAD file, 2026-09-04]
out/mech/halo-battery-contact-pos-a.step
8.77 x 4.91 x 0.25 mm
