Leif-Rydenfalk/halo/out/mech/halo-battery-contact-neg.step

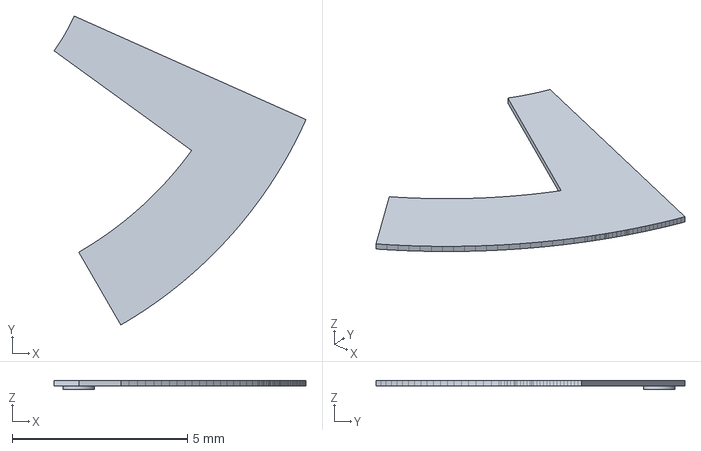
[picture p217: CAD file, 2026-09-03]
out/mech/halo-battery-contact-neg.step
7.19 x 8.82 x 0.25 mm
