Leif-Rydenfalk/halo/electronics/halo_replica/board/stackup/E-panel-3x3-halo_rev_a-MEASURED.png

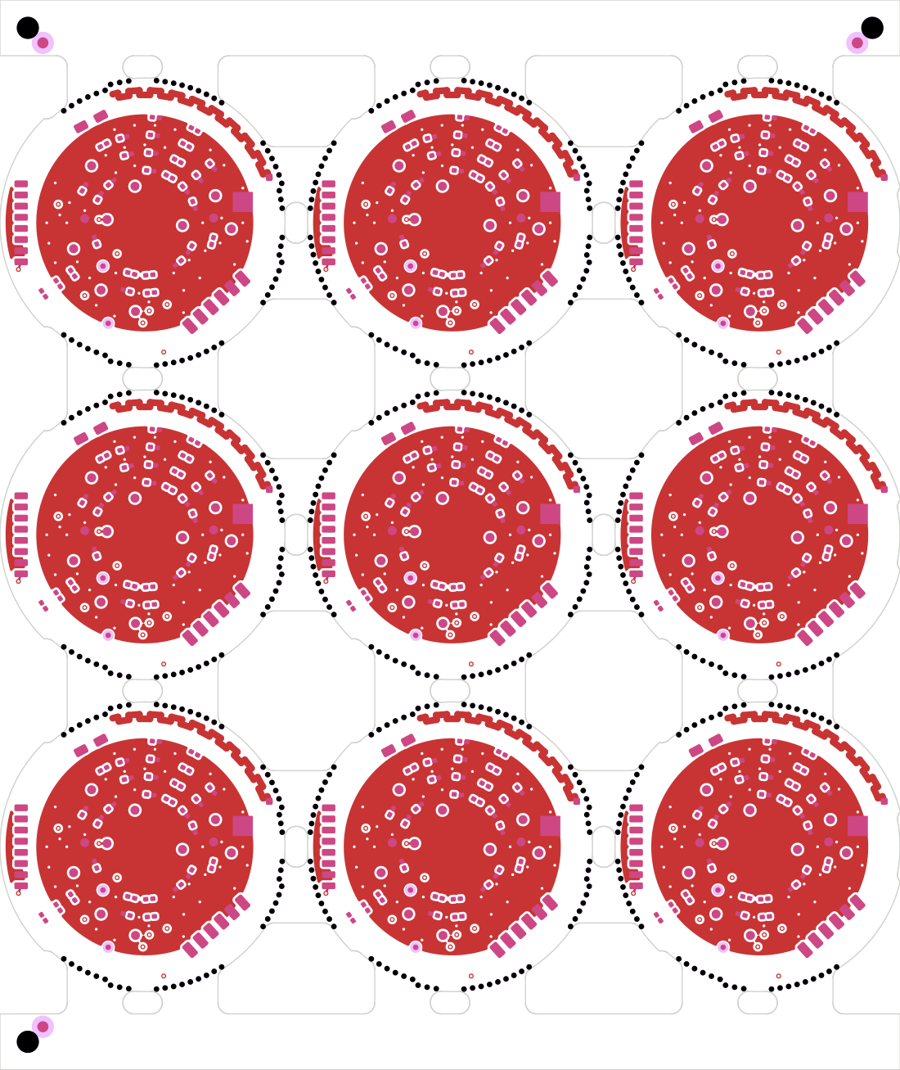
electronics/halo_replica/board/stackup/E-panel-3x3-halo_rev_a-MEASURED.png
