Leif-Rydenfalk/halo/out/gallery/img/ce-spice-out-nfc_tank-as-measured.png

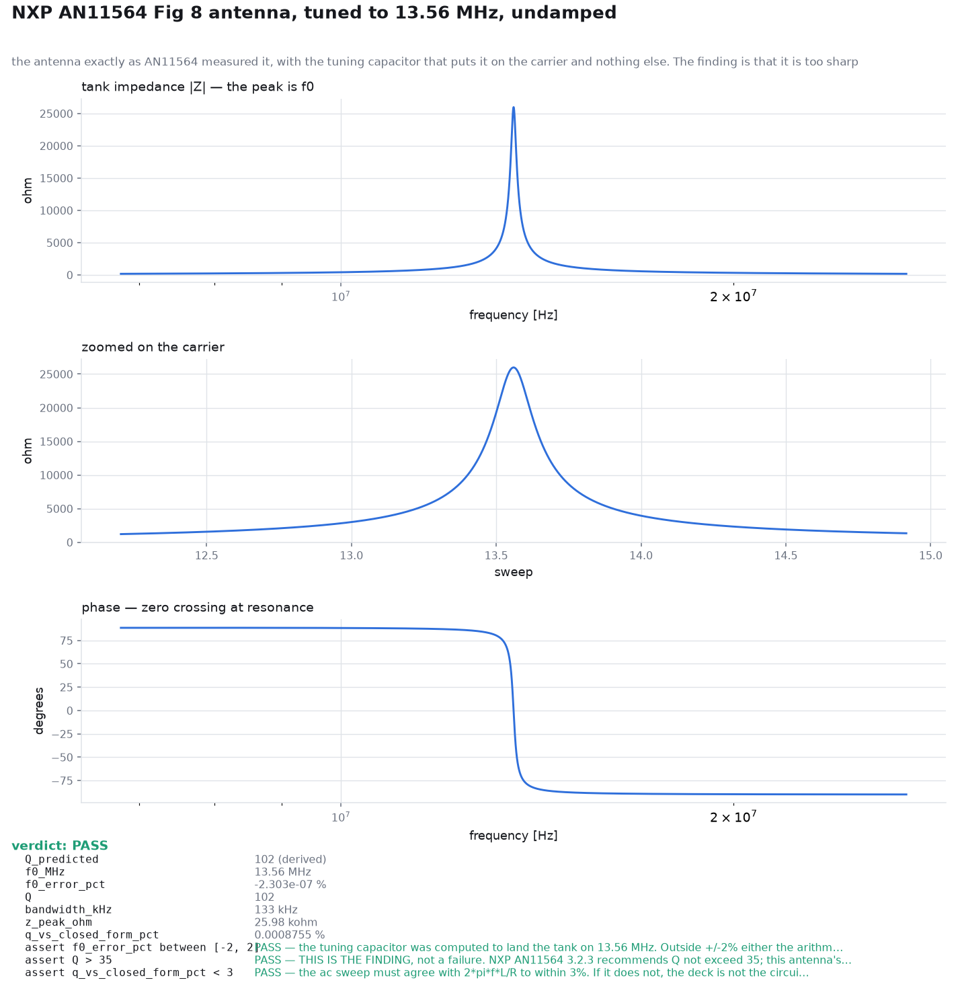
out/gallery/img/ce-spice-out-nfc_tank-as-measured.png
