Leif-Rydenfalk/halo/reference/shtc3_ble_beacon/schematic/nrf52_shtc3_board.kicad_pcb

## KiCad design reference/shtc3_ble_beacon/schematic/nrf52_shtc3_board.kicad_pcb (2026-09-03)

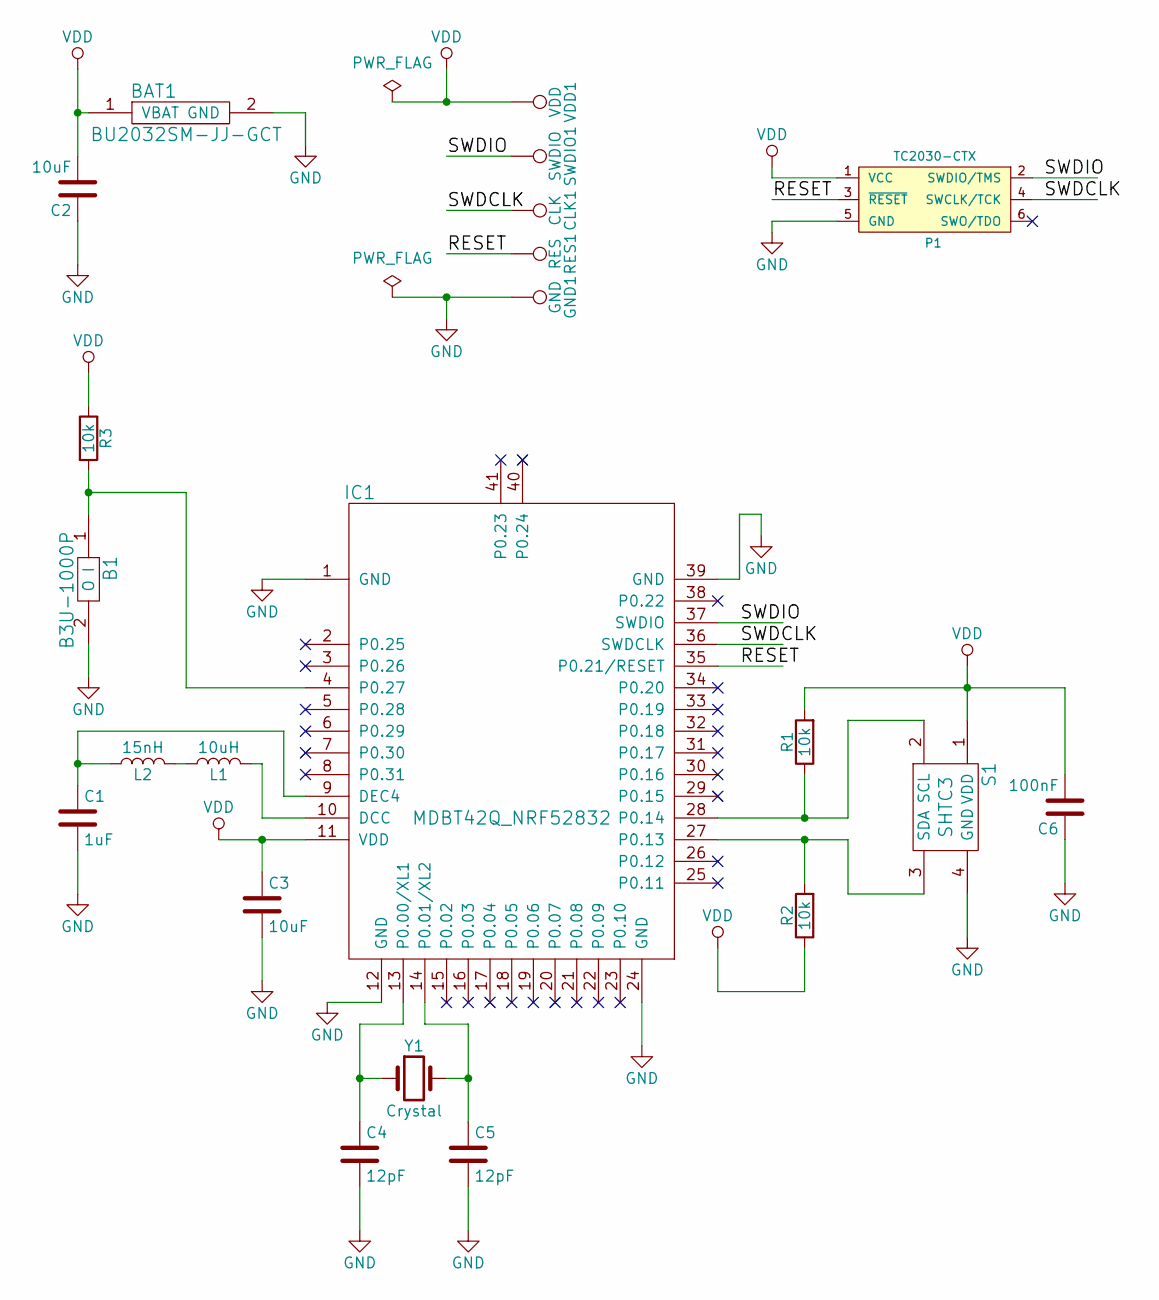
[picture p248: schematic nrf52_shtc3_board.sch, RHT_Beacon_SHTC3]

Parts:
B1: B3U-1000P; SW_SPST_B3U-1000P
BAT1: BU2032SM-JJ-GCT; BAT_Holder_2032
C1: 1uF; C_0603
C2, C3: 10uF; C_0603
C4, C5: 12pF; C_0603
C6: 100nF; C_0603
CLK1: CLK; WirePad_1mm_SMD
GND1: GND; WirePad_1mm_SMD
IC1: MDBT42Q_NRF52832; RF_Module_42_pin
L1: 10uH; C_0603
L2: 15nH; C_0603
P1: TC2030-CTX; TC2030-NL_SMALL
R1, R2, R3: 10k; R_0603
RES1: RES; WirePad_1mm_SMD
S1: SHTC3; DFN_4_pin_2x2
SWDIO1: SWDIO; WirePad_1mm_SMD
VDD1: VDD; WirePad_1mm_SMD
Y1: Crystal; Crystal_1.6x1_2pad

Connections:
/RESET: IC1.35 (P0.21/RESET), P1.3 (~RESET~), RES1.1
/SWDCLK: CLK1.1, IC1.36 (SWDCLK), P1.4 (SWCLK/TCK)
/SWDIO: IC1.37 (SWDIO), P1.2 (SWDIO/TMS), SWDIO1.1
GND: B1.2 (O), BAT1.2 (GND), C1.2, C2.1, C3.2, C4.2, C5.2, C6.1, GND1.1, IC1.1 (GND), IC1.12 (GND), IC1.24 (GND), IC1.39 (GND), P1.5 (GND), S1.4 (GND)
unnamed: B1.1 (I), IC1.4 (P0.27), R3.2
unnamed: C1.1, IC1.9 (DEC4), L2.1
unnamed: C4.1, IC1.13 (P0.00/XL1), Y1.1
unnamed: C5.1, IC1.14 (P0.01/XL2), Y1.2
unnamed: IC1.10 (DCC), L1.2
unnamed: IC1.27 (P0.13), R2.2, S1.3 (SDA)
unnamed: IC1.28 (P0.14), R1.1, S1.2 (SCL)
unnamed: L1.1, L2.2
VDD: BAT1.1 (VBAT), C2.2, C3.1, C6.2, IC1.11 (VDD), P1.1 (VCC), R1.2, R2.1, R3.1, S1.1 (VDD), VDD1.1

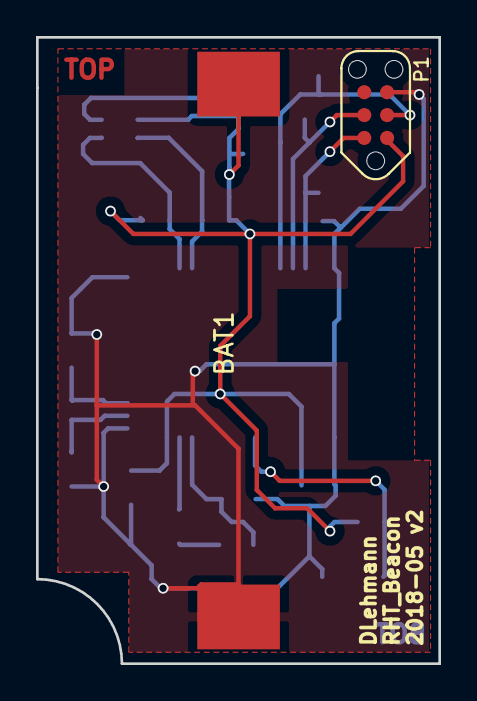
[picture p249: board nrf52_shtc3_board.kicad_pcb from above]

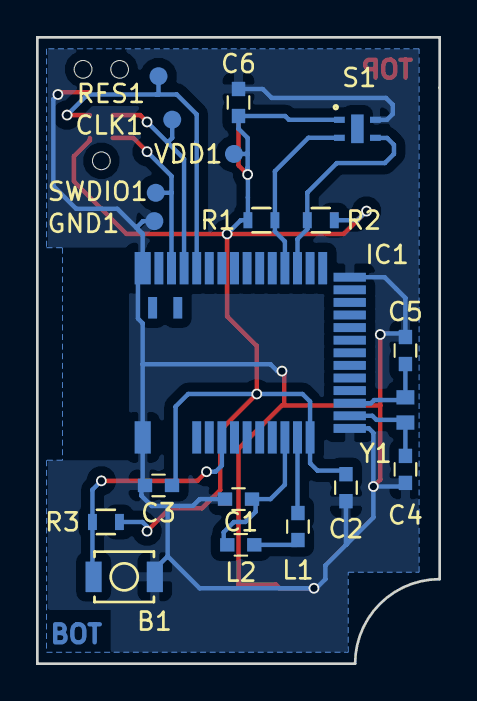
[picture p250: board nrf52_shtc3_board.kicad_pcb from below]

Board: 2 copper layers, 22.4 x 34.8 mm, 22 parts (20 on the bottom side), 13 nets.
