Leif-Rydenfalk/halo/reference/nrf52-kicad/nrf51x22_qfax_dcdc.kicad_pcb

## KiCad design reference/nrf52-kicad/nrf51x22_qfax_dcdc.kicad_pcb (2026-09-03)

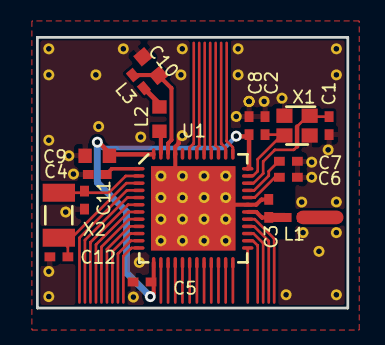
[picture p251: board nrf51x22_qfax_dcdc.kicad_pcb from above]

Board: 2 copper layers, 17.2 x 15.0 mm, 18 parts (0 on the bottom side), 13 nets.

Parts:
C1, C2, C11, C12: 12pF; CAPC1005X04L
C3: .8pF; CAPC1005X04L
C4, C5, C8: 100nF; CAPC1005X04L
C6: NC; CAPC1005X04L
C7: 100pF; CAPC1005X04L
C9: 4.7uF; CAPC1608X06L
C10: 1.0uF; CAPC1608X06L
L1: 3.9nH; INDC1005X04L
L2: 10uH; INDC1608X06L
L3: 15nH; INDC1005X04L
U1: nrf51822-qfax; nrf51-qfax-1ep-vias
X1: Crystal-4; BT-XTAL_2016
X2: 32.768kHz; XTAL_3215

Connections:
/VDD_nRF: C5.2, C8.2, C9.2, U1.13, U1.36, U1.48
GND: C1.2, C2.2, C3.2, C4.1, C5.1, C6.1, C7.1, C8.1, C9.1, C10.1, C11.1, C12.1, U1.31, U1.45, U1.49, X1.2, X1.4
unnamed: C1.1, U1.34, X1.1
unnamed: C2.1, U1.35, X1.3
unnamed: C3.1, L1.1, U1.30
unnamed: C4.2, U1.1
unnamed: C6.2, U1.32
unnamed: C7.2, U1.33
unnamed: C10.2, L3.1, U1.46
unnamed: C11.2, U1.2, X2.2
unnamed: C12.2, U1.3, X2.1
unnamed: L2.1, L3.2
unnamed: L2.2, U1.47
