Leif-Rydenfalk/halo/electronics/halo_replica/fab/out/halo_replica_fab-routed.kicad_pcb

## KiCad design electronics/halo_replica/fab/out/halo_replica_fab-routed.kicad_pcb (2026-09-05)

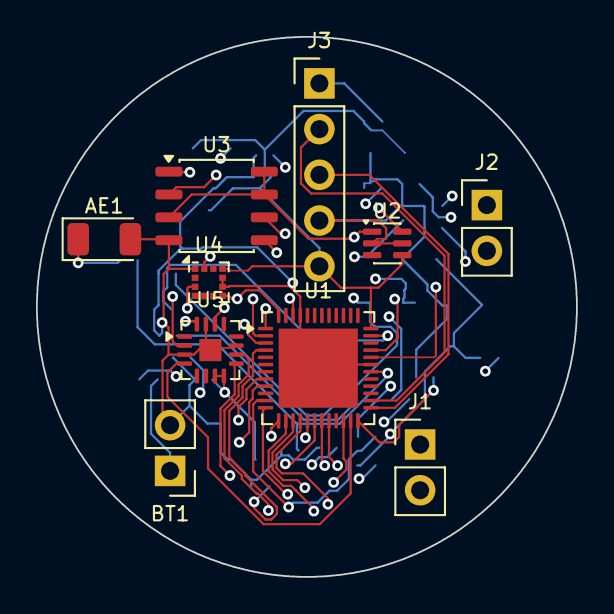
[picture p252: board halo_replica_fab-routed.kicad_pcb from above]

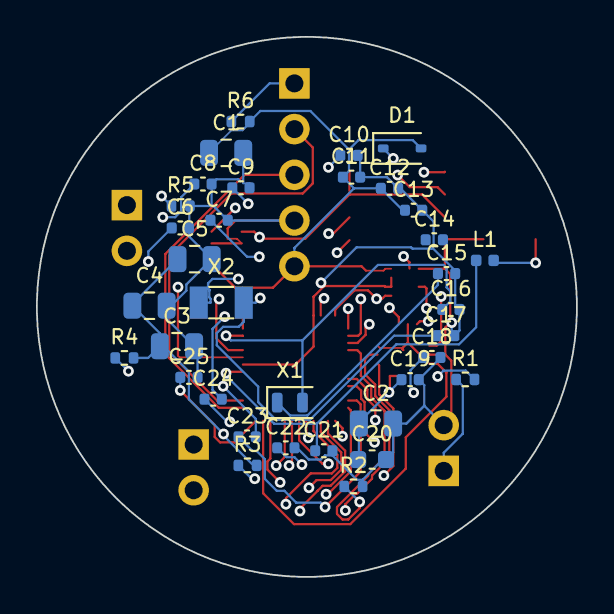
[picture p253: board halo_replica_fab-routed.kicad_pcb from below]

Board: 4 copper layers, 30.0 x 30.0 mm, 45 parts (35 on the bottom side), 37 nets.

Parts:
AE1: 2450AT18A100 2.4GHz chip; Johanson_2450AT18x100
BT1: CR2032 CELL - OFF-BOARD, ON 2 PADS; PinHeader_1x02_P2.54mm_Vertical
C1, C2, C3, C4, C5: 100uF 6.3V X5R; C_0805_2012Metric
C6, C10: 1uF 16V X7R; C_0402_1005Metric
C7, C8, C9, C11, C12, C13, C19, C25: 100nF 16V X7R; C_0402_1005Metric
C14: DNP - see note; C_0402_1005Metric
C15, C16: 8pF 50V C0G; C_0402_1005Metric
C17, C18: 22pF 50V C0G; C_0402_1005Metric
C20: 10uF 6.3V X5R; C_0603_1608Metric
C21, C22: 1.0pF 50V C0G; C_0402_1005Metric
C23, C24: 150pF 50V C0G; C_0402_1005Metric
D1: BAT54HT1G (Vf~0.24V @1mA); D_SOD-323
J1: VOICE COIL / SOUNDER; PinHeader_1x02_P2.54mm_Vertical
J2: NFC COIL 13.56MHz; PinHeader_1x02_P2.54mm_Vertical
J3: SWD (nRST SWDIO SWCLK GND VBAT); PinHeader_1x05_P2.54mm_Vertical
L1: 3.9nH; L_0402_1005Metric
R1, R2: 10M; R_0402_1005Metric
R3, R4, R6: 10k; R_0402_1005Metric
R5: 100k; R_0402_1005Metric
U1: nRF52832-QFAA-R; QFN-48-1EP_6x6mm_P0.4mm_EP4.4x4.4mm
U2: MIC94090YC6 (0.5 uA, 1.5 A); SOT-363_SC-70-6
U3: MX25R3235F 32Mb 1.65-3.6V; JEITA_SOIC-8_3.9x4.9mm_P1.27mm
U4: SC7A20 3-axis, LGA-12; LGA-12_2x2mm_P0.5mm
U5: MAX98357A class-D, TQFN-16; TQFN-16-1EP_3x3mm_P0.5mm_EP1.23x1.23mm
X1: 32MHz 10ppm CL=8pF; Crystal_SMD_2012-2Pin_2.0x1.2mm
X2: 32.768kHz 20ppm CL=12.5pF; Crystal_SMD_3215-2Pin_3.2x1.5mm

Connections:
ACC_INT1: U1.10, U4.5
ACC_SCL: R3.1, U1.8, U4.12
ACC_SDA: R4.1, U1.9, U4.2
AMP_GAIN: R5.1, U5.2
AMP_nSD: U1.23, U5.4
ANT_FEED: AE1.1, C22.1, L1.2
ANT_SOC: C21.1, L1.1, U1.30
DEC1: C7.1, U1.1
DEC2: C8.1, U1.32
DEC3: C9.1, U1.33
DEC4: C10.1, U1.46
FLASH_PWR_EN: U1.15, U2.6
FLASH_nCS: U1.14, U3.1
GND: AE1.2, BT1.2, C1.2, C2.2, C3.2, C4.2, C5.2, C6.2, C7.2, C8.2, C9.2, C10.2, C11.2, C12.2, C13.2, C15.2, C16.2, C17.2, C18.2, C19.2, C20.2, C21.2, C22.2, C25.2, J3.4, R2.2, R5.2, U1.31, U1.45, U1.49, U2.2, U2.5, U3.4, U4.1, U4.8, U4.9, U5.3, U5.11, U5.15, U5.17
I2S_BCLK: U1.16, U5.16
I2S_DIN: U1.22, U5.1
I2S_LRCLK: U1.17, U5.14
NFC1: C23.1, U1.11
NFC2: C24.1, U1.12
NFC_COIL_A: C23.2, J2.1
NFC_COIL_B: C24.2, J2.2
SPI_MISO: U1.18, U3.2
SPI_MOSI: U1.19, U3.5
SPI_SCK: U1.20, U3.6
SPK_N: J1.2, U5.10
SPK_P: J1.1, U5.9
SWDCLK: J3.3, U1.25
SWDIO: J3.2, U1.26
VBAT: C1.1, C2.1, C3.1, C4.1, C5.1, C11.1, C12.1, C13.1, C19.1, C20.1, D1.2, J3.5, R3.2, R4.2, R6.2, U1.13, U1.36, U1.48, U2.4, U4.3, U4.7, U4.10, U5.7, U5.8
VBAT_RAW: BT1.1, D1.1, R1.1
VBAT_SENSE: R1.2, R2.1, U1.4
VFLASH: C6.1, U2.1, U3.3, U3.7, U3.8
XC1: C15.1, U1.34, X1.1
XC2: C16.1, U1.35, X1.2
XL1: C17.1, U1.2, X2.1
XL2: C18.1, U1.3, X2.2
nRESET: C25.1, J3.1, R6.1, U1.24
