Leif-Rydenfalk/halo/reference/EspruinoBoard/MDBT42/eagle/mdbt42q_breakout.brd

## EAGLE design reference/EspruinoBoard/MDBT42/eagle/mdbt42q_breakout.brd (2026-09-03)

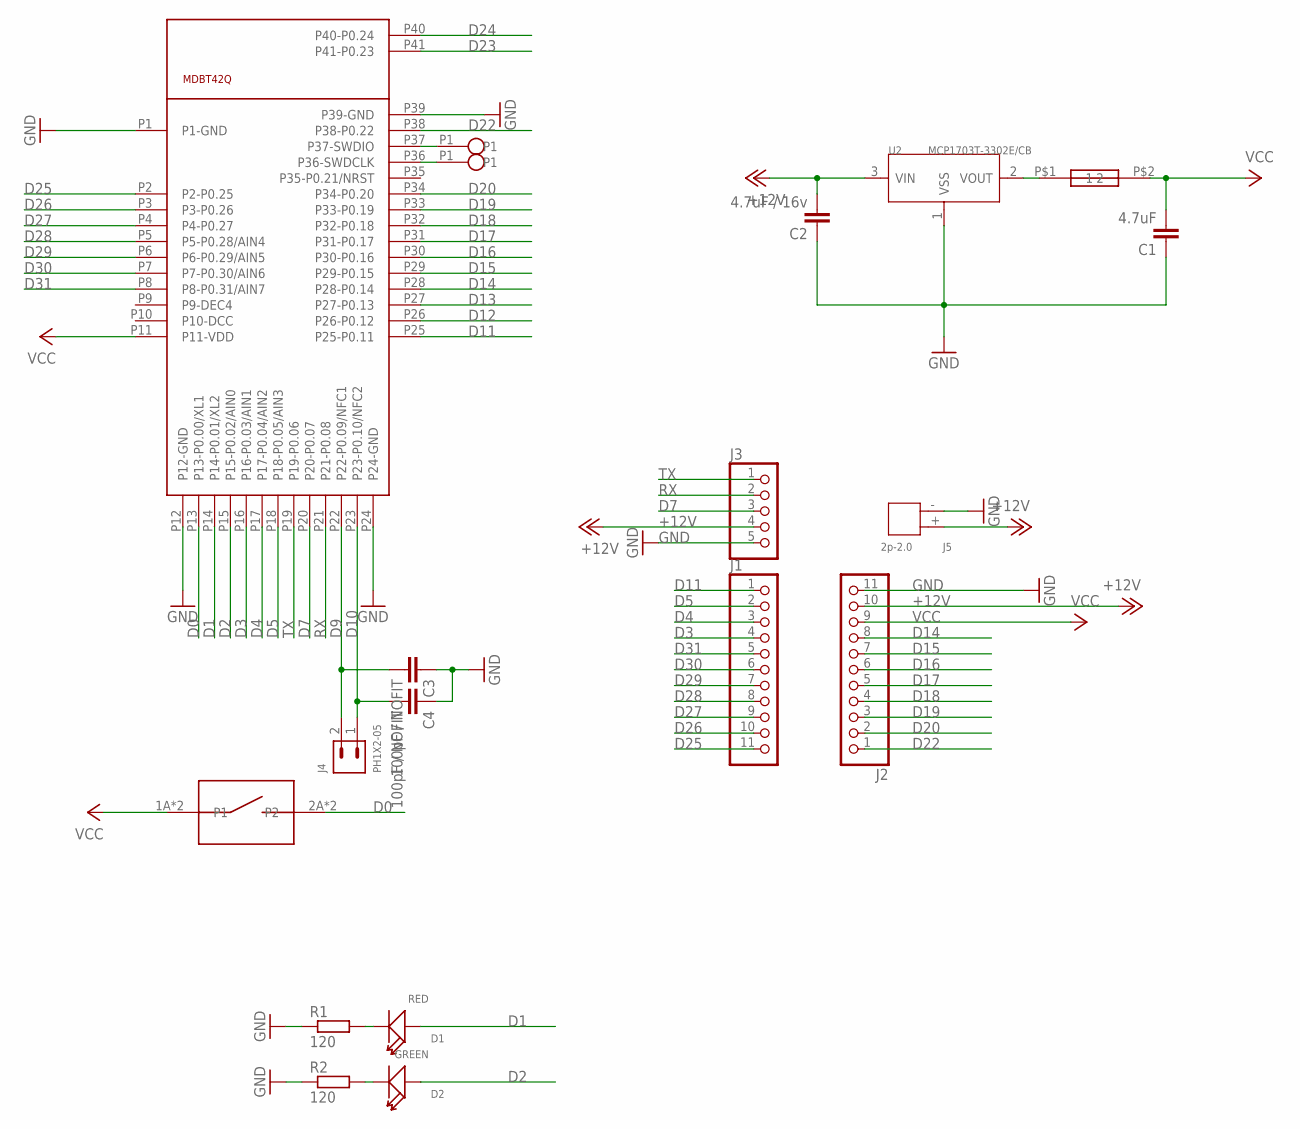
[picture p279: schematic mdbt42q_breakout.sch]

Parts:
BTN: KMR421NG
C1: 4.7uF; C0805
C2: 4.7uF / 16v; C0805
C3, C4: 100pF / NOFIT; C0603
D1: RED; LED-0603
D2: GREEN; LED-0603
J1, J2: PINHD-1X11_2.54-SX; 1X11-SX
J3: PINHD-1X05_2.54-SX; 1X05-SX
J4: PH1X2-05; PH005-1-2
J5: 2p-2.0; H2-2.0-6X4.5MM-NOSILK
R1, R2: 120; R0603
U1: MDBT42Q; MDBT40
U2: MCP1703T-3302E/CB; SOT23
U$2, U$3: SINGLE
U$4: WIRELINK

Connections:
+12V: C2.2, J2.10, J3.4, J5.+, U2.3 (VIN)
D0: BTN.2A (P2), BTN.2B (P2), U1.P13 (P13-P0.00/XL1)
D1: D1.+, U1.P14 (P14-P0.01/XL2)
D2: D2.+, U1.P15 (P15-P0.02/AIN0)
D3: J1.4, U1.P16 (P16-P0.03/AIN1)
D4: J1.3, U1.P17 (P17-P0.04/AIN2)
D5: J1.2, U1.P18 (P18-P0.05/AIN3)
D7: J3.3, U1.P20 (P20-P0.07)
D9: C3.2, J4.2, U1.P22 (P22-P0.09/NFC1)
D10: C4.2, J4.1, U1.P23 (P23-P0.10/NFC2)
D11: J1.1, U1.P25 (P25-P0.11)
D12: U1.P26 (P26-P0.12)
D13: U1.P27 (P27-P0.13)
D14: J2.8, U1.P28 (P28-P0.14)
D15: J2.7, U1.P29 (P29-P0.15)
D16: J2.6, U1.P30 (P30-P0.16)
D17: J2.5, U1.P31 (P31-P0.17)
D18: J2.4, U1.P32 (P32-P0.18)
D19: J2.3, U1.P33 (P33-P0.19)
D20: J2.2, U1.P34 (P34-P0.20)
D22: J2.1, U1.P38 (P38-P0.22)
D23: U1.P41 (P41-P0.23)
D24: U1.P40 (P40-P0.24)
D25: J1.11, U1.P2 (P2-P0.25)
D26: J1.10, U1.P3 (P3-P0.26)
D27: J1.9, U1.P4 (P4-P0.27)
D28: J1.8, U1.P5 (P5-P0.28/AIN4)
D29: J1.7, U1.P6 (P6-P0.29/AIN5)
D30: J1.6, U1.P7 (P7-P0.30/AIN6)
D31: J1.5, U1.P8 (P8-P0.31/AIN7)
GND: C1.1, C2.1, C3.1, C4.1, J2.11, J3.5, J5.-, R1.1, R2.1, U1.P1 (P1-GND), U1.P12 (P12-GND), U1.P24 (P24-GND), U1.P39 (P39-GND), U2.1 (VSS)
unnamed: U1.P37 (P37-SWDIO), U$2.P1
unnamed: U1.P36 (P36-SWDCLK), U$3.P1
unnamed: U2.2 (VOUT), U$4.P$1 (1)
unnamed: D1.-, R1.2
unnamed: D2.-, R2.2
RX: J3.2, U1.P21 (P21-P0.08)
TX: J3.1, U1.P19 (P19-P0.06)
VCC: BTN.1A (P1), BTN.1B (P1), C1.2, J2.9, U1.P11 (P11-VDD), U$4.P$2 (2)

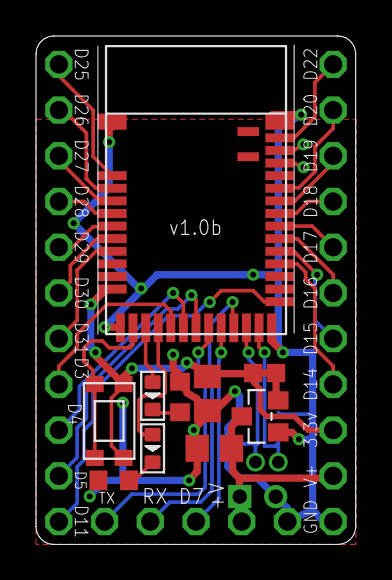
[picture p280: board mdbt42q_breakout.brd from above]

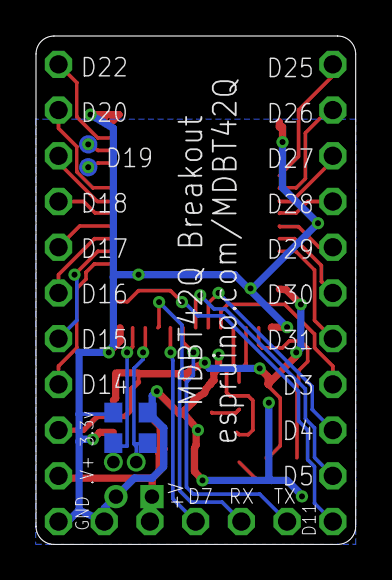
[picture p281: board mdbt42q_breakout.brd from below]

Board: 2 copper layers, 17.8 x 28.2 mm, 19 parts (4 on the bottom side), 35 nets.
