Leif-Rydenfalk/halo/reference/EspruinoBoard/Pico/EspruBoy/espruboy.brd

## EAGLE design reference/EspruinoBoard/Pico/EspruBoy/espruboy.brd (2026-09-03)

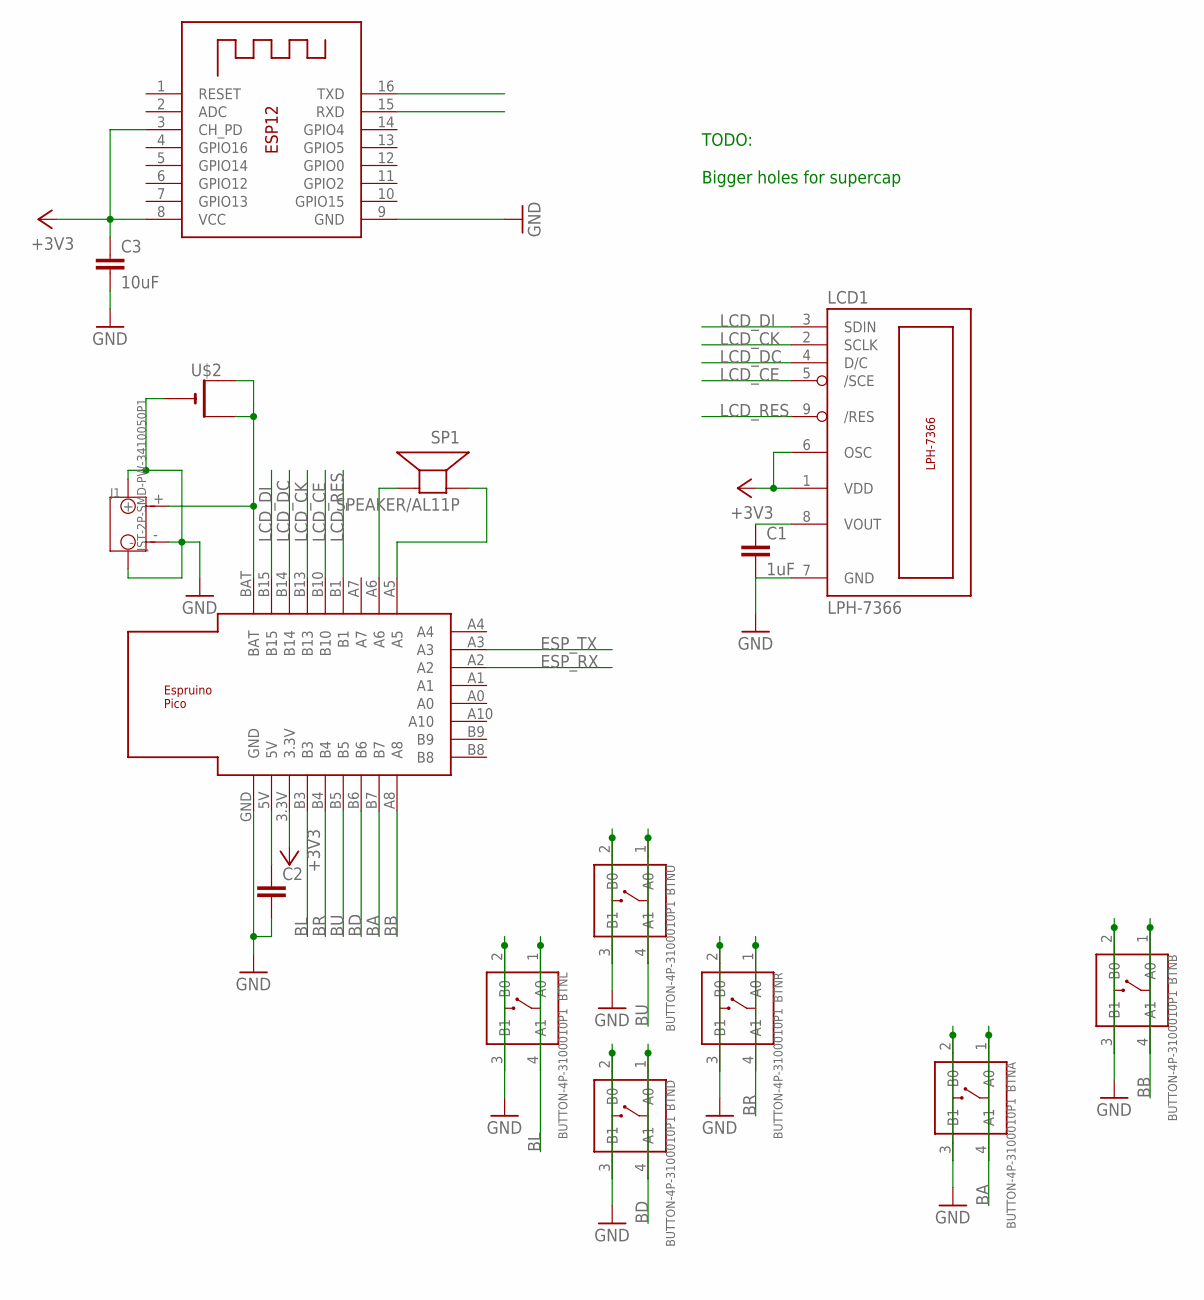
[picture p282: schematic espruboy.sch]

Parts:
BTNA: BUTTON-4P-3100010P1; 4P-SMD-6.0X6.0X5.0H
BTNB: BUTTON-4P-3100010P1; 4P-SMD-6.0X6.0X5.0H
BTND: BUTTON-4P-3100010P1; 4P-SMD-6.0X6.0X5.0H
BTNL: BUTTON-4P-3100010P1; 4P-SMD-6.0X6.0X5.0H
BTNR: BUTTON-4P-3100010P1; 4P-SMD-6.0X6.0X5.0H
BTNU: BUTTON-4P-3100010P1; 4P-SMD-6.0X6.0X5.0H
C1: 1uF; C1206
C2: C-EU050-075X075; C050-075X075
C3: 10uF; C1206
ESP12: ESP-12
J1: JST-2P-SMD-PW-3410050P1; 2P-SMD-2.0-90D
LCD1: LPH-7366
SP1: SPEAKER/AL11P; AL11P
U$1: ESPRUINO_PICO_SMDONLY
U$2: CR2032SMT; CR2032-SMD

Connections:
+3V3: C3.1, ESP12.3 (CH_PD), ESP12.8 (VCC), LCD1.1 (VDD), LCD1.6 (OSC), U$1.3.3V
BA: BTNA.1 (A0), BTNA.4 (A1), U$1.B7
BB: BTNB.1 (A0), BTNB.4 (A1), U$1.A8
BD: BTND.1 (A0), BTND.4 (A1), U$1.B6
BL: BTNL.1 (A0), BTNL.4 (A1), U$1.B3
BR: BTNR.1 (A0), BTNR.4 (A1), U$1.B4
BU: BTNU.1 (A0), BTNU.4 (A1), U$1.B5
ESP_RX: ESP12.15 (RXD), U$1.A2
ESP_TX: ESP12.16 (TXD), U$1.A3
GND: BTNA.2 (B0), BTNA.3 (B1), BTNB.2 (B0), BTNB.3 (B1), BTND.2 (B0), BTND.3 (B1), BTNL.2 (B0), BTNL.3 (B1), BTNR.2 (B0), BTNR.3 (B1), BTNU.2 (B0), BTNU.3 (B1), C1.2, C2.2, C3.2, ESP12.9 (GND), J1.3, J1.4, J1.-, LCD1.7 (GND), U$1.GND, U$2.-
LCD_CE: LCD1.5 (/SCE), U$1.B10
LCD_CK: LCD1.2 (SCLK), U$1.B13
LCD_DC: LCD1.4 (D/C), U$1.B14
LCD_DI: LCD1.3 (SDIN), U$1.B15
LCD_RES: LCD1.9 (/RES), U$1.B1
unnamed: C1.1, LCD1.8 (VOUT)
unnamed: J1.+, U$1.BAT, U$2.+$1 (+), U$2.+$2 (+1)
unnamed: C2.1, U$1.5V
unnamed: SP1.-, U$1.A6
unnamed: SP1.+, U$1.A5

Notes on the sheet:
TODO: Bigger holes for supercap

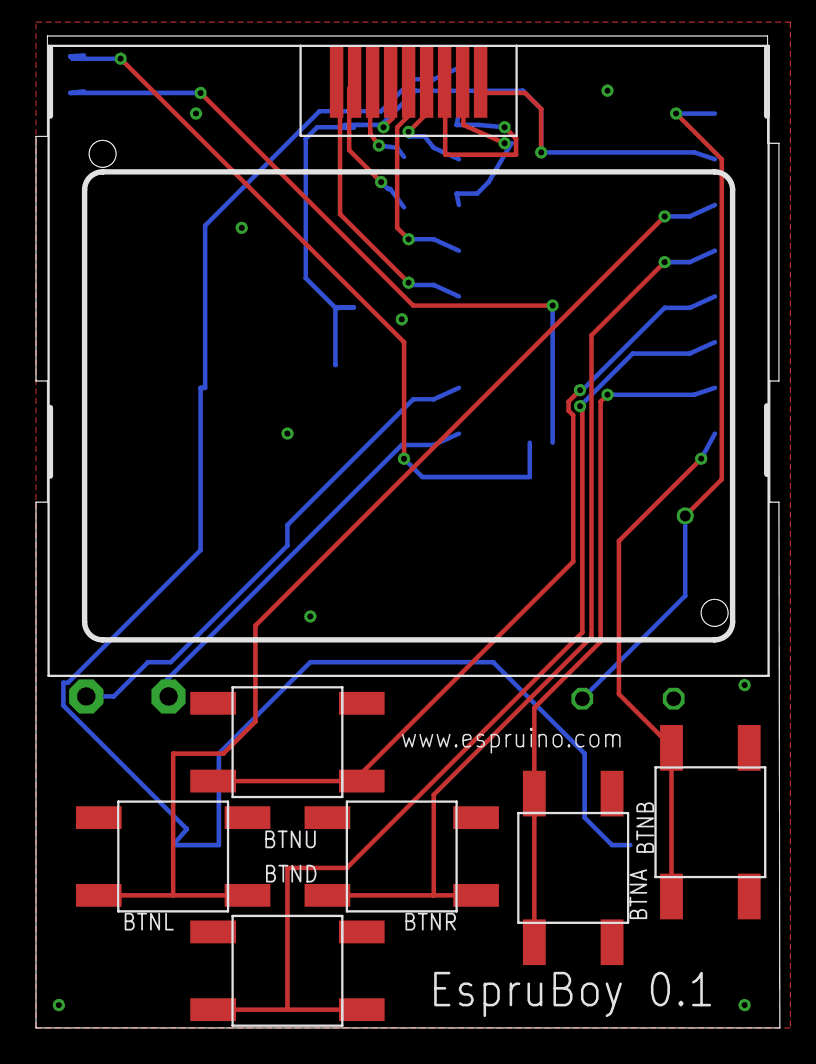
[picture p283: board espruboy.brd from above]

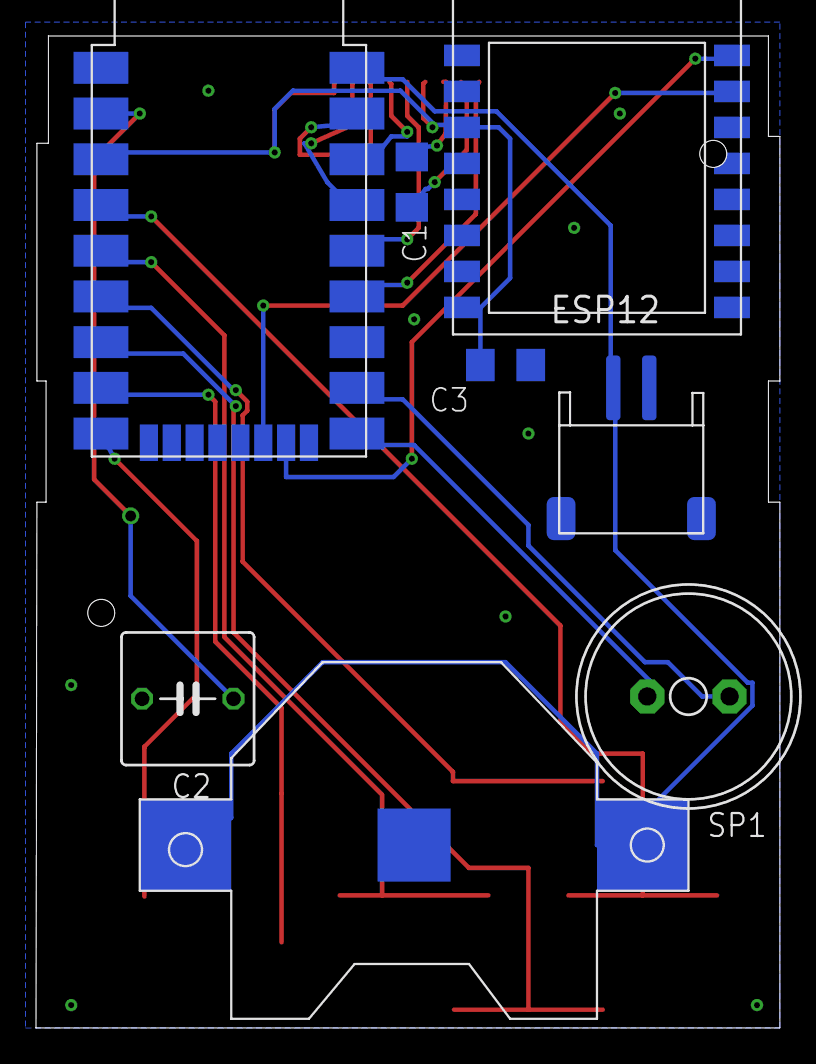
[picture p284: board espruboy.brd from below]

Board: 2 copper layers, 41.3 x 55.1 mm, 15 parts (8 on the bottom side), 20 nets.
