Leif-Rydenfalk/halo/reference/EspruinoBoard/Pico/Adaptors/eagle/rfm69.brd

## EAGLE design reference/EspruinoBoard/Pico/Adaptors/eagle/rfm69.brd (2026-09-03)

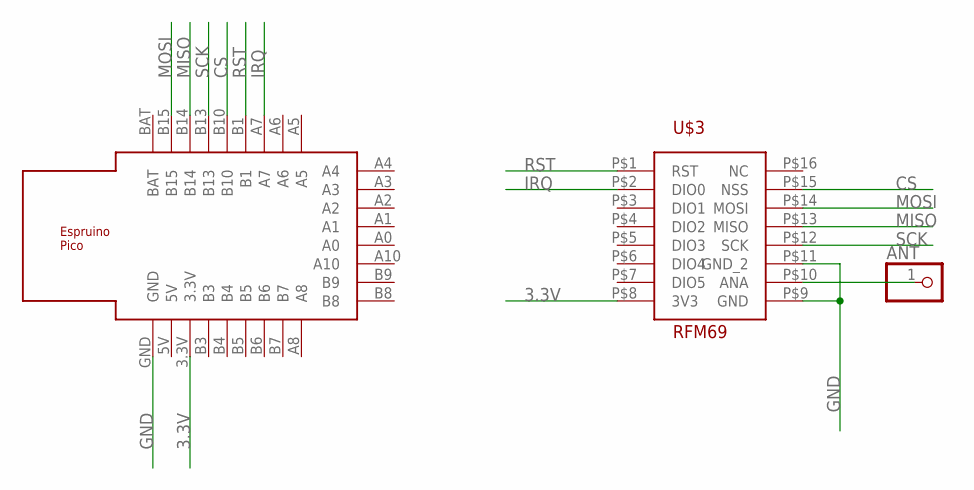
[picture p285: schematic rfm69.sch]

Parts:
ANT: PINHD-1X1; 1X01
U$1: ESPRUINO_PICO_SMDONLY
U$3: RFM69

Connections:
3.3V: U$1.3.3V, U$3.P$8 (3V3)
CS: U$1.B10, U$3.P$15 (NSS)
GND: U$1.GND, U$3.P$9 (GND), U$3.P$11 (GND_2)
IRQ: U$1.A7, U$3.P$2 (DIO0)
MISO: U$1.B14, U$3.P$13 (MISO)
MOSI: U$1.B15, U$3.P$14 (MOSI)
unnamed: ANT.1, U$3.P$10 (ANA)
RST: U$1.B1, U$3.P$1 (RST)
SCK: U$1.B13, U$3.P$12 (SCK)

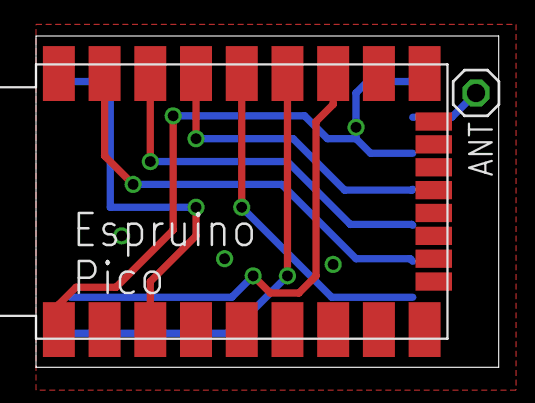
[picture p286: board rfm69.brd from above]

Board: 2 copper layers, 25.7 x 18.4 mm, 3 parts (1 on the bottom side), 9 nets.
