Leif-Rydenfalk/halo/reference/EspruinoBoard/Pico/Adaptors/eagle/servo.brd

## EAGLE design reference/EspruinoBoard/Pico/Adaptors/eagle/servo.brd (2026-09-03)

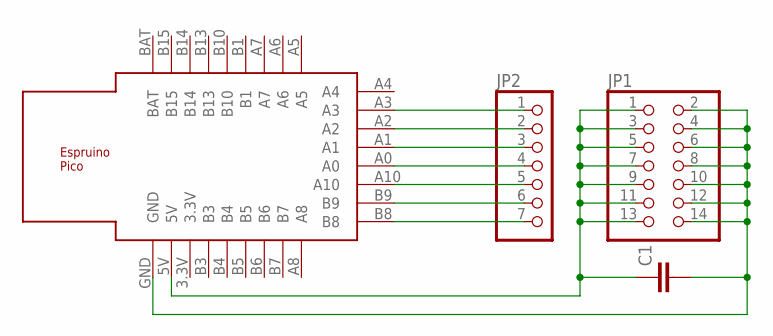
[picture p287: schematic servo.sch]

Parts:
C1: C-EUC1210; C1210
JP1: PINHD-2X7; 2X07
JP2: PINHD-1X7; 1X07
U$1: ESPRUINO_PICO_SMD

Connections:
5V: C1.1, JP1.1, JP1.3, JP1.5, JP1.7, JP1.9, JP1.11, JP1.13, U$1.5V
GND: C1.2, JP1.2, JP1.4, JP1.6, JP1.8, JP1.10, JP1.12, JP1.14, U$1.GND
unnamed: JP2.1, U$1.A3
unnamed: JP2.2, U$1.A2
unnamed: JP2.3, U$1.A1
unnamed: JP2.4, U$1.A0
unnamed: JP2.5, U$1.A10
unnamed: JP2.6, U$1.B9
unnamed: JP2.7, U$1.B8

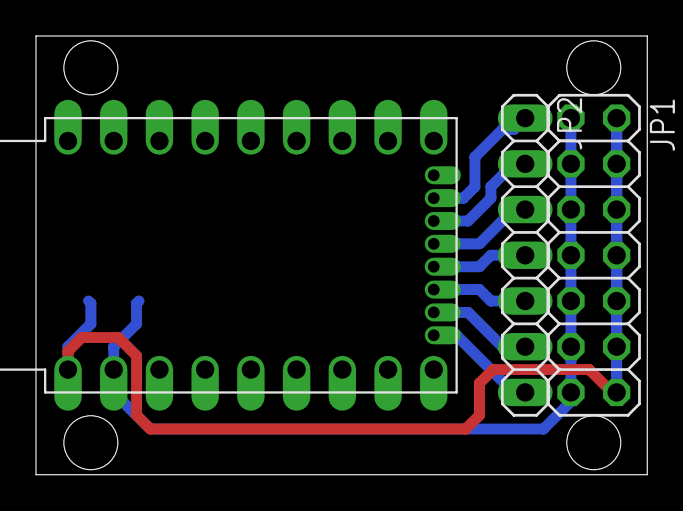
[picture p288: board servo.brd from above]

Board: 2 copper layers, 34.0 x 24.4 mm, 4 parts (1 on the bottom side), 9 nets.
