Leif-Rydenfalk/halo/reference/EspruinoBoard/Pico/Adaptors/eagle/nrf24.brd

## EAGLE design reference/EspruinoBoard/Pico/Adaptors/eagle/nrf24.brd (2026-09-03)

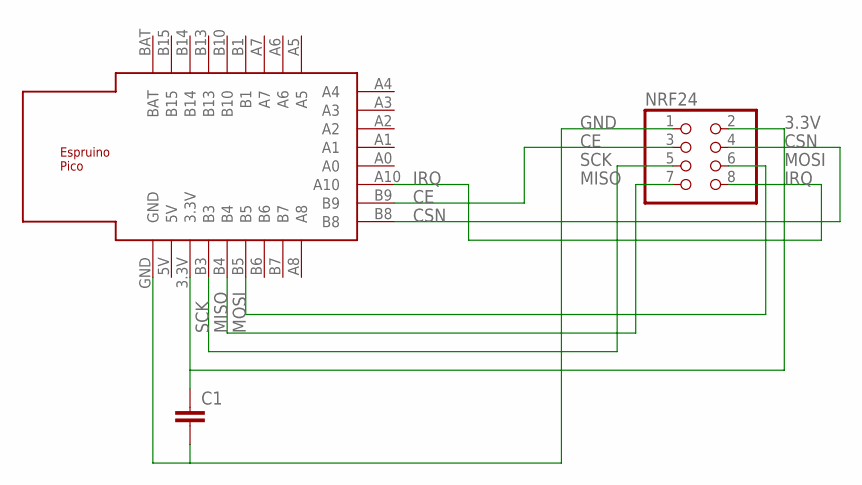
[picture p289: schematic nrf24.sch]

Parts:
C1: C-EUC1206; C1206
NRF24: PINHD-2X4; 2X04
U$2: ESPRUINO_PICO_HALFSMD

Connections:
3.3V: C1.1, NRF24.2, U$2.3.3V
CE: NRF24.3, U$2.B9
CSN: NRF24.4, U$2.B8
GND: C1.2, NRF24.1, U$2.GND
IRQ: NRF24.8, U$2.A10
MISO: NRF24.7, U$2.B4
MOSI: NRF24.6, U$2.B5
SCK: NRF24.5, U$2.B3

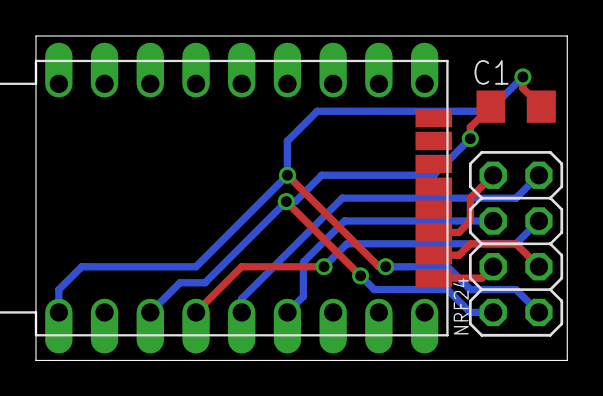
[picture p290: board nrf24.brd from above]

Board: 2 copper layers, 29.5 x 18.0 mm, 3 parts (0 on the bottom side), 8 nets.
