Leif-Rydenfalk/halo/reference/EspruinoBoard/Pico/Adaptors/eagle/robot.brd

## EAGLE design reference/EspruinoBoard/Pico/Adaptors/eagle/robot.brd (2026-09-03)

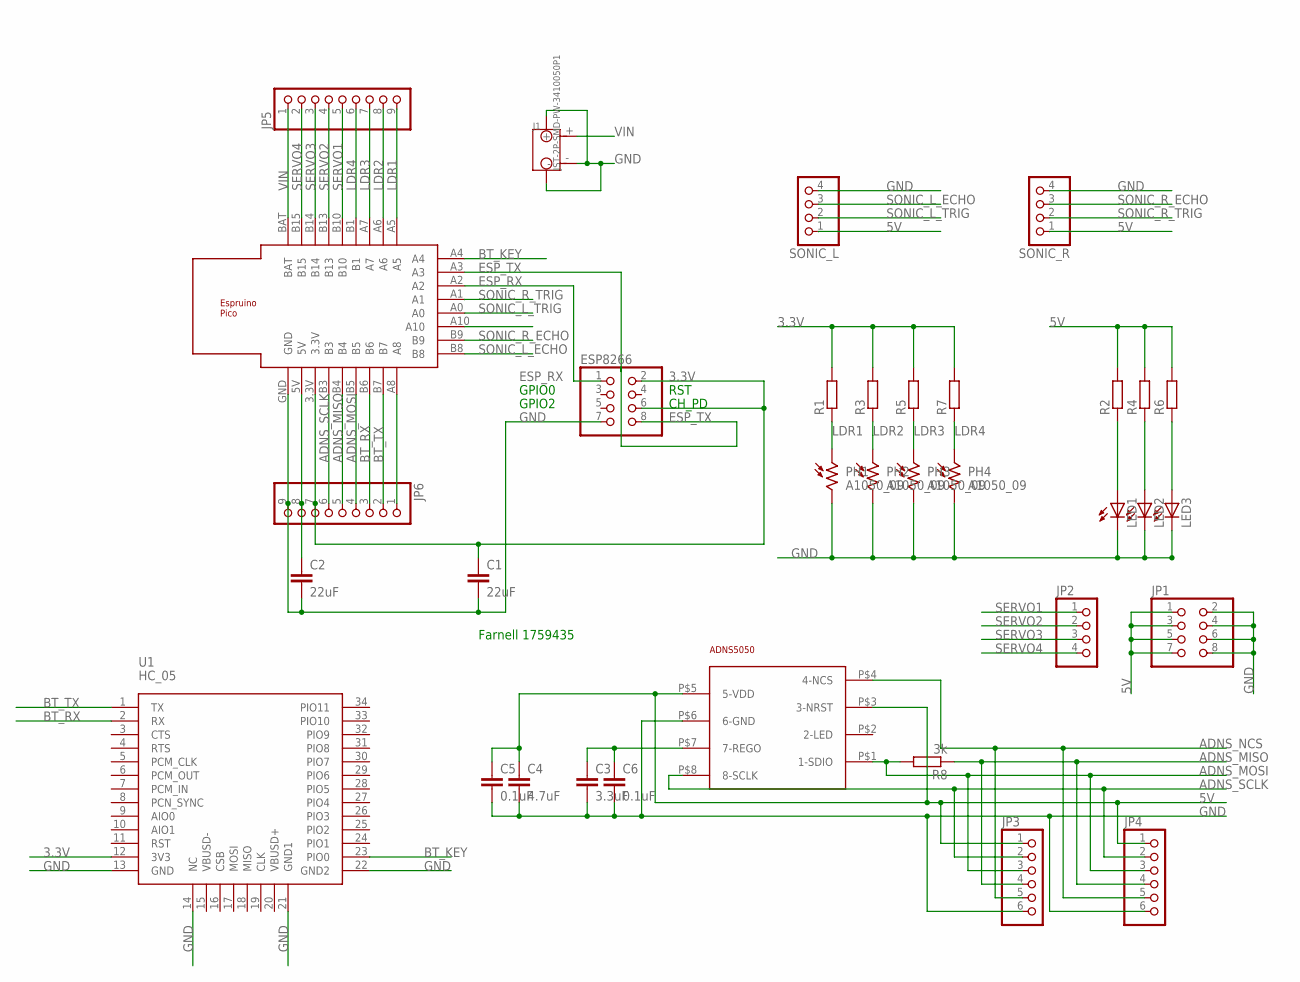
[picture p291: schematic robot.sch]

Parts:
C1, C2: 22uF; C1210
C3: 3.3uF; C1206
C4: 4.7uF; C1206
C5, C6: 0.1uF; C1206
ESP8266: PINHD-2X4; 2X04
J1: JST-2P-SMD-PW-3410050P1; 2P-SMD-2.0-90D
JP1: PINHD-2X4; 2X04
JP2: PINHD-1X4; 1X04
JP3, JP4: PINHD-1X6; 1X06
JP5, JP6: PINHD-1X9; 1X09
LED1, LED2, LED3: LED5MM
PH1, PH2, PH3, PH4: A1050_09; T0-46-A10XX
R1, R2, R3, R4, R5, R6, R7: R-EU_R1206; R1206
R8: 3k; R1206
SONIC_L: PINHD-1X4; 1X04
SONIC_R: PINHD-1X4; 1X04
U1: HC_05; BLUETOOTH_SMD
U$1: ESPRUINO_PICO_HALFSMD
U$2: ADNS5050; ADNS-5050

Connections:
3.3V: C1.1, ESP8266.2, ESP8266.6, JP6.7, R1.2, R3.2, R5.2, R7.2, U1.12 (3V3), U$1.3.3V
5V: C2.1, C4.1, C5.1, JP1.1, JP1.3, JP1.5, JP1.7, JP3.1, JP4.1, JP6.8, R2.2, R4.2, R6.2, SONIC_L.1, SONIC_R.1, U$1.5V, U$2.P$3 (3-NRST), U$2.P$5 (5-VDD)
ADNS_MISO: JP3.4, JP4.4, JP6.5, R8.1, U$1.B4
ADNS_MOSI: JP3.3, JP4.3, JP6.4, R8.2, U$1.B5, U$2.P$1 (1-SDIO)
ADNS_NCS: JP3.5, JP4.5, U$1.A10, U$2.P$4 (4-NCS)
ADNS_SCLK: JP3.2, JP4.2, JP6.6, U$1.B3, U$2.P$8 (8-SCLK)
BT_KEY: U1.23 (PIO0), U$1.A4
BT_RX: JP6.3, U1.2 (RX), U$1.B6
BT_TX: JP6.2, U1.1 (TX), U$1.B7
ESP_RX: ESP8266.1, U$1.A2
ESP_TX: ESP8266.8, U$1.A3
GND: C1.2, C2.2, C3.2, C4.2, C5.2, C6.2, ESP8266.7, J1.3, J1.4, J1.-, JP1.2, JP1.4, JP1.6, JP1.8, JP3.6, JP4.6, JP6.9, LED1.K (C), LED2.K (C), LED3.K (C), PH1.2, PH2.2, PH3.2, PH4.2, SONIC_L.4, SONIC_R.4, U1.13 (GND), U1.14 (NC), U1.21 (GND1), U1.22 (GND2), U$1.GND, U$2.P$6 (6-GND)
LDR1: JP5.9, PH1.1, R1.1, U$1.A5
LDR2: JP5.8, PH2.1, R3.1, U$1.A6
LDR3: JP5.7, PH3.1, R5.1, U$1.A7
LDR4: JP5.6, PH4.1, R7.1, U$1.B1
unnamed: JP6.1, U$1.A8
unnamed: C3.1, C6.1, U$2.P$7 (7-REGO)
unnamed: LED3.A, R6.1
unnamed: LED2.A, R4.1
unnamed: LED1.A, R2.1
SERVO1: JP2.1, JP5.5, U$1.B10
SERVO2: JP2.2, JP5.4, U$1.B13
SERVO3: JP2.3, JP5.3, U$1.B14
SERVO4: JP2.4, JP5.2, U$1.B15
SONIC_L_ECHO: SONIC_L.3, U$1.B8
SONIC_L_TRIG: SONIC_L.2, U$1.A0
SONIC_R_ECHO: SONIC_R.3, U$1.B9
SONIC_R_TRIG: SONIC_R.2, U$1.A1
VIN: J1.+, JP5.1, U$1.BAT

Notes on the sheet:
CH_PD
RST
GPIO0
GPIO2
Farnell 1759435

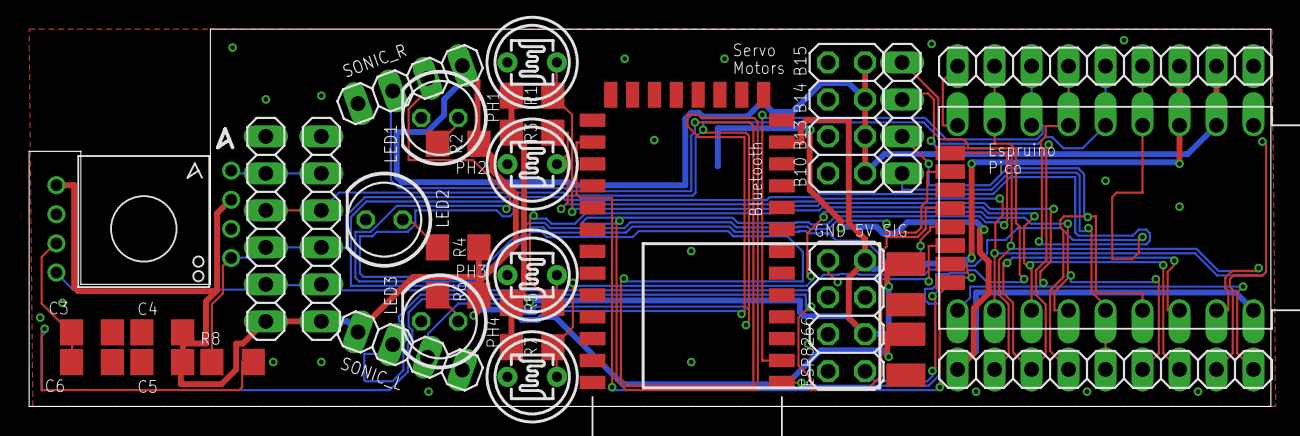
[picture p292: board robot.brd from above]

Board: 2 copper layers, 85.3 x 25.9 mm, 34 parts (1 on the bottom side), 30 nets.
