Leif-Rydenfalk/halo/reference/EspruinoBoard/Pico/Adaptors/eagle/arduino.brd

## EAGLE design reference/EspruinoBoard/Pico/Adaptors/eagle/arduino.brd (2026-09-03)

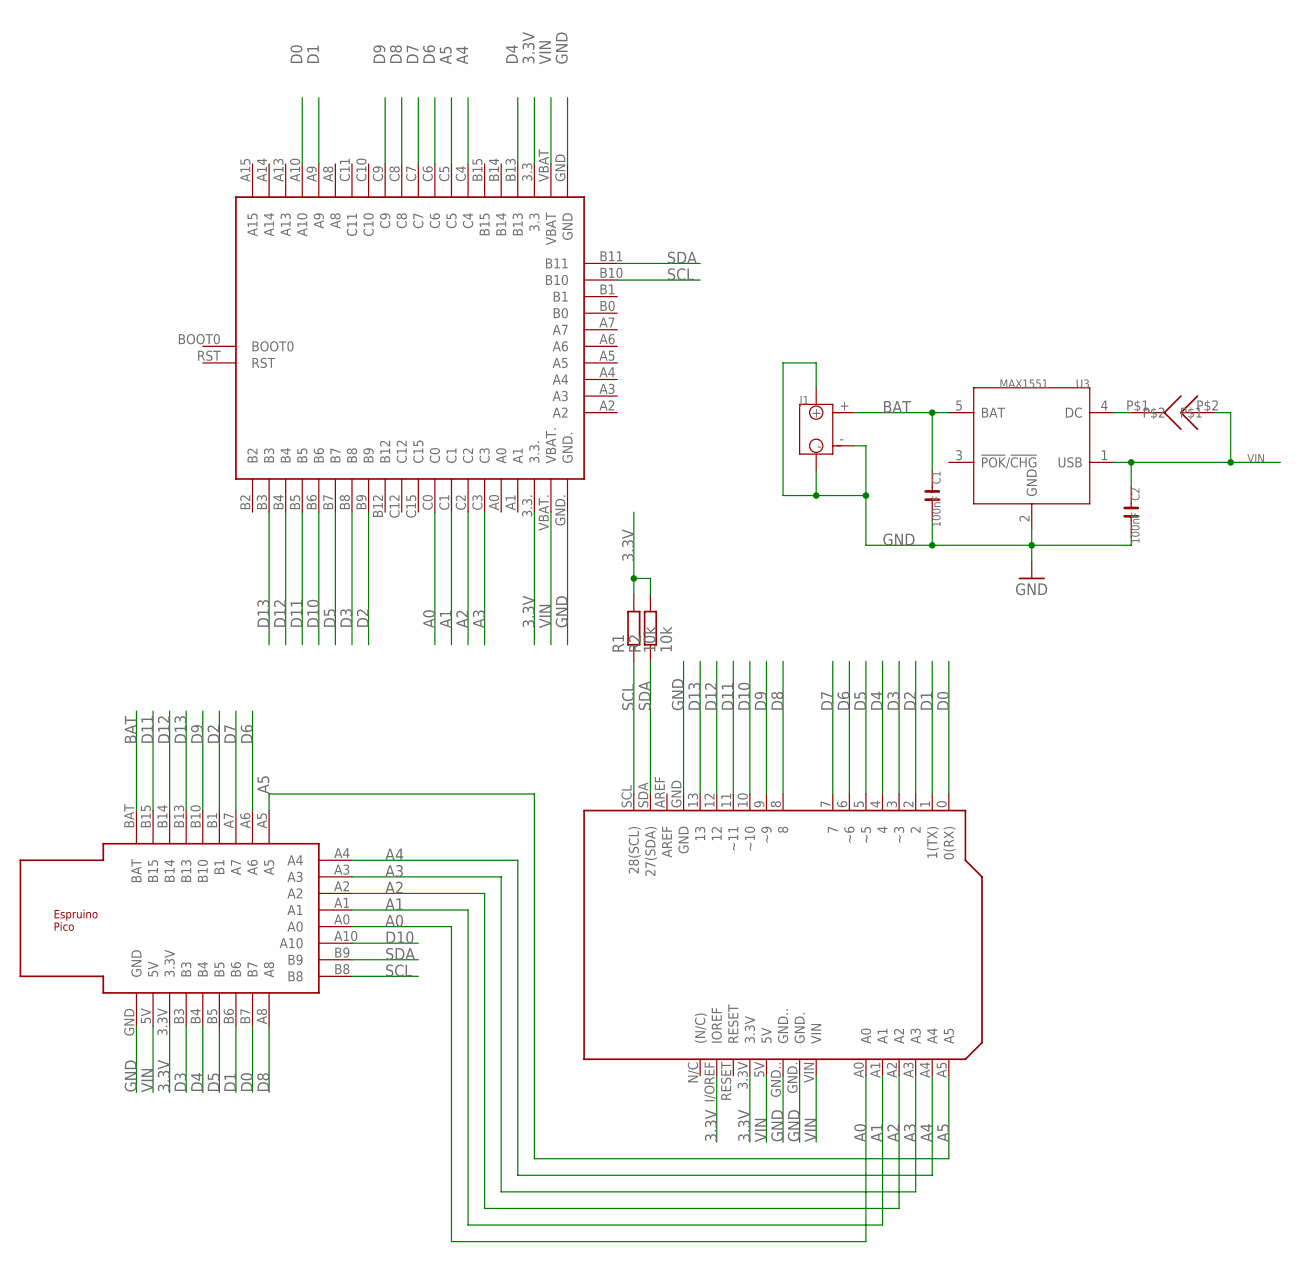
[picture p293: schematic arduino.sch]

Parts:
C1, C2: 100nF; C0603
J1: JST-2P-SMD-PW-3410050P1; 2P-SMD-2.0-90D
R1, R2: 10k; R0805
U3: MAX1551; SOT23-5
U$1: ESPRUINO_PICO_SMD
U$2: ARDUINO
U$3: ESPRUINO
U$4: SOLDERJUMPER

Connections:
3.3V: R1.2, R2.2, U$1.3.3V, U$2.3.3V, U$2.I/OREF (IOREF), U$3.3.3, U$3.3.3.
A0: U$1.A0, U$2.A0, U$3.C0
A1: U$1.A1, U$2.A1, U$3.C1
A2: U$1.A2, U$2.A2, U$3.C2
A3: U$1.A3, U$2.A3, U$3.C3
A4: U$1.A4, U$2.A4, U$3.C4
A5: U$1.A5, U$2.A5, U$3.C5
BAT: C1.1, J1.+, U3.5 (BAT), U$1.BAT
D0: U$1.B7, U$2.0 (0(RX)), U$3.A10
D1: U$1.B6, U$2.1 (1(TX)), U$3.A9
D2: U$1.B1, U$2.2, U$3.B9
D3: U$1.B3, U$2.3 (~3), U$3.B8
D4: U$1.B4, U$2.4, U$3.B13
D5: U$1.B5, U$2.5 (~5), U$3.B7
D6: U$1.A6, U$2.6 (~6), U$3.C6
D7: U$1.A7, U$2.7, U$3.C7
D8: U$1.A8, U$2.8, U$3.C8
D9: U$1.B10, U$2.9 (~9), U$3.C9
D10: U$1.A10, U$2.10 (~10), U$3.B6
D11: U$1.B15, U$2.11 (~11), U$3.B5
D12: U$1.B14, U$2.12, U$3.B4
D13: U$1.B13, U$2.13, U$3.B3
GND: C1.2, C2.2, J1.3, J1.4, J1.-, U3.2 (GND), U$1.GND, U$2.GND, U$2.GND., U$2.GND.., U$3.GND, U$3.GND.
unnamed: U3.4 (DC), U$4.P$1
SCL: R1.1, U$1.B8, U$2.SCL (28(SCL)), U$3.B10
SDA: R2.1, U$1.B9, U$2.SDA (27(SDA)), U$3.B11
VIN: C2.1, U3.1 (USB), U$1.5V, U$2.5V, U$2.VIN, U$3.VBAT, U$3.VBAT., U$4.P$2
