Leif-Rydenfalk/halo/reference/EspruinoBoard/Pico/Adaptors/eagle/arduino.brd

## EAGLE design reference/EspruinoBoard/Pico/Adaptors/eagle/arduino.brd (continued)

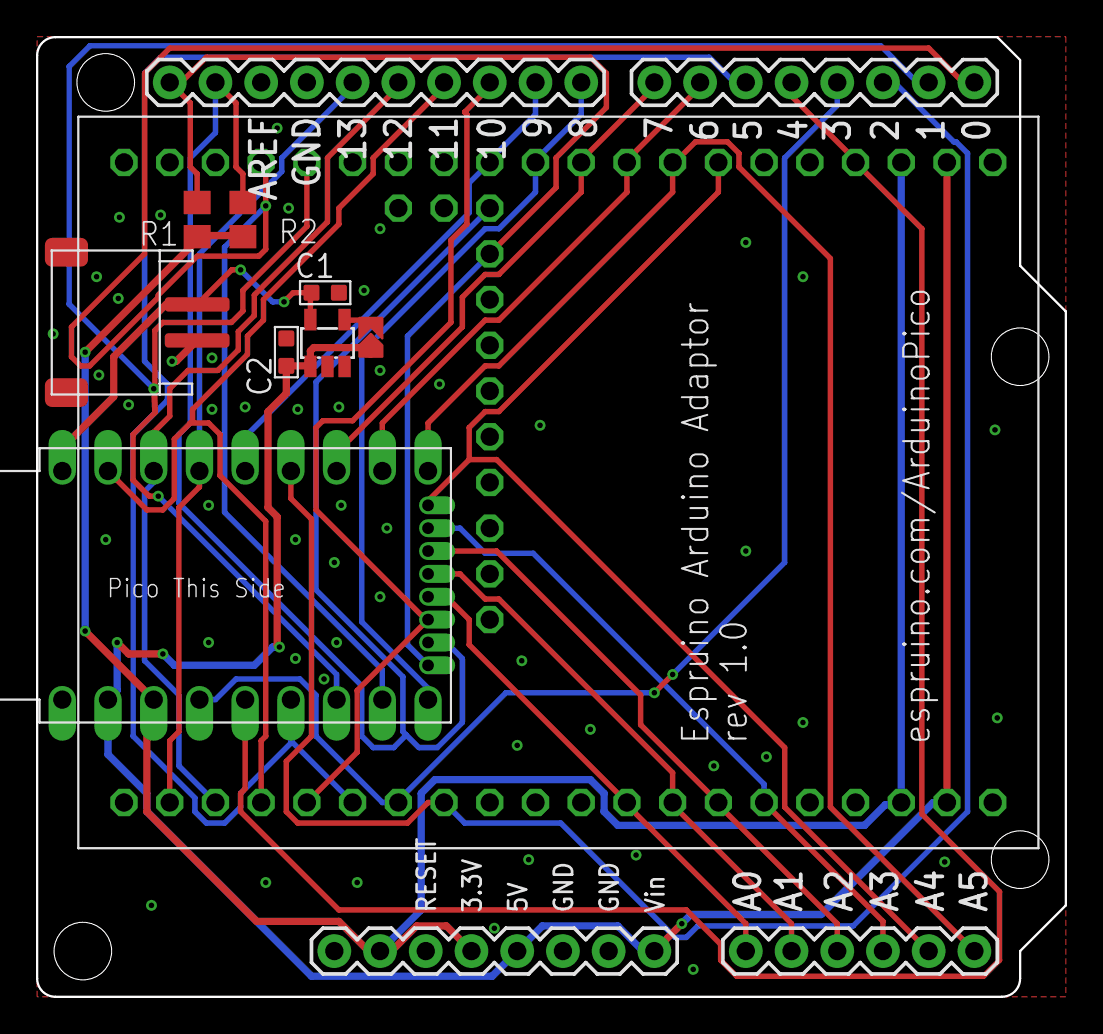
[picture p294: board arduino.brd from above]

Board: 2 copper layers, 57.1 x 53.3 mm, 10 parts (0 on the bottom side), 27 nets.
