Leif-Rydenfalk/halo/reference/EspruinoBoard/WiFi/eagle/espruino_wifi.brd

## EAGLE design reference/EspruinoBoard/WiFi/eagle/espruino_wifi.brd (2026-09-03)

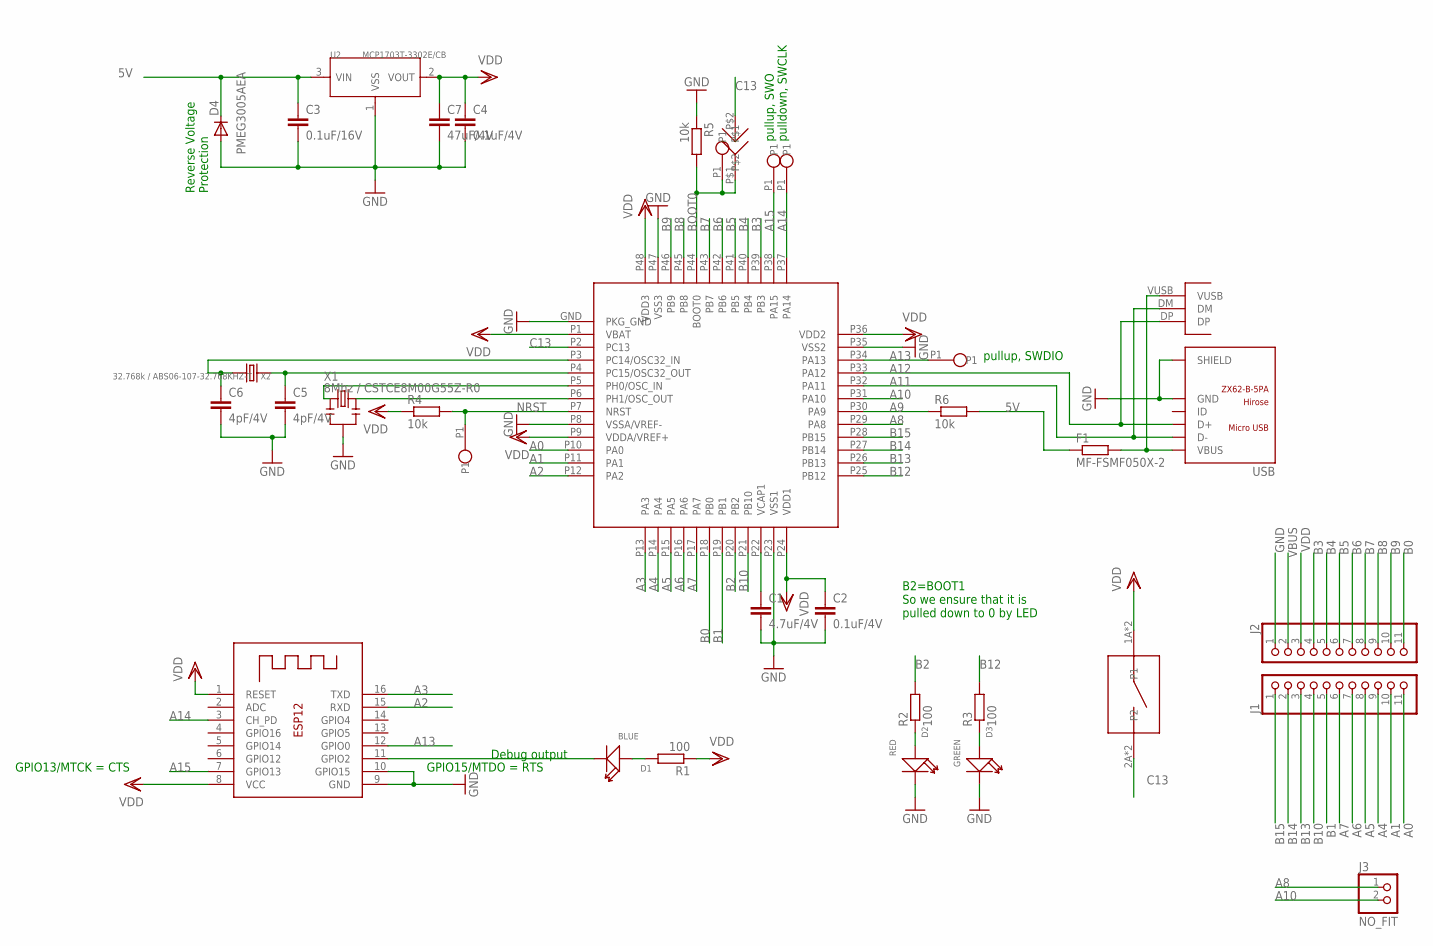
[picture p295: schematic espruino_wifi.sch]

Parts:
B1: KMR421NG
C1: 4.7uF/4V; C0402
C2, C4: 0.1uF/4V; C0402
C3: 0.1uF/16V; C0402
C5, C6: 4pF/4V; C0402
C7: 47uF/4V; C1210
D1: BLUE; LED-0402
D2: RED; LED-0402
D3: GREEN; LED-0402
D4: PMEG3005AEA; SOD323-W
F1: MF-FSMF050X-2; R0603
J1, J2: PINHD-1X11_2.54-S; 1X11-S
J3: NO_FIT; 1X02-S
J4: NO_FIT; SOLDERJUMPER
PBOOT0: NO_FIT; SINGLE
PNRST: NO_FIT; SINGLE
PSWCLK: NO_FIT; SINGLE
PSWDIO: NO_FIT; SINGLE
PSWO: NO_FIT; SINGLE
PUSB: NO_FIT; USB
R1, R2, R3: 100; R0402
R4, R5, R6: 10k; R0402
U1: STM32F411CEU6; UFQFPN48
U2: MCP1703T-3302E/CB; SOT23
U3: ESP-12
USB: ZX62-B-5PA; MICRO-USB5+6P-SMD-0.65-AB
X1: 8Mhz / CSTCE8M00G55Z-R0; 3P-SMD-3.6X1.3
X2: 32.768k / ABS06-107-32.768KHZ-T; 2P-SMD-2.05X1.2

Connections:
5V: C3.1, D4.C, F1.1, R6.2, U2.3 (VIN)
A0: J1.11, U1.P10 (PA0)
A1: J1.10, U1.P11 (PA1)
A2: U1.P12 (PA2), U3.15 (RXD)
A3: U1.P13 (PA3), U3.16 (TXD)
A4: J1.9, U1.P14 (PA4)
A5: J1.8, U1.P15 (PA5)
A6: J1.7, U1.P16 (PA6)
A7: J1.6, U1.P17 (PA7)
A8: J3.1, U1.P29 (PA8)
A9: R6.1, U1.P30 (PA9)
A10: J3.2, U1.P31 (PA10)
A11: PUSB.DM, U1.P32 (PA11), USB.2 (D-)
A12: PUSB.DP, U1.P33 (PA12), USB.3 (D+)
A13: PSWDIO.P1, U1.P34 (PA13), U3.12 (GPIO0)
A14: PSWCLK.P1, U1.P37 (PA14), U3.3 (CH_PD)
A15: PSWO.P1, U1.P38 (PA15), U3.7 (GPIO13)
B0: J2.11, U1.P18 (PB0)
B1: J1.5, U1.P19 (PB1)
B2: R2.2, U1.P20 (PB2)
B3: J2.4, U1.P39 (PB3)
B4: J2.5, U1.P40 (PB4)
B5: J2.6, U1.P41 (PB5)
B6: J2.7, U1.P42 (PB6)
B7: J2.8, U1.P43 (PB7)
B8: J2.9, U1.P45 (PB8)
B9: J2.10, U1.P46 (PB9)
B10: J1.4, U1.P21 (PB10)
B12: R3.2, U1.P25 (PB12)
B13: J1.3, U1.P26 (PB13)
B14: J1.2, U1.P27 (PB14)
B15: J1.1, U1.P28 (PB15)
BOOT0: J4.P$1, PBOOT0.P1, R5.2, U1.P44 (BOOT0)
C13: B1.2A (P2), B1.2B (P2), J4.P$2, U1.P2 (PC13)
GND: C1.3 (2), C2.3 (2), C3.3 (2), C4.3 (2), C5.3 (2), C6.3 (2), C7.2, D2.-, D3.-, D4.A, J2.1, R5.1, U1.GND (PKG_GND), U1.P8 (VSSA/VREF-), U1.P23 (VSS1), U1.P35 (VSS2), U1.P47 (VSS3), U2.1 (VSS), U3.9 (GND), U3.10 (GPIO15), USB.5 (GND), USB.P1 (SHIELD), USB.P2 (SHIELD), USB.P3 (SHIELD), USB.P4 (SHIELD), USB.P5 (SHIELD), USB.P6 (SHIELD), X1.2
unnamed: C5.1, U1.P4 (PC15/OSC32_OUT), X2.1
unnamed: C6.1, U1.P3 (PC14/OSC32_IN), X2.2
unnamed: U1.P5 (PH0/OSC_IN), X1.1
unnamed: U1.P6 (PH1/OSC_OUT), X1.3
unnamed: D2.+, R2.1
unnamed: D3.+, R3.1
unnamed: D1.+, R1.2
unnamed: D1.-, U3.11 (GPIO2)
unnamed: C1.1, U1.P22 (VCAP1)
NRST: PNRST.P1, R4.2, U1.P7 (NRST)
VBUS: F1.2, J2.2, PUSB.VUSB, USB.1 (VBUS)
VDD: B1.1A (P1), B1.1B (P1), C2.1, C4.1, C7.1, J2.3, R1.1, R4.1, U1.P1 (VBAT), U1.P9 (VDDA/VREF+), U1.P24 (VDD1), U1.P36 (VDD2), U1.P48 (VDD3), U2.2 (VOUT), U3.1 (RESET), U3.8 (VCC)

Notes on the sheet:
B2=BOOT1 So we ensure that it is pulled down to 0 by LED
Debug output
pulldown, SWCLK
pullup, SWO
pullup, SWDIO
GPIO13/MTCK = CTS
GPIO15/MTDO = RTS
Reverse Voltage Protection

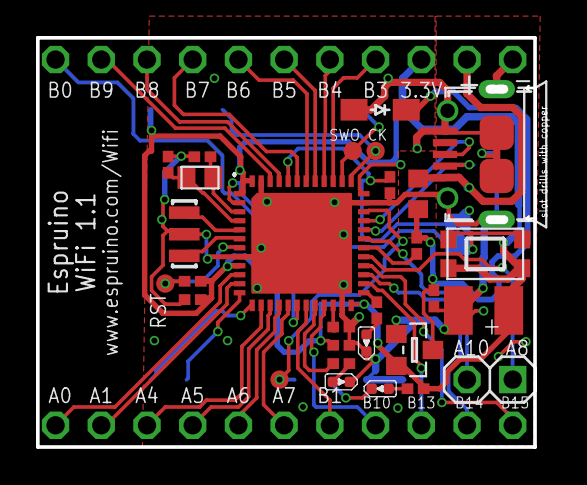
[picture p296: board espruino_wifi.brd from above]

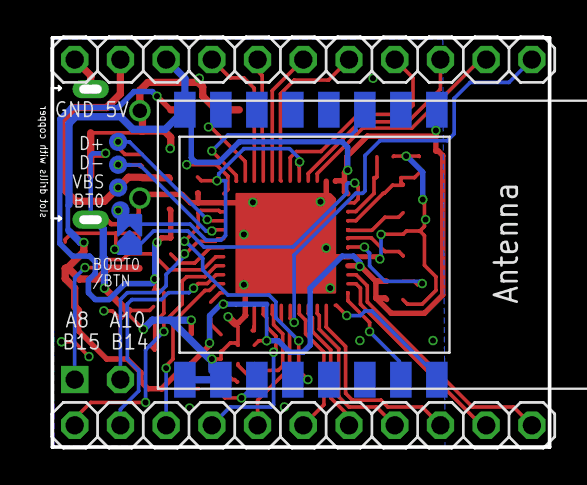
[picture p297: board espruino_wifi.brd from below]

Board: 2 copper layers, 27.6 x 22.7 mm, 35 parts (6 on the bottom side), 47 nets.
