Leif-Rydenfalk/halo/reference/EspruinoBoard/Pico/Adaptors/eagle/buttons.brd

## EAGLE design reference/EspruinoBoard/Pico/Adaptors/eagle/buttons.brd (2026-09-03)

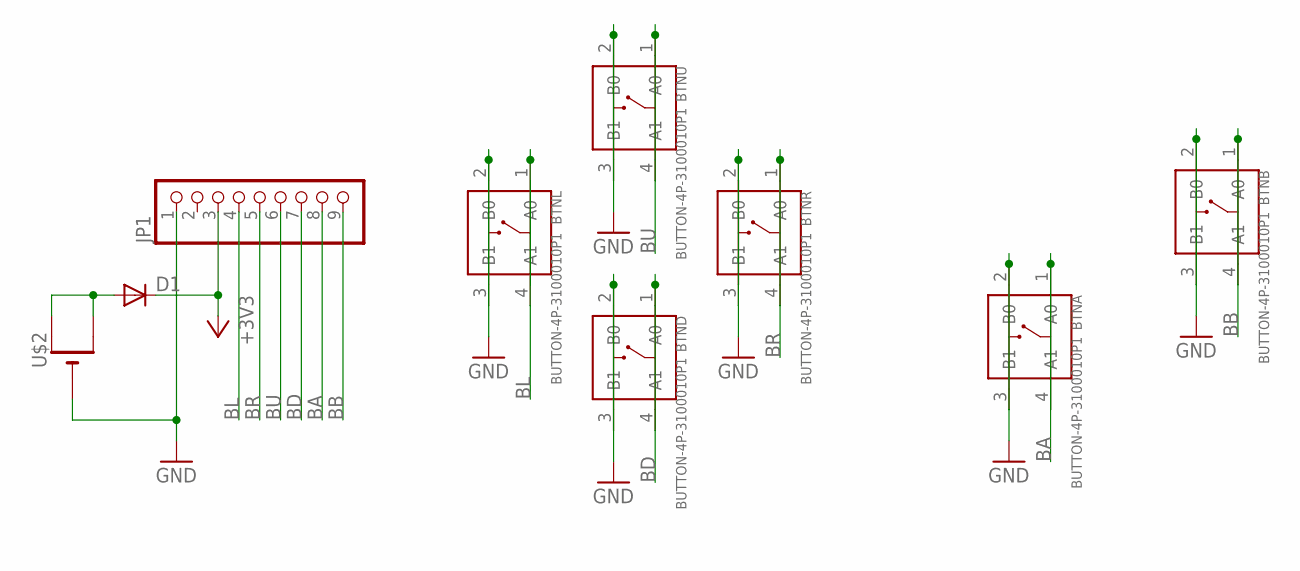
[picture p298: schematic buttons.sch]

Parts:
BTNA: BUTTON-4P-3100010P1; 4P-SMD-6.0X6.0X5.0H
BTNB: BUTTON-4P-3100010P1; 4P-SMD-6.0X6.0X5.0H
BTND: BUTTON-4P-3100010P1; 4P-SMD-6.0X6.0X5.0H
BTNL: BUTTON-4P-3100010P1; 4P-SMD-6.0X6.0X5.0H
BTNR: BUTTON-4P-3100010P1; 4P-SMD-6.0X6.0X5.0H
BTNU: BUTTON-4P-3100010P1; 4P-SMD-6.0X6.0X5.0H
D1: DIODE-SOD323-W; SOD323-W
JP1: PINHD-1X9; 1X09
U$2: CR2032SMT; CR2032-SMD

Connections:
+3V3: D1.C, JP1.3
BA: BTNA.1 (A0), BTNA.4 (A1), JP1.8
BB: BTNB.1 (A0), BTNB.4 (A1), JP1.9
BD: BTND.1 (A0), BTND.4 (A1), JP1.7
BL: BTNL.1 (A0), BTNL.4 (A1), JP1.4
BR: BTNR.1 (A0), BTNR.4 (A1), JP1.5
BU: BTNU.1 (A0), BTNU.4 (A1), JP1.6
GND: BTNA.2 (B0), BTNA.3 (B1), BTNB.2 (B0), BTNB.3 (B1), BTND.2 (B0), BTND.3 (B1), BTNL.2 (B0), BTNL.3 (B1), BTNR.2 (B0), BTNR.3 (B1), BTNU.2 (B0), BTNU.3 (B1), JP1.1, U$2.-
unnamed: D1.A, U$2.+$1 (+), U$2.+$2 (+1)

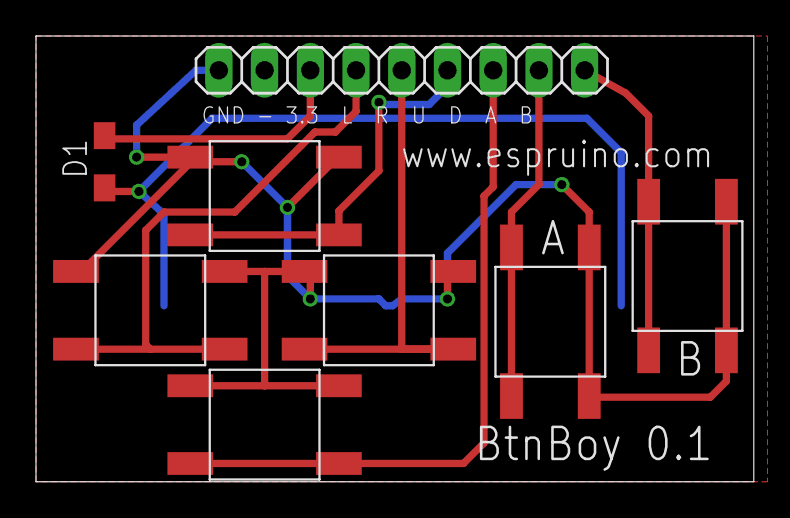
[picture p299: board buttons.brd from above]

Board: 2 copper layers, 39.9 x 24.8 mm, 9 parts (1 on the bottom side), 9 nets.
