Leif-Rydenfalk/halo/reference/EspruinoBoard/Pico/Adaptors/eagle/bluetooth_header.brd

## EAGLE design reference/EspruinoBoard/Pico/Adaptors/eagle/bluetooth_header.brd (2026-09-03)

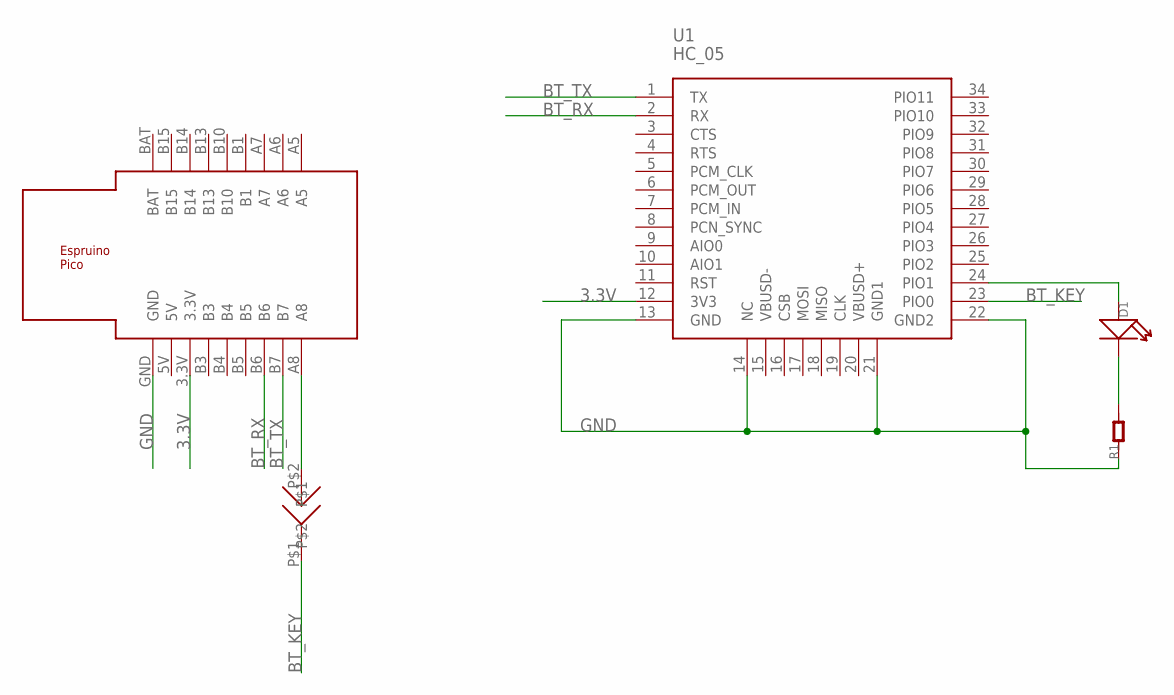
[picture p300: schematic bluetooth_header.sch]

Parts:
D1: LED; LED0603
R1: R-0603; R0603
U1: HC_05; BLUETOOTH_SMD
U$1: ESPRUINO_PICO_0.1
U$2: SOLDERJUMPER

Connections:
3.3V: U1.12 (3V3), U$1.3.3V
BT_KEY: U1.23 (PIO0), U$2.P$1
BT_RX: U1.2 (RX), U$1.B6
BT_TX: U1.1 (TX), U$1.B7
GND: R1.1, U1.13 (GND), U1.14 (NC), U1.21 (GND1), U1.22 (GND2), U$1.GND
unnamed: D1.+, U1.24 (PIO1)
unnamed: D1.-, R1.2
unnamed: U$1.A8, U$2.P$2

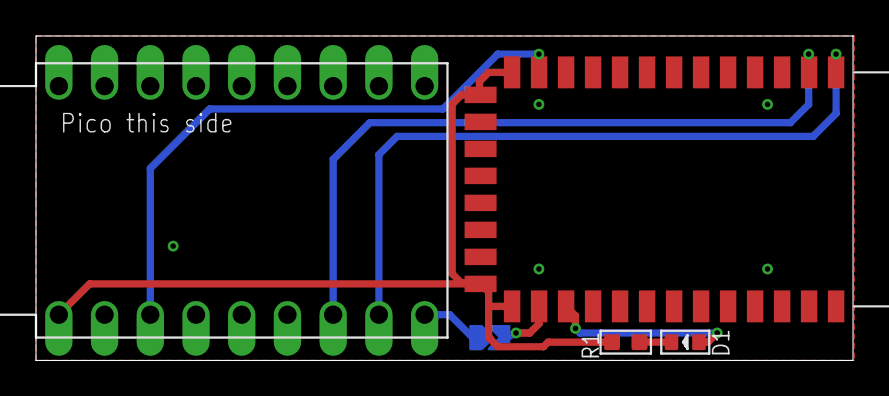
[picture p301: board bluetooth_header.brd from above]

Board: 2 copper layers, 45.4 x 18.0 mm, 5 parts (1 on the bottom side), 8 nets.
