Leif-Rydenfalk/halo/reference/EspruinoBoard/Pico/Adaptors/eagle/terminal.brd

## EAGLE design reference/EspruinoBoard/Pico/Adaptors/eagle/terminal.brd (2026-09-03)

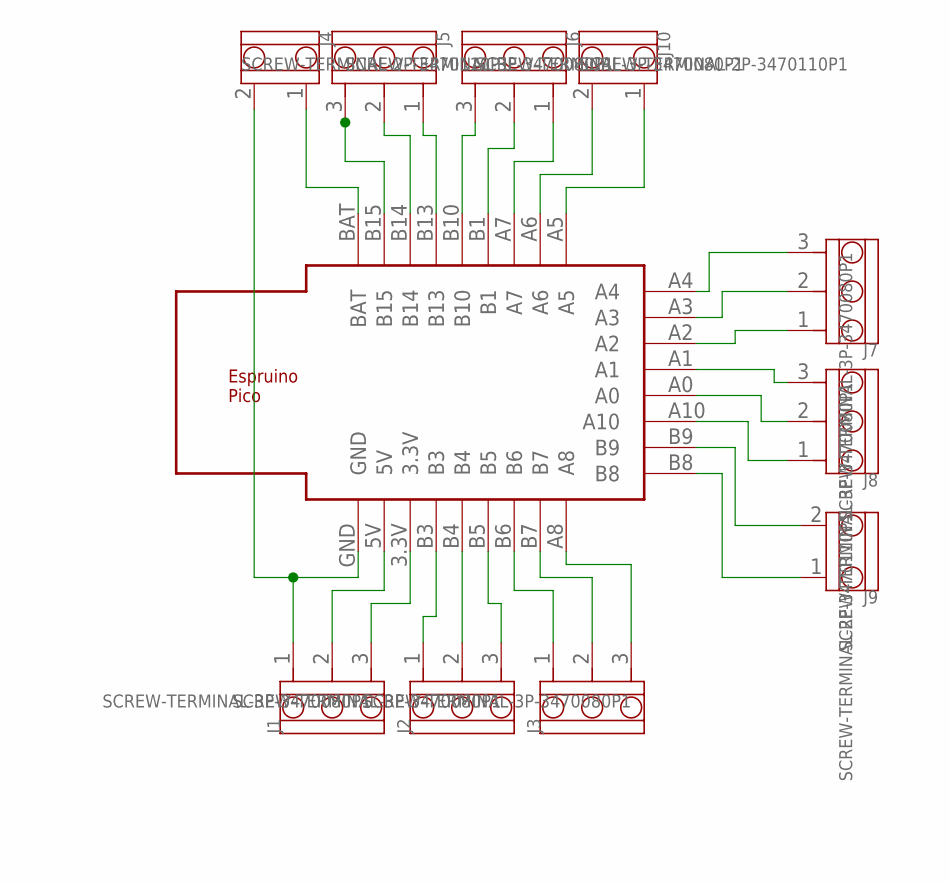
[picture p302: schematic terminal.sch]

Parts:
J1, J2, J3, J5, J6, J7, J8: SCREW-TERMINAL-3P-3470080P1; 3P-5.0
J4, J9, J10: SCREW-TERMINAL-2P-3470110P1; 2P-5.0
U$1: ESPRUINO_PICO_SMD

Connections:
unnamed: J4.1, U$1.BAT
unnamed: J5.3, U$1.B15
unnamed: J5.2, U$1.B14
unnamed: J5.1, U$1.B13
unnamed: J6.3, U$1.B10
unnamed: J6.2, U$1.B1
unnamed: J6.1, U$1.A7
unnamed: J10.2, U$1.A6
unnamed: J10.1, U$1.A5
unnamed: J7.3, U$1.A4
unnamed: J7.2, U$1.A3
unnamed: J7.1, U$1.A2
unnamed: J8.3, U$1.A1
unnamed: J8.2, U$1.A0
unnamed: J8.1, U$1.A10
unnamed: J9.2, U$1.B9
unnamed: J9.1, U$1.B8
unnamed: J3.3, U$1.A8
unnamed: J3.2, U$1.B7
unnamed: J3.1, U$1.B6
unnamed: J2.3, U$1.B5
unnamed: J2.2, U$1.B4
unnamed: J2.1, U$1.B3
unnamed: J1.3, U$1.3.3V
unnamed: J1.2, U$1.5V
unnamed: J1.1, J4.2, U$1.GND

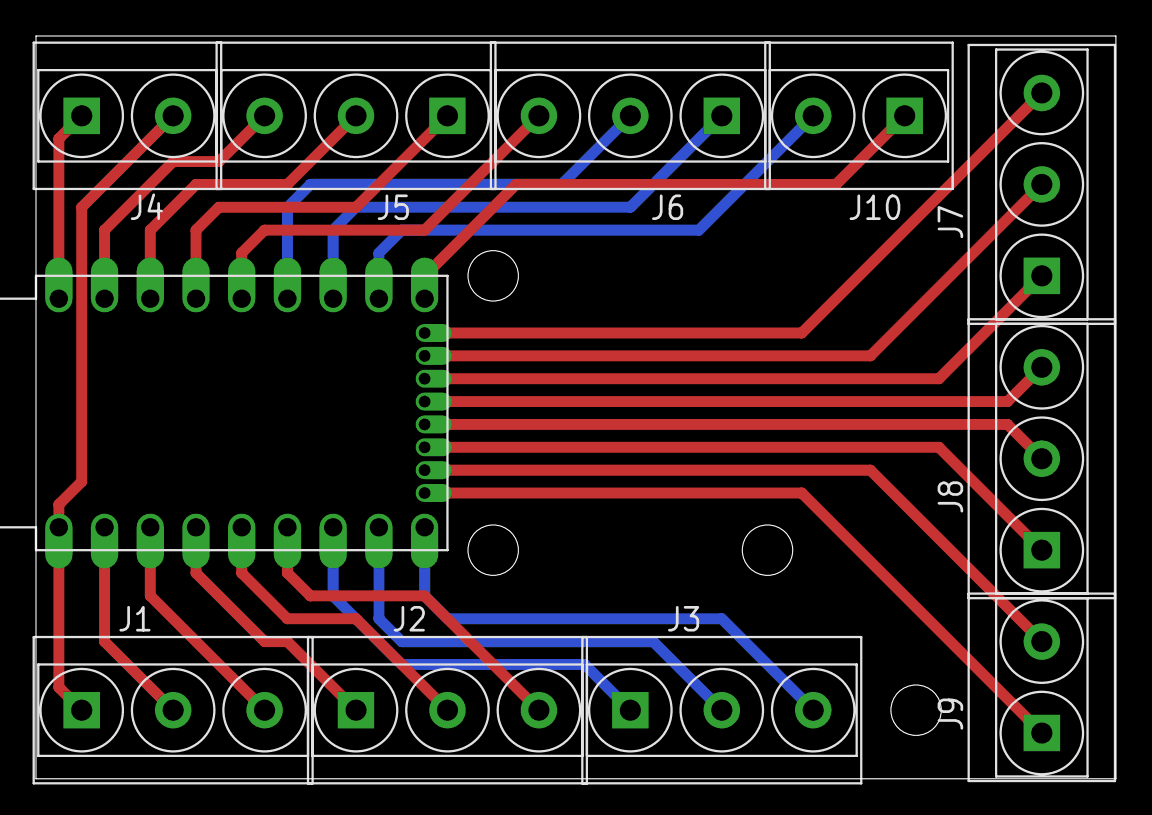
[picture p303: board terminal.brd from above]

Board: 2 copper layers, 60.0 x 41.3 mm, 11 parts (0 on the bottom side), 26 nets.
