Leif-Rydenfalk/halo/reference/EspruinoBoard/Pico/Adaptors/eagle/rfm12b.brd

## EAGLE design reference/EspruinoBoard/Pico/Adaptors/eagle/rfm12b.brd (2026-09-03)

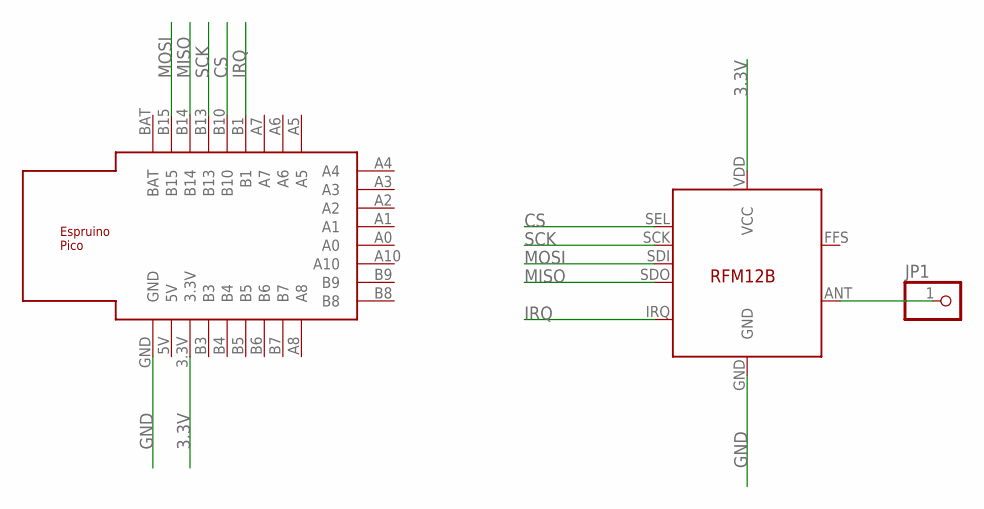
[picture p304: schematic rfm12b.sch]

Parts:
JP1: PINHD-1X1; 1X01
U$1: ESPRUINO_PICO_SMDONLY
U$2: RFM12B

Connections:
3.3V: U$1.3.3V, U$2.VDD (VCC)
CS: U$1.B10, U$2.SEL
GND: U$1.GND, U$2.GND
IRQ: U$1.B1, U$2.IRQ
MISO: U$1.B14, U$2.SDO
MOSI: U$1.B15, U$2.SDI
unnamed: JP1.1, U$2.ANT
SCK: U$1.B13, U$2.SCK

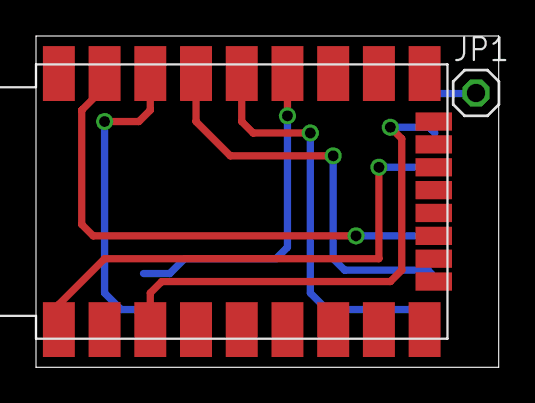
[picture p305: board rfm12b.brd from above]

Board: 2 copper layers, 25.7 x 18.4 mm, 3 parts (1 on the bottom side), 8 nets.
