Leif-Rydenfalk/halo/reference/EspruinoBoard/Pixl.js/eagle/pixljs.brd

## EAGLE design reference/EspruinoBoard/Pixl.js/eagle/pixljs.brd (2026-09-03)

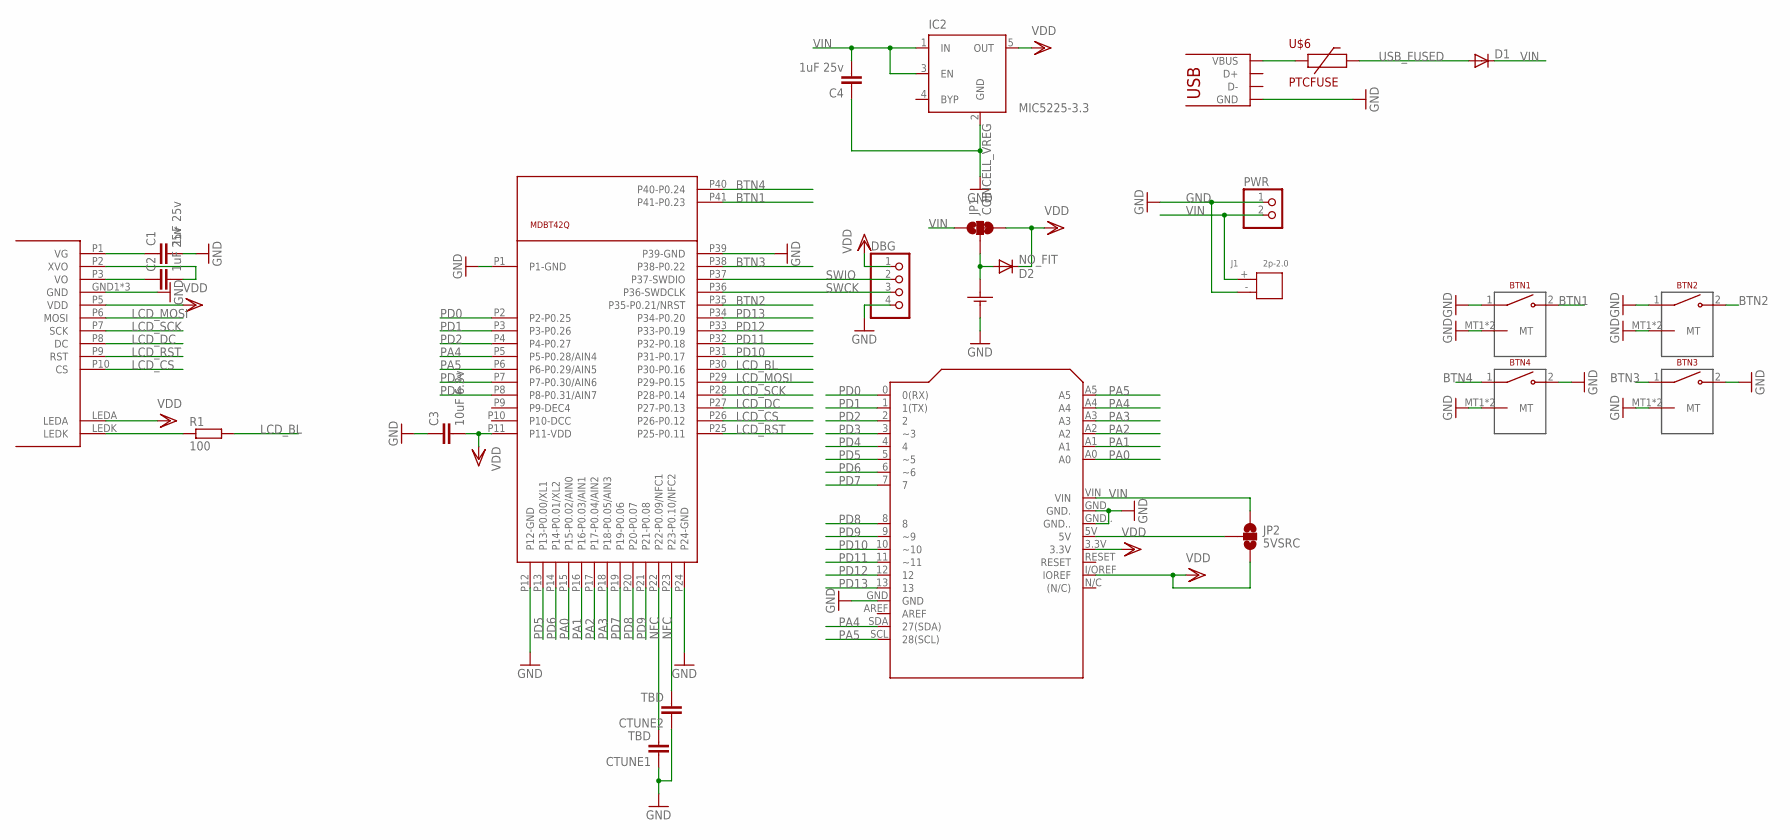
[picture p306: schematic pixljs.sch]

Parts:
BTN1, BTN2, BTN3, BTN4: TACT_MINI_RIGHT_ANGLEMEDI; TACT_MEDI_RIGHT_ANGLE
C1, C2, C4: 1uF 25v; C0603K
C3: 10uF 6.3v; C0603K
CTUNE1, CTUNE2: TBD; C0603K
D1: DIODE-SOD323-W; SOD323-W
D2: NO_FIT; SOD323-W
DBG: PINHD-1X04_2.54-S; 1X04-S
IC2: MIC5225-3.3; SOT23-5
J1: 2p-2.0; H2-2.0-6X4.5MM
JP1: COINCELL_VREG; SMT-JUMPER_3_1-NC_TRACE_NO-SILK
JP2: 5VSRC; SMT-JUMPER_3_NO_NO-SILK
PWR: PINHD-1X02_2.54-S; 1X02-S
R1: 100; R0603
U$1: JHD12864; JHD12864-G176BSW
U$2: MDBT42Q; MDBT40
U$3: CR2032-SMD
U$4: ARDUINO
U$5: USB-MICROB
U$6: PTCFUSE; R1210

Connections:
BTN1: BTN1.2, U$2.P41 (P41-P0.23)
BTN2: BTN2.2, U$2.P35 (P35-P0.21/NRST)
BTN3: BTN3.1, U$2.P38 (P38-P0.22)
BTN4: BTN4.1, U$2.P40 (P40-P0.24)
GND: BTN1.1, BTN1.MT1 (MT), BTN1.MT2 (MT), BTN2.1, BTN2.MT1 (MT), BTN2.MT2 (MT), BTN3.2, BTN3.MT1 (MT), BTN3.MT2 (MT), BTN4.2, BTN4.MT1 (MT), BTN4.MT2 (MT), C1.2, C3.1, C4.1, CTUNE1.1, CTUNE2.1, DBG.4, IC2.2 (GND), J1.-, PWR.1, U$1.GND1 (GND), U$1.GND2 (GND), U$1.P4 (GND), U$2.P1 (P1-GND), U$2.P12 (P12-GND), U$2.P24 (P24-GND), U$2.P39 (P39-GND), U$3.NEG (-), U$4.GND, U$4.GND., U$4.GND.., U$5.GND, U$5.MT1 (GND), U$5.MT2 (GND), U$5.P$1 (GND), U$5.P$2 (GND), U$5.P$3 (GND), U$5.P$4 (GND)
LCD_BL: R1.2, U$2.P30 (P30-P0.16)
LCD_CS: U$1.P10 (CS), U$2.P26 (P26-P0.12)
LCD_DC: U$1.P8 (DC), U$2.P27 (P27-P0.13)
LCD_MOSI: U$1.P6 (MOSI), U$2.P29 (P29-P0.15)
LCD_RST: U$1.P9 (RST), U$2.P25 (P25-P0.11)
LCD_SCK: U$1.P7 (SCK), U$2.P28 (P28-P0.14)
unnamed: D2.A, JP1.2, U$3.POS1 (+), U$3.POS2 (+)
unnamed: C2.1, U$1.P3 (VO)
unnamed: C2.2, U$1.P2 (XVO)
unnamed: C1.1, U$1.P1 (VG)
unnamed: R1.1, U$1.LEDK
unnamed: U$5.VBUS, U$6.1
unnamed: JP2.2, U$4.5V
NFC: CTUNE1.2, CTUNE2.2, U$2.P22 (P22-P0.09/NFC1), U$2.P23 (P23-P0.10/NFC2)
PA0: U$2.P15 (P15-P0.02/AIN0), U$4.A0
PA1: U$2.P16 (P16-P0.03/AIN1), U$4.A1
PA2: U$2.P17 (P17-P0.04/AIN2), U$4.A2
PA3: U$2.P18 (P18-P0.05/AIN3), U$4.A3
PA4: U$2.P5 (P5-P0.28/AIN4), U$4.A4, U$4.SDA (27(SDA))
PA5: U$2.P6 (P6-P0.29/AIN5), U$4.A5, U$4.SCL (28(SCL))
PD0: U$2.P2 (P2-P0.25), U$4.0 (0(RX))
PD1: U$2.P3 (P3-P0.26), U$4.1 (1(TX))
PD2: U$2.P4 (P4-P0.27), U$4.2
PD3: U$2.P7 (P7-P0.30/AIN6), U$4.3 (~3)
PD4: U$2.P8 (P8-P0.31/AIN7), U$4.4
PD5: U$2.P13 (P13-P0.00/XL1), U$4.5 (~5)
PD6: U$2.P14 (P14-P0.01/XL2), U$4.6 (~6)
PD7: U$2.P19 (P19-P0.06), U$4.7
PD8: U$2.P20 (P20-P0.07), U$4.8
PD9: U$2.P21 (P21-P0.08), U$4.9 (~9)
PD10: U$2.P31 (P31-P0.17), U$4.10 (~10)
PD11: U$2.P32 (P32-P0.18), U$4.11 (~11)
PD12: U$2.P33 (P33-P0.19), U$4.12
PD13: U$2.P34 (P34-P0.20), U$4.13
SWCK: DBG.3, U$2.P36 (P36-SWDCLK)
SWIO: DBG.2, U$2.P37 (P37-SWDIO)
USB_FUSED: D1.A, U$6.2
VDD: C3.2, D2.C, DBG.1, IC2.5 (OUT), JP1.3, JP2.3, U$1.LEDA, U$1.P5 (VDD), U$2.P11 (P11-VDD), U$4.3.3V, U$4.I/OREF (IOREF)
VIN: C4.2, D1.C, IC2.1 (IN), IC2.3 (EN), J1.+, JP1.1, JP2.1, PWR.2, U$4.VIN

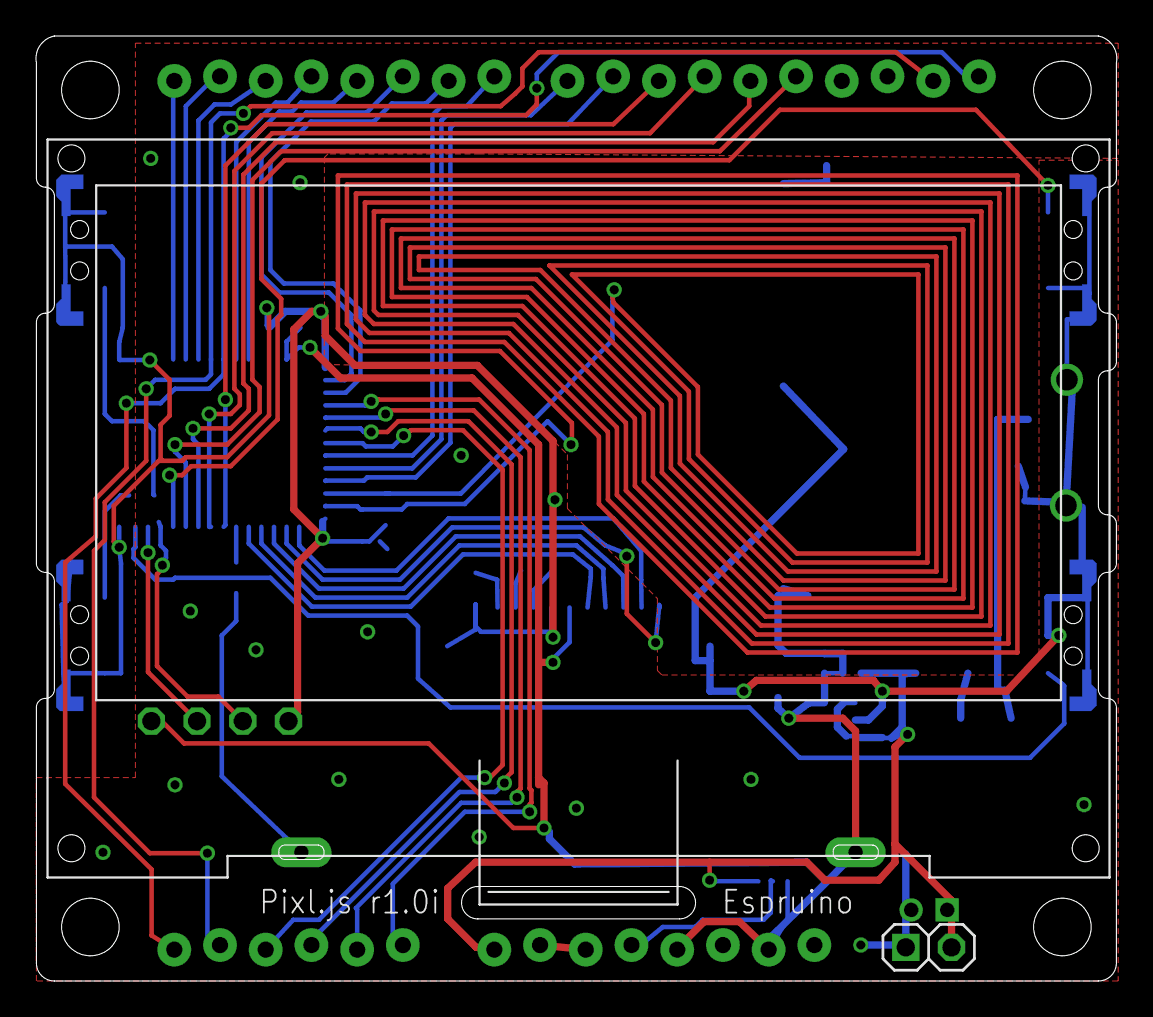
[picture p307: board pixljs.brd from above]

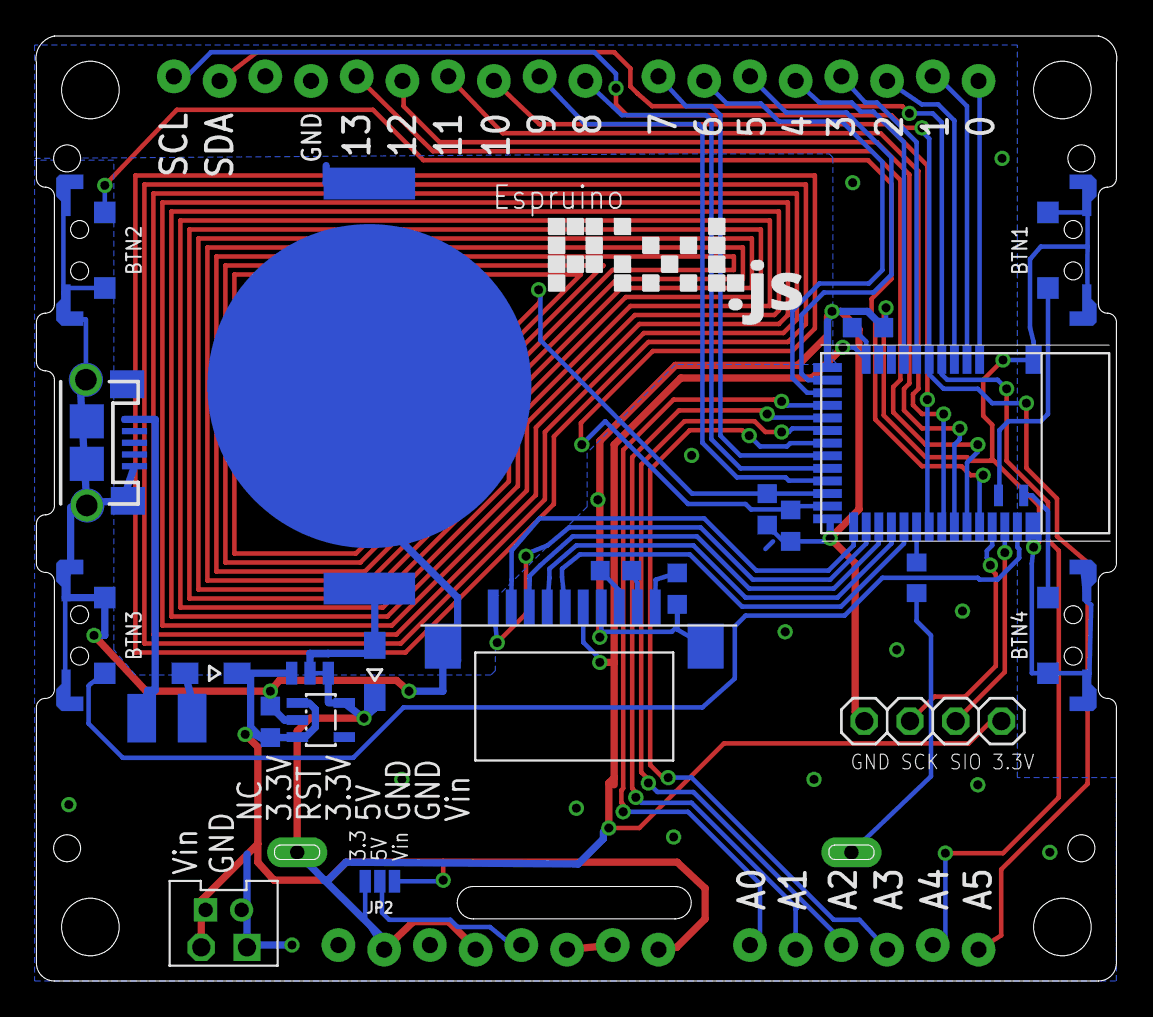
[picture p308: board pixljs.brd from below]

Board: 2 copper layers, 60.0 x 52.5 mm, 29 parts (23 on the bottom side), 44 nets.

Other parts of the board:
U$7, U$8, U$9, U$10: M3
