Leif-Rydenfalk/halo/reference/EspruinoBoard/Pico/Adaptors/eagle/nrf24_shim.brd

## EAGLE design reference/EspruinoBoard/Pico/Adaptors/eagle/nrf24_shim.brd (2026-09-03)

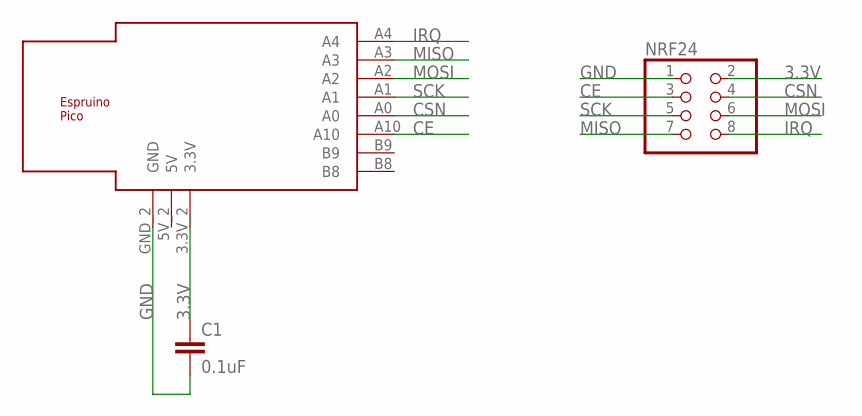
[picture p309: schematic nrf24_shim.sch]

Parts:
C1: 0.1uF; C1206
NRF24: PINHD-2X4; 2X04
U$1: ESPRUINO_PICO_0.05_SMALL

Connections:
3.3V: C1.1, NRF24.2, U$1.3.3V_2 (3.3V)
CE: NRF24.3, U$1.A10
CSN: NRF24.4, U$1.A0
GND: C1.2, NRF24.1, U$1.GND_2 (GND)
IRQ: NRF24.8, U$1.A4
MISO: NRF24.7, U$1.A3
MOSI: NRF24.6, U$1.A2
SCK: NRF24.5, U$1.A1

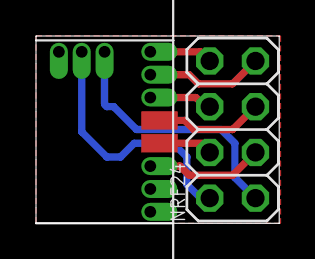
[picture p310: board nrf24_shim.brd from above]

Board: 2 copper layers, 13.5 x 10.4 mm, 3 parts (1 on the bottom side), 8 nets.
