Leif-Rydenfalk/halo/reference/EspruinoBoard/Pico/Adaptors/eagle/robot_simple.brd

## EAGLE design reference/EspruinoBoard/Pico/Adaptors/eagle/robot_simple.brd (2026-09-03)

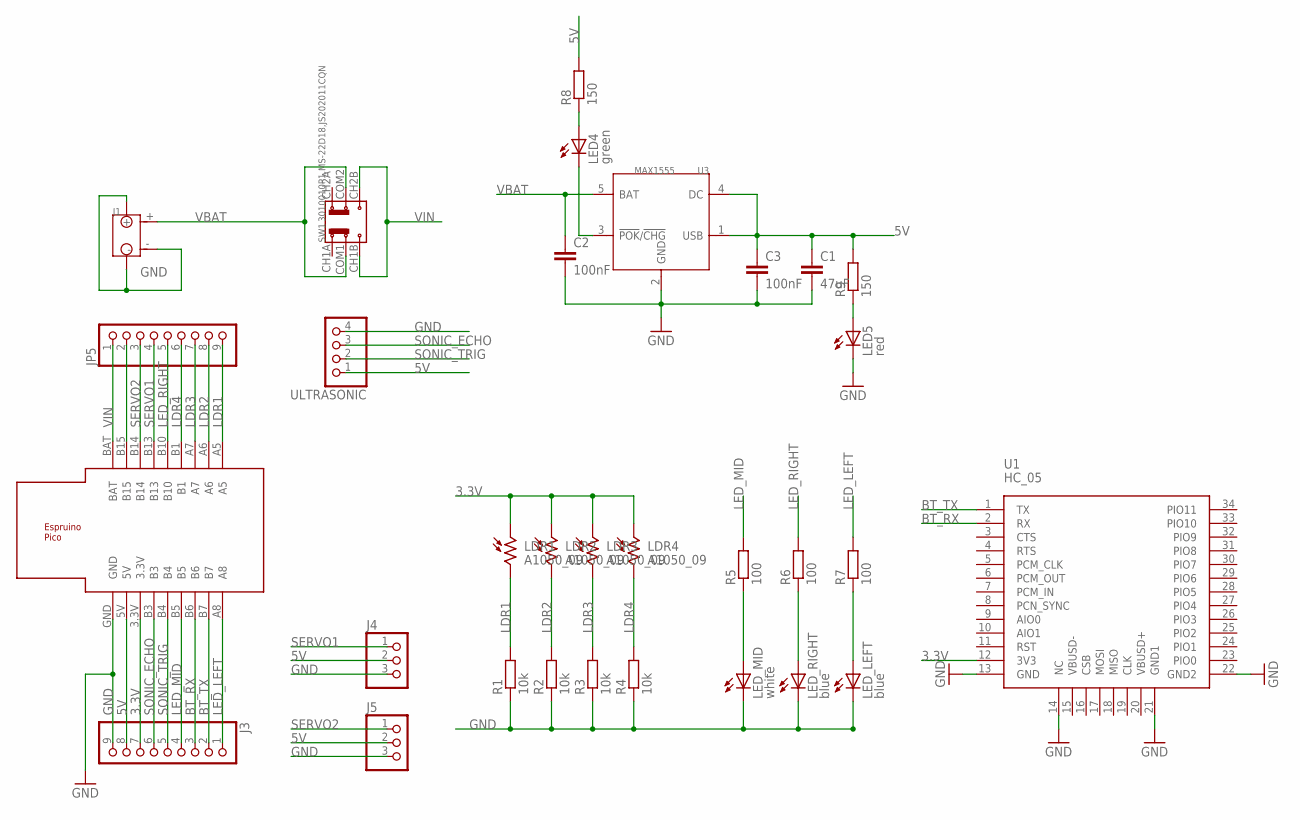
[picture p311: schematic robot_simple.sch]

Parts:
C1: 47uF; C1210
C2, C3: 100nF; C0805
J1: JST-2P-SMD-PW-3410050P1; 2P-SMD-2.0-90D
J3: PINHD-1X9; 1X09
J4, J5: PINHD-1X3; 1X03
JP5: PINHD-1X9; 1X09
LDR1, LDR2, LDR3, LDR4: A1050_09; T0-46-A10XX
LED4: green; CHIP-LED0805
LED5: red; CHIP-LED0805
LED_LEFT: blue; CHIP-LED0805
LED_MID: white; LED10MM
LED_RIGHT: blue; CHIP-LED0805
R1, R2, R3, R4: 10k; R0805
R5, R6, R7: 100; R0805
R8, R9: 150; R0805
SW1: 3010010P1,MS-22D18,JS202011CQN; 6P-2CH-2.54-9.1X3.5X3.2+2H
U1: HC_05; BLUETOOTH_SMD
U3: MAX1555; SOT23-5
U$1: ESPRUINO_PICO_0.1
ULTRASONIC: PINHD-1X4; 1X04

Connections:
3.3V: J3.7, LDR1.1, LDR2.1, LDR3.1, LDR4.1, U1.12 (3V3), U$1.3.3V
5V: C1.1, C3.1, J3.8, J4.2, J5.2, R8.2, R9.2, U3.1 (USB), U3.4 (DC), U$1.5V, ULTRASONIC.1
BT_RX: J3.3, U1.2 (RX), U$1.B6
BT_TX: J3.2, U1.1 (TX), U$1.B7
GND: C1.2, C2.2, C3.2, J1.3, J1.4, J1.-, J3.9, J4.3, J5.3, LED5.C, LED_LEFT.C, LED_MID.K (C), LED_RIGHT.C, R1.1, R2.1, R3.1, R4.1, U1.13 (GND), U1.14 (NC), U1.21 (GND1), U1.22 (GND2), U3.2 (GND), U$1.GND, ULTRASONIC.4
LDR1: JP5.9, LDR1.2, R1.2, U$1.A5
LDR2: JP5.8, LDR2.2, R2.2, U$1.A6
LDR3: JP5.7, LDR3.2, R3.2, U$1.A7
LDR4: JP5.6, LDR4.2, R4.2, U$1.B1
LED_LEFT: J3.1, R7.2, U$1.A8
LED_MID: J3.4, R5.2, U$1.B5
LED_RIGHT: JP5.5, R6.2, U$1.B10
unnamed: JP5.2, U$1.B15
unnamed: LED_LEFT.A, R7.1
unnamed: LED_RIGHT.A, R6.1
unnamed: LED_MID.A, R5.1
unnamed: LED4.C, U3.3 (!POK!/!CHG!)
unnamed: LED4.A, R8.1
unnamed: LED5.A, R9.1
SERVO1: J4.1, JP5.4, U$1.B13
SERVO2: J5.1, JP5.3, U$1.B14
SONIC_ECHO: J3.6, U$1.B3, ULTRASONIC.3
SONIC_TRIG: J3.5, U$1.B4, ULTRASONIC.2
VBAT: C2.1, J1.+, SW1.COM1, SW1.COM2, U3.5 (BAT)
VIN: JP5.1, SW1.CH1B, SW1.CH2B, U$1.BAT

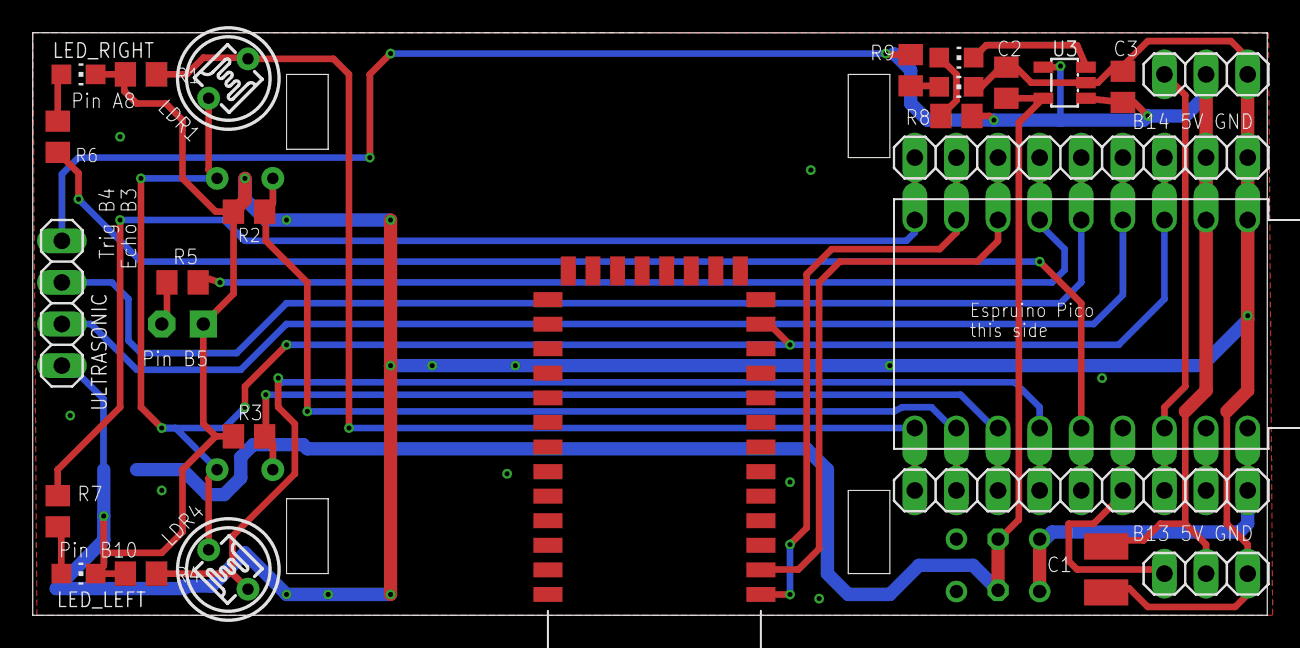
[picture p312: board robot_simple.brd from above]

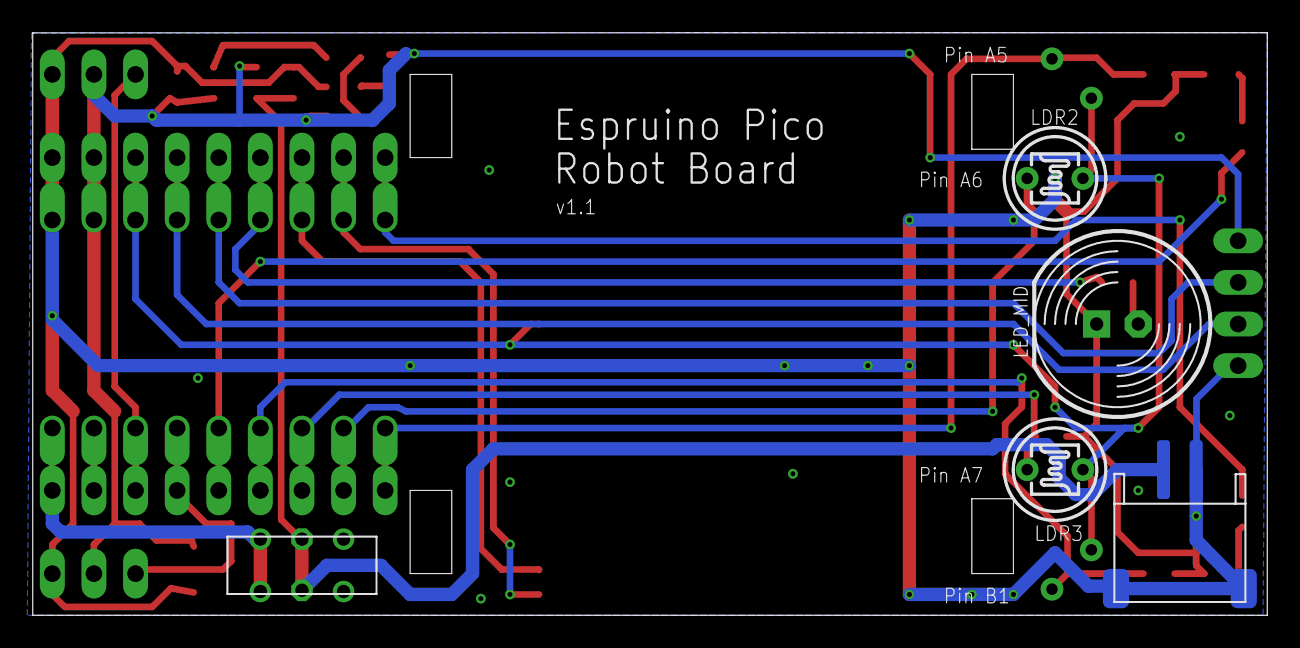
[picture p313: board robot_simple.brd from below]

Board: 2 copper layers, 75.4 x 35.6 mm, 31 parts (5 on the bottom side), 25 nets.
