Leif-Rydenfalk/halo/reference/nrf5-eagle-reference-design/nRF52810_reference/nRF52810_qfaa_dcdc/nRF52810_qfaa_dcdc.brd

## EAGLE design reference/nrf5-eagle-reference-design/nRF52810_reference/nRF52810_qfaa_dcdc/nRF52810_qfaa_dcdc.brd (2026-09-03)

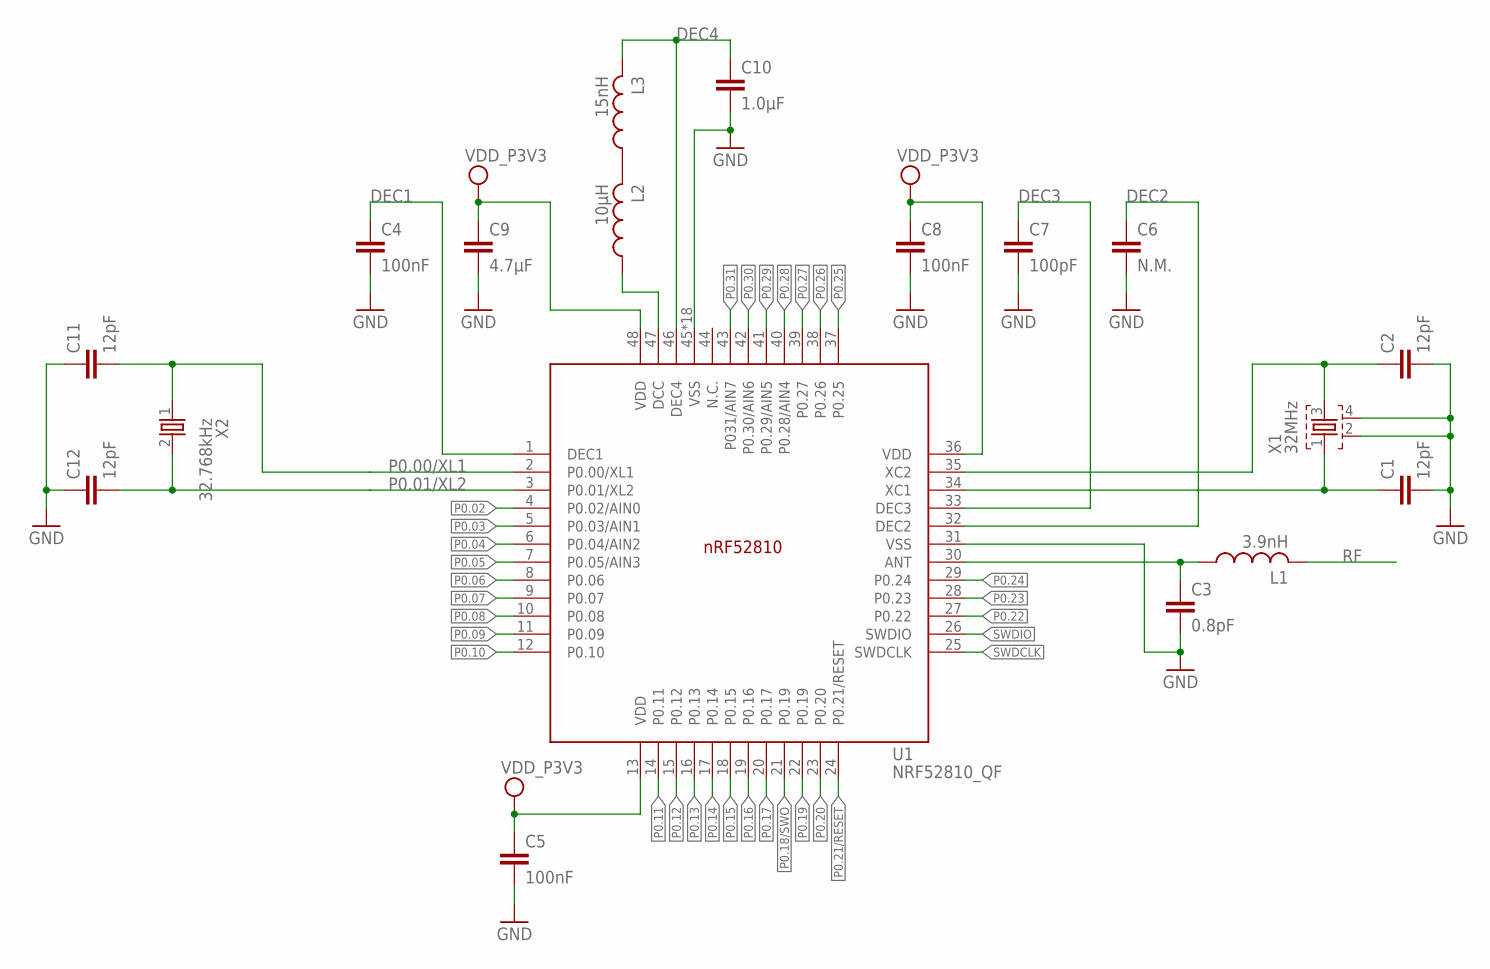
[picture p314: schematic nRF52810_qfaa_dcdc.sch]

Parts:
C1, C2, C11, C12: 12pF; RESC0402_N
C3: 0.8pF; RESC0402_N
C4, C5, C8: 100nF; RESC0402_N
C6: N.M.; RESC0402_N
C7: 100pF; RESC0402_N
C9: 4.7µF; RESC0603_N
C10: 1.0µF; RESC0603_N
L1: 3.9nH; RESC0402_N
L2: 10µH; RESC0603_N
L3: 15nH; RESC0402_N
U1: NRF52810_QF; QFN40P600X600X90-48_N
X1: 32MHz; BT-XTAL_2016_N
X2: 32.768kHz; XTAL_3215_N

Connections:
ANT: C3.1, L1.1, U1.30 (ANT)
DEC1: C4.1, U1.1 (DEC1)
DEC2: C6.1, U1.32 (DEC2)
DEC3: C7.1, U1.33 (DEC3)
DEC4: C10.1, L3.2, U1.46 (DEC4)
GND: C1.2, C2.2, C3.2, C4.2, C5.2, C6.2, C7.2, C8.2, C9.2, C10.2, C11.1, C12.1, U1.31 (VSS), U1.45 (VSS), U1.PAD (VSS), U1.PAD@VIA01 (VSS), U1.PAD@VIA02 (VSS), U1.PAD@VIA03 (VSS), U1.PAD@VIA04 (VSS), U1.PAD@VIA05 (VSS), U1.PAD@VIA06 (VSS), U1.PAD@VIA07 (VSS), U1.PAD@VIA08 (VSS), U1.PAD@VIA09 (VSS), U1.PAD@VIA10 (VSS), U1.PAD@VIA11 (VSS), U1.PAD@VIA12 (VSS), U1.PAD@VIA13 (VSS), U1.PAD@VIA14 (VSS), U1.PAD@VIA15 (VSS), U1.PAD@VIA16 (VSS), X1.2, X1.4
unnamed: L2.2, L3.1
unnamed: C2.1, U1.35 (XC2), X1.3
unnamed: L2.1, U1.47 (DCC)
P0.00/XL1: C11.2, U1.2 (P0.00/XL1), X2.1
P0.01/XL2: C12.2, U1.3 (P0.01/XL2), X2.2
P0.02: U1.4 (P0.02/AIN0)
P0.03: U1.5 (P0.03/AIN1)
P0.04: U1.6 (P0.04/AIN2)
P0.05: U1.7 (P0.05/AIN3)
P0.06: U1.8 (P0.06)
P0.07: U1.9 (P0.07)
P0.08: U1.10 (P0.08)
P0.09: U1.11 (P0.09)
P0.10: U1.12 (P0.10)
P0.11: U1.14 (P0.11)
P0.12: U1.15 (P0.12)
P0.13: U1.16 (P0.13)
P0.14: U1.17 (P0.14)
P0.15: U1.18 (P0.15)
P0.16: U1.19 (P0.16)
P0.17: U1.20 (P0.17)
P0.18/SWO: U1.21 (P0.19)
P0.19: U1.22 (P0.19)
P0.20: U1.23 (P0.20)
P0.21/RESET: U1.24 (P0.21/RESET)
P0.22: U1.27 (P0.22)
P0.23: U1.28 (P0.23)
P0.24: U1.29 (P0.24)
P0.25: U1.37 (P0.25)
P0.26: U1.38 (P0.26)
P0.27: U1.39 (P0.27)
P0.28: U1.40 (P0.28/AIN4)
P0.29: U1.41 (P0.29/AIN5)
P0.30: U1.42 (P0.30/AIN6)
P0.31: U1.43 (P031/AIN7)
RF: L1.2
SWDCLK: U1.25 (SWDCLK)
SWDIO: U1.26 (SWDIO)
VDD_P3V3: C5.1, C8.1, C9.1, U1.13 (VDD), U1.36 (VDD), U1.48 (VDD)
X1: C1.1, U1.34 (XC1), X1.1

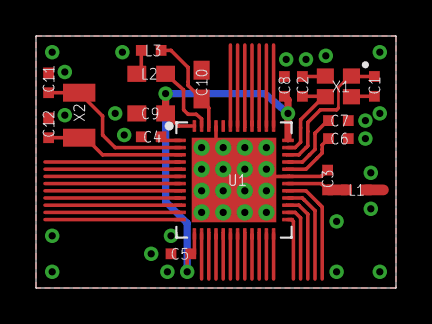
[picture p315: board nRF52810_qfaa_dcdc.brd from above]

Board: 2 copper layers, 20.0 x 14.0 mm, 18 parts (0 on the bottom side), 13 nets.
