Leif-Rydenfalk/halo/reference/nrf5-eagle-reference-design/nRF52810_reference/nRF52810_qcaa/nRF52810_qcaa.brd

## EAGLE design reference/nrf5-eagle-reference-design/nRF52810_reference/nRF52810_qcaa/nRF52810_qcaa.brd (2026-09-03)

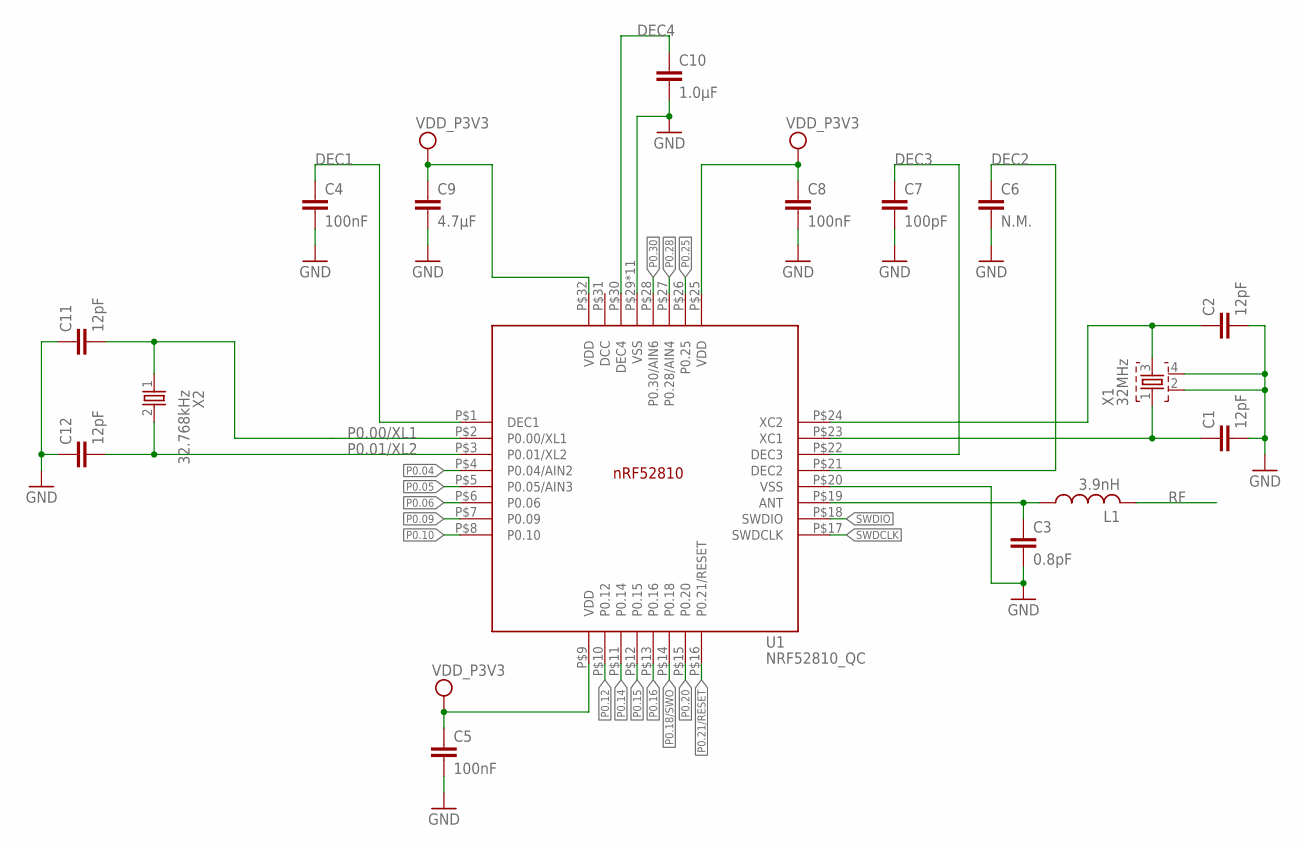
[picture p316: schematic nRF52810_qcaa.sch]

Parts:
C1, C2, C11, C12: 12pF; RESC0402_N
C3: 0.8pF; RESC0402_N
C4, C5, C8: 100nF; RESC0402_N
C6: N.M.; RESC0402_N
C7: 100pF; RESC0402_N
C9: 4.7µF; RESC0603_N
C10: 1.0µF; RESC0603_N
L1: 3.9nH; RESC0402_N
U1: NRF52810_QC; QFN50P500X500X90-32_N
X1: 32MHz; BT-XTAL_2016_N
X2: 32.768kHz; XTAL_3215_N

Connections:
ANT: C3.1, L1.1, U1.P$19 (ANT)
DEC1: C4.1, U1.P$1 (DEC1)
DEC2: C6.1, U1.P$21 (DEC2)
DEC3: C7.1, U1.P$22 (DEC3)
DEC4: C10.1, U1.P$30 (DEC4)
GND: C1.2, C2.2, C3.2, C4.2, C5.2, C6.2, C7.2, C8.2, C9.2, C10.2, C11.1, C12.1, U1.P$20 (VSS), U1.P$29 (VSS), U1.P$33 (VSS), U1.P$34 (VSS), U1.P$35 (VSS), U1.P$36 (VSS), U1.P$37 (VSS), U1.P$38 (VSS), U1.P$39 (VSS), U1.P$40 (VSS), U1.P$41 (VSS), U1.P$42 (VSS), X1.2, X1.4
unnamed: C2.1, U1.P$24 (XC2), X1.3
P0.00/XL1: C11.2, U1.P$2 (P0.00/XL1), X2.1
P0.01/XL2: C12.2, U1.P$3 (P0.01/XL2), X2.2
P0.04: U1.P$4 (P0.04/AIN2)
P0.05: U1.P$5 (P0.05/AIN3)
P0.06: U1.P$6 (P0.06)
P0.09: U1.P$7 (P0.09)
P0.10: U1.P$8 (P0.10)
P0.12: U1.P$10 (P0.12)
P0.14: U1.P$11 (P0.14)
P0.15: U1.P$12 (P0.15)
P0.16: U1.P$13 (P0.16)
P0.18/SWO: U1.P$14 (P0.18)
P0.20: U1.P$15 (P0.20)
P0.21/RESET: U1.P$16 (P0.21/RESET)
P0.25: U1.P$26 (P0.25)
P0.28: U1.P$27 (P0.28/AIN4)
P0.30: U1.P$28 (P0.30/AIN6)
RF: L1.2
SWDCLK: U1.P$17 (SWDCLK)
SWDIO: U1.P$18 (SWDIO)
VDD_P3V3: C5.1, C8.1, C9.1, U1.P$9 (VDD), U1.P$25 (VDD), U1.P$32 (VDD)
X1: C1.1, U1.P$23 (XC1), X1.1

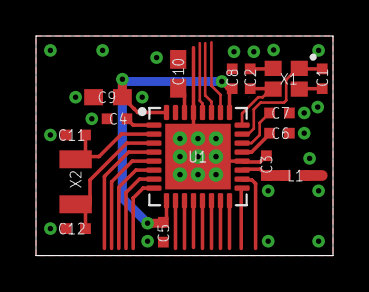
[picture p317: board nRF52810_qcaa.brd from above]

Board: 2 copper layers, 16.5 x 12.2 mm, 16 parts (0 on the bottom side), 11 nets.
