Leif-Rydenfalk/halo/electronics/halo_replica/out/schematic-fab/halo_replica_fab.kicad_sch

## KiCad design electronics/halo_replica/out/schematic-fab/halo_replica_fab.kicad_sch (2026-09-05)

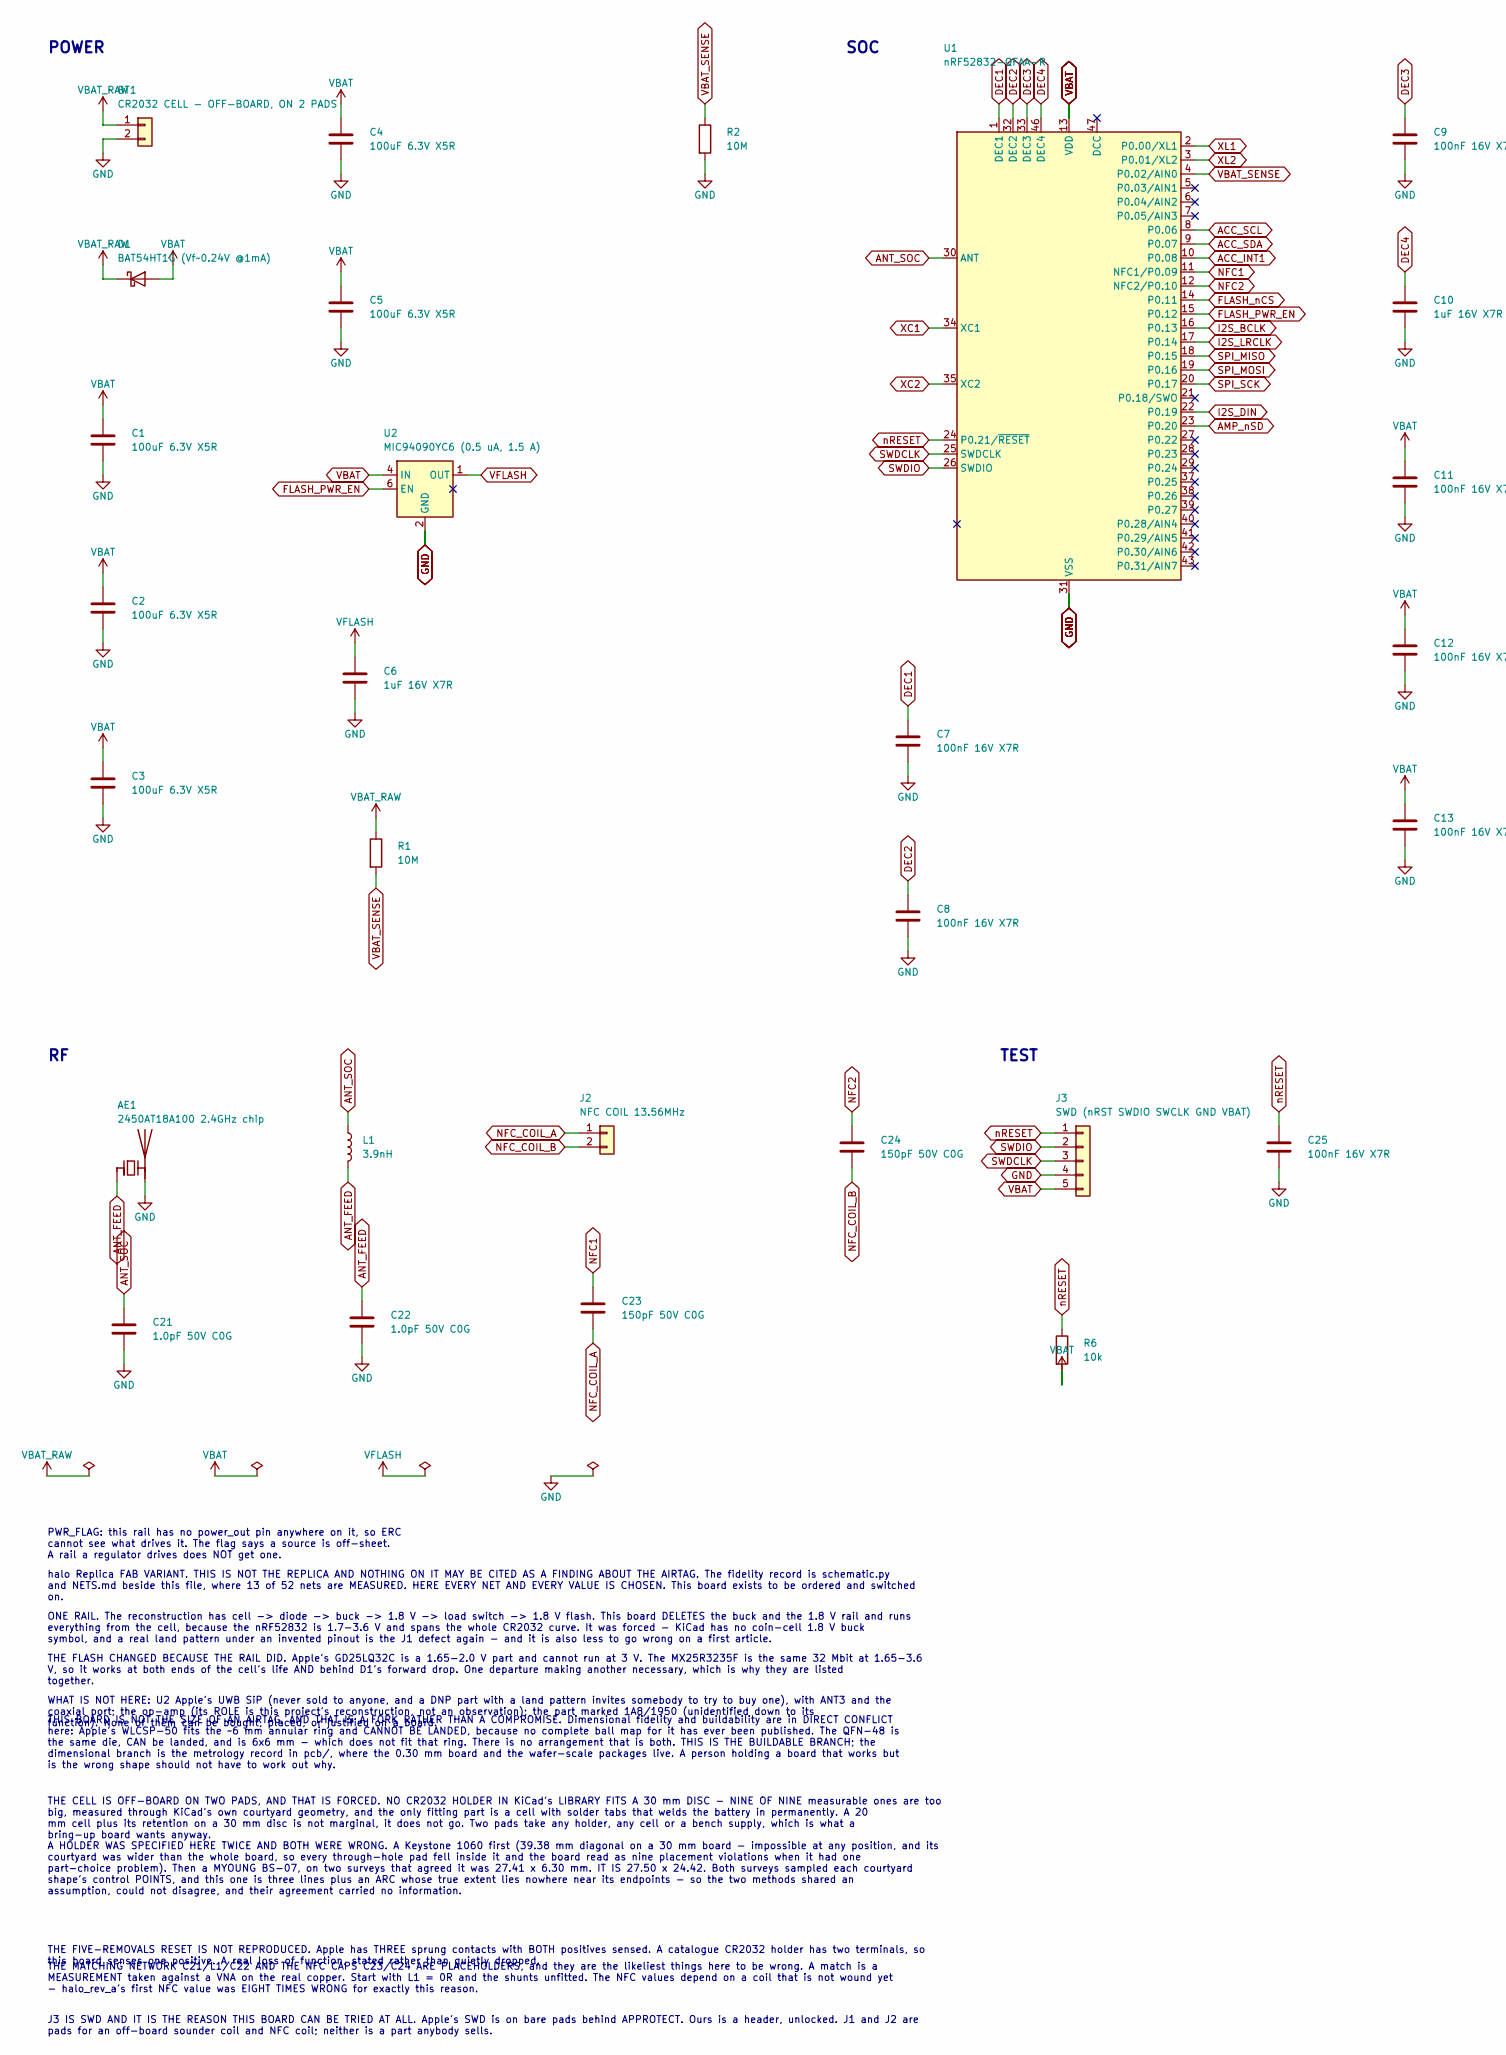
[picture p320: schematic halo_replica_fab.kicad_sch, part in row 1, column 1]

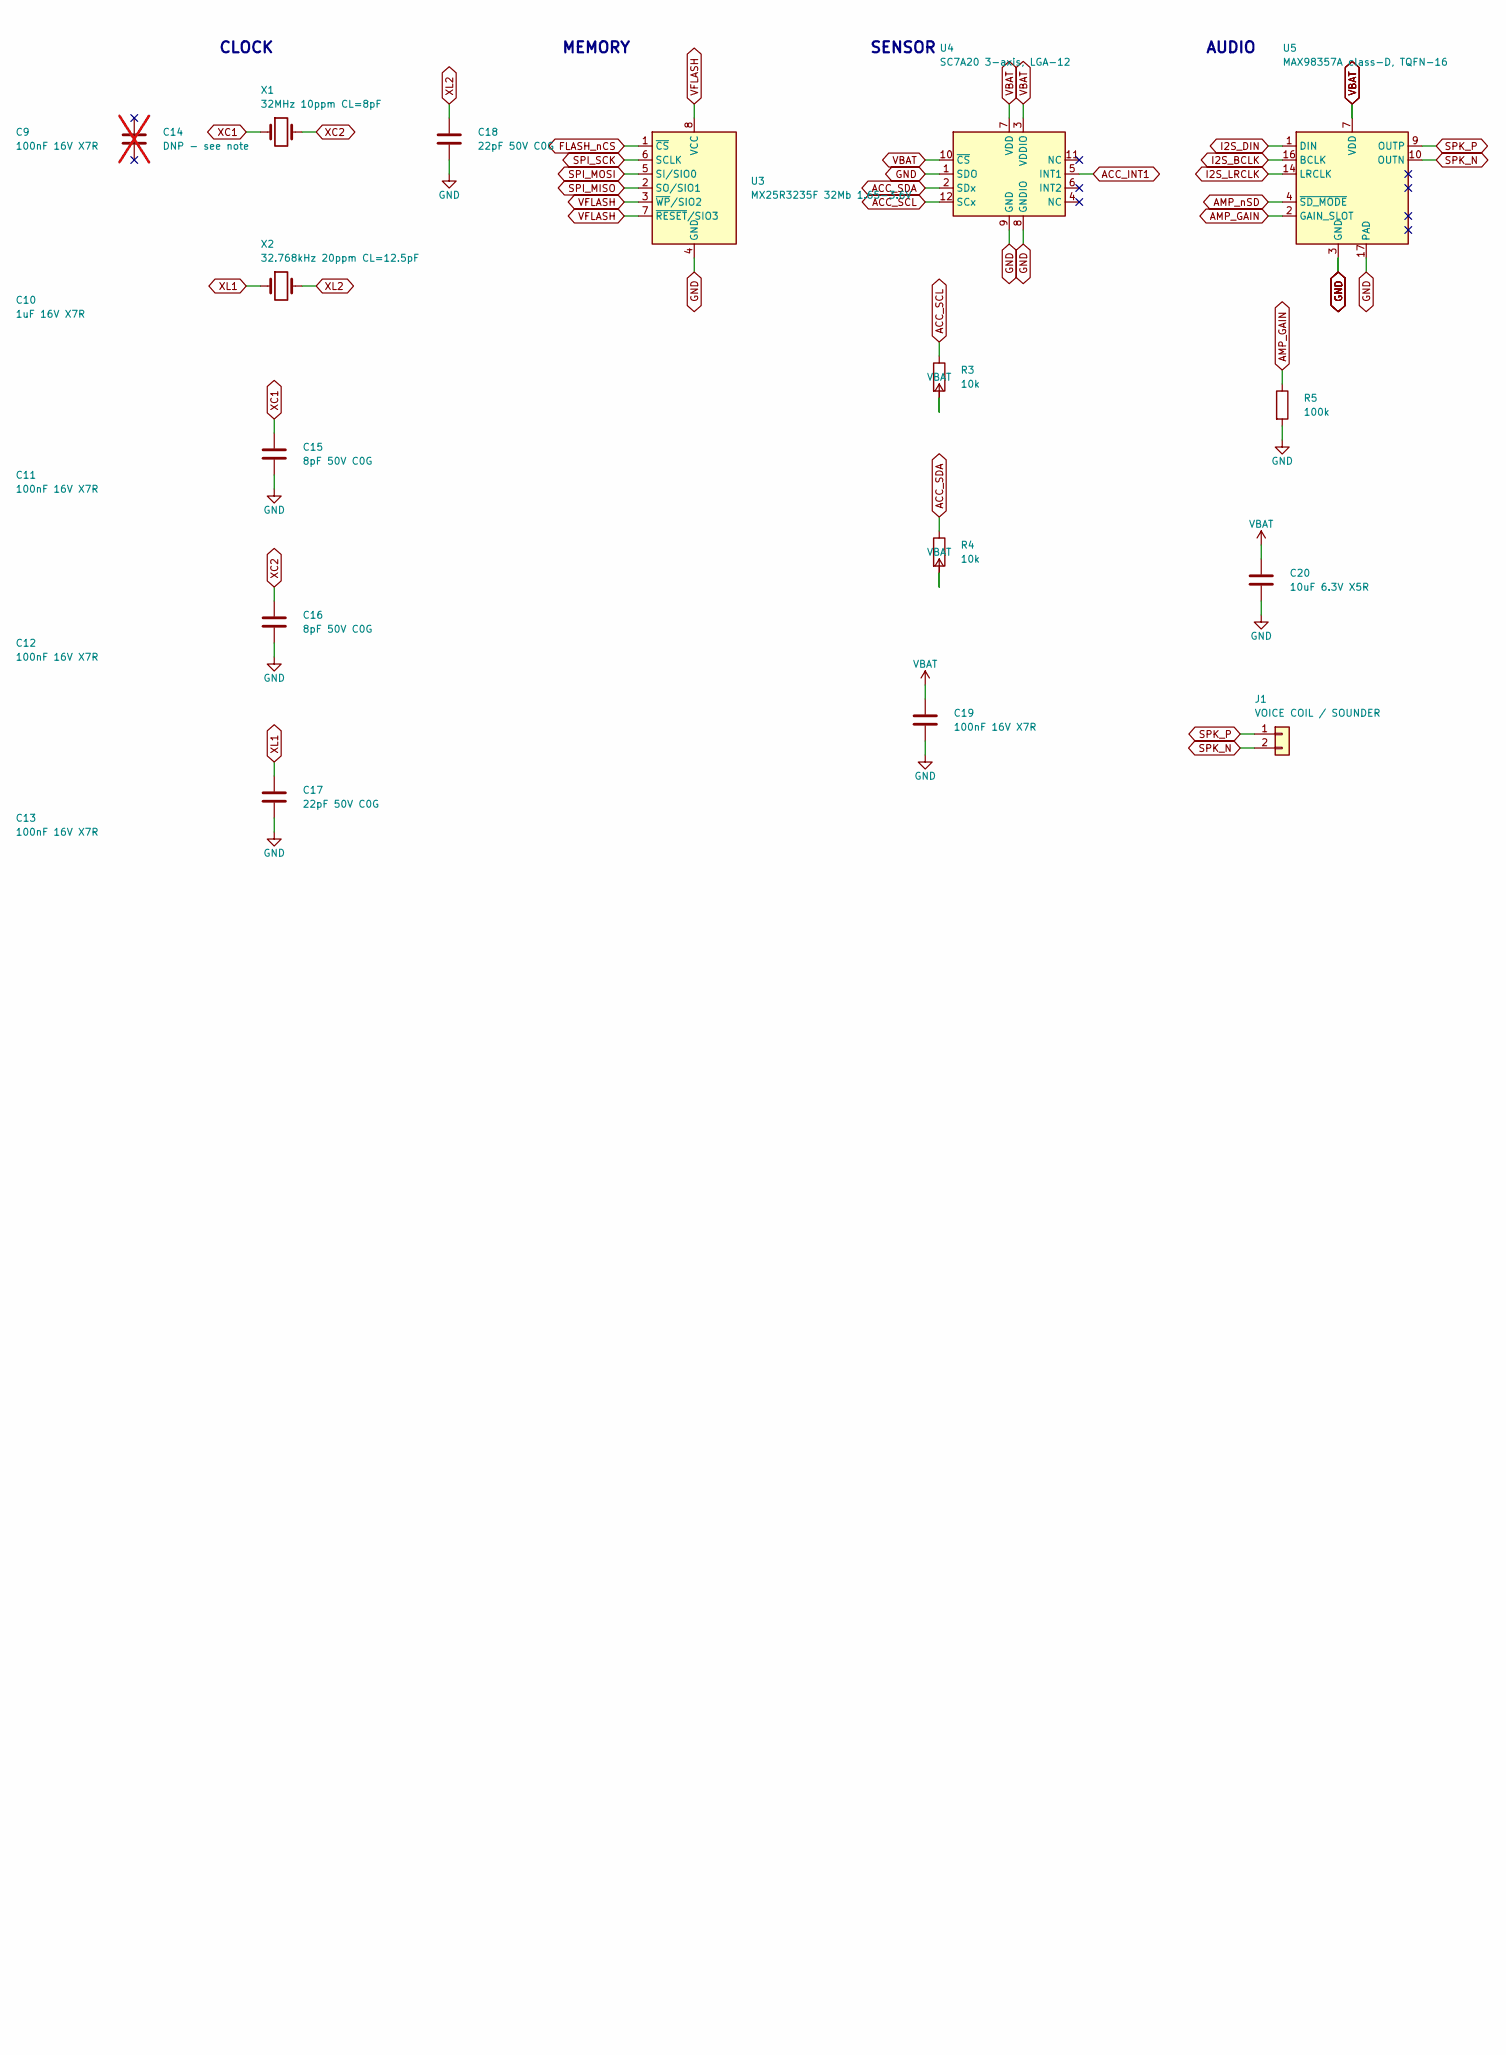
[picture p321: schematic halo_replica_fab.kicad_sch, part in row 1, column 2]

Parts:
AE1: 2450AT18A100 2.4GHz chip; Johanson_2450AT18x100; MPN 2450AT18A100E; LCSC Part # CANNOT DETERMINE - no price pull was do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
BT1: CR2032 CELL - OFF-BOARD, ON 2 PADS; PinHeader_1x02_P2.54mm_Vertical; LCSC Part # CANNOT DETERMINE - no price pull was do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
C1, C2, C3, C4, C5: 100uF 6.3V X5R; C_0805_2012Metric; MPN CL21A107MQNNNNE; LCSC Part # CANNOT DETERMINE - no price pull was do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
C6, C10: 1uF 16V X7R; C_0402_1005Metric; MPN CL05A105KA5NNNC; LCSC Part # CANNOT DETERMINE - no price pull was do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
C7, C8, C9, C11, C12, C13, C19, C25: 100nF 16V X7R; C_0402_1005Metric; MPN CL05B104KO5NNNC; LCSC Part # CANNOT DETERMINE - no price pull was do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
C14: DNP - see note; C_0402_1005Metric; LCSC Part # CANNOT DETERMINE - no price pull was do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; not fitted
C15, C16: 8pF 50V C0G; C_0402_1005Metric; MPN CL05C080CB5NNNC; LCSC Part # CANNOT DETERMINE - no price pull was do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
C17, C18: 22pF 50V C0G; C_0402_1005Metric; MPN CL05C220JB5NNNC; LCSC Part # CANNOT DETERMINE - no price pull was do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
C20: 10uF 6.3V X5R; C_0603_1608Metric; MPN CL10A106MQ8NNNC; LCSC Part # CANNOT DETERMINE - no price pull was do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
C21, C22: 1.0pF 50V C0G; C_0402_1005Metric; LCSC Part # CANNOT DETERMINE - no price pull was do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
C23, C24: 150pF 50V C0G; C_0402_1005Metric; LCSC Part # CANNOT DETERMINE - no price pull was do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
D1: BAT54HT1G (Vf~0.24V @1mA); D_SOD-323; MPN BAT54HT1G; LCSC Part # CANNOT DETERMINE - no price pull was do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
J1: VOICE COIL / SOUNDER; PinHeader_1x02_P2.54mm_Vertical; LCSC Part # CANNOT DETERMINE - no price pull was do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
J2: NFC COIL 13.56MHz; PinHeader_1x02_P2.54mm_Vertical; LCSC Part # CANNOT DETERMINE - no price pull was do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
J3: SWD (nRST SWDIO SWCLK GND VBAT); PinHeader_1x05_P2.54mm_Vertical; LCSC Part # CANNOT DETERMINE - no price pull was do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
L1: 3.9nH; L_0402_1005Metric; LCSC Part # CANNOT DETERMINE - no price pull was do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
R1, R2: 10M; R_0402_1005Metric; MPN RC0402FR-0710ML; LCSC Part # CANNOT DETERMINE - no price pull was do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
R3, R4, R6: 10k; R_0402_1005Metric; MPN RC0402FR-0710KL; LCSC Part # CANNOT DETERMINE - no price pull was do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
R5: 100k; R_0402_1005Metric; MPN RC0402FR-07100KL; LCSC Part # CANNOT DETERMINE - no price pull was do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
U1: nRF52832-QFAA-R; QFN-48-1EP_6x6mm_P0.4mm_EP4.4x4.4mm; MPN NRF52832-QFAA-R; LCSC Part # CANNOT DETERMINE - no price pull was do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
U2: MIC94090YC6 (0.5 uA, 1.5 A); SOT-363_SC-70-6; MPN MIC94090YC6; LCSC Part # CANNOT DETERMINE - no price pull was do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
U3: MX25R3235F 32Mb 1.65-3.6V; JEITA_SOIC-8_3.9x4.9mm_P1.27mm; MPN MX25R3235FM1IL0; LCSC Part # CANNOT DETERMINE - no price pull was do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
U4: SC7A20 3-axis, LGA-12; LGA-12_2x2mm_P0.5mm; MPN SC7A20; LCSC Part # CANNOT DETERMINE - no price pull was do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
U5: MAX98357A class-D, TQFN-16; TQFN-16-1EP_3x3mm_P0.5mm_EP1.23x1.23mm; MPN MAX98357AETE+T; LCSC Part # CANNOT DETERMINE - no price pull was do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
X1: 32MHz 10ppm CL=8pF; Crystal_SMD_2012-2Pin_2.0x1.2mm; MPN NX2012SA-32M-STD-CSW-5; LCSC Part # CANNOT DETERMINE - no price pull was do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
X2: 32.768kHz 20ppm CL=12.5pF; Crystal_SMD_3215-2Pin_3.2x1.5mm; MPN ABS07-32.768KHZ-T; LCSC Part # CANNOT DETERMINE - no price pull was do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

Connections:
ACC_INT1: U1.10 (P0.08), U4.5 (INT1)
ACC_SCL: R3.1, U1.8 (P0.06), U4.12 (SCx)
ACC_SDA: R4.1, U1.9 (P0.07), U4.2 (SDx)
AMP_GAIN: R5.1, U5.2 (GAIN_SLOT)
AMP_nSD: U1.23 (P0.20), U5.4 (~SD_MODE)
ANT_FEED: AE1.1 (FEED), C22.1, L1.2
ANT_SOC: C21.1, L1.1, U1.30 (ANT)
DEC1: C7.1, U1.1 (DEC1)
DEC2: C8.1, U1.32 (DEC2)
DEC3: C9.1, U1.33 (DEC3)
DEC4: C10.1, U1.46 (DEC4)
FLASH_PWR_EN: U1.15 (P0.12), U2.6 (EN)
FLASH_nCS: U1.14 (P0.11), U3.1 (~CS)
GND: AE1.2 (PCB_Trace), BT1.1, BT1.2, C1.1, C1.2, C2.1, C2.2, C3.1, C3.2, C4.1, C4.2, C5.1, C5.2, C6.1, C6.2, C7.2, C8.2, C9.2, C10.2, C11.1, C11.2, C12.1, C12.2, C13.1, C13.2, C15.2, C16.2, C17.2, C18.2, C19.1, C19.2, C20.1, C20.2, C21.2, C22.2, C25.2, D1.1 (K), D1.2 (A), J3.4, R1.1, R2.2, R3.2, R4.2, R5.2, R6.2, U1.31 (VSS), U1.45 (VSS), U1.49 (VSS), U2.2 (GND), U2.5 (GND), U3.4 (GND), U4.1 (SDO), U4.8 (GNDIO), U4.9 (GND), U5.3 (GND), U5.11 (GND), U5.15 (GND), U5.17 (PAD)
I2S_BCLK: U1.16 (P0.13), U5.16 (BCLK)
I2S_DIN: U1.22 (P0.19), U5.1 (DIN)
I2S_LRCLK: U1.17 (P0.14), U5.14 (LRCLK)
NFC1: C23.1, U1.11 (NFC1/P0.09)
NFC2: C24.1, U1.12 (NFC2/P0.10)
NFC_COIL_A: C23.2, J2.1
NFC_COIL_B: C24.2, J2.2
SPI_MISO: U1.18 (P0.15), U3.2 (SO/SIO1)
SPI_MOSI: U1.19 (P0.16), U3.5 (SI/SIO0)
SPI_SCK: U1.20 (P0.17), U3.6 (SCLK)
SPK_N: J1.2, U5.10 (OUTN)
SPK_P: J1.1, U5.9 (OUTP)
SWDCLK: J3.3, U1.25 (SWDCLK)
SWDIO: J3.2, U1.26 (SWDIO)
VBAT: J3.5, U1.13 (VDD), U1.36 (VDD), U1.48 (VDD), U2.4 (IN), U4.3 (VDDIO), U4.7 (VDD), U4.10 (~CS), U5.7 (VDD), U5.8 (VDD)
VBAT_SENSE: R1.2, R2.1, U1.4 (P0.02/AIN0)
VFLASH: U2.1 (OUT), U3.3 (~WP/SIO2), U3.7 (~RESET/SIO3), U3.8 (VCC)
XC1: C15.1, U1.34 (XC1), X1.1
XC2: C16.1, U1.35 (XC2), X1.2
XL1: C17.1, U1.2 (P0.00/XL1), X2.1
XL2: C18.1, U1.3 (P0.01/XL2), X2.2
nRESET: C25.1, J3.1, R6.1, U1.24 (P0.21/~RESET)

Notes on the sheet:
POWER
SOC
CLOCK
MEMORY
SENSOR
AUDIO
TEST
PWR_FLAG: this rail has no power_out pin anywhere on it, so ERC cannot see what drives it. The flag says a source is off-sheet. A rail a regulator drives does NOT get one.
halo Replica FAB VARIANT. THIS IS NOT THE REPLICA AND NOTHING ON IT MAY BE CITED AS A FINDING ABOUT THE AIRTAG. The fidelity record is schematic.py and NETS.md beside this file, where 13 of 52 nets are MEASURED. HERE EVERY NET AND EVERY VALUE IS CHOSEN. This board exists to be ordered and switched 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
ONE RAIL. The reconstruction has cell -> diode -> buck -> 1.8 V -> load switch -> 1.8 V flash. This board DELETES the buck and the 1.8 V rail and runs everything from the cell, because the nRF52832 is 1.7-3.6 V and spans the whole CR2032 curve. It was forced - KiCad has no coin-cell 1.8 V buck symb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
THE FLASH CHANGED BECAUSE THE RAIL DID. Apple's GD25LQ32C is a 1.65-2.0 V part and cannot run at 3 V. The MX25R3235F is the same 32 Mbit at 1.65-3.6 V, so it works at both ends of the cell's life AND behind D1's forward drop. One departure making another necessary, which is why they are listed toge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
WHAT IS NOT HERE: U2 Apple's UWB SiP (never sold to anyone, and a DNP part with a land pattern invites somebody to try to buy one), with ANT3 and the coaxial port; the op-amp (its ROLE is this project's reconstruction, not an observation); the part marked 1A8/1950 (unidentified down to its function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
THIS BOARD IS NOT THE SIZE OF AN AIRTAG, AND THAT IS A FORK RATHER THAN A COMPROMISE. Dimensional fidelity and buildability are in DIRECT CONFLICT here: Apple's WLCSP-50 fits the ~6 mm annular ring and CANNOT BE LANDED, because no complete ball map for it has ever been published. The QFN-48 is the 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
THE CELL IS OFF-BOARD ON TWO PADS, AND THAT IS FORCED. NO CR2032 HOLDER IN KiCad's LIBRARY FITS A 30 mm DISC - NINE OF NINE measurable ones are too big, measured through KiCad's own courtyard geometry, and the only fitting part is a cell with solder tabs that welds the battery in permanently. A 20 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
A HOLDER WAS SPECIFIED HERE TWICE AND BOTH WERE WRONG. A Keystone 1060 first (39.38 mm diagonal on a 30 mm board - impossible at any position, and its courtyard was wider than the whole board, so every through-hole pad fell inside it and the board read as nine placement violations when it had one p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
THE FIVE-REMOVALS RESET IS NOT REPRODUCED. Apple has THREE sprung contacts with BOTH positives sensed. A catalogue CR2032 holder has two terminals, so this board senses one positive. A real loss of function, stated rather than quietly dropped.
THE MATCHING NETWORK C21/L1/C22 AND THE NFC CAPS C23/C24 ARE PLACEHOLDERS, and they are the likeliest things here to be wrong. A match is a MEASUREMENT taken against a VNA on the real copper. Start with L1 = 0R and the shunts unfitted. The NFC values depend on a coil that is not wound yet - halo_re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
J3 IS SWD AND IT IS THE REASON THIS BOARD CAN BE TRIED AT ALL. Apple's SWD is on bare pads behind APPROTECT. Ours is a header, unlocked. J1 and J2 are pads for an off-board sounder coil and NFC coil; neither is a part anybody sells.
