Leif-Rydenfalk/halo/electronics/halo_replica/out/schematic/halo_replica.kicad_sch

## KiCad design electronics/halo_replica/out/schematic/halo_replica.kicad_sch (2026-09-05)

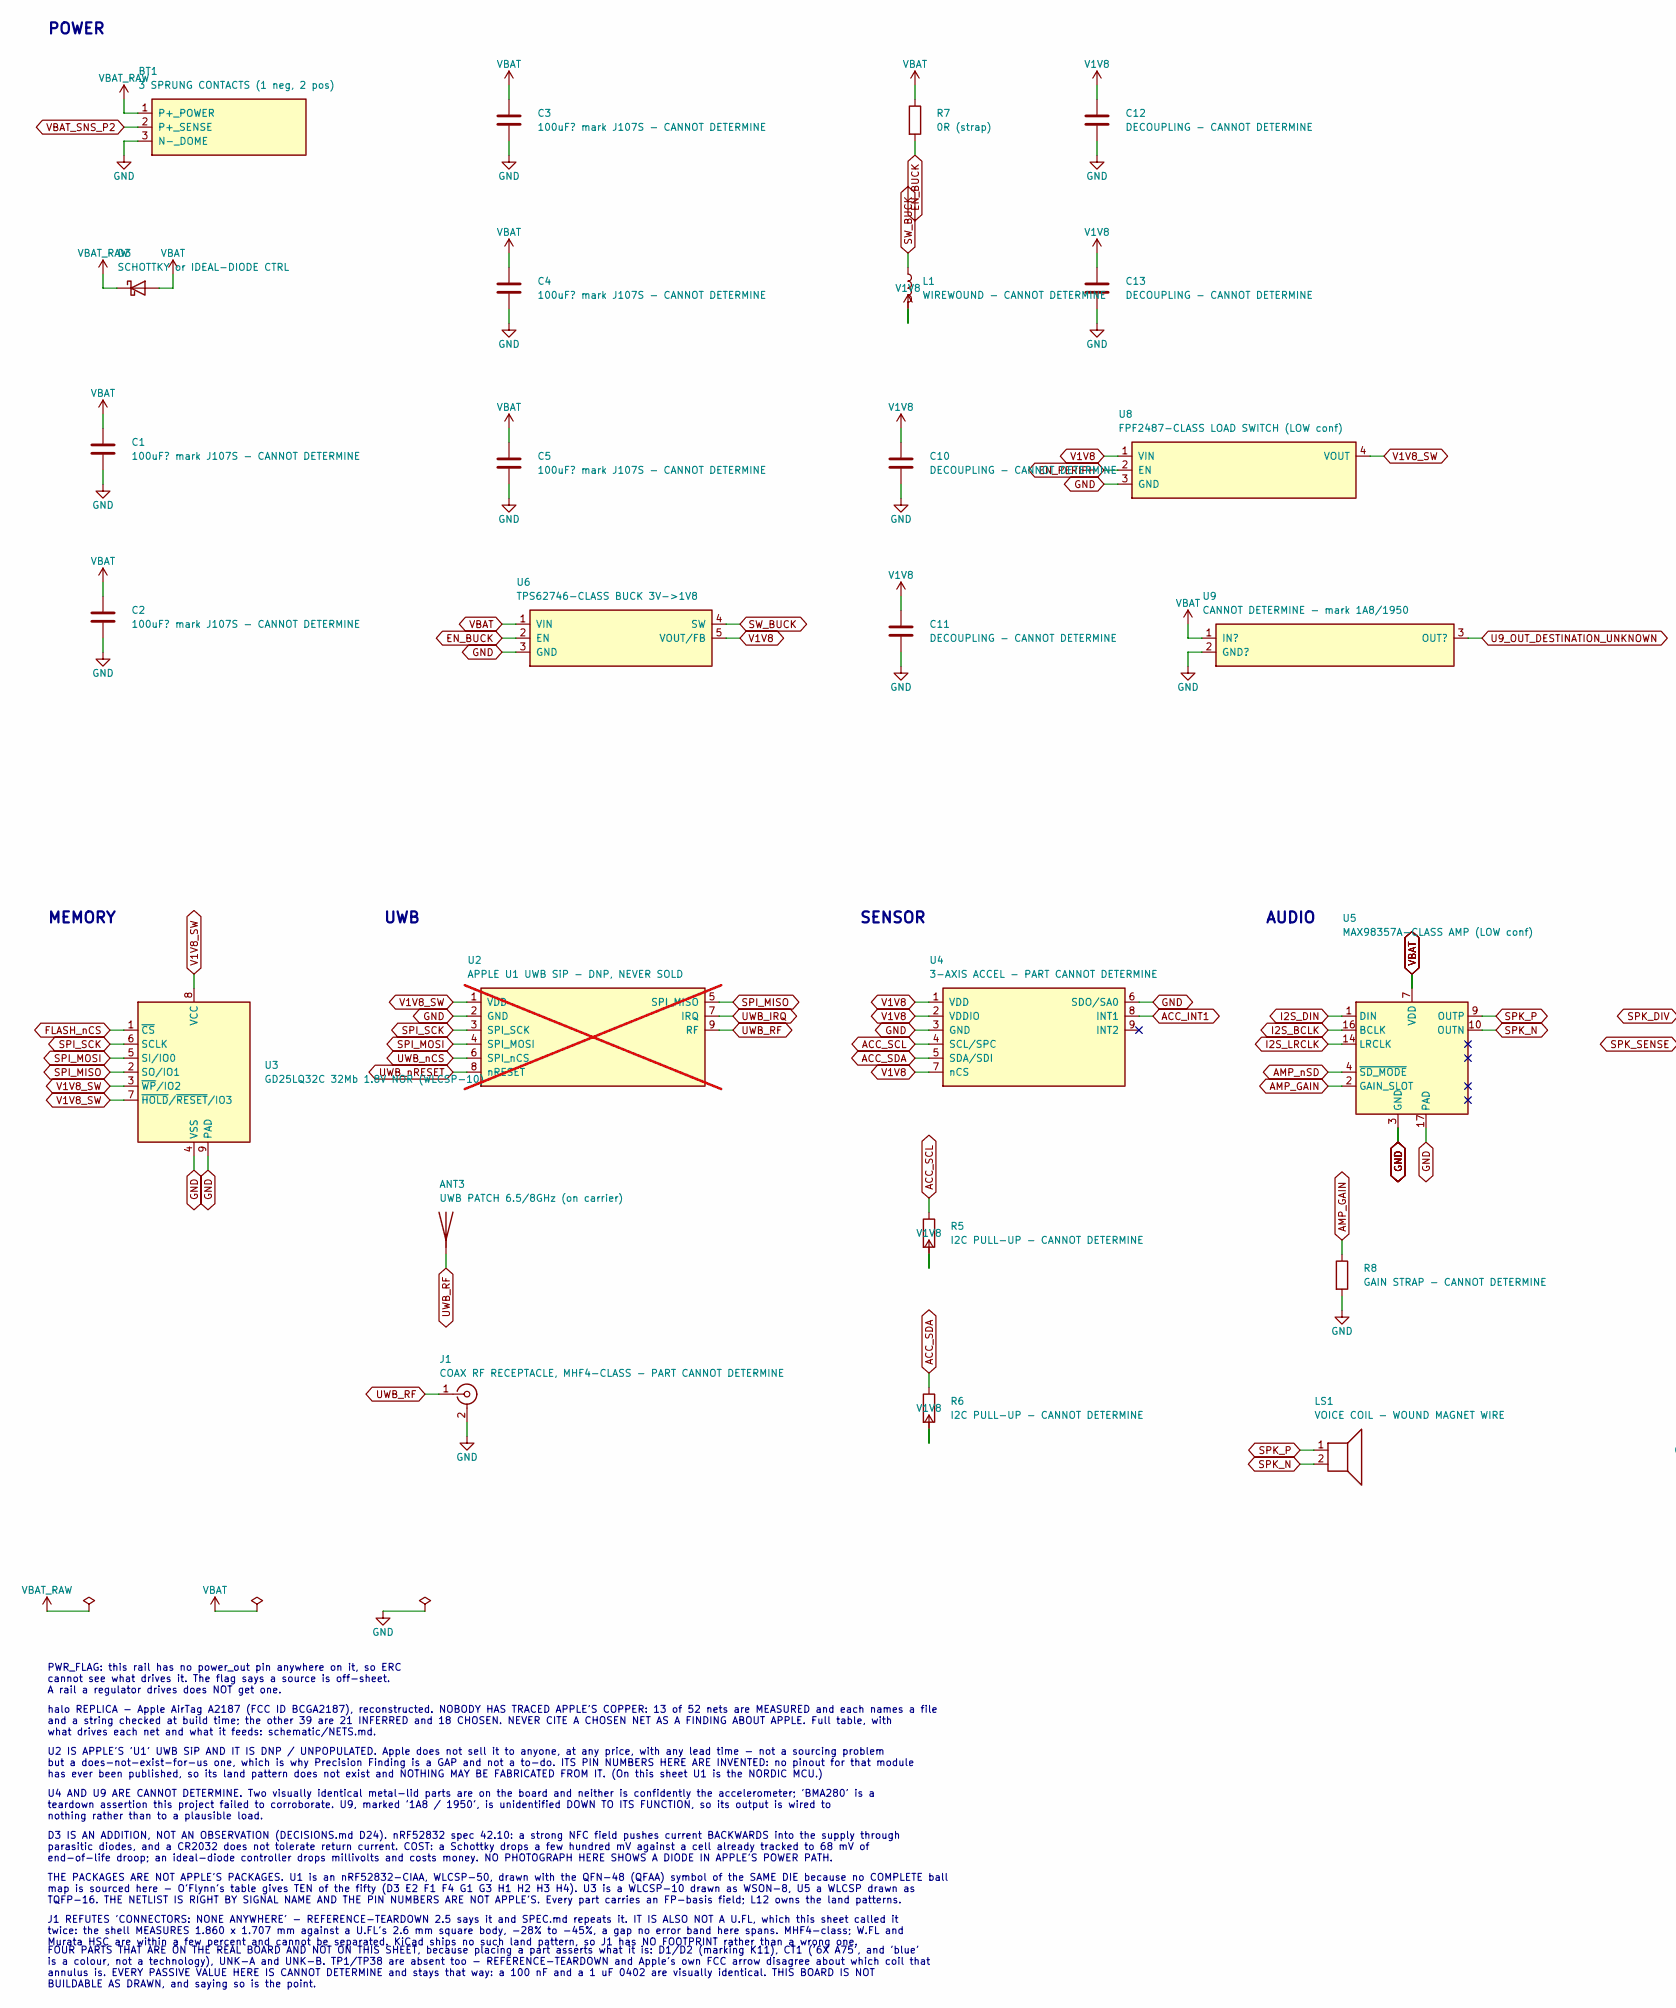
[picture p322: schematic halo_replica.kicad_sch, part in row 1, column 1]

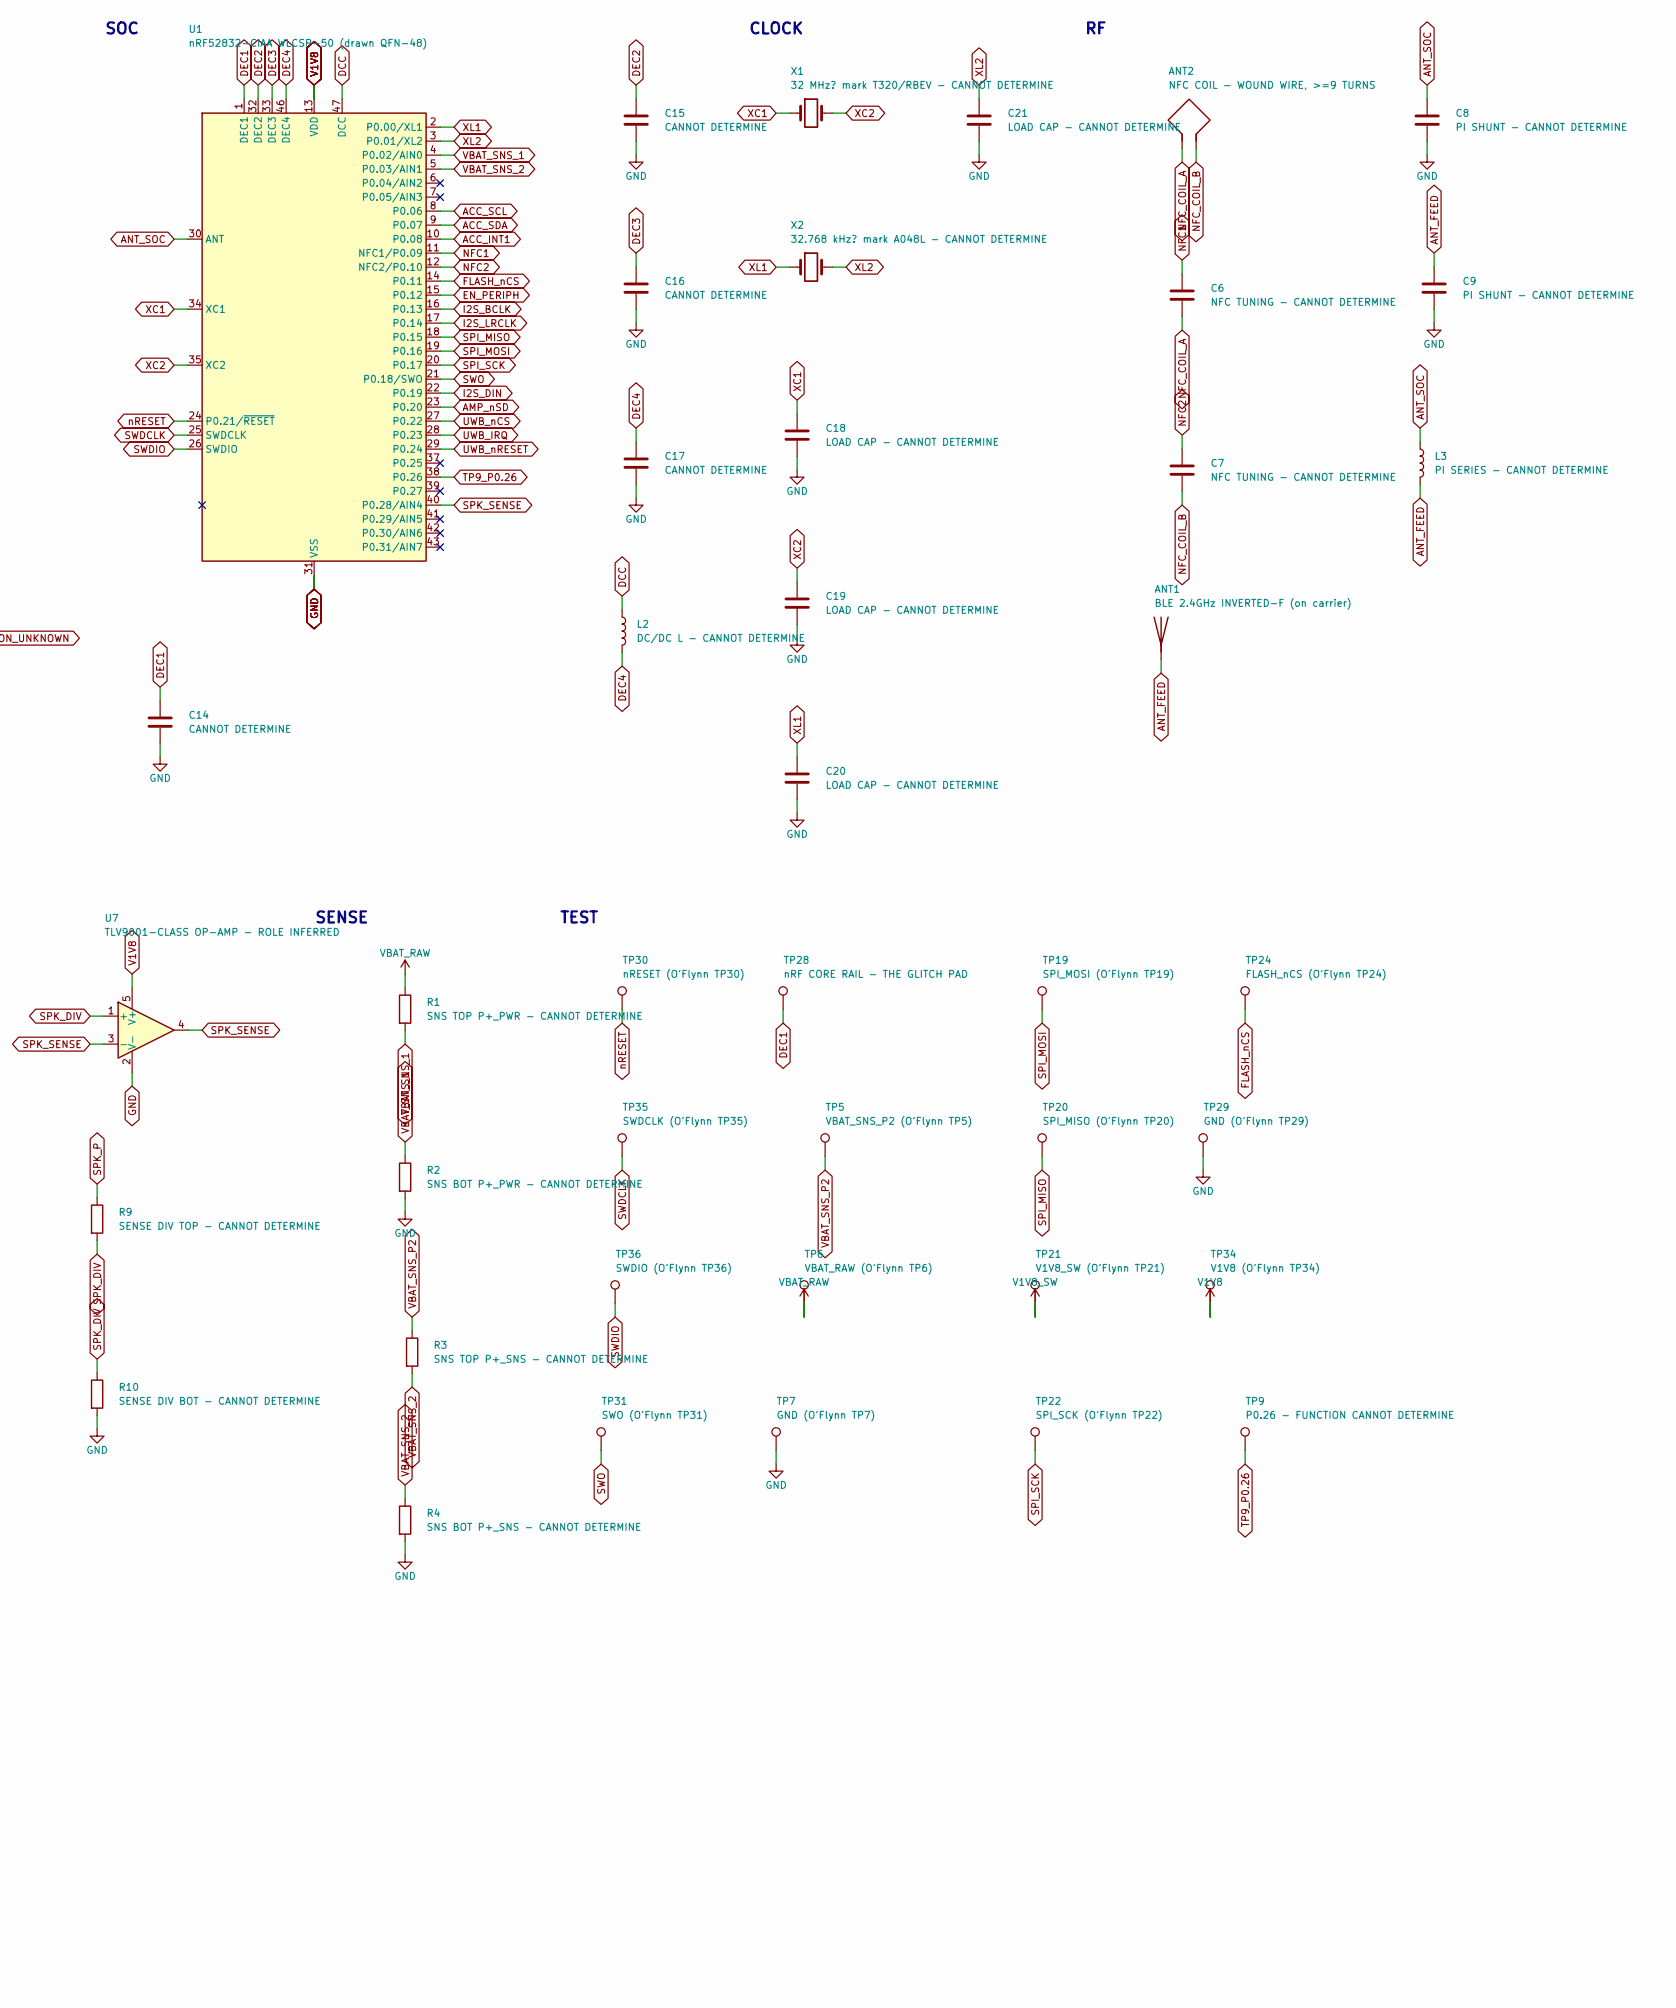
[picture p323: schematic halo_replica.kicad_sch, part in row 1, column 2]

Parts:
ANT1: BLE 2.4GHz INVERTED-F (on carrier)
ANT2: NFC COIL - WOUND WIRE, >=9 TURNS
ANT3: UWB PATCH 6.5/8GHz (on carrier)
BT1: 3 SPRUNG CONTACTS (1 neg, 2 pos)
C1, C2, C3, C4, C5: 100uF? mark J107S - CANNOT DETERMINE; C_0805_2012Metric
C6, C7: NFC TUNING - CANNOT DETERMINE; C_0201_0603Metric
C8, C9: PI SHUNT - CANNOT DETERMINE; C_0201_0603Metric
C10, C11, C12, C13: DECOUPLING - CANNOT DETERMINE; C_0402_1005Metric
C14, C15, C16, C17: CANNOT DETERMINE; C_0201_0603Metric
C18, C19, C20, C21: LOAD CAP - CANNOT DETERMINE; C_0201_0603Metric
D3: SCHOTTKY or IDEAL-DIODE CTRL; D_0402_1005Metric
J1: COAX RF RECEPTACLE, MHF4-CLASS - PART CANNOT DETE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
L1: WIREWOUND - CANNOT DETERMINE; L_0402_1005Metric
L2: DC/DC L - CANNOT DETERMINE; L_0402_1005Metric
L3: PI SERIES - CANNOT DETERMINE; L_0402_1005Metric
LS1: VOICE COIL - WOUND MAGNET WIRE
R1: SNS TOP P+_PWR - CANNOT DETERMINE; R_0402_1005Metric
R2: SNS BOT P+_PWR - CANNOT DETERMINE; R_0402_1005Metric
R3: SNS TOP P+_SNS - CANNOT DETERMINE; R_0402_1005Metric
R4: SNS BOT P+_SNS - CANNOT DETERMINE; R_0402_1005Metric
R5, R6: I2C PULL-UP - CANNOT DETERMINE; R_0402_1005Metric
R7: 0R (strap); R_0402_1005Metric
R8: GAIN STRAP - CANNOT DETERMINE; R_0402_1005Metric
R9: SENSE DIV TOP - CANNOT DETERMINE; R_0402_1005Metric
R10: SENSE DIV BOT - CANNOT DETERMINE; R_0402_1005Metric
TP5: VBAT_SNS_P2 (O'Flynn TP5); TestPoint_Pad_D1.0mm
TP6: VBAT_RAW (O'Flynn TP6); TestPoint_Pad_D1.0mm
TP7: GND (O'Flynn TP7); TestPoint_Pad_D1.0mm
TP9: P0.26 - FUNCTION CANNOT DETERMINE; TestPoint_Pad_D1.0mm
TP19: SPI_MOSI (O'Flynn TP19); TestPoint_Pad_D1.0mm
TP20: SPI_MISO (O'Flynn TP20); TestPoint_Pad_D1.0mm
TP21: V1V8_SW (O'Flynn TP21); TestPoint_Pad_D1.0mm
TP22: SPI_SCK (O'Flynn TP22); TestPoint_Pad_D1.0mm
TP24: FLASH_nCS (O'Flynn TP24); TestPoint_Pad_D1.0mm
TP28: nRF CORE RAIL - THE GLITCH PAD; TestPoint_Pad_D1.0mm
TP29: GND (O'Flynn TP29); TestPoint_Pad_D1.0mm
TP30: nRESET (O'Flynn TP30); TestPoint_Pad_D1.0mm
TP31: SWO (O'Flynn TP31); TestPoint_Pad_D1.0mm
TP34: V1V8 (O'Flynn TP34); TestPoint_Pad_D1.0mm
TP35: SWDCLK (O'Flynn TP35); TestPoint_Pad_D1.0mm
TP36: SWDIO (O'Flynn TP36); TestPoint_Pad_D1.0mm
U1: nRF52832-CIAA WLCSP-50 (drawn QFN-48); QFN-48-1EP_6x6mm_P0.4mm_EP4.4x4.4mm
U2: APPLE U1 UWB SiP - DNP, NEVER SOLD; not fitted
U3: GD25LQ32C 32Mb 1.8V NOR (WLCSP-10)
U4: 3-AXIS ACCEL - PART CANNOT DETERMINE
U5: MAX98357A-CLASS AMP (LOW conf); WLCSP-16_4x4_B2.17x2.32mm_P0.5mm
U6: TPS62746-CLASS BUCK 3V->1V8
U7: TLV9001-CLASS OP-AMP - ROLE INFERRED; SOT-353_SC-70-5
U8: FPF2487-CLASS LOAD SWITCH (LOW conf)
U9: CANNOT DETERMINE - mark 1A8/1950
X1: 32 MHz? mark T320/RBEV - CANNOT DETERMINE; Crystal_SMD_3215-2Pin_3.2x1.5mm
X2: 32.768 kHz? mark A048L - CANNOT DETERMINE; Crystal_SMD_3215-2Pin_3.2x1.5mm

Connections:
ACC_INT1: U1.10 (P0.08), U4.8 (INT1)
ACC_SCL: R5.1, U1.8 (P0.06), U4.4 (SCL/SPC)
ACC_SDA: R6.1, U1.9 (P0.07), U4.5 (SDA/SDI)
AMP_GAIN: R8.1, U5.2 (GAIN_SLOT)
AMP_nSD: U1.23 (P0.20), U5.4 (~SD_MODE)
ANT_FEED: ANT1.1, C9.1, L3.2
ANT_SOC: C8.1, L3.1, U1.30 (ANT)
DCC: L2.1, U1.47 (DCC)
DEC1: C14.1, TP28.1, U1.1 (DEC1)
DEC2: C15.1, U1.32 (DEC2)
DEC3: C16.1, U1.33 (DEC3)
DEC4: C17.1, L2.2, U1.46 (DEC4)
EN_BUCK: R7.2, U6.2 (EN)
EN_PERIPH: U1.15 (P0.12), U8.2 (EN)
FLASH_nCS: TP24.1, U1.14 (P0.11), U3.1 (~CS)
GND: BT1.1 (P+_POWER), BT1.3 (N-_DOME), C1.1, C1.2, C2.1, C2.2, C3.1, C3.2, C4.1, C4.2, C5.1, C5.2, C8.2, C9.2, C10.2, C11.2, C12.2, C13.2, C14.2, C15.2, C16.2, C17.2, C18.2, C19.2, C20.2, C21.2, D3.1 (K), D3.2 (A), J1.2 (Ext), R1.1, R2.2, R4.2, R7.1, R8.2, R10.2, TP6.1, TP7.1, TP29.1, U1.31 (VSS), U1.45 (VSS), U1.49 (VSS), U2.2 (GND), U3.4 (VSS), U3.9 (PAD), U4.3 (GND), U4.6 (SDO/SA0), U5.3 (GND), U5.11 (GND), U5.15 (GND), U5.17 (PAD), U6.3 (GND), U7.2 (V-), U8.3 (GND), U9.1 (IN?), U9.2 (GND?)
I2S_BCLK: U1.16 (P0.13), U5.16 (BCLK)
I2S_DIN: U1.22 (P0.19), U5.1 (DIN)
I2S_LRCLK: U1.17 (P0.14), U5.14 (LRCLK)
NFC1: C6.1, U1.11 (NFC1/P0.09)
NFC2: C7.1, U1.12 (NFC2/P0.10)
NFC_COIL_A: ANT2.1, C6.2
NFC_COIL_B: ANT2.2, C7.2
SPI_MISO: TP20.1, U1.18 (P0.15), U2.5 (SPI_MISO), U3.2 (SO/IO1)
SPI_MOSI: TP19.1, U1.19 (P0.16), U2.4 (SPI_MOSI), U3.5 (SI/IO0)
SPI_SCK: TP22.1, U1.20 (P0.17), U2.3 (SPI_SCK), U3.6 (SCLK)
SPK_DIV: R9.2, R10.1, U7.1 (+)
SPK_N: LS1.2, U5.10 (OUTN)
SPK_P: LS1.1, R9.1, U5.9 (OUTP)
SPK_SENSE: U1.40 (P0.28/AIN4), U7.3 (-), U7.4
SWDCLK: TP35.1, U1.25 (SWDCLK)
SWDIO: TP36.1, U1.26 (SWDIO)
SWO: TP31.1, U1.21 (P0.18/SWO)
SW_BUCK: L1.1, U6.4 (SW)
TP9_P0.26: TP9.1, U1.38 (P0.26)
U9_OUT_DESTINATION_UNKNOWN: U9.3 (OUT?)
UWB_IRQ: U1.28 (P0.23), U2.7 (IRQ)
UWB_RF: ANT3.1, J1.1 (In), U2.9 (RF)
UWB_nCS: U1.27 (P0.22), U2.6 (SPI_nCS)
UWB_nRESET: U1.29 (P0.24), U2.8 (nRESET)
V1V8: C10.1, C11.1, C12.1, C13.1, L1.2, R5.2, R6.2, TP34.1, U1.13 (VDD), U1.36 (VDD), U1.48 (VDD), U4.1 (VDD), U4.2 (VDDIO), U4.7 (nCS), U6.5 (VOUT/FB), U7.5 (V+), U8.1 (VIN)
V1V8_SW: TP21.1, U2.1 (VDD), U3.3 (~WP/IO2), U3.7 (~HOLD/~RESET/IO3), U3.8 (VCC), U8.4 (VOUT)
VBAT: U5.7 (VDD), U5.8 (VDD), U6.1 (VIN)
VBAT_SNS_1: R1.2, R2.1, U1.4 (P0.02/AIN0)
VBAT_SNS_2: R3.2, R4.1, U1.5 (P0.03/AIN1)
VBAT_SNS_P2: BT1.2 (P+_SENSE), R3.1, TP5.1
XC1: C18.1, U1.34 (XC1), X1.1
XC2: C19.1, U1.35 (XC2), X1.2
XL1: C20.1, U1.2 (P0.00/XL1), X2.1
XL2: C21.1, U1.3 (P0.01/XL2), X2.2
nRESET: TP30.1, U1.24 (P0.21/~RESET)

Notes on the sheet:
POWER
SOC
CLOCK
MEMORY
UWB
SENSOR
AUDIO
SENSE
TEST
PWR_FLAG: this rail has no power_out pin anywhere on it, so ERC cannot see what drives it. The flag says a source is off-sheet. A rail a regulator drives does NOT get one.
halo REPLICA - Apple AirTag A2187 (FCC ID BCGA2187), reconstructed. NOBODY HAS TRACED APPLE'S COPPER: 13 of 52 nets are MEASURED and each names a file and a string checked at build time; the other 39 are 21 INFERRED and 18 CHOSEN. NEVER CITE A CHOSEN NET AS A FINDING ABOUT APPLE. Full table, with w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
U2 IS APPLE'S 'U1' UWB SiP AND IT IS DNP / UNPOPULATED. Apple does not sell it to anyone, at any price, with any lead time - not a sourcing problem but a does-not-exist-for-us one, which is why Precision Finding is a GAP and not a to-do. ITS PIN NUMBERS HERE ARE INVENTED: no pinout for that module 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
U4 AND U9 ARE CANNOT DETERMINE. Two visually identical metal-lid parts are on the board and neither is confidently the accelerometer; 'BMA280' is a teardown assertion this project failed to corroborate. U9, marked '1A8 / 1950', is unidentified DOWN TO ITS FUNCTION, so its output is wired to nothing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
D3 IS AN ADDITION, NOT AN OBSERVATION (DECISIONS.md D24). nRF52832 spec 42.10: a strong NFC field pushes current BACKWARDS into the supply through parasitic diodes, and a CR2032 does not tolerate return current. COST: a Schottky drops a few hundred mV against a cell already tracked to 68 mV of end-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
THE PACKAGES ARE NOT APPLE'S PACKAGES. U1 is an nRF52832-CIAA, WLCSP-50, drawn with the QFN-48 (QFAA) symbol of the SAME DIE because no COMPLETE ball map is sourced here - O'Flynn's table gives TEN of the fifty (D3 E2 F1 F4 G1 G3 H1 H2 H3 H4). U3 is a WLCSP-10 drawn as WSON-8, U5 a WLCSP drawn as T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
J1 REFUTES 'CONNECTORS: NONE ANYWHERE' - REFERENCE-TEARDOWN 2.5 says it and SPEC.md repeats it. IT IS ALSO NOT A U.FL, which this sheet called it twice: the shell MEASURES 1.860 x 1.707 mm against a U.FL's 2.6 mm square body, -28% to -45%, a gap no error band here spans. MHF4-class; W.FL and Murata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
FOUR PARTS THAT ARE ON THE REAL BOARD AND NOT ON THIS SHEET, because placing a part asserts what it is: D1/D2 (marking K11), CT1 ('6X A75', and 'blue' is a colour, not a technology), UNK-A and UNK-B. TP1/TP38 are absent too - REFERENCE-TEARDOWN and Apple's own FCC arrow disagree about which coil th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
