Leif-Rydenfalk/halo/reference/nordic-lib-kicad/blocks/nRF54L.kicad_blocks/nRF54L15-QFXX_Reference_Design.kicad_block/nRF54L15-QFXX_Reference_Design.kicad_sch

## KiCad design reference/nordic-lib-kicad/blocks/nRF54L.kicad_blocks/nRF54L15-QFXX_Reference_Design.kicad_block/nRF54L15-QFXX_Reference_Design.kicad_sch (2026-09-03)

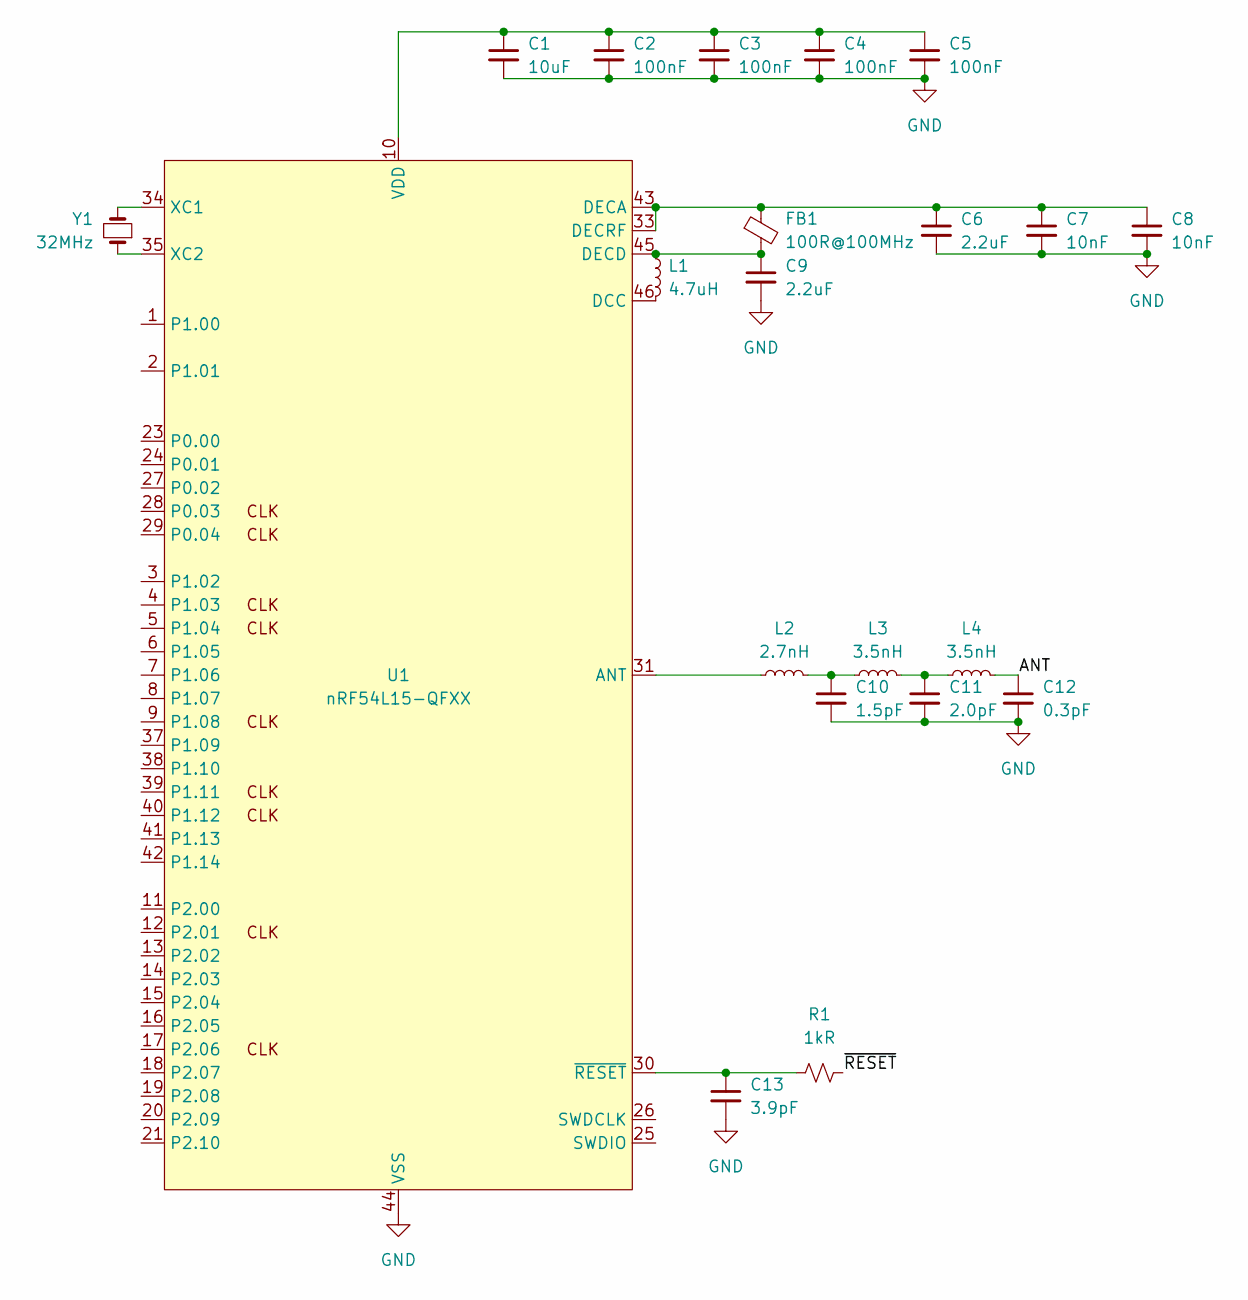
[picture p326: schematic nRF54L15-QFXX_Reference_Design.kicad_sch]

Parts:
C1: 10uF
C2, C3, C4, C5: 100nF
C6, C9: 2.2uF
C7, C8: 10nF
C10: 1.5pF
C11: 2.0pF
C12: 0.3pF
C13: 3.9pF
FB1: 100R@100MHz
L1: 4.7uH
L2: 2.7nH
L3, L4: 3.5nH
R1: 1kR
U1: nRF54L15-QFXX; QFN-48-1EP_6x6mm_P0.4mm_EP4.6x4.6mm
Y1: 32MHz

Connections:
ANT: C12.1, L4.2
GND: C1.2, C2.2, C3.2, C4.2, C5.2, C6.2, C7.2, C8.2, C9.2, C10.2, C11.2, C12.2, C13.2, U1.32 (VSS_PA), U1.44 (VSS), U1.49 (VSS)
unnamed: C1.1, C2.1, C3.1, C4.1, C5.1, U1.10 (VDD), U1.22 (VDD), U1.36 (VDD), U1.47 (VDD), U1.48 (VDD)
unnamed: C6.1, C7.1, C8.1, FB1.1, U1.33 (DECRF), U1.43 (DECA)
unnamed: C9.1, FB1.2, L1.1, U1.45 (DECD)
unnamed: C10.1, L2.2, L3.1
unnamed: C11.1, L3.2, L4.1
unnamed: C13.1, R1.1, U1.30 (~RESET)
unnamed: L1.2, U1.46 (DCC)
unnamed: L2.1, U1.31 (ANT)
unnamed: U1.34 (XC1), Y1.2
unnamed: U1.35 (XC2), Y1.1
~RESET: R1.2
